kangyuzhe666/ZYNQ7010-7020_AD9363/images/a82.PNG

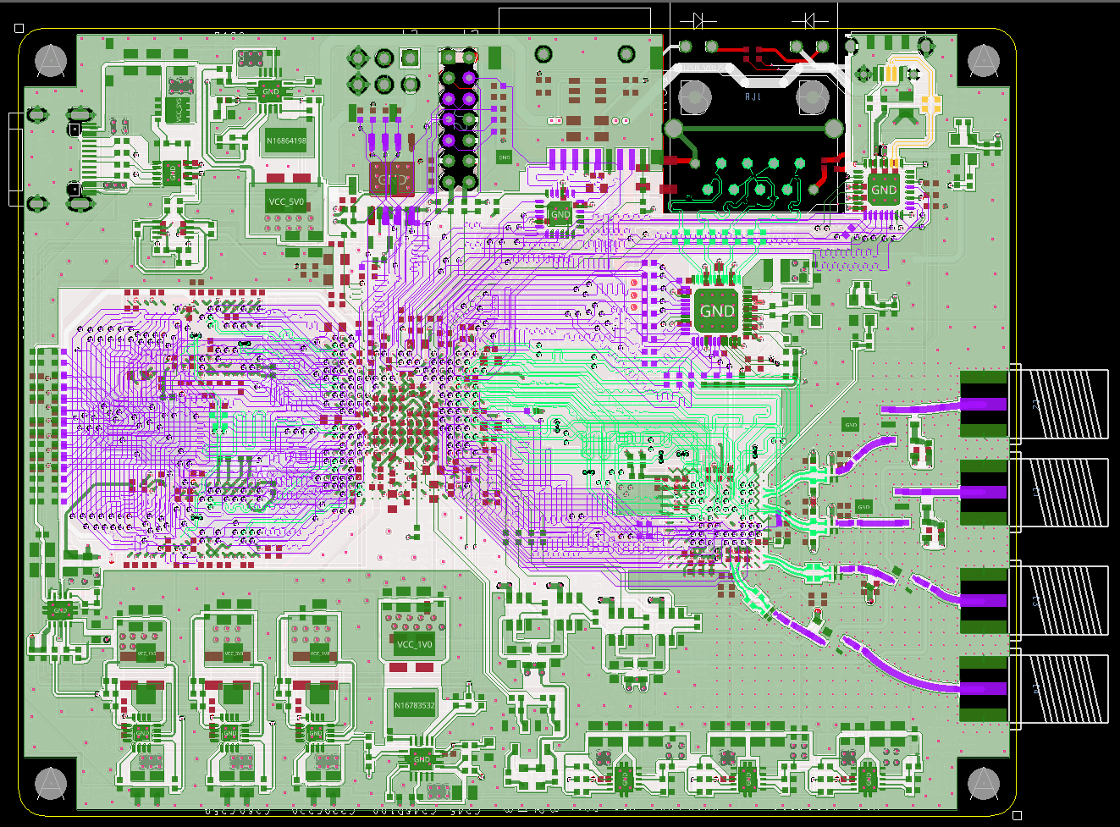
images/a82.PNG
