kangyuzhe666/ZYNQ7010-7020_AD9363/images/a83.PNG

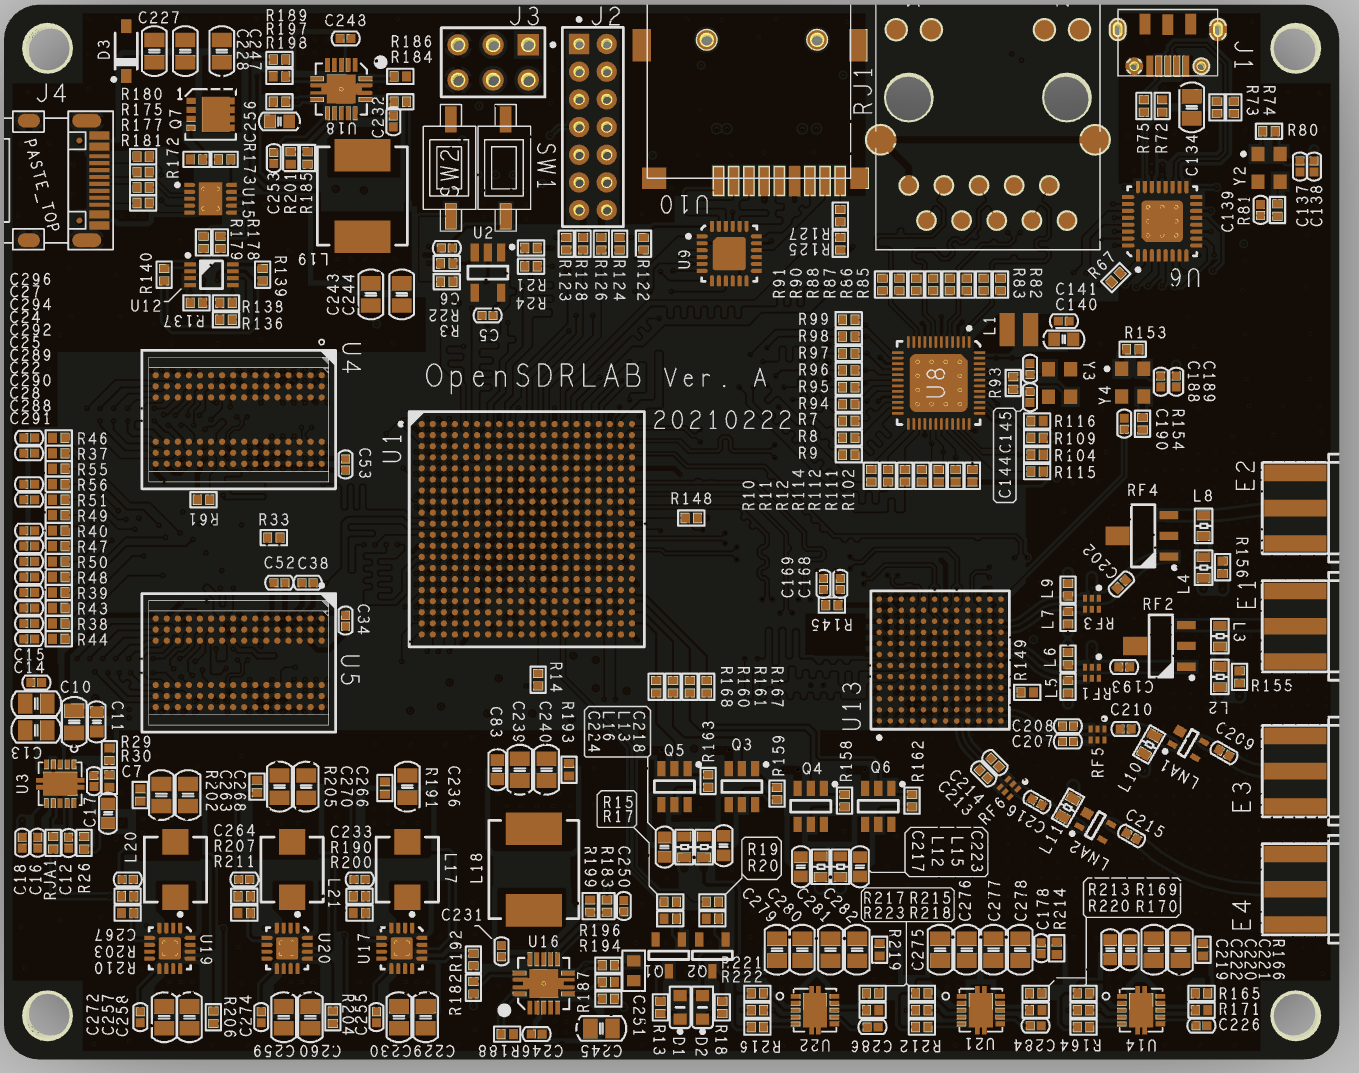
images/a83.PNG
