kangyuzhe666/ZYNQ7010-7020_AD9363/images/cpf.JPG

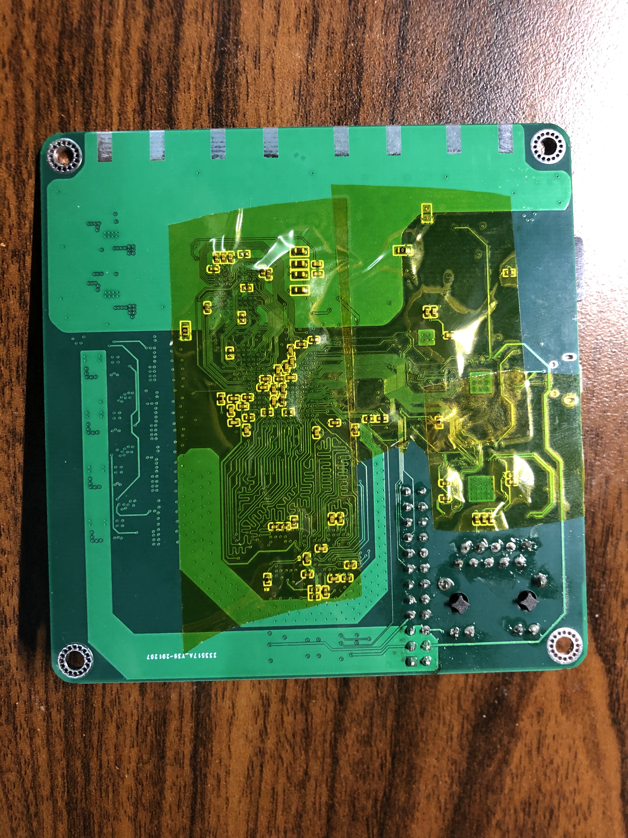
images/cpf.JPG
