kangyuzhe666/ZYNQ7010-7020_AD9363/images/cpz.JPG

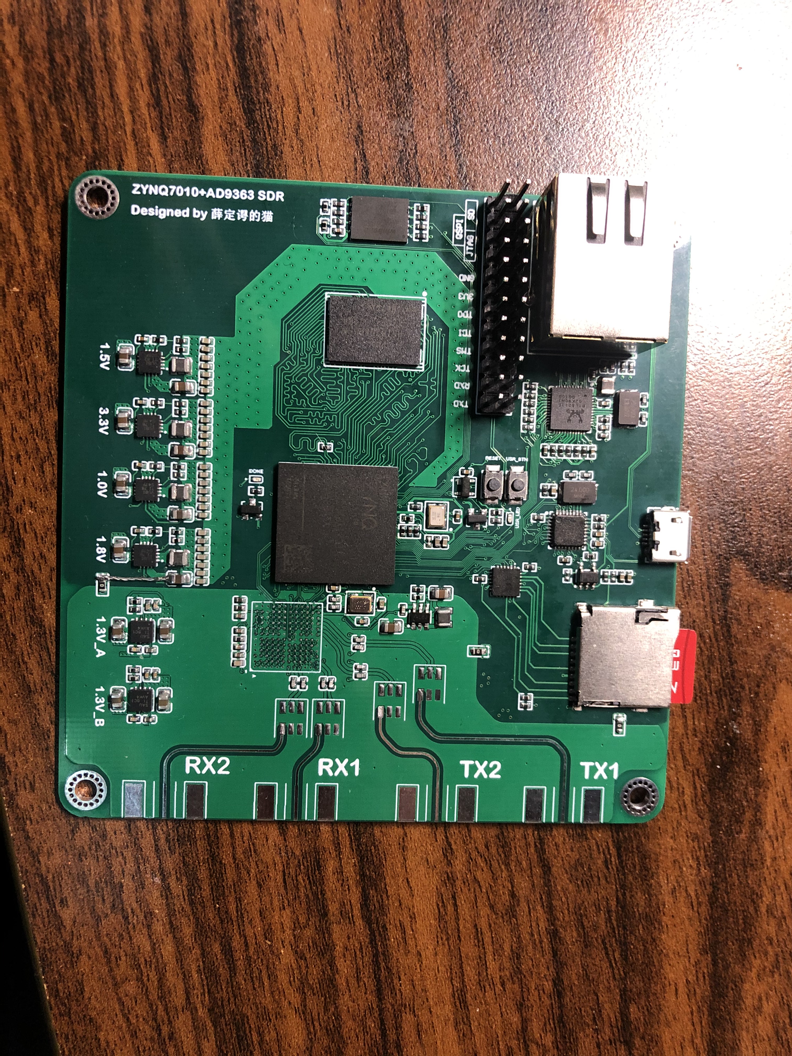
images/cpz.JPG
