kangyuzhe666/ZYNQ7010-7020_AD9363/images/IMG_2752.JPG

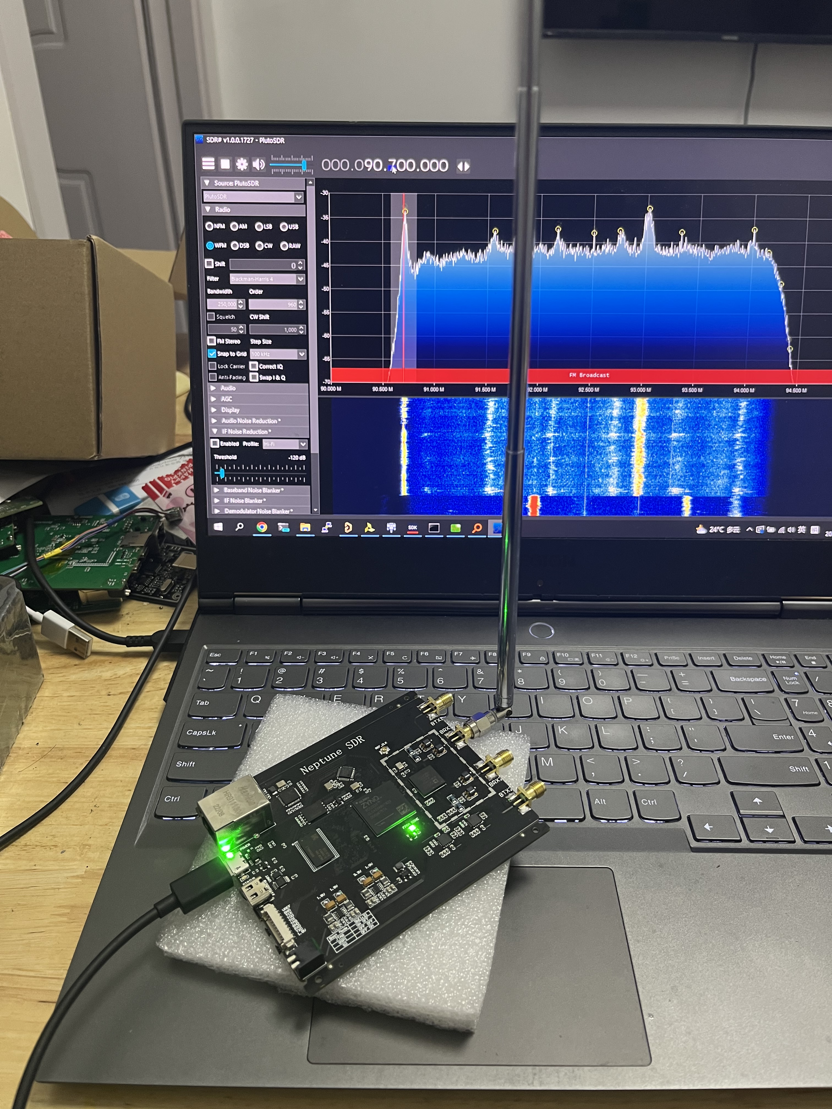
images/IMG_2752.JPG
