kangyuzhe666/ZYNQ7010-7020_AD9363/images/IMG_2765.JPG

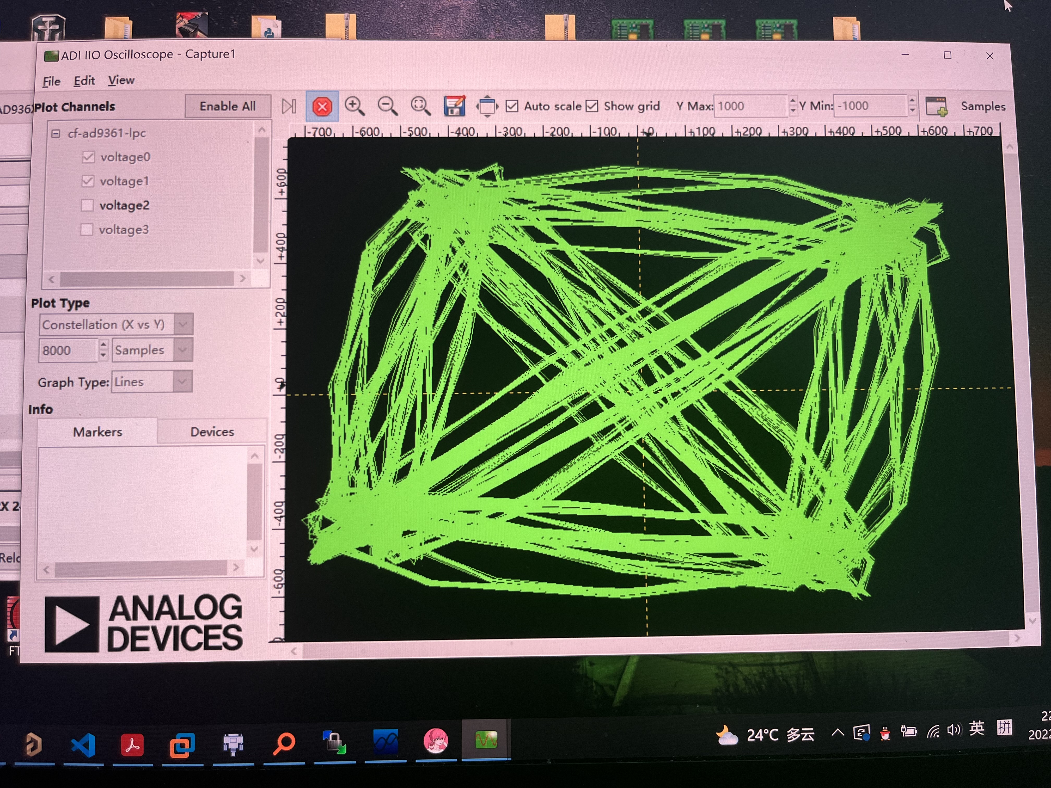
images/IMG_2765.JPG
