kangyuzhe666/ZYNQ7010-7020_AD9363/images/IMG_7890.PNG

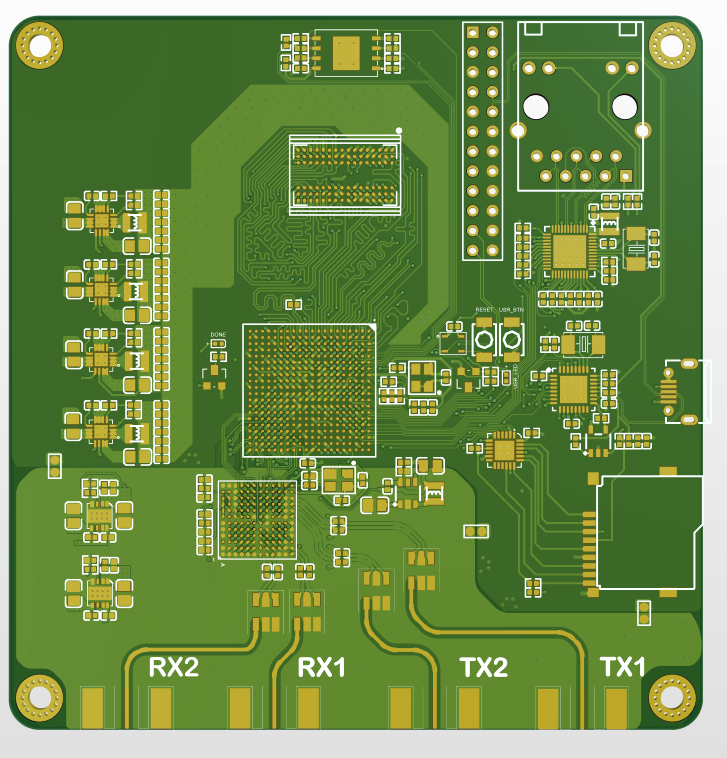
images/IMG_7890.PNG
