kangyuzhe666/ZYNQ7010-7020_AD9363/images/top.png

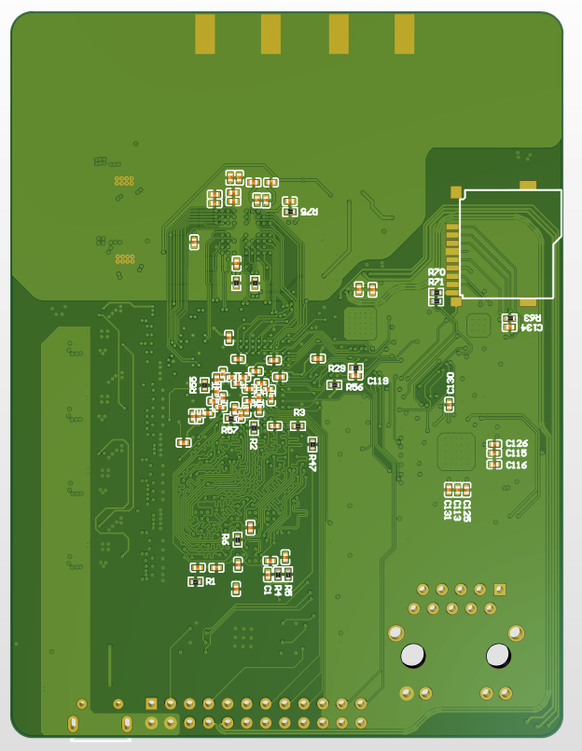
images/top.png
