kangyuzhe666/ZYNQ7010-7020_AD9363/firmware/source project/pluto-7010clg400-user-ip/pluto/pluto.runs/synth_1/.Xil/system_top_propImpl.xdc

set_property SRC_FILE_INFO {cfile:/home/kyz/hdl-2019_r1/projects/pluto/system_constr.xdc rfile:../../../system_constr.xdc id:1} [current_design]
set_property SRC_FILE_INFO {cfile:/home/kyz/hdl-2019_r1/projects/pluto/pluto.srcs/sources_1/bd/system/ip/system_axi_ad9361_dac_dma_0/system_axi_ad9361_dac_dma_0_constr.xdc rfile:../../../pluto.srcs/sources_1/bd/system/ip/system_axi_ad9361_dac_dma_0/system_axi_ad9361_dac_dma_0_constr.xdc id:2 order:LATE scoped_inst:i_system_wrapper/system_i/axi_ad9361_dac_dma/inst} [current_design]
set_property SRC_FILE_INFO {cfile:/home/kyz/hdl-2019_r1/projects/pluto/pluto.srcs/sources_1/bd/system/ip/system_axi_ad9361_adc_dma_0/system_axi_ad9361_adc_dma_0_constr.xdc rfile:../../../pluto.srcs/sources_1/bd/system/ip/system_axi_ad9361_adc_dma_0/system_axi_ad9361_adc_dma_0_constr.xdc id:3 order:LATE scoped_inst:i_system_wrapper/system_i/axi_ad9361_adc_dma/inst} [current_design]
set_property src_info {type:XDC file:1 line:4 export:INPUT save:INPUT read:READ} [current_design]
set_property  -dict {PACKAGE_PIN  U18  IOSTANDARD LVCMOS18 } [get_ports rx_clk_in]
set_property src_info {type:XDC file:1 line:5 export:INPUT save:INPUT read:READ} [current_design]
set_property  -dict {PACKAGE_PIN  U13  IOSTANDARD LVCMOS18 } [get_ports rx_frame_in]
set_property src_info {type:XDC file:1 line:6 export:INPUT save:INPUT read:READ} [current_design]
set_property  -dict {PACKAGE_PIN  P20  IOSTANDARD LVCMOS18 } [get_ports rx_data_in[0]]
set_property src_info {type:XDC file:1 line:7 export:INPUT save:INPUT read:READ} [current_design]
set_property  -dict {PACKAGE_PIN  N20  IOSTANDARD LVCMOS18 } [get_ports rx_data_in[1]]
set_property src_info {type:XDC file:1 line:8 export:INPUT save:INPUT read:READ} [current_design]
set_property  -dict {PACKAGE_PIN  W20  IOSTANDARD LVCMOS18 } [get_ports rx_data_in[2]]
set_property src_info {type:XDC file:1 line:9 export:INPUT save:INPUT read:READ} [current_design]
set_property  -dict {PACKAGE_PIN  V20  IOSTANDARD LVCMOS18 } [get_ports rx_data_in[3]]
set_property src_info {type:XDC file:1 line:10 export:INPUT save:INPUT read:READ} [current_design]
set_property  -dict {PACKAGE_PIN  U20  IOSTANDARD LVCMOS18 } [get_ports rx_data_in[4]]
set_property src_info {type:XDC file:1 line:11 export:INPUT save:INPUT read:READ} [current_design]
set_property  -dict {PACKAGE_PIN  T20  IOSTANDARD LVCMOS18 } [get_ports rx_data_in[5]]
set_property src_info {type:XDC file:1 line:12 export:INPUT save:INPUT read:READ} [current_design]
set_property  -dict {PACKAGE_PIN  R18  IOSTANDARD LVCMOS18 } [get_ports rx_data_in[6]]
set_property src_info {type:XDC file:1 line:13 export:INPUT save:INPUT read:READ} [current_design]
set_property  -dict {PACKAGE_PIN  T17  IOSTANDARD LVCMOS18 } [get_ports rx_data_in[7]]
set_property src_info {type:XDC file:1 line:14 export:INPUT save:INPUT read:READ} [current_design]
set_property  -dict {PACKAGE_PIN  P19  IOSTANDARD LVCMOS18 } [get_ports rx_data_in[8]]
set_property src_info {type:XDC file:1 line:15 export:INPUT save:INPUT read:READ} [current_design]
set_property  -dict {PACKAGE_PIN  N18  IOSTANDARD LVCMOS18 } [get_ports rx_data_in[9]]
set_property src_info {type:XDC file:1 line:16 export:INPUT save:INPUT read:READ} [current_design]
set_property  -dict {PACKAGE_PIN  R17  IOSTANDARD LVCMOS18 } [get_ports rx_data_in[10]]
set_property src_info {type:XDC file:1 line:17 export:INPUT save:INPUT read:READ} [current_design]
set_property  -dict {PACKAGE_PIN  R16  IOSTANDARD LVCMOS18 } [get_ports rx_data_in[11]]
set_property src_info {type:XDC file:1 line:19 export:INPUT save:INPUT read:READ} [current_design]
set_property  -dict {PACKAGE_PIN  T16  IOSTANDARD LVCMOS18} [get_ports tx_clk_out]
set_property src_info {type:XDC file:1 line:20 export:INPUT save:INPUT read:READ} [current_design]
set_property  -dict {PACKAGE_PIN  V16  IOSTANDARD LVCMOS18} [get_ports tx_frame_out]
set_property src_info {type:XDC file:1 line:21 export:INPUT save:INPUT read:READ} [current_design]
set_property  -dict {PACKAGE_PIN  W14  IOSTANDARD LVCMOS18} [get_ports tx_data_out[0]]
set_property src_info {type:XDC file:1 line:22 export:INPUT save:INPUT read:READ} [current_design]
set_property  -dict {PACKAGE_PIN  Y14  IOSTANDARD LVCMOS18} [get_ports tx_data_out[1]]
set_property src_info {type:XDC file:1 line:23 export:INPUT save:INPUT read:READ} [current_design]
set_property  -dict {PACKAGE_PIN  V12  IOSTANDARD LVCMOS18} [get_ports tx_data_out[2]]
set_property src_info {type:XDC file:1 line:24 export:INPUT save:INPUT read:READ} [current_design]
set_property  -dict {PACKAGE_PIN  W13  IOSTANDARD LVCMOS18} [get_ports tx_data_out[3]]
set_property src_info {type:XDC file:1 line:25 export:INPUT save:INPUT read:READ} [current_design]
set_property  -dict {PACKAGE_PIN  Y18  IOSTANDARD LVCMOS18} [get_ports tx_data_out[4]]
set_property src_info {type:XDC file:1 line:26 export:INPUT save:INPUT read:READ} [current_design]
set_property  -dict {PACKAGE_PIN  Y19  IOSTANDARD LVCMOS18} [get_ports tx_data_out[5]]
set_property src_info {type:XDC file:1 line:27 export:INPUT save:INPUT read:READ} [current_design]
set_property  -dict {PACKAGE_PIN  T12  IOSTANDARD LVCMOS18} [get_ports tx_data_out[6]]
set_property src_info {type:XDC file:1 line:28 export:INPUT save:INPUT read:READ} [current_design]
set_property  -dict {PACKAGE_PIN  U12  IOSTANDARD LVCMOS18} [get_ports tx_data_out[7]]
set_property src_info {type:XDC file:1 line:29 export:INPUT save:INPUT read:READ} [current_design]
set_property  -dict {PACKAGE_PIN  Y16  IOSTANDARD LVCMOS18} [get_ports tx_data_out[8]]
set_property src_info {type:XDC file:1 line:30 export:INPUT save:INPUT read:READ} [current_design]
set_property  -dict {PACKAGE_PIN  Y17  IOSTANDARD LVCMOS18} [get_ports tx_data_out[9]]
set_property src_info {type:XDC file:1 line:31 export:INPUT save:INPUT read:READ} [current_design]
set_property  -dict {PACKAGE_PIN  T11  IOSTANDARD LVCMOS18} [get_ports tx_data_out[10]]
set_property src_info {type:XDC file:1 line:32 export:INPUT save:INPUT read:READ} [current_design]
set_property  -dict {PACKAGE_PIN  T10  IOSTANDARD LVCMOS18} [get_ports tx_data_out[11]]
set_property src_info {type:XDC file:1 line:34 export:INPUT save:INPUT read:READ} [current_design]
set_property  -dict {PACKAGE_PIN  V17  IOSTANDARD LVCMOS18} [get_ports gpio_status[0]]
set_property src_info {type:XDC file:1 line:35 export:INPUT save:INPUT read:READ} [current_design]
set_property  -dict {PACKAGE_PIN  T14  IOSTANDARD LVCMOS18} [get_ports gpio_status[1]]
set_property src_info {type:XDC file:1 line:36 export:INPUT save:INPUT read:READ} [current_design]
set_property  -dict {PACKAGE_PIN  T15  IOSTANDARD LVCMOS18} [get_ports gpio_status[2]]
set_property src_info {type:XDC file:1 line:37 export:INPUT save:INPUT read:READ} [current_design]
set_property  -dict {PACKAGE_PIN  P14  IOSTANDARD LVCMOS18} [get_ports gpio_status[3]]
set_property src_info {type:XDC file:1 line:38 export:INPUT save:INPUT read:READ} [current_design]
set_property  -dict {PACKAGE_PIN  U14  IOSTANDARD LVCMOS18} [get_ports gpio_status[4]]
set_property src_info {type:XDC file:1 line:39 export:INPUT save:INPUT read:READ} [current_design]
set_property  -dict {PACKAGE_PIN  U15  IOSTANDARD LVCMOS18} [get_ports gpio_status[5]]
set_property src_info {type:XDC file:1 line:40 export:INPUT save:INPUT read:READ} [current_design]
set_property  -dict {PACKAGE_PIN  T19  IOSTANDARD LVCMOS18} [get_ports gpio_status[6]]
set_property src_info {type:XDC file:1 line:41 export:INPUT save:INPUT read:READ} [current_design]
set_property  -dict {PACKAGE_PIN  V18  IOSTANDARD LVCMOS18} [get_ports gpio_status[7]]
set_property src_info {type:XDC file:1 line:43 export:INPUT save:INPUT read:READ} [current_design]
set_property  -dict {PACKAGE_PIN  G20  IOSTANDARD LVCMOS18} [get_ports gpio_ctl[0]]
set_property src_info {type:XDC file:1 line:44 export:INPUT save:INPUT read:READ} [current_design]
set_property  -dict {PACKAGE_PIN  D20  IOSTANDARD LVCMOS18} [get_ports gpio_ctl[1]]
set_property src_info {type:XDC file:1 line:45 export:INPUT save:INPUT read:READ} [current_design]
set_property  -dict {PACKAGE_PIN  F20  IOSTANDARD LVCMOS18} [get_ports gpio_ctl[2]]
set_property src_info {type:XDC file:1 line:46 export:INPUT save:INPUT read:READ} [current_design]
set_property  -dict {PACKAGE_PIN  H20  IOSTANDARD LVCMOS18} [get_ports gpio_ctl[3]]
set_property src_info {type:XDC file:1 line:48 export:INPUT save:INPUT read:READ} [current_design]
set_property  -dict {PACKAGE_PIN  W19  IOSTANDARD LVCMOS18} [get_ports gpio_en_agc]
set_property src_info {type:XDC file:1 line:49 export:INPUT save:INPUT read:READ} [current_design]
set_property  -dict {PACKAGE_PIN  R19  IOSTANDARD LVCMOS18} [get_ports gpio_resetb]
set_property src_info {type:XDC file:1 line:51 export:INPUT save:INPUT read:READ} [current_design]
set_property  -dict {PACKAGE_PIN  V15  IOSTANDARD LVCMOS18} [get_ports enable]
set_property src_info {type:XDC file:1 line:52 export:INPUT save:INPUT read:READ} [current_design]
set_property  -dict {PACKAGE_PIN  R14  IOSTANDARD LVCMOS18} [get_ports txnrx]
set_property src_info {type:XDC file:1 line:54 export:INPUT save:INPUT read:READ} [current_design]
set_property  -dict {PACKAGE_PIN  J16  IOSTANDARD LVCMOS18 PULLTYPE PULLUP} [get_ports iic_scl]
set_property src_info {type:XDC file:1 line:55 export:INPUT save:INPUT read:READ} [current_design]
set_property  -dict {PACKAGE_PIN  K16  IOSTANDARD LVCMOS18 PULLTYPE PULLUP} [get_ports iic_sda]
set_property src_info {type:XDC file:1 line:57 export:INPUT save:INPUT read:READ} [current_design]
set_property  -dict {PACKAGE_PIN  N17  IOSTANDARD LVCMOS18  PULLTYPE PULLUP} [get_ports spi_csn]
set_property src_info {type:XDC file:1 line:58 export:INPUT save:INPUT read:READ} [current_design]
set_property  -dict {PACKAGE_PIN  P18  IOSTANDARD LVCMOS18} [get_ports spi_clk]
set_property src_info {type:XDC file:1 line:59 export:INPUT save:INPUT read:READ} [current_design]
set_property  -dict {PACKAGE_PIN  P15  IOSTANDARD LVCMOS18} [get_ports spi_mosi]
set_property src_info {type:XDC file:1 line:60 export:INPUT save:INPUT read:READ} [current_design]
set_property  -dict {PACKAGE_PIN  P16  IOSTANDARD LVCMOS18} [get_ports spi_miso]
set_property src_info {type:XDC file:1 line:62 export:INPUT save:INPUT read:READ} [current_design]
set_property  -dict {PACKAGE_PIN  L15  IOSTANDARD LVCMOS18} [get_ports gpio_bd]
set_property src_info {type:XDC file:1 line:63 export:INPUT save:INPUT read:READ} [current_design]
set_property  -dict {PACKAGE_PIN  W18  IOSTANDARD LVCMOS18} [get_ports clk_out]
set_property src_info {type:XDC file:1 line:74 export:INPUT save:INPUT read:READ} [current_design]
set_input_jitter clk_fpga_0 0.3
set_property src_info {type:XDC file:1 line:75 export:INPUT save:INPUT read:READ} [current_design]
set_input_jitter clk_fpga_1 0.15
current_instance i_system_wrapper/system_i/axi_ad9361_dac_dma/inst
set_property src_info {type:SCOPED_XDC file:2 line:10 export:INPUT save:INPUT read:READ} [current_design]
set_max_delay -quiet -datapath_only -from [get_clocks -of_objects [get_pins [list i_system_wrapper/system_i/axi_ad9361_dac_dma/inst/fifo_rd_clk i_system_wrapper/system_i/axi_ad9361_dac_dma/inst/m_axis_aclk i_system_wrapper/system_i/axi_ad9361_dac_dma/inst/m_dest_axi_aclk]]] -to [get_cells -hier *cdc_sync_stage1_reg* -filter {NAME =~ *i_sync_req_response_id* && IS_SEQUENTIAL}] [get_property -min PERIOD [get_clocks -of_objects [get_pins [list i_system_wrapper/system_i/axi_ad9361_dac_dma/inst/fifo_rd_clk i_system_wrapper/system_i/axi_ad9361_dac_dma/inst/m_axis_aclk i_system_wrapper/system_i/axi_ad9361_dac_dma/inst/m_dest_axi_aclk]]]]
set_property src_info {type:SCOPED_XDC file:2 line:26 export:INPUT save:INPUT read:READ} [current_design]
set_max_delay -quiet -datapath_only -from [get_clocks -of_objects [get_pins [list i_system_wrapper/system_i/axi_ad9361_dac_dma/inst/fifo_rd_clk i_system_wrapper/system_i/axi_ad9361_dac_dma/inst/m_axis_aclk i_system_wrapper/system_i/axi_ad9361_dac_dma/inst/m_dest_axi_aclk]]] -to [get_cells -quiet -hier *cdc_sync_stage1_reg* -filter {NAME =~ *i_dest_response_fifo/i_waddr_sync* && IS_SEQUENTIAL}] [get_property -min PERIOD [get_clocks -of_objects [get_pins [list i_system_wrapper/system_i/axi_ad9361_dac_dma/inst/fifo_rd_clk i_system_wrapper/system_i/axi_ad9361_dac_dma/inst/m_axis_aclk i_system_wrapper/system_i/axi_ad9361_dac_dma/inst/m_dest_axi_aclk]]]]
set_property src_info {type:SCOPED_XDC file:2 line:32 export:INPUT save:INPUT read:READ} [current_design]
set_max_delay -quiet -datapath_only -from [get_clocks -of_objects [get_pins i_system_wrapper/system_i/axi_ad9361_dac_dma/inst/s_axi_aclk]] -to [get_cells -quiet -hier *cdc_sync_stage1_reg* -filter {NAME =~ *i_dest_response_fifo/i_raddr_sync* && IS_SEQUENTIAL}] [get_property -min PERIOD [get_clocks -of_objects [get_pins i_system_wrapper/system_i/axi_ad9361_dac_dma/inst/s_axi_aclk]]]
set_property src_info {type:SCOPED_XDC file:2 line:37 export:INPUT save:INPUT read:READ} [current_design]
set_max_delay -quiet -datapath_only -from [get_cells -quiet -hier *cdc_sync_fifo_ram_reg* -filter {NAME =~ *i_dest_response_fifo* && IS_SEQUENTIAL}] -to [get_clocks -of_objects [get_pins i_system_wrapper/system_i/axi_ad9361_dac_dma/inst/s_axi_aclk]] [get_property -min PERIOD [get_clocks -of_objects [get_pins i_system_wrapper/system_i/axi_ad9361_dac_dma/inst/s_axi_aclk]]]
set_property src_info {type:SCOPED_XDC file:2 line:43 export:INPUT save:INPUT read:READ} [current_design]
set_max_delay -quiet -datapath_only -from [get_clocks -of_objects [get_pins [list i_system_wrapper/system_i/axi_ad9361_dac_dma/inst/fifo_wr_clk i_system_wrapper/system_i/axi_ad9361_dac_dma/inst/m_src_axi_aclk i_system_wrapper/system_i/axi_ad9361_dac_dma/inst/s_axis_aclk]]] -to [get_cells -quiet -hier *cdc_sync_stage1_reg* -filter {NAME =~ *i_sync_dest_request_id* && IS_SEQUENTIAL}] [get_property -min PERIOD [get_clocks -of_objects [get_pins [list i_system_wrapper/system_i/axi_ad9361_dac_dma/inst/fifo_wr_clk i_system_wrapper/system_i/axi_ad9361_dac_dma/inst/m_src_axi_aclk i_system_wrapper/system_i/axi_ad9361_dac_dma/inst/s_axis_aclk]]]]
set_property src_info {type:SCOPED_XDC file:2 line:49 export:INPUT save:INPUT read:READ} [current_design]
set_max_delay -quiet -datapath_only -from [get_clocks -of_objects [get_pins [list i_system_wrapper/system_i/axi_ad9361_dac_dma/inst/fifo_wr_clk i_system_wrapper/system_i/axi_ad9361_dac_dma/inst/m_src_axi_aclk i_system_wrapper/system_i/axi_ad9361_dac_dma/inst/s_axis_aclk]]] -to [get_cells -quiet -hier *cdc_sync_stage1_reg* -filter {NAME =~ *i_store_and_forward/i_dest_sync_id* && IS_SEQUENTIAL}] [get_property -min PERIOD [get_clocks -of_objects [get_pins [list i_system_wrapper/system_i/axi_ad9361_dac_dma/inst/fifo_wr_clk i_system_wrapper/system_i/axi_ad9361_dac_dma/inst/m_src_axi_aclk i_system_wrapper/system_i/axi_ad9361_dac_dma/inst/s_axis_aclk]]]]
set_property src_info {type:SCOPED_XDC file:2 line:55 export:INPUT save:INPUT read:READ} [current_design]
set_max_delay -quiet -datapath_only -from [get_clocks -of_objects [get_pins [list i_system_wrapper/system_i/axi_ad9361_dac_dma/inst/fifo_rd_clk i_system_wrapper/system_i/axi_ad9361_dac_dma/inst/m_axis_aclk i_system_wrapper/system_i/axi_ad9361_dac_dma/inst/m_dest_axi_aclk]]] -to [get_cells -quiet -hier *cdc_sync_stage1_reg* -filter {NAME =~ *i_store_and_forward/i_src_sync_id* && IS_SEQUENTIAL}] [get_property -min PERIOD [get_clocks -of_objects [get_pins [list i_system_wrapper/system_i/axi_ad9361_dac_dma/inst/fifo_rd_clk i_system_wrapper/system_i/axi_ad9361_dac_dma/inst/m_axis_aclk i_system_wrapper/system_i/axi_ad9361_dac_dma/inst/m_dest_axi_aclk]]]]
set_property src_info {type:SCOPED_XDC file:2 line:61 export:INPUT save:INPUT read:READ} [current_design]
set_max_delay -quiet -datapath_only -from [get_clocks -of_objects [get_pins [list i_system_wrapper/system_i/axi_ad9361_dac_dma/inst/fifo_wr_clk i_system_wrapper/system_i/axi_ad9361_dac_dma/inst/m_src_axi_aclk i_system_wrapper/system_i/axi_ad9361_dac_dma/inst/s_axis_aclk]]] -through [get_cells -quiet -hier -filter {IS_SEQUENTIAL && NAME =~ *i_store_and_forward/burst_len_mem_reg*}] -to [get_clocks -of_objects [get_pins [list i_system_wrapper/system_i/axi_ad9361_dac_dma/inst/fifo_rd_clk i_system_wrapper/system_i/axi_ad9361_dac_dma/inst/m_axis_aclk i_system_wrapper/system_i/axi_ad9361_dac_dma/inst/m_dest_axi_aclk]]] [get_property -min PERIOD [get_clocks -of_objects [get_pins [list i_system_wrapper/system_i/axi_ad9361_dac_dma/inst/fifo_rd_clk i_system_wrapper/system_i/axi_ad9361_dac_dma/inst/m_axis_aclk i_system_wrapper/system_i/axi_ad9361_dac_dma/inst/m_dest_axi_aclk]]]]
set_property src_info {type:SCOPED_XDC file:2 line:68 export:INPUT save:INPUT read:READ} [current_design]
set_max_delay -quiet -datapath_only -from [get_clocks -of_objects [get_pins [list i_system_wrapper/system_i/axi_ad9361_dac_dma/inst/fifo_wr_clk i_system_wrapper/system_i/axi_ad9361_dac_dma/inst/m_src_axi_aclk i_system_wrapper/system_i/axi_ad9361_dac_dma/inst/s_axis_aclk]]] -to [get_cells -quiet -hier *cdc_sync_stage1_reg* -filter {NAME =~ *i_dest_req_fifo/i_waddr_sync* && IS_SEQUENTIAL}] [get_property -min PERIOD [get_clocks -of_objects [get_pins [list i_system_wrapper/system_i/axi_ad9361_dac_dma/inst/fifo_wr_clk i_system_wrapper/system_i/axi_ad9361_dac_dma/inst/m_src_axi_aclk i_system_wrapper/system_i/axi_ad9361_dac_dma/inst/s_axis_aclk]]]]
set_property src_info {type:SCOPED_XDC file:2 line:74 export:INPUT save:INPUT read:READ} [current_design]
set_max_delay -quiet -datapath_only -from [get_clocks -of_objects [get_pins [list i_system_wrapper/system_i/axi_ad9361_dac_dma/inst/fifo_rd_clk i_system_wrapper/system_i/axi_ad9361_dac_dma/inst/m_axis_aclk i_system_wrapper/system_i/axi_ad9361_dac_dma/inst/m_dest_axi_aclk]]] -to [get_cells -quiet -hier *cdc_sync_stage1_reg* -filter {NAME =~ *i_dest_req_fifo/i_raddr_sync* && IS_SEQUENTIAL}] [get_property -min PERIOD [get_clocks -of_objects [get_pins [list i_system_wrapper/system_i/axi_ad9361_dac_dma/inst/fifo_rd_clk i_system_wrapper/system_i/axi_ad9361_dac_dma/inst/m_axis_aclk i_system_wrapper/system_i/axi_ad9361_dac_dma/inst/m_dest_axi_aclk]]]]
set_property src_info {type:SCOPED_XDC file:2 line:80 export:INPUT save:INPUT read:READ} [current_design]
set_max_delay -quiet -datapath_only -from [get_cells -quiet -hier *cdc_sync_fifo_ram_reg* -filter {NAME =~ *i_dest_req_fifo* && IS_SEQUENTIAL}] -to [get_clocks -of_objects [get_pins [list i_system_wrapper/system_i/axi_ad9361_dac_dma/inst/fifo_rd_clk i_system_wrapper/system_i/axi_ad9361_dac_dma/inst/m_axis_aclk i_system_wrapper/system_i/axi_ad9361_dac_dma/inst/m_dest_axi_aclk]]] [get_property -min PERIOD [get_clocks -of_objects [get_pins [list i_system_wrapper/system_i/axi_ad9361_dac_dma/inst/fifo_rd_clk i_system_wrapper/system_i/axi_ad9361_dac_dma/inst/m_axis_aclk i_system_wrapper/system_i/axi_ad9361_dac_dma/inst/m_dest_axi_aclk]]]]
set_property src_info {type:SCOPED_XDC file:2 line:86 export:INPUT save:INPUT read:READ} [current_design]
set_max_delay -quiet -datapath_only -from [get_clocks -of_objects [get_pins [list i_system_wrapper/system_i/axi_ad9361_dac_dma/inst/fifo_wr_clk i_system_wrapper/system_i/axi_ad9361_dac_dma/inst/m_src_axi_aclk i_system_wrapper/system_i/axi_ad9361_dac_dma/inst/s_axis_aclk]]] -to [get_cells -quiet -hier *cdc_sync_stage1_reg* -filter {NAME =~ *i_src_dest_bl_fifo/i_waddr_sync* && IS_SEQUENTIAL}] [get_property -min PERIOD [get_clocks -of_objects [get_pins [list i_system_wrapper/system_i/axi_ad9361_dac_dma/inst/fifo_wr_clk i_system_wrapper/system_i/axi_ad9361_dac_dma/inst/m_src_axi_aclk i_system_wrapper/system_i/axi_ad9361_dac_dma/inst/s_axis_aclk]]]]
set_property src_info {type:SCOPED_XDC file:2 line:92 export:INPUT save:INPUT read:READ} [current_design]
set_max_delay -quiet -datapath_only -from [get_clocks -of_objects [get_pins [list i_system_wrapper/system_i/axi_ad9361_dac_dma/inst/fifo_rd_clk i_system_wrapper/system_i/axi_ad9361_dac_dma/inst/m_axis_aclk i_system_wrapper/system_i/axi_ad9361_dac_dma/inst/m_dest_axi_aclk]]] -to [get_cells -quiet -hier *cdc_sync_stage1_reg* -filter {NAME =~ *i_src_dest_bl_fifo/i_raddr_sync* && IS_SEQUENTIAL}] [get_property -min PERIOD [get_clocks -of_objects [get_pins [list i_system_wrapper/system_i/axi_ad9361_dac_dma/inst/fifo_rd_clk i_system_wrapper/system_i/axi_ad9361_dac_dma/inst/m_axis_aclk i_system_wrapper/system_i/axi_ad9361_dac_dma/inst/m_dest_axi_aclk]]]]
set_property src_info {type:SCOPED_XDC file:2 line:98 export:INPUT save:INPUT read:READ} [current_design]
set_max_delay -quiet -datapath_only -from [get_cells -quiet -hier *cdc_sync_fifo_ram_reg* -filter {NAME =~ *i_src_dest_bl_fifo* && IS_SEQUENTIAL}] -to [get_clocks -of_objects [get_pins [list i_system_wrapper/system_i/axi_ad9361_dac_dma/inst/fifo_rd_clk i_system_wrapper/system_i/axi_ad9361_dac_dma/inst/m_axis_aclk i_system_wrapper/system_i/axi_ad9361_dac_dma/inst/m_dest_axi_aclk]]] [get_property -min PERIOD [get_clocks -of_objects [get_pins [list i_system_wrapper/system_i/axi_ad9361_dac_dma/inst/fifo_rd_clk i_system_wrapper/system_i/axi_ad9361_dac_dma/inst/m_axis_aclk i_system_wrapper/system_i/axi_ad9361_dac_dma/inst/m_dest_axi_aclk]]]]
set_property src_info {type:SCOPED_XDC file:2 line:104 export:INPUT save:INPUT read:READ} [current_design]
set_max_delay -quiet -datapath_only -from [get_clocks -of_objects [get_pins [list i_system_wrapper/system_i/axi_ad9361_dac_dma/inst/fifo_wr_clk i_system_wrapper/system_i/axi_ad9361_dac_dma/inst/m_src_axi_aclk i_system_wrapper/system_i/axi_ad9361_dac_dma/inst/s_axis_aclk]]] -through [get_cells -quiet -hier DP -filter {NAME =~ *i_request_arb/eot_mem_dest_reg*}] -to [get_clocks -of_objects [get_pins [list i_system_wrapper/system_i/axi_ad9361_dac_dma/inst/fifo_rd_clk i_system_wrapper/system_i/axi_ad9361_dac_dma/inst/m_axis_aclk i_system_wrapper/system_i/axi_ad9361_dac_dma/inst/m_dest_axi_aclk]]] [get_property -min PERIOD [get_clocks -of_objects [get_pins [list i_system_wrapper/system_i/axi_ad9361_dac_dma/inst/fifo_rd_clk i_system_wrapper/system_i/axi_ad9361_dac_dma/inst/m_axis_aclk i_system_wrapper/system_i/axi_ad9361_dac_dma/inst/m_dest_axi_aclk]]]]
current_instance
current_instance i_system_wrapper/system_i/axi_ad9361_adc_dma/inst
set_property src_info {type:SCOPED_XDC file:3 line:10 export:INPUT save:INPUT read:READ} [current_design]
set_max_delay -quiet -datapath_only -from [get_clocks -of_objects [get_pins i_system_wrapper/system_i/axi_ad9361_adc_dma/inst/s_axi_aclk]] -to [get_cells -quiet -hier *cdc_sync_stage1_reg* -filter {NAME =~ *i_sync_src_request_id* && IS_SEQUENTIAL}] [get_property -min PERIOD [get_clocks -of_objects [get_pins i_system_wrapper/system_i/axi_ad9361_adc_dma/inst/s_axi_aclk]]]
set_property src_info {type:SCOPED_XDC file:3 line:26 export:INPUT save:INPUT read:READ} [current_design]
set_max_delay -quiet -datapath_only -from [get_clocks -of_objects [get_pins i_system_wrapper/system_i/axi_ad9361_adc_dma/inst/s_axi_aclk]] -to [get_cells -quiet -hier *cdc_sync_stage1_reg* -filter {NAME =~ *i_src_req_fifo/i_waddr_sync* && IS_SEQUENTIAL}] [get_property -min PERIOD [get_clocks -of_objects [get_pins i_system_wrapper/system_i/axi_ad9361_adc_dma/inst/s_axi_aclk]]]
set_property src_info {type:SCOPED_XDC file:3 line:32 export:INPUT save:INPUT read:READ} [current_design]
set_max_delay -quiet -datapath_only -from [get_clocks -of_objects [get_pins [list i_system_wrapper/system_i/axi_ad9361_adc_dma/inst/fifo_wr_clk i_system_wrapper/system_i/axi_ad9361_adc_dma/inst/m_src_axi_aclk i_system_wrapper/system_i/axi_ad9361_adc_dma/inst/s_axis_aclk]]] -to [get_cells -quiet -hier *cdc_sync_stage1_reg* -filter {NAME =~ *i_src_req_fifo/i_raddr_sync* && IS_SEQUENTIAL}] [get_property -min PERIOD [get_clocks -of_objects [get_pins [list i_system_wrapper/system_i/axi_ad9361_adc_dma/inst/fifo_wr_clk i_system_wrapper/system_i/axi_ad9361_adc_dma/inst/m_src_axi_aclk i_system_wrapper/system_i/axi_ad9361_adc_dma/inst/s_axis_aclk]]]]
set_property src_info {type:SCOPED_XDC file:3 line:38 export:INPUT save:INPUT read:READ} [current_design]
set_max_delay -quiet -datapath_only -from [get_cells -quiet -hier *cdc_sync_fifo_ram_reg* -filter {NAME =~ *i_src_req_fifo* && IS_SEQUENTIAL}] -to [get_clocks -of_objects [get_pins [list i_system_wrapper/system_i/axi_ad9361_adc_dma/inst/fifo_wr_clk i_system_wrapper/system_i/axi_ad9361_adc_dma/inst/m_src_axi_aclk i_system_wrapper/system_i/axi_ad9361_adc_dma/inst/s_axis_aclk]]] [get_property -min PERIOD [get_clocks -of_objects [get_pins [list i_system_wrapper/system_i/axi_ad9361_adc_dma/inst/fifo_wr_clk i_system_wrapper/system_i/axi_ad9361_adc_dma/inst/m_src_axi_aclk i_system_wrapper/system_i/axi_ad9361_adc_dma/inst/s_axis_aclk]]]]
set_property src_info {type:SCOPED_XDC file:3 line:44 export:INPUT save:INPUT read:READ} [current_design]
set_max_delay -quiet -datapath_only -from [get_clocks -of_objects [get_pins i_system_wrapper/system_i/axi_ad9361_adc_dma/inst/s_axi_aclk]] -through [get_cells -quiet -hier DP -filter {NAME =~ *i_request_arb/eot_mem_src_reg*}] -to [get_clocks -of_objects [get_pins [list i_system_wrapper/system_i/axi_ad9361_adc_dma/inst/fifo_wr_clk i_system_wrapper/system_i/axi_ad9361_adc_dma/inst/m_src_axi_aclk i_system_wrapper/system_i/axi_ad9361_adc_dma/inst/s_axis_aclk]]] [get_property -min PERIOD [get_clocks -of_objects [get_pins [list i_system_wrapper/system_i/axi_ad9361_adc_dma/inst/fifo_wr_clk i_system_wrapper/system_i/axi_ad9361_adc_dma/inst/m_src_axi_aclk i_system_wrapper/system_i/axi_ad9361_adc_dma/inst/s_axis_aclk]]]]
set_property src_info {type:SCOPED_XDC file:3 line:51 export:INPUT save:INPUT read:READ} [current_design]
set_max_delay -quiet -datapath_only -from [get_clocks -of_objects [get_pins [list i_system_wrapper/system_i/axi_ad9361_adc_dma/inst/fifo_wr_clk i_system_wrapper/system_i/axi_ad9361_adc_dma/inst/m_src_axi_aclk i_system_wrapper/system_i/axi_ad9361_adc_dma/inst/s_axis_aclk]]] -to [get_cells -quiet -hier *cdc_sync_stage1_reg* -filter {NAME =~ *i_rewind_req_fifo/i_waddr_sync* && IS_SEQUENTIAL}] [get_property -min PERIOD [get_clocks -of_objects [get_pins [list i_system_wrapper/system_i/axi_ad9361_adc_dma/inst/fifo_wr_clk i_system_wrapper/system_i/axi_ad9361_adc_dma/inst/m_src_axi_aclk i_system_wrapper/system_i/axi_ad9361_adc_dma/inst/s_axis_aclk]]]]
set_property src_info {type:SCOPED_XDC file:3 line:57 export:INPUT save:INPUT read:READ} [current_design]
set_max_delay -quiet -datapath_only -from [get_clocks -of_objects [get_pins i_system_wrapper/system_i/axi_ad9361_adc_dma/inst/s_axi_aclk]] -to [get_cells -quiet -hier *cdc_sync_stage1_reg* -filter {NAME =~ *i_rewind_req_fifo/i_raddr_sync* && IS_SEQUENTIAL}] [get_property -min PERIOD [get_clocks -of_objects [get_pins i_system_wrapper/system_i/axi_ad9361_adc_dma/inst/s_axi_aclk]]]
set_property src_info {type:SCOPED_XDC file:3 line:63 export:INPUT save:INPUT read:READ} [current_design]
set_max_delay -quiet -datapath_only -from [get_cells -quiet -hier *cdc_sync_fifo_ram_reg* -filter {NAME =~ *i_rewind_req_fifo* && IS_SEQUENTIAL}] -to [get_clocks -of_objects [get_pins i_system_wrapper/system_i/axi_ad9361_adc_dma/inst/s_axi_aclk]] [get_property -min PERIOD [get_clocks -of_objects [get_pins i_system_wrapper/system_i/axi_ad9361_adc_dma/inst/s_axi_aclk]]]
set_property src_info {type:SCOPED_XDC file:3 line:79 export:INPUT save:INPUT read:READ} [current_design]
set_max_delay -quiet -datapath_only -from [get_clocks -of_objects [get_pins [list i_system_wrapper/system_i/axi_ad9361_adc_dma/inst/fifo_wr_clk i_system_wrapper/system_i/axi_ad9361_adc_dma/inst/m_src_axi_aclk i_system_wrapper/system_i/axi_ad9361_adc_dma/inst/s_axis_aclk]]] -to [get_cells -quiet -hier *cdc_sync_stage1_reg* -filter {NAME =~ *i_sync_dest_request_id* && IS_SEQUENTIAL}] [get_property -min PERIOD [get_clocks -of_objects [get_pins [list i_system_wrapper/system_i/axi_ad9361_adc_dma/inst/fifo_wr_clk i_system_wrapper/system_i/axi_ad9361_adc_dma/inst/m_src_axi_aclk i_system_wrapper/system_i/axi_ad9361_adc_dma/inst/s_axis_aclk]]]]
set_property src_info {type:SCOPED_XDC file:3 line:85 export:INPUT save:INPUT read:READ} [current_design]
set_max_delay -quiet -datapath_only -from [get_clocks -of_objects [get_pins [list i_system_wrapper/system_i/axi_ad9361_adc_dma/inst/fifo_wr_clk i_system_wrapper/system_i/axi_ad9361_adc_dma/inst/m_src_axi_aclk i_system_wrapper/system_i/axi_ad9361_adc_dma/inst/s_axis_aclk]]] -to [get_cells -quiet -hier *cdc_sync_stage1_reg* -filter {NAME =~ *i_store_and_forward/i_dest_sync_id* && IS_SEQUENTIAL}] [get_property -min PERIOD [get_clocks -of_objects [get_pins [list i_system_wrapper/system_i/axi_ad9361_adc_dma/inst/fifo_wr_clk i_system_wrapper/system_i/axi_ad9361_adc_dma/inst/m_src_axi_aclk i_system_wrapper/system_i/axi_ad9361_adc_dma/inst/s_axis_aclk]]]]
set_property src_info {type:SCOPED_XDC file:3 line:91 export:INPUT save:INPUT read:READ} [current_design]
set_max_delay -quiet -datapath_only -from [get_clocks -of_objects [get_pins [list i_system_wrapper/system_i/axi_ad9361_adc_dma/inst/fifo_rd_clk i_system_wrapper/system_i/axi_ad9361_adc_dma/inst/m_axis_aclk i_system_wrapper/system_i/axi_ad9361_adc_dma/inst/m_dest_axi_aclk]]] -to [get_cells -quiet -hier *cdc_sync_stage1_reg* -filter {NAME =~ *i_store_and_forward/i_src_sync_id* && IS_SEQUENTIAL}] [get_property -min PERIOD [get_clocks -of_objects [get_pins [list i_system_wrapper/system_i/axi_ad9361_adc_dma/inst/fifo_rd_clk i_system_wrapper/system_i/axi_ad9361_adc_dma/inst/m_axis_aclk i_system_wrapper/system_i/axi_ad9361_adc_dma/inst/m_dest_axi_aclk]]]]
set_property src_info {type:SCOPED_XDC file:3 line:97 export:INPUT save:INPUT read:READ} [current_design]
set_max_delay -quiet -datapath_only -from [get_clocks -of_objects [get_pins [list i_system_wrapper/system_i/axi_ad9361_adc_dma/inst/fifo_wr_clk i_system_wrapper/system_i/axi_ad9361_adc_dma/inst/m_src_axi_aclk i_system_wrapper/system_i/axi_ad9361_adc_dma/inst/s_axis_aclk]]] -through [get_cells -quiet -hier -filter {IS_SEQUENTIAL && NAME =~ *i_store_and_forward/burst_len_mem_reg*}] -to [get_clocks -of_objects [get_pins [list i_system_wrapper/system_i/axi_ad9361_adc_dma/inst/fifo_rd_clk i_system_wrapper/system_i/axi_ad9361_adc_dma/inst/m_axis_aclk i_system_wrapper/system_i/axi_ad9361_adc_dma/inst/m_dest_axi_aclk]]] [get_property -min PERIOD [get_clocks -of_objects [get_pins [list i_system_wrapper/system_i/axi_ad9361_adc_dma/inst/fifo_rd_clk i_system_wrapper/system_i/axi_ad9361_adc_dma/inst/m_axis_aclk i_system_wrapper/system_i/axi_ad9361_adc_dma/inst/m_dest_axi_aclk]]]]
set_property src_info {type:SCOPED_XDC file:3 line:104 export:INPUT save:INPUT read:READ} [current_design]
set_max_delay -quiet -datapath_only -from [get_clocks -of_objects [get_pins [list i_system_wrapper/system_i/axi_ad9361_adc_dma/inst/fifo_wr_clk i_system_wrapper/system_i/axi_ad9361_adc_dma/inst/m_src_axi_aclk i_system_wrapper/system_i/axi_ad9361_adc_dma/inst/s_axis_aclk]]] -to [get_cells -quiet -hier *cdc_sync_stage1_reg* -filter {NAME =~ *i_dest_req_fifo/i_waddr_sync* && IS_SEQUENTIAL}] [get_property -min PERIOD [get_clocks -of_objects [get_pins [list i_system_wrapper/system_i/axi_ad9361_adc_dma/inst/fifo_wr_clk i_system_wrapper/system_i/axi_ad9361_adc_dma/inst/m_src_axi_aclk i_system_wrapper/system_i/axi_ad9361_adc_dma/inst/s_axis_aclk]]]]
set_property src_info {type:SCOPED_XDC file:3 line:110 export:INPUT save:INPUT read:READ} [current_design]
set_max_delay -quiet -datapath_only -from [get_clocks -of_objects [get_pins [list i_system_wrapper/system_i/axi_ad9361_adc_dma/inst/fifo_rd_clk i_system_wrapper/system_i/axi_ad9361_adc_dma/inst/m_axis_aclk i_system_wrapper/system_i/axi_ad9361_adc_dma/inst/m_dest_axi_aclk]]] -to [get_cells -quiet -hier *cdc_sync_stage1_reg* -filter {NAME =~ *i_dest_req_fifo/i_raddr_sync* && IS_SEQUENTIAL}] [get_property -min PERIOD [get_clocks -of_objects [get_pins [list i_system_wrapper/system_i/axi_ad9361_adc_dma/inst/fifo_rd_clk i_system_wrapper/system_i/axi_ad9361_adc_dma/inst/m_axis_aclk i_system_wrapper/system_i/axi_ad9361_adc_dma/inst/m_dest_axi_aclk]]]]
set_property src_info {type:SCOPED_XDC file:3 line:116 export:INPUT save:INPUT read:READ} [current_design]
set_max_delay -quiet -datapath_only -from [get_cells -quiet -hier *cdc_sync_fifo_ram_reg* -filter {NAME =~ *i_dest_req_fifo* && IS_SEQUENTIAL}] -to [get_clocks -of_objects [get_pins [list i_system_wrapper/system_i/axi_ad9361_adc_dma/inst/fifo_rd_clk i_system_wrapper/system_i/axi_ad9361_adc_dma/inst/m_axis_aclk i_system_wrapper/system_i/axi_ad9361_adc_dma/inst/m_dest_axi_aclk]]] [get_property -min PERIOD [get_clocks -of_objects [get_pins [list i_system_wrapper/system_i/axi_ad9361_adc_dma/inst/fifo_rd_clk i_system_wrapper/system_i/axi_ad9361_adc_dma/inst/m_axis_aclk i_system_wrapper/system_i/axi_ad9361_adc_dma/inst/m_dest_axi_aclk]]]]
set_property src_info {type:SCOPED_XDC file:3 line:122 export:INPUT save:INPUT read:READ} [current_design]
set_max_delay -quiet -datapath_only -from [get_clocks -of_objects [get_pins [list i_system_wrapper/system_i/axi_ad9361_adc_dma/inst/fifo_wr_clk i_system_wrapper/system_i/axi_ad9361_adc_dma/inst/m_src_axi_aclk i_system_wrapper/system_i/axi_ad9361_adc_dma/inst/s_axis_aclk]]] -to [get_cells -quiet -hier *cdc_sync_stage1_reg* -filter {NAME =~ *i_src_dest_bl_fifo/i_waddr_sync* && IS_SEQUENTIAL}] [get_property -min PERIOD [get_clocks -of_objects [get_pins [list i_system_wrapper/system_i/axi_ad9361_adc_dma/inst/fifo_wr_clk i_system_wrapper/system_i/axi_ad9361_adc_dma/inst/m_src_axi_aclk i_system_wrapper/system_i/axi_ad9361_adc_dma/inst/s_axis_aclk]]]]
set_property src_info {type:SCOPED_XDC file:3 line:128 export:INPUT save:INPUT read:READ} [current_design]
set_max_delay -quiet -datapath_only -from [get_clocks -of_objects [get_pins [list i_system_wrapper/system_i/axi_ad9361_adc_dma/inst/fifo_rd_clk i_system_wrapper/system_i/axi_ad9361_adc_dma/inst/m_axis_aclk i_system_wrapper/system_i/axi_ad9361_adc_dma/inst/m_dest_axi_aclk]]] -to [get_cells -quiet -hier *cdc_sync_stage1_reg* -filter {NAME =~ *i_src_dest_bl_fifo/i_raddr_sync* && IS_SEQUENTIAL}] [get_property -min PERIOD [get_clocks -of_objects [get_pins [list i_system_wrapper/system_i/axi_ad9361_adc_dma/inst/fifo_rd_clk i_system_wrapper/system_i/axi_ad9361_adc_dma/inst/m_axis_aclk i_system_wrapper/system_i/axi_ad9361_adc_dma/inst/m_dest_axi_aclk]]]]
set_property src_info {type:SCOPED_XDC file:3 line:134 export:INPUT save:INPUT read:READ} [current_design]
set_max_delay -quiet -datapath_only -from [get_cells -quiet -hier *cdc_sync_fifo_ram_reg* -filter {NAME =~ *i_src_dest_bl_fifo* && IS_SEQUENTIAL}] -to [get_clocks -of_objects [get_pins [list i_system_wrapper/system_i/axi_ad9361_adc_dma/inst/fifo_rd_clk i_system_wrapper/system_i/axi_ad9361_adc_dma/inst/m_axis_aclk i_system_wrapper/system_i/axi_ad9361_adc_dma/inst/m_dest_axi_aclk]]] [get_property -min PERIOD [get_clocks -of_objects [get_pins [list i_system_wrapper/system_i/axi_ad9361_adc_dma/inst/fifo_rd_clk i_system_wrapper/system_i/axi_ad9361_adc_dma/inst/m_axis_aclk i_system_wrapper/system_i/axi_ad9361_adc_dma/inst/m_dest_axi_aclk]]]]
set_property src_info {type:SCOPED_XDC file:3 line:140 export:INPUT save:INPUT read:READ} [current_design]
set_max_delay -quiet -datapath_only -from [get_clocks -of_objects [get_pins [list i_system_wrapper/system_i/axi_ad9361_adc_dma/inst/fifo_wr_clk i_system_wrapper/system_i/axi_ad9361_adc_dma/inst/m_src_axi_aclk i_system_wrapper/system_i/axi_ad9361_adc_dma/inst/s_axis_aclk]]] -through [get_cells -quiet -hier DP -filter {NAME =~ *i_request_arb/eot_mem_dest_reg*}] -to [get_clocks -of_objects [get_pins [list i_system_wrapper/system_i/axi_ad9361_adc_dma/inst/fifo_rd_clk i_system_wrapper/system_i/axi_ad9361_adc_dma/inst/m_axis_aclk i_system_wrapper/system_i/axi_ad9361_adc_dma/inst/m_dest_axi_aclk]]] [get_property -min PERIOD [get_clocks -of_objects [get_pins [list i_system_wrapper/system_i/axi_ad9361_adc_dma/inst/fifo_rd_clk i_system_wrapper/system_i/axi_ad9361_adc_dma/inst/m_axis_aclk i_system_wrapper/system_i/axi_ad9361_adc_dma/inst/m_dest_axi_aclk]]]]
