kangyuzhe666/ZYNQ7010-7020_AD9363/firmware/source project/pluto-7010clg400-user-ip/pluto/pluto.srcs/sources_1/bd/system/ipshared/6c9d/hdl/axi_crossbar_v2_1_vl_rfs.v

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
// File name: addr_arbiter_sasd.v
//
// Description: 
//   Hybrid priority + round-robin arbiter.
//   Read & write requests combined (read preferred) at each slot
//   Muxes AR and AW channel payload inputs based on arbitration results.
//-----------------------------------------------------------------------------
//
// Structure:
//    addr_arbiter_sasd
//      mux_enc
//-----------------------------------------------------------------------------

`timescale 1ps/1ps
`default_nettype none

(* DowngradeIPIdentifiedWarnings="yes" *) 
module axi_crossbar_v2_1_19_addr_arbiter_sasd #
  (
   parameter         C_FAMILY                         = "none", 
   parameter integer C_NUM_S                = 1, 
   parameter integer C_NUM_S_LOG                = 1, 
   parameter integer C_AMESG_WIDTH                 = 1, 
   parameter         C_GRANT_ENC        = 0,
   parameter [C_NUM_S*32-1:0] C_ARB_PRIORITY             = {C_NUM_S{32'h00000000}}
                       // Arbitration priority among each SI slot. 
                       // Higher values indicate higher priority.
                       // Format: C_NUM_SLAVE_SLOTS{Bit32};
                       // Range: 'h0-'hF.
   )
  (
   // Global Signals
   input  wire                                      ACLK,
   input  wire                                      ARESET,
   // Slave Ports
   input  wire [C_NUM_S*C_AMESG_WIDTH-1:0]  S_AWMESG,
   input  wire [C_NUM_S*C_AMESG_WIDTH-1:0]  S_ARMESG,
   input  wire [C_NUM_S-1:0]                S_AWVALID,
   output wire [C_NUM_S-1:0]                S_AWREADY,
   input  wire [C_NUM_S-1:0]                S_ARVALID,
   output wire [C_NUM_S-1:0]                S_ARREADY,
   // Master Ports
   output wire [C_AMESG_WIDTH-1:0]          M_AMESG,
   output wire [C_NUM_S_LOG-1:0]            M_GRANT_ENC,
   output wire [C_NUM_S-1:0]                M_GRANT_HOT,
   output wire                              M_GRANT_RNW,
   output wire                              M_GRANT_ANY,
   output wire                              M_AWVALID,
   input  wire                              M_AWREADY,
   output wire                              M_ARVALID,
   input  wire                              M_ARREADY
   );
   
  // Generates a mask for all input slots that are priority based
  function [C_NUM_S-1:0] f_prio_mask
    (
      input integer null_arg
    );
    reg   [C_NUM_S-1:0]            mask;
    integer                        i;    
    begin
      mask = 0;    
      for (i=0; i < C_NUM_S; i=i+1) begin
        mask[i] = (C_ARB_PRIORITY[i*32+:32] != 0);
      end 
      f_prio_mask = mask;
    end   
  endfunction
  
  // Convert 16-bit one-hot to 4-bit binary
  function [3:0] f_hot2enc
    (
      input [15:0]  one_hot
    );
    begin
      f_hot2enc[0] = |(one_hot & 16'b1010101010101010);
      f_hot2enc[1] = |(one_hot & 16'b1100110011001100);
      f_hot2enc[2] = |(one_hot & 16'b1111000011110000);
      f_hot2enc[3] = |(one_hot & 16'b1111111100000000);
    end
  endfunction

  localparam [C_NUM_S-1:0] P_PRIO_MASK = f_prio_mask(0);

  reg                     m_valid_i = 1'b0;
  reg [C_NUM_S-1:0]       s_ready_i = 0;
  reg [C_NUM_S-1:0]       s_awvalid_reg = 0;
  reg [C_NUM_S-1:0]       s_arvalid_reg = 0;
  wire [15:0]             s_avalid;
  wire                    m_aready;
  wire [C_NUM_S-1:0]      rnw;
  reg                     grant_rnw;
  reg [C_NUM_S_LOG-1:0]   m_grant_enc_i;
  reg [C_NUM_S-1:0]       m_grant_hot_i; 
  reg [C_NUM_S-1:0]       last_rr_hot;
  reg                     any_grant;
  reg                     any_prio;
  reg [C_NUM_S-1:0]       which_prio_hot;
  reg [C_NUM_S_LOG-1:0]   which_prio_enc;          
  reg [4:0]               current_highest;
  reg [15:0]              next_prio_hot;
  reg [C_NUM_S_LOG-1:0]   next_prio_enc;    
  reg                     found_prio;
  wire [C_NUM_S-1:0]      valid_rr;
  reg [15:0]              next_rr_hot;
  reg [C_NUM_S_LOG-1:0]   next_rr_enc;    
  reg [C_NUM_S*C_NUM_S-1:0] carry_rr;
  reg [C_NUM_S*C_NUM_S-1:0] mask_rr;
  reg                     found_rr;
  wire [C_NUM_S-1:0]      next_hot;
  wire [C_NUM_S_LOG-1:0]  next_enc;    
  integer                 i;
  wire  [C_AMESG_WIDTH-1:0] amesg_mux;
  reg   [C_AMESG_WIDTH-1:0] m_amesg_i;
  wire [C_NUM_S*C_AMESG_WIDTH-1:0] s_amesg;
  genvar                  gen_si;

  always @(posedge ACLK) begin
    if (ARESET) begin
      s_awvalid_reg <= 0;
      s_arvalid_reg <= 0;
    end else if (|s_ready_i) begin
      s_awvalid_reg <= 0;
      s_arvalid_reg <= 0;
    end else begin
      s_arvalid_reg <= S_ARVALID & ~s_awvalid_reg;
      s_awvalid_reg <= S_AWVALID & ~s_arvalid_reg & (~S_ARVALID | s_awvalid_reg);
    end
  end
  
  assign s_avalid = S_AWVALID | S_ARVALID;
  assign M_AWVALID = m_valid_i & ~grant_rnw;
  assign M_ARVALID = m_valid_i & grant_rnw;
  assign S_AWREADY = s_ready_i & {C_NUM_S{~grant_rnw}};
  assign S_ARREADY = s_ready_i & {C_NUM_S{grant_rnw}};
  assign M_GRANT_ENC = C_GRANT_ENC ? m_grant_enc_i : 0;
  assign M_GRANT_HOT = m_grant_hot_i;
  assign M_GRANT_RNW = grant_rnw;
  assign rnw = S_ARVALID & ~s_awvalid_reg;
  assign M_AMESG = m_amesg_i;
  assign m_aready = grant_rnw ? M_ARREADY : M_AWREADY;
  
  generate
    for (gen_si=0; gen_si<C_NUM_S; gen_si=gen_si+1) begin : gen_mesg_mux
      assign s_amesg[C_AMESG_WIDTH*gen_si +: C_AMESG_WIDTH] = rnw[gen_si] ? S_ARMESG[C_AMESG_WIDTH*gen_si +: C_AMESG_WIDTH] : S_AWMESG[C_AMESG_WIDTH*gen_si +: C_AMESG_WIDTH];
    end  // gen_mesg_mux
         
    if (C_NUM_S>1) begin : gen_arbiter
    
      /////////////////////////////////////////////////////////////////////////////
      // Grant a new request when there is none still pending.
      // If no qualified requests found, de-assert M_VALID.
      /////////////////////////////////////////////////////////////////////////////
      
      assign M_GRANT_ANY = any_grant;
      assign next_hot = found_prio ? next_prio_hot : next_rr_hot;
      assign next_enc = found_prio ? next_prio_enc : next_rr_enc;
      
      always @(posedge ACLK) begin
        if (ARESET) begin
          m_valid_i <= 0;
          s_ready_i <= 0;
          m_grant_hot_i <= 0;
          m_grant_enc_i <= 0;
          any_grant <= 1'b0;
          last_rr_hot <= {1'b1, {C_NUM_S-1{1'b0}}};
          grant_rnw <= 1'b0;
        end else begin
          s_ready_i <= 0;
          if (m_valid_i) begin
            // Stall 1 cycle after each master-side completion.
            if (m_aready) begin  // Master-side completion
              m_valid_i <= 1'b0;
              m_grant_hot_i <= 0;
              any_grant <= 1'b0;
            end
          end else if (any_grant) begin
            m_valid_i <= 1'b1;
            s_ready_i <= m_grant_hot_i;  // Assert S_AW/READY for 1 cycle to complete SI address transfer
          end else begin
            if (found_prio | found_rr) begin
              m_grant_hot_i <= next_hot;
              m_grant_enc_i <= next_enc;
              any_grant <= 1'b1;
              grant_rnw <= |(rnw & next_hot);
              if (~found_prio) begin
                last_rr_hot <= next_rr_hot;
              end
            end
          end
        end
      end
    
      /////////////////////////////////////////////////////////////////////////////
      // Fixed Priority arbiter
      // Selects next request to grant from among inputs with PRIO > 0, if any.
      /////////////////////////////////////////////////////////////////////////////
      
      always @ * begin : ALG_PRIO
        integer ip;
        any_prio = 1'b0;
        which_prio_hot = 0;        
        which_prio_enc = 0;    
        current_highest = 0;    
        for (ip=0; ip < C_NUM_S; ip=ip+1) begin
          if (P_PRIO_MASK[ip] & ({1'b0, C_ARB_PRIORITY[ip*32+:4]} > current_highest)) begin
            if (s_avalid[ip]) begin
              current_highest[0+:4] = C_ARB_PRIORITY[ip*32+:4];
              any_prio = 1'b1;
              which_prio_hot = 1'b1 << ip;
              which_prio_enc = ip;
            end
          end   
        end
        found_prio = any_prio;
        next_prio_hot = which_prio_hot;
        next_prio_enc = which_prio_enc;
      end
     
      /////////////////////////////////////////////////////////////////////////////
      // Round-robin arbiter
      // Selects next request to grant from among inputs with PRIO = 0, if any.
      /////////////////////////////////////////////////////////////////////////////
      
      assign valid_rr = ~P_PRIO_MASK & s_avalid;
      
      always @ * begin : ALG_RR
        integer ir, jr, nr;
        next_rr_hot = 0;
        for (ir=0;ir<C_NUM_S;ir=ir+1) begin
          nr = (ir>0) ? (ir-1) : (C_NUM_S-1);
          carry_rr[ir*C_NUM_S] = last_rr_hot[nr];
          mask_rr[ir*C_NUM_S] = ~valid_rr[nr];
          for (jr=1;jr<C_NUM_S;jr=jr+1) begin
            nr = (ir-jr > 0) ? (ir-jr-1) : (C_NUM_S+ir-jr-1);
            carry_rr[ir*C_NUM_S+jr] = carry_rr[ir*C_NUM_S+jr-1] | (last_rr_hot[nr] & mask_rr[ir*C_NUM_S+jr-1]);
            if (jr < C_NUM_S-1) begin
              mask_rr[ir*C_NUM_S+jr] = mask_rr[ir*C_NUM_S+jr-1] & ~valid_rr[nr];
            end
          end   
          next_rr_hot[ir] = valid_rr[ir] & carry_rr[(ir+1)*C_NUM_S-1];
        end
        next_rr_enc = f_hot2enc(next_rr_hot);
        found_rr = |(next_rr_hot);
      end
  
      generic_baseblocks_v2_1_0_mux_enc # 
        (
         .C_FAMILY      ("rtl"),
         .C_RATIO       (C_NUM_S),
         .C_SEL_WIDTH   (C_NUM_S_LOG),
         .C_DATA_WIDTH  (C_AMESG_WIDTH)
        ) si_amesg_mux_inst 
        (
         .S   (next_enc),
         .A   (s_amesg),
         .O   (amesg_mux),
         .OE  (1'b1)
        ); 
        
      always @(posedge ACLK) begin
        if (ARESET) begin
          m_amesg_i <= 0;
        end else if (~any_grant) begin
          m_amesg_i <= amesg_mux;
        end
      end
    
    end else begin : gen_no_arbiter
      
      assign M_GRANT_ANY = m_grant_hot_i;

      always @ (posedge ACLK) begin
        if (ARESET) begin
          m_valid_i <= 1'b0;
          s_ready_i <= 1'b0;
          m_grant_enc_i <= 0;
          m_grant_hot_i <= 1'b0;
          grant_rnw <= 1'b0;
        end else begin
          s_ready_i <= 1'b0;
          if (m_valid_i) begin
            if (m_aready) begin
              m_valid_i <= 1'b0;
              m_grant_hot_i <= 1'b0;
            end
          end else if (m_grant_hot_i) begin
            m_valid_i <= 1'b1;
            s_ready_i[0] <= 1'b1;  // Assert S_AW/READY for 1 cycle to complete SI address transfer
          end else if (s_avalid[0]) begin
            m_grant_hot_i <= 1'b1;
            grant_rnw <= rnw[0];
          end
        end
      end
      
      always @ (posedge ACLK) begin
        if (ARESET) begin
          m_amesg_i <= 0;
        end else if (~m_grant_hot_i) begin
          m_amesg_i <= s_amesg;
        end
      end
    
    end  // gen_arbiter
  endgenerate
endmodule

`default_nettype wire


// -- (c) Copyright 2009 - 2011 Xilinx, Inc. All rights reserved.
// --
// -- This file contains confidential and proprietary information
// -- of Xilinx, Inc. and is protected under U.S. and 
// -- international copyright and other intellectual property
// -- laws.
// --
// -- DISCLAIMER
// -- This disclaimer is not a license and does not grant any
// -- rights to the materials distributed herewith. Except as
// -- otherwise provided in a valid license issued to you by
// -- Xilinx, and to the maximum extent permitted by applicable
// -- law: (1) THESE MATERIALS ARE MADE AVAILABLE "AS IS" AND
// -- WITH ALL FAULTS, AND XILINX HEREBY DISCLAIMS ALL WARRANTIES
// -- AND CONDITIONS, EXPRESS, IMPLIED, OR STATUTORY, INCLUDING
// -- BUT NOT LIMITED TO WARRANTIES OF MERCHANTABILITY, NON-
// -- INFRINGEMENT, OR FITNESS FOR ANY PARTICULAR PURPOSE; and
// -- (2) Xilinx shall not be liable (whether in contract or tort,
// -- including negligence, or under any other theory of
// -- liability) for any loss or damage of any kind or nature
// -- related to, arising under or in connection with these
// -- materials, including for any direct, or any indirect,
// -- special, incidental, or consequential loss or damage
// -- (including loss of data, profits, goodwill, or any type of
// -- loss or damage suffered as a result of any action brought
// -- by a third party) even if such damage or loss was
// -- reasonably foreseeable or Xilinx had been advised of the
// -- possibility of the same.
// --
// -- CRITICAL APPLICATIONS
// -- Xilinx products are not designed or intended to be fail-
// -- safe, or for use in any application requiring fail-safe
// -- performance, such as life-support or safety devices or
// -- systems, Class III medical devices, nuclear facilities,
// -- applications related to the deployment of airbags, or any
// -- other applications that could lead to death, personal
// -- injury, or severe property or environmental damage
// -- (individually and collectively, "Critical
// -- Applications"). Customer assumes the sole risk and
// -- liability of any use of Xilinx products in Critical
// -- Applications, subject only to applicable laws and
// -- regulations governing limitations on product liability.
// --
// -- THIS COPYRIGHT NOTICE AND DISCLAIMER MUST BE RETAINED AS
// -- PART OF THIS FILE AT ALL TIMES.
//-----------------------------------------------------------------------------
//
// File name: addr_arbiter.v
//
// Description: 
//   Instantiates generic priority encoder.
//   Each request is qualified if its target has not reached its issuing limit.
//   Muxes mesg and target inputs based on arbitration results.
//-----------------------------------------------------------------------------
//
// Structure:
//    addr_arbiter
//      mux_enc
//-----------------------------------------------------------------------------

`timescale 1ps/1ps
`default_nettype none

(* DowngradeIPIdentifiedWarnings="yes" *) 
module axi_crossbar_v2_1_19_addr_arbiter #
  (
   parameter         C_FAMILY                         = "none", 
   parameter integer C_NUM_S                = 1, 
   parameter integer C_NUM_S_LOG                = 1, 
   parameter integer C_NUM_M               = 1, 
   parameter integer C_MESG_WIDTH                 = 1, 
   parameter [C_NUM_S*32-1:0] C_ARB_PRIORITY             = {C_NUM_S{32'h00000000}}
                       // Arbitration priority among each SI slot. 
                       // Higher values indicate higher priority.
                       // Format: C_NUM_SLAVE_SLOTS{Bit32};
                       // Range: 'h0-'hF.
   )
  (
   // Global Signals
   input  wire                                      ACLK,
   input  wire                                      ARESET,
   // Slave Ports
   input  wire [C_NUM_S*C_MESG_WIDTH-1:0]  S_MESG,
   input  wire [C_NUM_S*C_NUM_M-1:0]                S_TARGET_HOT,
   input  wire [C_NUM_S-1:0]                S_VALID,
   input  wire [C_NUM_S-1:0]                S_VALID_QUAL,
   output wire [C_NUM_S-1:0]                S_READY,
   // Master Ports
   output wire [C_MESG_WIDTH-1:0]                    M_MESG,
   output wire [C_NUM_M-1:0]                           M_TARGET_HOT,
   output wire [C_NUM_S_LOG-1:0]                      M_GRANT_ENC,
   output wire                                        M_VALID,
   input  wire                                        M_READY,
   // Sideband input
   input  wire [C_NUM_M-1:0]                ISSUING_LIMIT
   );
   
  // Generates a mask for all input slots that are priority based
  function [C_NUM_S-1:0] f_prio_mask
    (
      input integer null_arg
    );
    reg   [C_NUM_S-1:0]            mask;
    integer                        i;    
    begin
      mask = 0;    
      for (i=0; i < C_NUM_S; i=i+1) begin
        mask[i] = (C_ARB_PRIORITY[i*32+:32] != 0);
      end 
      f_prio_mask = mask;
    end   
  endfunction
  
  // Convert 16-bit one-hot to 4-bit binary
  function [3:0] f_hot2enc
    (
      input [15:0]  one_hot
    );
    begin
      f_hot2enc[0] = |(one_hot & 16'b1010101010101010);
      f_hot2enc[1] = |(one_hot & 16'b1100110011001100);
      f_hot2enc[2] = |(one_hot & 16'b1111000011110000);
      f_hot2enc[3] = |(one_hot & 16'b1111111100000000);
    end
  endfunction

  localparam [C_NUM_S-1:0] P_PRIO_MASK = f_prio_mask(0);

  reg                     m_valid_i = 1'b0;
  reg [C_NUM_S-1:0]       s_ready_i = 0;
  reg [C_NUM_S-1:0]       qual_reg;
  reg [C_NUM_S-1:0]       grant_hot; 
  reg [C_NUM_S-1:0]       last_rr_hot;
  reg                     any_grant;
  reg                     any_prio;
  reg                     found_prio;
  reg [C_NUM_S-1:0]       which_prio_hot;
  reg [C_NUM_S-1:0]       next_prio_hot;
  reg [C_NUM_S_LOG-1:0]   which_prio_enc;          
  reg [C_NUM_S_LOG-1:0]   next_prio_enc;    
  reg [4:0]               current_highest;
  wire [C_NUM_S-1:0]      valid_rr;
  reg [15:0]              next_rr_hot;
  reg [C_NUM_S_LOG-1:0]   next_rr_enc;    
  reg [C_NUM_S*C_NUM_S-1:0] carry_rr;
  reg [C_NUM_S*C_NUM_S-1:0] mask_rr;
  reg                     found_rr;
  wire [C_NUM_S-1:0]      next_hot;
  wire [C_NUM_S_LOG-1:0]  next_enc;    
  reg                     prio_stall;
  integer                 i;
  wire [C_NUM_S-1:0]      valid_qual_i;
  reg  [C_NUM_S_LOG-1:0]  m_grant_enc_i;
  reg  [C_NUM_M-1:0]      m_target_hot_i;
  wire [C_NUM_M-1:0]      m_target_hot_mux;
  reg  [C_MESG_WIDTH-1:0] m_mesg_i;
  wire [C_MESG_WIDTH-1:0] m_mesg_mux;
  genvar                  gen_si;

  assign M_VALID = m_valid_i;
  assign S_READY = s_ready_i;
  assign M_GRANT_ENC = m_grant_enc_i;
  assign M_MESG = m_mesg_i;
  assign M_TARGET_HOT = m_target_hot_i;
  
  generate
    if (C_NUM_S>1) begin : gen_arbiter
      
      always @(posedge ACLK) begin
        if (ARESET) begin
          qual_reg <= 0;
        end else begin 
          qual_reg <= valid_qual_i | ~S_VALID; // Don't disqualify when bus not VALID (valid_qual_i would be garbage)
        end
      end
    
      for (gen_si=0; gen_si<C_NUM_S; gen_si=gen_si+1) begin : gen_req_qual
        assign valid_qual_i[gen_si] = S_VALID_QUAL[gen_si] & (|(S_TARGET_HOT[gen_si*C_NUM_M+:C_NUM_M] & ~ISSUING_LIMIT));
      end
    
      /////////////////////////////////////////////////////////////////////////////
      // Grant a new request when there is none still pending.
      // If no qualified requests found, de-assert M_VALID.
      /////////////////////////////////////////////////////////////////////////////
      
      assign next_hot = found_prio ? next_prio_hot : next_rr_hot;
      assign next_enc = found_prio ? next_prio_enc : next_rr_enc;
      
      always @(posedge ACLK) begin
        if (ARESET) begin
          m_valid_i <= 0;
          s_ready_i <= 0;
          grant_hot <= 0;
          any_grant <= 1'b0;
          m_grant_enc_i <= 0;
          last_rr_hot <= {1'b1, {C_NUM_S-1{1'b0}}};
          m_target_hot_i <= 0;
        end else begin
          s_ready_i <= 0;
          if (m_valid_i) begin
            // Stall 1 cycle after each master-side completion.
            if (M_READY) begin  // Master-side completion
              m_valid_i <= 1'b0;
              grant_hot <= 0;
              any_grant <= 1'b0;
            end
          end else if (any_grant) begin
            m_valid_i <= 1'b1;
            s_ready_i <= grant_hot;  // Assert S_AW/READY for 1 cycle to complete SI address transfer (regardless of M_AREADY)
          end else begin
            if ((found_prio | found_rr) & ~prio_stall) begin
              // Waste 1 cycle and re-arbitrate if target of highest prio hit issuing limit in previous cycle (valid_qual_i).
              if (|(next_hot & valid_qual_i)) begin  
                grant_hot <= next_hot;
                m_grant_enc_i <= next_enc;
                any_grant <= 1'b1;
                if (~found_prio) begin
                  last_rr_hot <= next_rr_hot;
                end
                m_target_hot_i <= m_target_hot_mux;
              end
            end
          end
        end
      end
    
      /////////////////////////////////////////////////////////////////////////////
      // Fixed Priority arbiter
      // Selects next request to grant from among inputs with PRIO > 0, if any.
      /////////////////////////////////////////////////////////////////////////////
          
      always @ * begin : ALG_PRIO
        integer ip;
        any_prio = 1'b0;
        prio_stall = 1'b0;
        which_prio_hot = 0;        
        which_prio_enc = 0;    
        current_highest = 0;    
        for (ip=0; ip < C_NUM_S; ip=ip+1) begin
          // Disqualify slot if target hit issuing limit (pass to lower prio slot).
          if (P_PRIO_MASK[ip] & S_VALID[ip] & qual_reg[ip]) begin
            if ({1'b0, C_ARB_PRIORITY[ip*32+:4]} > current_highest) begin
              current_highest[0+:4] = C_ARB_PRIORITY[ip*32+:4];
              // Stall 1 cycle when highest prio is recovering from SI-side handshake.
              // (Do not allow lower-prio slot to win arbitration.)
              if (s_ready_i[ip]) begin
                any_prio = 1'b0;
                prio_stall = 1'b1;
                which_prio_hot = 0;
                which_prio_enc = 0;
              end else begin
                any_prio = 1'b1;
                which_prio_hot = 1'b1 << ip;
                which_prio_enc = ip;
              end
            end
          end   
        end
        found_prio = any_prio;
        next_prio_hot = which_prio_hot;
        next_prio_enc = which_prio_enc;
      end
     
      /////////////////////////////////////////////////////////////////////////////
      // Round-robin arbiter
      // Selects next request to grant from among inputs with PRIO = 0, if any.
      /////////////////////////////////////////////////////////////////////////////
      
      // Disqualify slot if target hit issuing limit 2 or more cycles earlier (pass to next RR slot).
      // Disqualify for 1 cycle a slot that is recovering from SI-side handshake (s_ready_i),
      //   and allow arbitration to pass to any other RR requester.
      assign valid_rr = ~P_PRIO_MASK & S_VALID & ~s_ready_i & qual_reg;
      
      always @ * begin : ALG_RR
        integer ir, jr, nr;
        next_rr_hot = 0;
        for (ir=0;ir<C_NUM_S;ir=ir+1) begin
          nr = (ir>0) ? (ir-1) : (C_NUM_S-1);
          carry_rr[ir*C_NUM_S] = last_rr_hot[nr];
          mask_rr[ir*C_NUM_S] = ~valid_rr[nr];
          for (jr=1;jr<C_NUM_S;jr=jr+1) begin
            nr = (ir-jr > 0) ? (ir-jr-1) : (C_NUM_S+ir-jr-1);
            carry_rr[ir*C_NUM_S+jr] = carry_rr[ir*C_NUM_S+jr-1] | (last_rr_hot[nr] & mask_rr[ir*C_NUM_S+jr-1]);
            if (jr < C_NUM_S-1) begin
              mask_rr[ir*C_NUM_S+jr] = mask_rr[ir*C_NUM_S+jr-1] & ~valid_rr[nr];
            end
          end   
          next_rr_hot[ir] = valid_rr[ir] & carry_rr[(ir+1)*C_NUM_S-1];
        end
        next_rr_enc = f_hot2enc(next_rr_hot);
        found_rr = |(next_rr_hot);
      end
  
      generic_baseblocks_v2_1_0_mux_enc # 
        (
         .C_FAMILY      ("rtl"),
         .C_RATIO       (C_NUM_S),
         .C_SEL_WIDTH   (C_NUM_S_LOG),
         .C_DATA_WIDTH  (C_MESG_WIDTH)
        ) mux_mesg 
        (
         .S   (m_grant_enc_i),
         .A   (S_MESG),
         .O   (m_mesg_mux),
         .OE  (1'b1)
        ); 
        
      generic_baseblocks_v2_1_0_mux_enc # 
        (
         .C_FAMILY      ("rtl"),
         .C_RATIO       (C_NUM_S),
         .C_SEL_WIDTH   (C_NUM_S_LOG),
         .C_DATA_WIDTH  (C_NUM_M)
        ) si_amesg_mux_inst 
        (
         .S   (next_enc),
         .A   (S_TARGET_HOT),
         .O   (m_target_hot_mux),
         .OE  (1'b1)
        ); 
        
      always @(posedge ACLK) begin
        if (ARESET) begin
          m_mesg_i <= 0;
        end else if (~m_valid_i) begin
          m_mesg_i <= m_mesg_mux;
        end
      end
    
    end else begin : gen_no_arbiter
      
      assign valid_qual_i = S_VALID_QUAL & |(S_TARGET_HOT & ~ISSUING_LIMIT);
      
      always @ (posedge ACLK) begin
        if (ARESET) begin
          m_valid_i <= 1'b0;
          s_ready_i <= 1'b0;
          m_grant_enc_i <= 0;
        end else begin
          s_ready_i <= 1'b0;
          if (m_valid_i) begin
            if (M_READY) begin
              m_valid_i <= 1'b0;
            end
          end else if (S_VALID[0] & valid_qual_i[0] & ~s_ready_i) begin
            m_valid_i <= 1'b1;
            s_ready_i <= 1'b1;
            m_target_hot_i <= S_TARGET_HOT;
          end
        end
      end
      always @(posedge ACLK) begin
        if (ARESET) begin
          m_mesg_i <= 0;
        end else if (~m_valid_i) begin
          m_mesg_i <= S_MESG;
        end
      end
      
      
    end  // gen_arbiter
  endgenerate
endmodule

`default_nettype wire


// -- (c) Copyright 2010 - 2011 Xilinx, Inc. All rights reserved.
// --
// -- This file contains confidential and proprietary information
// -- of Xilinx, Inc. and is protected under U.S. and 
// -- international copyright and other intellectual property
// -- laws.
// --
// -- DISCLAIMER
// -- This disclaimer is not a license and does not grant any
// -- rights to the materials distributed herewith. Except as
// -- otherwise provided in a valid license issued to you by
// -- Xilinx, and to the maximum extent permitted by applicable
// -- law: (1) THESE MATERIALS ARE MADE AVAILABLE "AS IS" AND
// -- WITH ALL FAULTS, AND XILINX HEREBY DISCLAIMS ALL WARRANTIES
// -- AND CONDITIONS, EXPRESS, IMPLIED, OR STATUTORY, INCLUDING
// -- BUT NOT LIMITED TO WARRANTIES OF MERCHANTABILITY, NON-
// -- INFRINGEMENT, OR FITNESS FOR ANY PARTICULAR PURPOSE; and
// -- (2) Xilinx shall not be liable (whether in contract or tort,
// -- including negligence, or under any other theory of
// -- liability) for any loss or damage of any kind or nature
// -- related to, arising under or in connection with these
// -- materials, including for any direct, or any indirect,
// -- special, incidental, or consequential loss or damage
// -- (including loss of data, profits, goodwill, or any type of
// -- loss or damage suffered as a result of any action brought
// -- by a third party) even if such damage or loss was
// -- reasonably foreseeable or Xilinx had been advised of the
// -- possibility of the same.
// --
// -- CRITICAL APPLICATIONS
// -- Xilinx products are not designed or intended to be fail-
// -- safe, or for use in any application requiring fail-safe
// -- performance, such as life-support or safety devices or
// -- systems, Class III medical devices, nuclear facilities,
// -- applications related to the deployment of airbags, or any
// -- other applications that could lead to death, personal
// -- injury, or severe property or environmental damage
// -- (individually and collectively, "Critical
// -- Applications"). Customer assumes the sole risk and
// -- liability of any use of Xilinx products in Critical
// -- Applications, subject only to applicable laws and
// -- regulations governing limitations on product liability.
// --
// -- THIS COPYRIGHT NOTICE AND DISCLAIMER MUST BE RETAINED AS
// -- PART OF THIS FILE AT ALL TIMES.
//-----------------------------------------------------------------------------
//
// Description: Addr Decoder
// Each received address is compared to base and high address pairs for each 
//   of a set of decode targets. 
// The matching target's index (if any) is output combinatorially.
// If the decode is successful (matches any target), the MATCH output is asserted.
// For each target, a set of alternative address ranges may be specified.
// The base and high address pairs are formatted as a pair of 2-dimensional arrays,
//   alternative address ranges iterate within each target.
// The alternative range which matches the address is also output as REGION.
//
// Verilog-standard:  Verilog 2001
//--------------------------------------------------------------------------
//
// Structure:
//   addr_decoder
//      comparator_static
//
//--------------------------------------------------------------------------
`timescale 1ps/1ps

(* DowngradeIPIdentifiedWarnings="yes" *) 
module axi_crossbar_v2_1_19_addr_decoder #
  (
   parameter         C_FAMILY          = "none",
   parameter integer C_NUM_TARGETS     = 2,  // Number of decode targets = [1:16]
   parameter integer C_NUM_TARGETS_LOG = 1,  // Log2(C_NUM_TARGETS)
   parameter integer C_NUM_RANGES      = 1, // Number of alternative ranges that
                                             //    can match each target [1:16]
   parameter integer C_ADDR_WIDTH      = 32, // Width of decoder operand and of
                                             //   each base and high address [2:64]
   parameter integer C_TARGET_ENC      = 0,  // Enable encoded target output
   parameter integer C_TARGET_HOT      = 1,  // Enable 1-hot target output
   parameter integer C_REGION_ENC      = 0,   // Enable REGION output
   parameter [C_NUM_TARGETS*C_NUM_RANGES*64-1:0] C_BASE_ADDR = {C_NUM_TARGETS*C_NUM_RANGES*64{1'b1}}, 
   parameter [C_NUM_TARGETS*C_NUM_RANGES*64-1:0] C_HIGH_ADDR = {C_NUM_TARGETS*C_NUM_RANGES*64{1'b0}}, 
   parameter [C_NUM_TARGETS:0]    C_TARGET_QUAL                 = {C_NUM_TARGETS{1'b1}},
                       // Indicates whether each target has connectivity.
                       // Format: C_NUM_TARGETS{Bit1}.
   parameter integer   C_RESOLUTION                 = 0,
                       // Number of low-order ADDR bits that can be ignored when decoding.
   parameter integer   C_COMPARATOR_THRESHOLD       = 6
                       // Number of decoded ADDR bits above which will implement comparator_static.
   )
  (
   input  wire [C_ADDR_WIDTH-1:0]      ADDR,        // Decoder input operand
   output wire [C_NUM_TARGETS-1:0]     TARGET_HOT,  // Target matching address (1-hot)
   output wire [C_NUM_TARGETS_LOG-1:0] TARGET_ENC,  // Target matching address (encoded)
   output wire                         MATCH,       // Decode successful
   output wire [3:0]                   REGION      // Range within target matching address (encoded)
   );
  
  
  /////////////////////////////////////////////////////////////////////////////
  // Variables for generating parameter controlled instances.
  genvar target_cnt;
  genvar region_cnt;
  
  
  /////////////////////////////////////////////////////////////////////////////
  // Function to detect addrs is in the addressable range.
  // Only compare 4KB page address (ignore low-order 12 bits)
  function  decode_address;
    input [C_ADDR_WIDTH-1:0] base, high, addr;
    reg   [C_ADDR_WIDTH-C_RESOLUTION-1:0] mask;
    reg   [C_ADDR_WIDTH-C_RESOLUTION-1:0] addr_page;
    reg   [C_ADDR_WIDTH-C_RESOLUTION-1:0] base_page;
    reg   [C_ADDR_WIDTH-C_RESOLUTION-1:0] high_page;
  begin
    addr_page = addr[C_RESOLUTION+:C_ADDR_WIDTH-C_RESOLUTION];
    base_page = base[C_RESOLUTION+:C_ADDR_WIDTH-C_RESOLUTION];
    high_page = high[C_RESOLUTION+:C_ADDR_WIDTH-C_RESOLUTION];
    if (base[C_ADDR_WIDTH-1] & ~high[C_ADDR_WIDTH-1]) begin
      decode_address = 1'b0;
    end else begin
      mask  = base_page ^ high_page;
      if ( (base_page & ~mask) == (addr_page & ~mask) ) begin
        decode_address = 1'b1;
      end else begin
        decode_address = 1'b0;
      end
    end
  end
  endfunction
  
  // Generates a binary coded from onehotone encoded
  function [3:0] f_hot2enc
    (
      input [15:0]  one_hot
    );
    begin
      f_hot2enc[0] = |(one_hot & 16'b1010101010101010);
      f_hot2enc[1] = |(one_hot & 16'b1100110011001100);
      f_hot2enc[2] = |(one_hot & 16'b1111000011110000);
      f_hot2enc[3] = |(one_hot & 16'b1111111100000000);
    end
  endfunction

  /////////////////////////////////////////////////////////////////////////////
  // Internal signals
  wire [C_NUM_TARGETS-1:0]              TARGET_HOT_I;     // Target matching address (1-hot).
  wire [C_NUM_TARGETS*C_NUM_RANGES-1:0] ADDRESS_HIT;      // For address hit (1-hot).
  wire [C_NUM_TARGETS*C_NUM_RANGES-1:0] ADDRESS_HIT_REG;  // For address hit (1-hot).
  wire [C_NUM_RANGES-1:0]               REGION_HOT;       // Reginon matching address (1-hot).
  wire [3:0]                            TARGET_ENC_I;     // Internal version of encoded hit. 
  /////////////////////////////////////////////////////////////////////////////
  // Generate detection per region per target.
  generate
    for (target_cnt = 0; target_cnt < C_NUM_TARGETS; target_cnt = target_cnt + 1) begin : gen_target
      for (region_cnt = 0; region_cnt < C_NUM_RANGES; region_cnt = region_cnt + 1) begin : gen_region
        // Detect if this is an address hit (including used region decoding).
        if ((C_ADDR_WIDTH - C_RESOLUTION) > C_COMPARATOR_THRESHOLD) begin : gen_comparator_static
          if (C_TARGET_QUAL[target_cnt] &&
              ((C_BASE_ADDR[(target_cnt*C_NUM_RANGES+region_cnt)*64 +: C_ADDR_WIDTH] == 0) ||
               (C_HIGH_ADDR[(target_cnt*C_NUM_RANGES+region_cnt)*64 +: C_ADDR_WIDTH] != 0))) begin : gen_addr_range
            generic_baseblocks_v2_1_0_comparator_static #
            (
            .C_FAMILY("rtl"),
            .C_VALUE(C_BASE_ADDR[(target_cnt*C_NUM_RANGES+region_cnt)*64+C_RESOLUTION +: C_ADDR_WIDTH-C_RESOLUTION]),
            .C_DATA_WIDTH(C_ADDR_WIDTH-C_RESOLUTION)
            ) addr_decode_comparator
            (
            .CIN(1'b1),
            .A(ADDR[C_RESOLUTION +: C_ADDR_WIDTH-C_RESOLUTION] &
              ~(C_BASE_ADDR[(target_cnt*C_NUM_RANGES+region_cnt)*64+C_RESOLUTION +: C_ADDR_WIDTH-C_RESOLUTION] ^
                C_HIGH_ADDR[(target_cnt*C_NUM_RANGES+region_cnt)*64+C_RESOLUTION +: C_ADDR_WIDTH-C_RESOLUTION])),
            .COUT(ADDRESS_HIT[target_cnt*C_NUM_RANGES + region_cnt])
            );
          end else begin : gen_null_range
            assign ADDRESS_HIT[target_cnt*C_NUM_RANGES + region_cnt] = 1'b0;
          end
        end else begin : gen_no_comparator_static
          assign ADDRESS_HIT[target_cnt*C_NUM_RANGES + region_cnt] = C_TARGET_QUAL[target_cnt] ? 
                                    decode_address(
                                      C_BASE_ADDR[(target_cnt*C_NUM_RANGES+region_cnt)*64 +: C_ADDR_WIDTH],
                                      C_HIGH_ADDR[(target_cnt*C_NUM_RANGES+region_cnt)*64 +: C_ADDR_WIDTH],
                                      ADDR)
                                    : 1'b0;
        end  // gen_comparator_static
        assign ADDRESS_HIT_REG[region_cnt*C_NUM_TARGETS+target_cnt] = ADDRESS_HIT[target_cnt*C_NUM_RANGES + region_cnt];
      end  // gen_region
      
      // All regions are non-overlapping
      // => Or all the region detections for this target to determine if it is a hit.
      assign TARGET_HOT_I[target_cnt]  = | ADDRESS_HIT[target_cnt*C_NUM_RANGES +: C_NUM_RANGES];
    end  // gen_target
    
    for (region_cnt = 0; region_cnt < C_NUM_RANGES; region_cnt = region_cnt + 1) begin : gen_region_or
      assign REGION_HOT[region_cnt] = | ADDRESS_HIT_REG[region_cnt*C_NUM_TARGETS +: C_NUM_TARGETS];
    end  // gen_region_or
  endgenerate
  
  
  /////////////////////////////////////////////////////////////////////////////
  // All regions are non-overlapping
  // => Or all the target hit detections if it is a match.
  assign MATCH = | TARGET_HOT_I;
  
  
  /////////////////////////////////////////////////////////////////////////////
  // Assign conditional onehot target output signal.
  generate
    if (C_TARGET_HOT == 1) begin : USE_TARGET_ONEHOT
      assign TARGET_HOT = MATCH ? TARGET_HOT_I : 1;
    end else begin : NO_TARGET_ONEHOT
      assign TARGET_HOT = {C_NUM_TARGETS{1'b0}};
    end
  endgenerate
  
  
  /////////////////////////////////////////////////////////////////////////////
  // Assign conditional encoded target output signal.
  generate
    if (C_TARGET_ENC == 1) begin : USE_TARGET_ENCODED
      assign TARGET_ENC_I = f_hot2enc(TARGET_HOT_I);
      assign TARGET_ENC   = TARGET_ENC_I[C_NUM_TARGETS_LOG-1:0];
    end else begin : NO_TARGET_ENCODED
      assign TARGET_ENC = {C_NUM_TARGETS_LOG{1'b0}};
    end
  endgenerate
  
  
  /////////////////////////////////////////////////////////////////////////////
  // Assign conditional encoded region output signal.
  generate
    if (C_TARGET_ENC == 1) begin : USE_REGION_ENCODED
      assign REGION = f_hot2enc(REGION_HOT);
    end else begin : NO_REGION_ENCODED
      assign REGION = 4'b0;
    end
  endgenerate
  
  
endmodule


// -- (c) Copyright 2010 - 2011 Xilinx, Inc. All rights reserved.
// --
// -- This file contains confidential and proprietary information
// -- of Xilinx, Inc. and is protected under U.S. and 
// -- international copyright and other intellectual property
// -- laws.
// --
// -- DISCLAIMER
// -- This disclaimer is not a license and does not grant any
// -- rights to the materials distributed herewith. Except as
// -- otherwise provided in a valid license issued to you by
// -- Xilinx, and to the maximum extent permitted by applicable
// -- law: (1) THESE MATERIALS ARE MADE AVAILABLE "AS IS" AND
// -- WITH ALL FAULTS, AND XILINX HEREBY DISCLAIMS ALL WARRANTIES
// -- AND CONDITIONS, EXPRESS, IMPLIED, OR STATUTORY, INCLUDING
// -- BUT NOT LIMITED TO WARRANTIES OF MERCHANTABILITY, NON-
// -- INFRINGEMENT, OR FITNESS FOR ANY PARTICULAR PURPOSE; and
// -- (2) Xilinx shall not be liable (whether in contract or tort,
// -- including negligence, or under any other theory of
// -- liability) for any loss or damage of any kind or nature
// -- related to, arising under or in connection with these
// -- materials, including for any direct, or any indirect,
// -- special, incidental, or consequential loss or damage
// -- (including loss of data, profits, goodwill, or any type of
// -- loss or damage suffered as a result of any action brought
// -- by a third party) even if such damage or loss was
// -- reasonably foreseeable or Xilinx had been advised of the
// -- possibility of the same.
// --
// -- CRITICAL APPLICATIONS
// -- Xilinx products are not designed or intended to be fail-
// -- safe, or for use in any application requiring fail-safe
// -- performance, such as life-support or safety devices or
// -- systems, Class III medical devices, nuclear facilities,
// -- applications related to the deployment of airbags, or any
// -- other applications that could lead to death, personal
// -- injury, or severe property or environmental damage
// -- (individually and collectively, "Critical
// -- Applications"). Customer assumes the sole risk and
// -- liability of any use of Xilinx products in Critical
// -- Applications, subject only to applicable laws and
// -- regulations governing limitations on product liability.
// --
// -- THIS COPYRIGHT NOTICE AND DISCLAIMER MUST BE RETAINED AS
// -- PART OF THIS FILE AT ALL TIMES.
//-----------------------------------------------------------------------------
//
// Round-Robin Arbiter for R and B channel responses
// Verilog-standard:  Verilog 2001
//--------------------------------------------------------------------------
//
// Structure:
//    arbiter_resp
//--------------------------------------------------------------------------
`timescale 1ps/1ps

(* DowngradeIPIdentifiedWarnings="yes" *) 
module axi_crossbar_v2_1_19_arbiter_resp #
  (
   parameter         C_FAMILY       = "none",
   parameter integer C_NUM_S        = 4,      // Number of requesting Slave ports = [2:16]
   parameter integer C_NUM_S_LOG    = 2,      // Log2(C_NUM_S)
   parameter integer C_GRANT_ENC    = 0,      // Enable encoded grant output
   parameter integer C_GRANT_HOT    = 1       // Enable 1-hot grant output
   )
  (
   // Global Inputs
   input  wire                     ACLK,
   input  wire                     ARESET,
   // Slave  Ports
   input  wire [C_NUM_S-1:0]       S_VALID,      // Request from each slave
   output wire [C_NUM_S-1:0]       S_READY,      // Grant response to each slave
   // Master Ports
   output wire [C_NUM_S_LOG-1:0]   M_GRANT_ENC,  // Granted slave index (encoded)
   output wire [C_NUM_S-1:0]       M_GRANT_HOT,  // Granted slave index (1-hot)
   output wire                     M_VALID,      // Grant event
   input  wire                     M_READY
   );

  // Generates a binary coded from onehotone encoded
  function [4:0] f_hot2enc
    (
      input [16:0]  one_hot
    );
    begin
      f_hot2enc[0] = |(one_hot & 17'b01010101010101010);
      f_hot2enc[1] = |(one_hot & 17'b01100110011001100);
      f_hot2enc[2] = |(one_hot & 17'b01111000011110000);
      f_hot2enc[3] = |(one_hot & 17'b01111111100000000);
      f_hot2enc[4] = |(one_hot & 17'b10000000000000000);
    end
  endfunction

  (* use_clock_enable = "yes" *)
  reg [C_NUM_S-1:0]      chosen = 0;
  
  wire [C_NUM_S-1:0]     grant_hot; 
  wire                   master_selected; 
  wire                   active_master;
  wire                   need_arbitration;
  wire                   m_valid_i;
  wire [C_NUM_S-1:0]     s_ready_i;
  wire                   access_done;
  reg [C_NUM_S-1:0]      last_rr_hot;
  wire [C_NUM_S-1:0]     valid_rr;
  reg [C_NUM_S-1:0]      next_rr_hot;
  reg [C_NUM_S*C_NUM_S-1:0] carry_rr;
  reg [C_NUM_S*C_NUM_S-1:0] mask_rr;
  integer                 i;
  integer                 j;
  integer                 n;
  
  /////////////////////////////////////////////////////////////////////////////
  //   
  // Implementation of the arbiter outputs independant of arbitration
  //
  /////////////////////////////////////////////////////////////////////////////
  
  // Mask the current requests with the chosen master
  assign grant_hot        = chosen & S_VALID;

  // See if we have a selected master
  assign master_selected  = |grant_hot[0+:C_NUM_S];

  // See if we have current requests
  assign active_master    = |S_VALID;

  // Access is completed
  assign access_done = m_valid_i & M_READY;
  
  // Need to handle if we drive S_ready combinatorial and without an IDLE state

  // Drive S_READY on the master who has been chosen when we get a M_READY
  assign s_ready_i = {C_NUM_S{M_READY}} & grant_hot[0+:C_NUM_S];

  // Drive M_VALID if we have a selected master
  assign m_valid_i = master_selected;
                
  // If we have request and not a selected master, we need to arbitrate a new chosen 
  assign need_arbitration = (active_master & ~master_selected) | access_done;

  // need internal signals of the output signals
  assign M_VALID = m_valid_i;
  assign S_READY = s_ready_i;

  /////////////////////////////////////////////////////////////////////////////
  // Assign conditional onehot target output signal.
  assign M_GRANT_HOT = (C_GRANT_HOT == 1) ? grant_hot[0+:C_NUM_S] : {C_NUM_S{1'b0}};
  /////////////////////////////////////////////////////////////////////////////
  // Assign conditional encoded target output signal.
  assign M_GRANT_ENC = (C_GRANT_ENC == 1) ? f_hot2enc(grant_hot) : {C_NUM_S_LOG{1'b0}};
  
  /////////////////////////////////////////////////////////////////////////////
  // Select a new chosen when we need to arbitrate
  // If we don't have a new chosen, keep the old one since it's a good chance
  // that it will do another request
  always @(posedge ACLK)
    begin
      if (ARESET) begin
        chosen <= {C_NUM_S{1'b0}};
        last_rr_hot <= {1'b1, {C_NUM_S-1{1'b0}}};
      end else if (need_arbitration) begin
        chosen <= next_rr_hot;   
        if (|next_rr_hot) last_rr_hot <= next_rr_hot;
      end
    end

  assign valid_rr =  S_VALID;

  /////////////////////////////////////////////////////////////////////////////
  // Round-robin arbiter
  // Selects next request to grant from among inputs with PRIO = 0, if any.
  /////////////////////////////////////////////////////////////////////////////
  
  always @ * begin
    next_rr_hot = 0;
    for (i=0;i<C_NUM_S;i=i+1) begin
      n = (i>0) ? (i-1) : (C_NUM_S-1);
      carry_rr[i*C_NUM_S] = last_rr_hot[n];
      mask_rr[i*C_NUM_S] = ~valid_rr[n];
      for (j=1;j<C_NUM_S;j=j+1) begin
        n = (i-j > 0) ? (i-j-1) : (C_NUM_S+i-j-1);
        carry_rr[i*C_NUM_S+j] = carry_rr[i*C_NUM_S+j-1] | (last_rr_hot[n] & mask_rr[i*C_NUM_S+j-1]);
        if (j < C_NUM_S-1) begin
          mask_rr[i*C_NUM_S+j] = mask_rr[i*C_NUM_S+j-1] & ~valid_rr[n];
        end
      end   
      next_rr_hot[i] = valid_rr[i] & carry_rr[(i+1)*C_NUM_S-1];
    end
  end
  
endmodule


// -- (c) Copyright 2009 - 2011 Xilinx, Inc. All rights reserved.
// --
// -- This file contains confidential and proprietary information
// -- of Xilinx, Inc. and is protected under U.S. and 
// -- international copyright and other intellectual property
// -- laws.
// --
// -- DISCLAIMER
// -- This disclaimer is not a license and does not grant any
// -- rights to the materials distributed herewith. Except as
// -- otherwise provided in a valid license issued to you by
// -- Xilinx, and to the maximum extent permitted by applicable
// -- law: (1) THESE MATERIALS ARE MADE AVAILABLE "AS IS" AND
// -- WITH ALL FAULTS, AND XILINX HEREBY DISCLAIMS ALL WARRANTIES
// -- AND CONDITIONS, EXPRESS, IMPLIED, OR STATUTORY, INCLUDING
// -- BUT NOT LIMITED TO WARRANTIES OF MERCHANTABILITY, NON-
// -- INFRINGEMENT, OR FITNESS FOR ANY PARTICULAR PURPOSE; and
// -- (2) Xilinx shall not be liable (whether in contract or tort,
// -- including negligence, or under any other theory of
// -- liability) for any loss or damage of any kind or nature
// -- related to, arising under or in connection with these
// -- materials, including for any direct, or any indirect,
// -- special, incidental, or consequential loss or damage
// -- (including loss of data, profits, goodwill, or any type of
// -- loss or damage suffered as a result of any action brought
// -- by a third party) even if such damage or loss was
// -- reasonably foreseeable or Xilinx had been advised of the
// -- possibility of the same.
// --
// -- CRITICAL APPLICATIONS
// -- Xilinx products are not designed or intended to be fail-
// -- safe, or for use in any application requiring fail-safe
// -- performance, such as life-support or safety devices or
// -- systems, Class III medical devices, nuclear facilities,
// -- applications related to the deployment of airbags, or any
// -- other applications that could lead to death, personal
// -- injury, or severe property or environmental damage
// -- (individually and collectively, "Critical
// -- Applications"). Customer assumes the sole risk and
// -- liability of any use of Xilinx products in Critical
// -- Applications, subject only to applicable laws and
// -- regulations governing limitations on product liability.
// --
// -- THIS COPYRIGHT NOTICE AND DISCLAIMER MUST BE RETAINED AS
// -- PART OF THIS FILE AT ALL TIMES.
//-----------------------------------------------------------------------------
//
// File name: crossbar_sasd.v
//
// Description: 
//   This module is a M-master to N-slave AXI axi_crossbar_v2_1_19_crossbar switch.
//   Single transaction issuing, single arbiter (both W&R), single data pathways.
//   The interface of this module consists of a vectored slave and master interface
//     in which all slots are sized and synchronized to the native width and clock 
//     of the interconnect, and are all AXI4 protocol.
//   All width, clock and protocol conversions are done outside this block, as are
//     any pipeline registers or data FIFOs.
//   This module contains all arbitration, decoders and channel multiplexing logic.
//     It also contains the diagnostic registers and control interface.
//
//--------------------------------------------------------------------------
//
// Structure:
//    crossbar_sasd
//      addr_arbiter_sasd
//        mux_enc
//      addr_decoder
//        comparator_static
//      splitter
//      mux_enc
//      axic_register_slice
//      decerr_slave
//      
//-----------------------------------------------------------------------------
`timescale 1ps/1ps
`default_nettype none

(* DowngradeIPIdentifiedWarnings="yes" *) 
module axi_crossbar_v2_1_19_crossbar_sasd #
  (
   parameter         C_FAMILY                       = "none", 
   parameter integer C_NUM_SLAVE_SLOTS              =   1, 
   parameter integer C_NUM_MASTER_SLOTS             =   1, 
   parameter integer C_NUM_ADDR_RANGES              = 1,
   parameter integer C_AXI_ID_WIDTH                   = 1, 
   parameter integer C_AXI_ADDR_WIDTH                 = 32, 
   parameter integer C_AXI_DATA_WIDTH = 32, 
   parameter integer C_AXI_PROTOCOL                 = 0, 
   parameter [C_NUM_MASTER_SLOTS*C_NUM_ADDR_RANGES*64-1:0] C_M_AXI_BASE_ADDR = {C_NUM_MASTER_SLOTS*C_NUM_ADDR_RANGES*64{1'b1}}, 
   parameter [C_NUM_MASTER_SLOTS*C_NUM_ADDR_RANGES*64-1:0] C_M_AXI_HIGH_ADDR = {C_NUM_MASTER_SLOTS*C_NUM_ADDR_RANGES*64{1'b0}}, 
   parameter [C_NUM_SLAVE_SLOTS*64-1:0] C_S_AXI_BASE_ID = {C_NUM_SLAVE_SLOTS*64{1'b0}},
   parameter [C_NUM_SLAVE_SLOTS*64-1:0] C_S_AXI_HIGH_ID = {C_NUM_SLAVE_SLOTS*64{1'b0}},
   parameter integer C_AXI_SUPPORTS_USER_SIGNALS      = 0,
   parameter integer C_AXI_AWUSER_WIDTH               = 1,
   parameter integer C_AXI_ARUSER_WIDTH               = 1,
   parameter integer C_AXI_WUSER_WIDTH                = 1,
   parameter integer C_AXI_RUSER_WIDTH                = 1,
   parameter integer C_AXI_BUSER_WIDTH                = 1,
   parameter [C_NUM_SLAVE_SLOTS-1:0] C_S_AXI_SUPPORTS_WRITE           = {C_NUM_SLAVE_SLOTS{1'b1}}, 
   parameter [C_NUM_SLAVE_SLOTS-1:0] C_S_AXI_SUPPORTS_READ            = {C_NUM_SLAVE_SLOTS{1'b1}}, 
   parameter [C_NUM_MASTER_SLOTS-1:0] C_M_AXI_SUPPORTS_WRITE           = {C_NUM_MASTER_SLOTS{1'b1}}, 
   parameter [C_NUM_MASTER_SLOTS-1:0] C_M_AXI_SUPPORTS_READ            = {C_NUM_MASTER_SLOTS{1'b1}}, 
   parameter [C_NUM_SLAVE_SLOTS*32-1:0] C_S_AXI_ARB_PRIORITY             = {C_NUM_SLAVE_SLOTS{32'h00000000}},
   parameter [C_NUM_MASTER_SLOTS*32-1:0] C_M_AXI_SECURE                   = {C_NUM_MASTER_SLOTS{32'h00000000}},
   parameter [C_NUM_MASTER_SLOTS*32-1:0] C_M_AXI_ERR_MODE            = {C_NUM_MASTER_SLOTS{32'h00000000}},
   parameter integer C_R_REGISTER               = 0,
   parameter integer C_RANGE_CHECK                    = 0,
   parameter integer C_ADDR_DECODE                    = 0,
   parameter integer C_DEBUG              = 1
   )
  (
   // Global Signals
   input  wire                                                    ACLK,
   input  wire                                                    ARESETN,
   // Slave Interface Write Address Ports
   input  wire [C_NUM_SLAVE_SLOTS*C_AXI_ID_WIDTH-1:0]           S_AXI_AWID,
   input  wire [C_NUM_SLAVE_SLOTS*C_AXI_ADDR_WIDTH-1:0]           S_AXI_AWADDR,
   input  wire [C_NUM_SLAVE_SLOTS*8-1:0]                          S_AXI_AWLEN,
   input  wire [C_NUM_SLAVE_SLOTS*3-1:0]                          S_AXI_AWSIZE,
   input  wire [C_NUM_SLAVE_SLOTS*2-1:0]                          S_AXI_AWBURST,
   input  wire [C_NUM_SLAVE_SLOTS*2-1:0]                          S_AXI_AWLOCK,
   input  wire [C_NUM_SLAVE_SLOTS*4-1:0]                          S_AXI_AWCACHE,
   input  wire [C_NUM_SLAVE_SLOTS*3-1:0]                          S_AXI_AWPROT,
//   input  wire [C_NUM_SLAVE_SLOTS*4-1:0]                          S_AXI_AWREGION,
   input  wire [C_NUM_SLAVE_SLOTS*4-1:0]                          S_AXI_AWQOS,
   input  wire [C_NUM_SLAVE_SLOTS*C_AXI_AWUSER_WIDTH-1:0]         S_AXI_AWUSER,
   input  wire [C_NUM_SLAVE_SLOTS-1:0]                            S_AXI_AWVALID,
   output wire [C_NUM_SLAVE_SLOTS-1:0]                            S_AXI_AWREADY,
   // Slave Interface Write Data Ports
   input  wire [C_NUM_SLAVE_SLOTS*C_AXI_ID_WIDTH-1:0]           S_AXI_WID,
   input  wire [C_NUM_SLAVE_SLOTS*C_AXI_DATA_WIDTH-1:0]     S_AXI_WDATA,
   input  wire [C_NUM_SLAVE_SLOTS*C_AXI_DATA_WIDTH/8-1:0]   S_AXI_WSTRB,
   input  wire [C_NUM_SLAVE_SLOTS-1:0]                            S_AXI_WLAST,
   input  wire [C_NUM_SLAVE_SLOTS*C_AXI_WUSER_WIDTH-1:0]          S_AXI_WUSER,
   input  wire [C_NUM_SLAVE_SLOTS-1:0]                            S_AXI_WVALID,
   output wire [C_NUM_SLAVE_SLOTS-1:0]                            S_AXI_WREADY,
   // Slave Interface Write Response Ports
   output wire [C_NUM_SLAVE_SLOTS*C_AXI_ID_WIDTH-1:0]           S_AXI_BID,
   output wire [C_NUM_SLAVE_SLOTS*2-1:0]                          S_AXI_BRESP,
   output wire [C_NUM_SLAVE_SLOTS*C_AXI_BUSER_WIDTH-1:0]          S_AXI_BUSER,
   output wire [C_NUM_SLAVE_SLOTS-1:0]                            S_AXI_BVALID,
   input  wire [C_NUM_SLAVE_SLOTS-1:0]                            S_AXI_BREADY,
   // Slave Interface Read Address Ports
   input  wire [C_NUM_SLAVE_SLOTS*C_AXI_ID_WIDTH-1:0]           S_AXI_ARID,
   input  wire [C_NUM_SLAVE_SLOTS*C_AXI_ADDR_WIDTH-1:0]           S_AXI_ARADDR,
   input  wire [C_NUM_SLAVE_SLOTS*8-1:0]                          S_AXI_ARLEN,
   input  wire [C_NUM_SLAVE_SLOTS*3-1:0]                          S_AXI_ARSIZE,
   input  wire [C_NUM_SLAVE_SLOTS*2-1:0]                          S_AXI_ARBURST,
   input  wire [C_NUM_SLAVE_SLOTS*2-1:0]                          S_AXI_ARLOCK,
   input  wire [C_NUM_SLAVE_SLOTS*4-1:0]                          S_AXI_ARCACHE,
   input  wire [C_NUM_SLAVE_SLOTS*3-1:0]                          S_AXI_ARPROT,
//   input  wire [C_NUM_SLAVE_SLOTS*4-1:0]                          S_AXI_ARREGION,
   input  wire [C_NUM_SLAVE_SLOTS*4-1:0]                          S_AXI_ARQOS,
   input  wire [C_NUM_SLAVE_SLOTS*C_AXI_ARUSER_WIDTH-1:0]         S_AXI_ARUSER,
   input  wire [C_NUM_SLAVE_SLOTS-1:0]                            S_AXI_ARVALID,
   output wire [C_NUM_SLAVE_SLOTS-1:0]                            S_AXI_ARREADY,
   // Slave Interface Read Data Ports
   output wire [C_NUM_SLAVE_SLOTS*C_AXI_ID_WIDTH-1:0]           S_AXI_RID,
   output wire [C_NUM_SLAVE_SLOTS*C_AXI_DATA_WIDTH-1:0]     S_AXI_RDATA,
   output wire [C_NUM_SLAVE_SLOTS*2-1:0]                          S_AXI_RRESP,
   output wire [C_NUM_SLAVE_SLOTS-1:0]                            S_AXI_RLAST,
   output wire [C_NUM_SLAVE_SLOTS*C_AXI_RUSER_WIDTH-1:0]          S_AXI_RUSER,
   output wire [C_NUM_SLAVE_SLOTS-1:0]                            S_AXI_RVALID,
   input  wire [C_NUM_SLAVE_SLOTS-1:0]                            S_AXI_RREADY,
   // Master Interface Write Address Port
   output wire [C_NUM_MASTER_SLOTS*C_AXI_ID_WIDTH-1:0]          M_AXI_AWID,
   output wire [C_NUM_MASTER_SLOTS*C_AXI_ADDR_WIDTH-1:0]          M_AXI_AWADDR,
   output wire [C_NUM_MASTER_SLOTS*8-1:0]                         M_AXI_AWLEN,
   output wire [C_NUM_MASTER_SLOTS*3-1:0]                         M_AXI_AWSIZE,
   output wire [C_NUM_MASTER_SLOTS*2-1:0]                         M_AXI_AWBURST,
   output wire [C_NUM_MASTER_SLOTS*2-1:0]                         M_AXI_AWLOCK,
   output wire [C_NUM_MASTER_SLOTS*4-1:0]                         M_AXI_AWCACHE,
   output wire [C_NUM_MASTER_SLOTS*3-1:0]                         M_AXI_AWPROT,
   output wire [C_NUM_MASTER_SLOTS*4-1:0]                         M_AXI_AWREGION,
   output wire [C_NUM_MASTER_SLOTS*4-1:0]                         M_AXI_AWQOS,
   output wire [C_NUM_MASTER_SLOTS*C_AXI_AWUSER_WIDTH-1:0]        M_AXI_AWUSER,
   output wire [C_NUM_MASTER_SLOTS-1:0]                           M_AXI_AWVALID,
   input  wire [C_NUM_MASTER_SLOTS-1:0]                           M_AXI_AWREADY,
   // Master Interface Write Data Ports
   output wire [C_NUM_MASTER_SLOTS*C_AXI_ID_WIDTH-1:0]          M_AXI_WID,
   output wire [C_NUM_MASTER_SLOTS*C_AXI_DATA_WIDTH-1:0]    M_AXI_WDATA,
   output wire [C_NUM_MASTER_SLOTS*C_AXI_DATA_WIDTH/8-1:0]  M_AXI_WSTRB,
   output wire [C_NUM_MASTER_SLOTS-1:0]                           M_AXI_WLAST,
   output wire [C_NUM_MASTER_SLOTS*C_AXI_WUSER_WIDTH-1:0]         M_AXI_WUSER,
   output wire [C_NUM_MASTER_SLOTS-1:0]                           M_AXI_WVALID,
   input  wire [C_NUM_MASTER_SLOTS-1:0]                           M_AXI_WREADY,
   // Master Interface Write Response Ports
   input  wire [C_NUM_MASTER_SLOTS*C_AXI_ID_WIDTH-1:0]          M_AXI_BID,  // Unused
   input  wire [C_NUM_MASTER_SLOTS*2-1:0]                         M_AXI_BRESP,
   input  wire [C_NUM_MASTER_SLOTS*C_AXI_BUSER_WIDTH-1:0]         M_AXI_BUSER,
   input  wire [C_NUM_MASTER_SLOTS-1:0]                           M_AXI_BVALID,
   output wire [C_NUM_MASTER_SLOTS-1:0]                           M_AXI_BREADY,
   // Master Interface Read Address Port
   output wire [C_NUM_MASTER_SLOTS*C_AXI_ID_WIDTH-1:0]          M_AXI_ARID,
   output wire [C_NUM_MASTER_SLOTS*C_AXI_ADDR_WIDTH-1:0]          M_AXI_ARADDR,
   output wire [C_NUM_MASTER_SLOTS*8-1:0]                         M_AXI_ARLEN,
   output wire [C_NUM_MASTER_SLOTS*3-1:0]                         M_AXI_ARSIZE,
   output wire [C_NUM_MASTER_SLOTS*2-1:0]                         M_AXI_ARBURST,
   output wire [C_NUM_MASTER_SLOTS*2-1:0]                         M_AXI_ARLOCK,
   output wire [C_NUM_MASTER_SLOTS*4-1:0]                         M_AXI_ARCACHE,
   output wire [C_NUM_MASTER_SLOTS*3-1:0]                         M_AXI_ARPROT,
   output wire [C_NUM_MASTER_SLOTS*4-1:0]                         M_AXI_ARREGION,
   output wire [C_NUM_MASTER_SLOTS*4-1:0]                         M_AXI_ARQOS,
   output wire [C_NUM_MASTER_SLOTS*C_AXI_ARUSER_WIDTH-1:0]        M_AXI_ARUSER,
   output wire [C_NUM_MASTER_SLOTS-1:0]                           M_AXI_ARVALID,
   input  wire [C_NUM_MASTER_SLOTS-1:0]                           M_AXI_ARREADY,
   // Master Interface Read Data Ports
   input  wire [C_NUM_MASTER_SLOTS*C_AXI_ID_WIDTH-1:0]          M_AXI_RID,  // Unused
   input  wire [C_NUM_MASTER_SLOTS*C_AXI_DATA_WIDTH-1:0]    M_AXI_RDATA,
   input  wire [C_NUM_MASTER_SLOTS*2-1:0]                         M_AXI_RRESP,
   input  wire [C_NUM_MASTER_SLOTS-1:0]                           M_AXI_RLAST,
   input wire [C_NUM_MASTER_SLOTS*C_AXI_RUSER_WIDTH-1:0]         M_AXI_RUSER,
   input  wire [C_NUM_MASTER_SLOTS-1:0]                           M_AXI_RVALID,
   output wire [C_NUM_MASTER_SLOTS-1:0]                           M_AXI_RREADY
   );
   
  localparam integer  P_AXI4 = 0;
  localparam integer  P_AXI3 = 1;
  localparam integer  P_AXILITE = 2;
  localparam integer P_NUM_MASTER_SLOTS_DE = C_RANGE_CHECK ? C_NUM_MASTER_SLOTS+1 : C_NUM_MASTER_SLOTS;
  localparam integer P_NUM_MASTER_SLOTS_LOG = (C_NUM_MASTER_SLOTS>1) ? f_ceil_log2(C_NUM_MASTER_SLOTS) : 1;
  localparam integer P_NUM_MASTER_SLOTS_DE_LOG = (P_NUM_MASTER_SLOTS_DE>1) ? f_ceil_log2(P_NUM_MASTER_SLOTS_DE) : 1;
  localparam integer P_NUM_SLAVE_SLOTS_LOG = (C_NUM_SLAVE_SLOTS>1) ? f_ceil_log2(C_NUM_SLAVE_SLOTS) : 1;
  localparam integer P_AXI_AUSER_WIDTH = (C_AXI_AWUSER_WIDTH > C_AXI_ARUSER_WIDTH) ? C_AXI_AWUSER_WIDTH : C_AXI_ARUSER_WIDTH;
  localparam integer P_AXI_WID_WIDTH = (C_AXI_PROTOCOL == P_AXI3) ? C_AXI_ID_WIDTH : 1;
  localparam integer P_AMESG_WIDTH = C_AXI_ID_WIDTH + C_AXI_ADDR_WIDTH + 8+3+2+3+2+4+4 + P_AXI_AUSER_WIDTH + 4;
  localparam integer P_BMESG_WIDTH = 2 + C_AXI_BUSER_WIDTH;
  localparam integer P_RMESG_WIDTH = 1+2 + C_AXI_DATA_WIDTH + C_AXI_RUSER_WIDTH;
  localparam integer P_WMESG_WIDTH = 1 + C_AXI_DATA_WIDTH + C_AXI_DATA_WIDTH/8 + C_AXI_WUSER_WIDTH + P_AXI_WID_WIDTH;
  localparam [31:0]   P_AXILITE_ERRMODE = 32'h00000001;
  localparam integer P_NONSECURE_BIT = 1; 
  localparam [C_NUM_MASTER_SLOTS-1:0] P_M_SECURE_MASK = f_bit32to1_mi(C_M_AXI_SECURE);  // Mask of secure MI-slots
  localparam [C_NUM_MASTER_SLOTS-1:0] P_M_AXILITE_MASK = f_m_axilite(0);  // Mask of axilite rule-check MI-slots
  localparam [1:0]   P_FIXED = 2'b00;
  localparam integer P_BYPASS = 0;
  localparam integer P_LIGHTWT = 7;
  localparam integer P_FULLY_REG = 1;
  localparam integer P_R_REG_CONFIG = C_R_REGISTER == 8 ?  // "Automatic" reg-slice
        (C_RANGE_CHECK ? ((C_AXI_PROTOCOL == P_AXILITE) ? P_LIGHTWT : P_FULLY_REG) : P_BYPASS) :  // Bypass if no R-channel mux
        C_R_REGISTER;
  localparam P_DECERR = 2'b11;

  //---------------------------------------------------------------------------
  // Functions
  //---------------------------------------------------------------------------
  // Ceiling of log2(x)
  function integer f_ceil_log2
    (
     input integer x
     );
    integer acc;
    begin
      acc=0;
      while ((2**acc) < x)
        acc = acc + 1;
      f_ceil_log2 = acc;
    end
  endfunction

  // Isolate thread bits of input S_ID and add to BASE_ID (RNG00) to form MI-side ID value
  //   only for end-point SI-slots
  function [C_AXI_ID_WIDTH-1:0] f_extend_ID
    (
     input [C_AXI_ID_WIDTH-1:0] s_id,
     input integer slot
     );
    begin
      f_extend_ID = C_S_AXI_BASE_ID[slot*64+:C_AXI_ID_WIDTH] | (s_id & (C_S_AXI_BASE_ID[slot*64+:C_AXI_ID_WIDTH] ^ C_S_AXI_HIGH_ID[slot*64+:C_AXI_ID_WIDTH]));
    end
  endfunction

  // Convert Bit32 vector of range [0,1] to Bit1 vector on MI
  function [C_NUM_MASTER_SLOTS-1:0] f_bit32to1_mi
    (input [C_NUM_MASTER_SLOTS*32-1:0] vec32);
    integer mi;
    begin
      for (mi=0; mi<C_NUM_MASTER_SLOTS; mi=mi+1) begin
        f_bit32to1_mi[mi] = vec32[mi*32];
      end
    end
  endfunction

  // AxiLite error-checking mask (on MI)      
  function [C_NUM_MASTER_SLOTS-1:0] f_m_axilite
    (
      input integer null_arg
    );
    integer mi;
    begin
      for (mi=0; mi<C_NUM_MASTER_SLOTS; mi=mi+1) begin
        f_m_axilite[mi] = (C_M_AXI_ERR_MODE[mi*32+:32] == P_AXILITE_ERRMODE);
      end
    end
  endfunction

  genvar gen_si_slot;
  genvar gen_mi_slot;
  wire [C_NUM_SLAVE_SLOTS*P_AMESG_WIDTH-1:0]                      si_awmesg          ;
  wire [C_NUM_SLAVE_SLOTS*P_AMESG_WIDTH-1:0]                      si_armesg          ;
  wire [P_AMESG_WIDTH-1:0]                                        aa_amesg         ;
  wire [C_AXI_ID_WIDTH-1:0]                                       mi_aid            ;
  wire [C_AXI_ADDR_WIDTH-1:0]                                     mi_aaddr          ;
  wire [8-1:0]                                                    mi_alen           ;
  wire [3-1:0]                                                    mi_asize          ;
  wire [2-1:0]                                                    mi_alock          ;
  wire [3-1:0]                                                    mi_aprot          ;
  wire [2-1:0]                                                    mi_aburst        ;
  wire [4-1:0]                                                    mi_acache        ;
  wire [4-1:0]                                                    mi_aregion        ;
  wire [4-1:0]                                                    mi_aqos        ;
  wire [P_AXI_AUSER_WIDTH-1:0]                                    mi_auser        ;
  wire [4-1:0]                                                    target_region        ;
  wire [C_NUM_SLAVE_SLOTS*1-1:0]                                  aa_grant_hot     ;
  wire [P_NUM_SLAVE_SLOTS_LOG-1:0]                                  aa_grant_enc     ;
  wire                                                            aa_grant_rnw ;
  wire                                                            aa_grant_any ;
  wire [C_NUM_MASTER_SLOTS-1:0]                                   target_mi_hot    ;
  wire [P_NUM_MASTER_SLOTS_LOG-1:0]                                   target_mi_enc    ;
  reg  [P_NUM_MASTER_SLOTS_DE-1:0]                               m_atarget_hot = 0    ;
  reg  [P_NUM_MASTER_SLOTS_DE_LOG-1:0]                               m_atarget_enc = 0    ;
  wire [P_NUM_MASTER_SLOTS_DE_LOG-1:0]                               m_atarget_enc_comb    ;
  wire                                                            match;
  wire                                                            any_error         ;
  wire [7:0]                                                      m_aerror_i         ;
  wire [P_NUM_MASTER_SLOTS_DE-1:0]                             mi_awvalid            ;
  wire [P_NUM_MASTER_SLOTS_DE-1:0]                             mi_awready            ;
  wire [P_NUM_MASTER_SLOTS_DE-1:0]                             mi_arvalid            ;
  wire [P_NUM_MASTER_SLOTS_DE-1:0]                             mi_arready            ;
  wire                                                            aa_awvalid         ;
  wire                                                            aa_awready         ;
  wire                                                            aa_arvalid         ;
  wire                                                            aa_arready         ;
  wire                                                            mi_awvalid_en;
  wire                                                            mi_awready_mux;
  wire                                                            mi_arvalid_en;
  wire                                                            mi_arready_mux;
  wire                                                            w_transfer_en;
  wire                                                            w_complete_mux;
  wire                                                            b_transfer_en;
  wire                                                            b_complete_mux;
  wire                                                            r_transfer_en;
  wire                                                            r_complete_mux;
  wire                                                            target_secure;
  wire                                                            target_write;
  wire                                                            target_read;
  wire                                                            target_axilite;
  
  wire [P_BMESG_WIDTH-1:0]                                        si_bmesg           ;
  wire [P_NUM_MASTER_SLOTS_DE*P_BMESG_WIDTH-1:0]                 mi_bmesg           ;
  wire [P_NUM_MASTER_SLOTS_DE*2-1:0]                             mi_bresp           ;
  wire [P_NUM_MASTER_SLOTS_DE*C_AXI_BUSER_WIDTH-1:0]             mi_buser           ;
  wire [2-1:0]                                                    si_bresp           ;
  wire [C_AXI_BUSER_WIDTH-1:0]                                    si_buser           ;
  wire [P_NUM_MASTER_SLOTS_DE-1:0]                             mi_bvalid          ;
  wire [P_NUM_MASTER_SLOTS_DE-1:0]                             mi_bready          ;
  wire                                                            aa_bvalid          ;
  wire                                                            aa_bready         ;
  wire                                                            si_bready         ;
  wire [C_NUM_SLAVE_SLOTS-1:0]                                    si_bvalid;
  
  wire [P_RMESG_WIDTH-1:0]                                        aa_rmesg           ;
  wire [P_RMESG_WIDTH-1:0]                                        sr_rmesg           ;
  wire [P_NUM_MASTER_SLOTS_DE*P_RMESG_WIDTH-1:0]                 mi_rmesg           ;
  wire [P_NUM_MASTER_SLOTS_DE*2-1:0]                             mi_rresp           ;
  wire [P_NUM_MASTER_SLOTS_DE*C_AXI_RUSER_WIDTH-1:0]             mi_ruser           ;
  wire [P_NUM_MASTER_SLOTS_DE*C_AXI_DATA_WIDTH-1:0]          mi_rdata              ;
  wire [P_NUM_MASTER_SLOTS_DE*1-1:0]                             mi_rlast              ;
  wire [2-1:0]                                                    si_rresp           ;
  wire [C_AXI_RUSER_WIDTH-1:0]                                    si_ruser           ;
  wire [C_AXI_DATA_WIDTH-1:0]                                 si_rdata              ;
  wire                                                            si_rlast              ;
  wire [P_NUM_MASTER_SLOTS_DE-1:0]                             mi_rvalid          ;
  wire [P_NUM_MASTER_SLOTS_DE-1:0]                             mi_rready          ;
  wire                                                            aa_rvalid          ;
  wire                                                            aa_rready         ;
  wire                                                            sr_rvalid          ;
  wire                                                            si_rready         ;
  wire                                                            sr_rready         ;
  wire [C_NUM_SLAVE_SLOTS-1:0]                                    si_rvalid;
  
  wire [C_NUM_SLAVE_SLOTS*P_WMESG_WIDTH-1:0]                      si_wmesg           ;
  wire [P_WMESG_WIDTH-1:0]                                        mi_wmesg           ;
  wire [C_AXI_ID_WIDTH-1:0]                                    mi_wid              ;
  wire [C_AXI_DATA_WIDTH-1:0]                            mi_wdata              ;
  wire [C_AXI_DATA_WIDTH/8-1:0]                          mi_wstrb              ;
  wire [C_AXI_WUSER_WIDTH-1:0]                                    mi_wuser              ;
  wire [1-1:0]                                                    mi_wlast              ;
  wire [P_NUM_MASTER_SLOTS_DE-1:0]                             mi_wvalid          ;
  wire [P_NUM_MASTER_SLOTS_DE-1:0]                             mi_wready          ;
  wire                                                            aa_wvalid          ;
  wire                                                            aa_wready         ;
  wire [C_NUM_SLAVE_SLOTS-1:0]                                    si_wready;
  
  reg  [7:0]                                                      debug_r_beat_cnt_i;
  reg  [7:0]                                                      debug_w_beat_cnt_i;
  reg  [7:0]                                                      debug_aw_trans_seq_i;
  reg  [7:0]                                                      debug_ar_trans_seq_i;

  reg aresetn_d = 1'b0; // Reset delay register
  always @(posedge ACLK) begin
    if (~ARESETN) begin
      aresetn_d <= 1'b0;
    end else begin
      aresetn_d <= ARESETN;
    end
  end
  wire reset;
  assign reset = ~aresetn_d;

  generate
    axi_crossbar_v2_1_19_addr_arbiter_sasd #
      (
       .C_FAMILY                (C_FAMILY),
       .C_NUM_S                 (C_NUM_SLAVE_SLOTS),
       .C_NUM_S_LOG             (P_NUM_SLAVE_SLOTS_LOG),
       .C_AMESG_WIDTH            (P_AMESG_WIDTH),
       .C_GRANT_ENC             (1),
       .C_ARB_PRIORITY          (C_S_AXI_ARB_PRIORITY)
       )
      addr_arbiter_inst
        (
         .ACLK                  (ACLK),
         .ARESET                (reset),
         // Vector of SI-side AW command request inputs
         .S_AWMESG                (si_awmesg),
         .S_ARMESG                (si_armesg),
         .S_AWVALID               (S_AXI_AWVALID),
         .S_AWREADY               (S_AXI_AWREADY),
         .S_ARVALID               (S_AXI_ARVALID),
         .S_ARREADY               (S_AXI_ARREADY),
         .M_GRANT_ENC           (aa_grant_enc),
         .M_GRANT_HOT           (aa_grant_hot),  // SI-slot 1-hot mask of granted command
         .M_GRANT_ANY             (aa_grant_any),
         .M_GRANT_RNW             (aa_grant_rnw),
         .M_AMESG                (aa_amesg),  // Either S_AWMESG or S_ARMESG, as indicated by M_AWVALID and M_ARVALID.
         .M_AWVALID               (aa_awvalid),
         .M_AWREADY               (aa_awready),
         .M_ARVALID               (aa_arvalid),
         .M_ARREADY               (aa_arready)
         );

    if (C_ADDR_DECODE) begin : gen_addr_decoder
      axi_crossbar_v2_1_19_addr_decoder #
        (
          .C_FAMILY          (C_FAMILY),
          .C_NUM_TARGETS     (C_NUM_MASTER_SLOTS),
          .C_NUM_TARGETS_LOG (P_NUM_MASTER_SLOTS_LOG),
          .C_NUM_RANGES      (C_NUM_ADDR_RANGES),
          .C_ADDR_WIDTH      (C_AXI_ADDR_WIDTH),
          .C_TARGET_ENC      (1),
          .C_TARGET_HOT      (1),
          .C_REGION_ENC      (1),
          .C_BASE_ADDR      (C_M_AXI_BASE_ADDR),
          .C_HIGH_ADDR      (C_M_AXI_HIGH_ADDR),
          .C_TARGET_QUAL     ({C_NUM_MASTER_SLOTS{1'b1}}),
          .C_RESOLUTION      (2)
        ) 
        addr_decoder_inst 
        (
          .ADDR             (mi_aaddr),        
          .TARGET_HOT       (target_mi_hot),  
          .TARGET_ENC       (target_mi_enc),  
          .MATCH            (match),       
          .REGION           (target_region)      
        );
    end else begin : gen_no_addr_decoder
      assign target_mi_hot = 1;
      assign match = 1'b1;
      assign target_region = 4'b0000;
    end  // gen_addr_decoder
    
    // AW-channel arbiter command transfer completes upon completion of both M-side AW-channel transfer and B channel completion.
    axi_crossbar_v2_1_19_splitter #  
      (
        .C_NUM_M                (3)
      )
      splitter_aw
      (
         .ACLK                  (ACLK),
         .ARESET                (reset),
         .S_VALID              (aa_awvalid),
         .S_READY              (aa_awready),
         .M_VALID              ({mi_awvalid_en, w_transfer_en, b_transfer_en}),
         .M_READY              ({mi_awready_mux, w_complete_mux, b_complete_mux})
      );
    
    // AR-channel arbiter command transfer completes upon completion of both M-side AR-channel transfer and R channel completion.
    axi_crossbar_v2_1_19_splitter #  
      (
        .C_NUM_M                (2)
      )
      splitter_ar
      (
         .ACLK                  (ACLK),
         .ARESET                (reset),
         .S_VALID              (aa_arvalid),
         .S_READY              (aa_arready),
         .M_VALID              ({mi_arvalid_en, r_transfer_en}),
         .M_READY              ({mi_arready_mux, r_complete_mux})
      );
    
    assign target_secure = |(target_mi_hot & P_M_SECURE_MASK);
    assign target_write = |(target_mi_hot & C_M_AXI_SUPPORTS_WRITE);
    assign target_read = |(target_mi_hot & C_M_AXI_SUPPORTS_READ);
    assign target_axilite = |(target_mi_hot & P_M_AXILITE_MASK);
    
    assign any_error = C_RANGE_CHECK && (m_aerror_i != 0);             // DECERR if error-detection enabled and any error condition.
    assign m_aerror_i[0] = ~match;                                     // Invalid target address
    assign m_aerror_i[1] = target_secure && mi_aprot[P_NONSECURE_BIT]; // TrustZone violation
    assign m_aerror_i[2] = target_axilite && ((mi_alen != 0) || 
      (mi_asize[1:0] == 2'b11) || (mi_asize[2] == 1'b1));              // AxiLite access violation
    assign m_aerror_i[3] = (~aa_grant_rnw && ~target_write) ||
      (aa_grant_rnw && ~target_read);                                  // R/W direction unsupported by target
    assign m_aerror_i[7:4] = 4'b0000;                                     // Reserved
    assign m_atarget_enc_comb = any_error ? (P_NUM_MASTER_SLOTS_DE-1) : target_mi_enc;  // Select MI slot or decerr_slave
      
    always @(posedge ACLK) begin
      if (reset) begin
        m_atarget_hot <= 0;
        m_atarget_enc <= 0;
      end else begin
        m_atarget_hot <= {P_NUM_MASTER_SLOTS_DE{aa_grant_any}} & (any_error ? {1'b1, {C_NUM_MASTER_SLOTS{1'b0}}} : {1'b0, target_mi_hot});  // Select MI slot or decerr_slave
        m_atarget_enc <= m_atarget_enc_comb;
      end
    end
    
    // Receive AWREADY from targeted MI.
    generic_baseblocks_v2_1_0_mux_enc # 
      (
       .C_FAMILY      ("rtl"),
       .C_RATIO       (P_NUM_MASTER_SLOTS_DE),
       .C_SEL_WIDTH   (P_NUM_MASTER_SLOTS_DE_LOG),
       .C_DATA_WIDTH  (1)
      ) mi_awready_mux_inst 
      (
       .S   (m_atarget_enc),
       .A   (mi_awready),
       .O   (mi_awready_mux),
       .OE  (mi_awvalid_en)
      ); 
      
    // Receive ARREADY from targeted MI.
    generic_baseblocks_v2_1_0_mux_enc # 
      (
       .C_FAMILY      ("rtl"),
       .C_RATIO       (P_NUM_MASTER_SLOTS_DE),
       .C_SEL_WIDTH   (P_NUM_MASTER_SLOTS_DE_LOG),
       .C_DATA_WIDTH  (1)
      ) mi_arready_mux_inst 
      (
       .S   (m_atarget_enc),
       .A   (mi_arready),
       .O   (mi_arready_mux),
       .OE  (mi_arvalid_en)
      ); 
      
    assign mi_awvalid = m_atarget_hot & {P_NUM_MASTER_SLOTS_DE{mi_awvalid_en}};  // Assert AWVALID on targeted MI.
    assign mi_arvalid = m_atarget_hot & {P_NUM_MASTER_SLOTS_DE{mi_arvalid_en}};  // Assert ARVALID on targeted MI.
    assign M_AXI_AWVALID = mi_awvalid[0+:C_NUM_MASTER_SLOTS];  // Propagate to MI slots.
    assign M_AXI_ARVALID = mi_arvalid[0+:C_NUM_MASTER_SLOTS];  // Propagate to MI slots.
    assign mi_awready[0+:C_NUM_MASTER_SLOTS] = M_AXI_AWREADY;  // Copy from MI slots.
    assign mi_arready[0+:C_NUM_MASTER_SLOTS] = M_AXI_ARREADY;  // Copy from MI slots.
    
    // Receive WREADY from targeted MI.
    generic_baseblocks_v2_1_0_mux_enc # 
      (
       .C_FAMILY      ("rtl"),
       .C_RATIO       (P_NUM_MASTER_SLOTS_DE),
       .C_SEL_WIDTH   (P_NUM_MASTER_SLOTS_DE_LOG),
       .C_DATA_WIDTH  (1)
      ) mi_wready_mux_inst 
      (
       .S   (m_atarget_enc),
       .A   (mi_wready),
       .O   (aa_wready),
       .OE  (w_transfer_en)
      ); 
      
    assign mi_wvalid = m_atarget_hot & {P_NUM_MASTER_SLOTS_DE{aa_wvalid}};  // Assert WVALID on targeted MI.
    assign si_wready = aa_grant_hot & {C_NUM_SLAVE_SLOTS{aa_wready}};  // Assert WREADY on granted SI.
    assign S_AXI_WREADY = si_wready;
    assign w_complete_mux = aa_wready & aa_wvalid & mi_wlast;  // W burst complete on on designated SI/MI.
    
    // Receive RREADY from granted SI.
    generic_baseblocks_v2_1_0_mux_enc # 
      (
       .C_FAMILY      ("rtl"),
       .C_RATIO       (C_NUM_SLAVE_SLOTS),
       .C_SEL_WIDTH   (P_NUM_SLAVE_SLOTS_LOG),
       .C_DATA_WIDTH  (1)
      ) si_rready_mux_inst 
      (
       .S   (aa_grant_enc),
       .A   (S_AXI_RREADY),
       .O   (si_rready),
       .OE  (r_transfer_en)
      ); 
      
    assign sr_rready = si_rready & r_transfer_en;
    assign mi_rready = m_atarget_hot & {P_NUM_MASTER_SLOTS_DE{aa_rready}};  // Assert RREADY on targeted MI.
    assign si_rvalid = aa_grant_hot & {C_NUM_SLAVE_SLOTS{sr_rvalid}};  // Assert RVALID on granted SI.
    assign S_AXI_RVALID = si_rvalid;
    assign r_complete_mux = sr_rready & sr_rvalid & si_rlast;  // R burst complete on on designated SI/MI.
    
    // Receive BREADY from granted SI.
    generic_baseblocks_v2_1_0_mux_enc # 
      (
       .C_FAMILY      ("rtl"),
       .C_RATIO       (C_NUM_SLAVE_SLOTS),
       .C_SEL_WIDTH   (P_NUM_SLAVE_SLOTS_LOG),
       .C_DATA_WIDTH  (1)
      ) si_bready_mux_inst 
      (
       .S   (aa_grant_enc),
       .A   (S_AXI_BREADY),
       .O   (si_bready),
       .OE  (b_transfer_en)
      ); 
      
    assign aa_bready = si_bready & b_transfer_en;
    assign mi_bready = m_atarget_hot & {P_NUM_MASTER_SLOTS_DE{aa_bready}};  // Assert BREADY on targeted MI.
    assign si_bvalid = aa_grant_hot & {C_NUM_SLAVE_SLOTS{aa_bvalid}};  // Assert BVALID on granted SI.
    assign S_AXI_BVALID = si_bvalid;
    assign b_complete_mux = aa_bready & aa_bvalid;  // B transfer complete on on designated SI/MI.
    
    for (gen_si_slot=0; gen_si_slot<C_NUM_SLAVE_SLOTS; gen_si_slot=gen_si_slot+1) begin : gen_si_amesg
      assign si_armesg[gen_si_slot*P_AMESG_WIDTH +: P_AMESG_WIDTH] = {  // Concatenate from MSB to LSB
        4'b0000,
//        S_AXI_ARREGION[gen_si_slot*4+:4],
        S_AXI_ARUSER[gen_si_slot*C_AXI_ARUSER_WIDTH +: C_AXI_ARUSER_WIDTH],
        S_AXI_ARQOS[gen_si_slot*4+:4],
        S_AXI_ARCACHE[gen_si_slot*4+:4],
        S_AXI_ARBURST[gen_si_slot*2+:2],
        S_AXI_ARPROT[gen_si_slot*3+:3],
        S_AXI_ARLOCK[gen_si_slot*2+:2],
        S_AXI_ARSIZE[gen_si_slot*3+:3],
        S_AXI_ARLEN[gen_si_slot*8+:8],
        S_AXI_ARADDR[gen_si_slot*C_AXI_ADDR_WIDTH +: C_AXI_ADDR_WIDTH],
        f_extend_ID(S_AXI_ARID[gen_si_slot*C_AXI_ID_WIDTH +: C_AXI_ID_WIDTH], gen_si_slot)
        };
      assign si_awmesg[gen_si_slot*P_AMESG_WIDTH +: P_AMESG_WIDTH] = {  // Concatenate from MSB to LSB
        4'b0000,
//        S_AXI_AWREGION[gen_si_slot*4+:4],
        S_AXI_AWUSER[gen_si_slot*C_AXI_AWUSER_WIDTH +: C_AXI_AWUSER_WIDTH],
        S_AXI_AWQOS[gen_si_slot*4+:4],
        S_AXI_AWCACHE[gen_si_slot*4+:4],
        S_AXI_AWBURST[gen_si_slot*2+:2],
        S_AXI_AWPROT[gen_si_slot*3+:3],
        S_AXI_AWLOCK[gen_si_slot*2+:2],
        S_AXI_AWSIZE[gen_si_slot*3+:3],
        S_AXI_AWLEN[gen_si_slot*8+:8],
        S_AXI_AWADDR[gen_si_slot*C_AXI_ADDR_WIDTH +: C_AXI_ADDR_WIDTH],
        f_extend_ID(S_AXI_AWID[gen_si_slot*C_AXI_ID_WIDTH+:C_AXI_ID_WIDTH], gen_si_slot)
        };
    end  // gen_si_amesg
    
    assign mi_aid        = aa_amesg[0 +: C_AXI_ID_WIDTH];
    assign mi_aaddr      = aa_amesg[C_AXI_ID_WIDTH +: C_AXI_ADDR_WIDTH];
    assign mi_alen       = aa_amesg[C_AXI_ID_WIDTH+C_AXI_ADDR_WIDTH +: 8];
    assign mi_asize      = aa_amesg[C_AXI_ID_WIDTH+C_AXI_ADDR_WIDTH+8 +: 3];
    assign mi_alock      = aa_amesg[C_AXI_ID_WIDTH+C_AXI_ADDR_WIDTH+8+3 +: 2];
    assign mi_aprot      = aa_amesg[C_AXI_ID_WIDTH+C_AXI_ADDR_WIDTH+8+3+2 +: 3];
    assign mi_aburst     = aa_amesg[C_AXI_ID_WIDTH+C_AXI_ADDR_WIDTH+8+3+2+3 +: 2];
    assign mi_acache     = aa_amesg[C_AXI_ID_WIDTH+C_AXI_ADDR_WIDTH+8+3+2+3+2 +: 4];
    assign mi_aqos       = aa_amesg[C_AXI_ID_WIDTH+C_AXI_ADDR_WIDTH+8+3+2+3+2+4 +: 4];
    assign mi_auser      = aa_amesg[C_AXI_ID_WIDTH+C_AXI_ADDR_WIDTH+8+3+2+3+2+4+4 +: P_AXI_AUSER_WIDTH];
    assign mi_aregion    = (C_ADDR_DECODE != 0) ? target_region : aa_amesg[C_AXI_ID_WIDTH+C_AXI_ADDR_WIDTH+8+3+2+3+2+4+4+P_AXI_AUSER_WIDTH +: 4];
      
    // Broadcast AW transfer payload to all MI-slots
    assign M_AXI_AWID        = {C_NUM_MASTER_SLOTS{mi_aid}};
    assign M_AXI_AWADDR      = {C_NUM_MASTER_SLOTS{mi_aaddr}};
    assign M_AXI_AWLEN       = {C_NUM_MASTER_SLOTS{mi_alen }};
    assign M_AXI_AWSIZE      = {C_NUM_MASTER_SLOTS{mi_asize}};
    assign M_AXI_AWLOCK      = {C_NUM_MASTER_SLOTS{mi_alock}};
    assign M_AXI_AWPROT      = {C_NUM_MASTER_SLOTS{mi_aprot}};
    assign M_AXI_AWREGION    = {C_NUM_MASTER_SLOTS{mi_aregion}};
    assign M_AXI_AWBURST     = {C_NUM_MASTER_SLOTS{mi_aburst}};
    assign M_AXI_AWCACHE     = {C_NUM_MASTER_SLOTS{mi_acache}};
    assign M_AXI_AWQOS       = {C_NUM_MASTER_SLOTS{mi_aqos  }};
    assign M_AXI_AWUSER      = {C_NUM_MASTER_SLOTS{mi_auser[0+:C_AXI_AWUSER_WIDTH] }};
    
    // Broadcast AR transfer payload to all MI-slots
    assign M_AXI_ARID        = {C_NUM_MASTER_SLOTS{mi_aid}};
    assign M_AXI_ARADDR      = {C_NUM_MASTER_SLOTS{mi_aaddr}};                        
    assign M_AXI_ARLEN       = {C_NUM_MASTER_SLOTS{mi_alen }};                        
    assign M_AXI_ARSIZE      = {C_NUM_MASTER_SLOTS{mi_asize}};                        
    assign M_AXI_ARLOCK      = {C_NUM_MASTER_SLOTS{mi_alock}};                        
    assign M_AXI_ARPROT      = {C_NUM_MASTER_SLOTS{mi_aprot}};                        
    assign M_AXI_ARREGION    = {C_NUM_MASTER_SLOTS{mi_aregion}};                          
    assign M_AXI_ARBURST     = {C_NUM_MASTER_SLOTS{mi_aburst}};                       
    assign M_AXI_ARCACHE     = {C_NUM_MASTER_SLOTS{mi_acache}};                       
    assign M_AXI_ARQOS       = {C_NUM_MASTER_SLOTS{mi_aqos  }};                       
    assign M_AXI_ARUSER      = {C_NUM_MASTER_SLOTS{mi_auser[0+:C_AXI_ARUSER_WIDTH] }};
    
    // W-channel MI handshakes
    assign M_AXI_WVALID = mi_wvalid[0+:C_NUM_MASTER_SLOTS];
    assign mi_wready[0+:C_NUM_MASTER_SLOTS] = M_AXI_WREADY;
    // Broadcast W transfer payload to all MI-slots
    assign M_AXI_WLAST = {C_NUM_MASTER_SLOTS{mi_wlast}};
    assign M_AXI_WUSER = {C_NUM_MASTER_SLOTS{mi_wuser}};
    assign M_AXI_WDATA = {C_NUM_MASTER_SLOTS{mi_wdata}};
    assign M_AXI_WSTRB = {C_NUM_MASTER_SLOTS{mi_wstrb}};
    assign M_AXI_WID =   {C_NUM_MASTER_SLOTS{mi_wid}};
    
    // Broadcast R transfer payload to all SI-slots
    assign S_AXI_RLAST = {C_NUM_SLAVE_SLOTS{si_rlast}};
    assign S_AXI_RRESP = {C_NUM_SLAVE_SLOTS{si_rresp}};
    assign S_AXI_RUSER = {C_NUM_SLAVE_SLOTS{si_ruser}};
    assign S_AXI_RDATA = {C_NUM_SLAVE_SLOTS{si_rdata}};
    assign S_AXI_RID =   {C_NUM_SLAVE_SLOTS{mi_aid}};
    
    // Broadcast B transfer payload to all SI-slots
    assign S_AXI_BRESP = {C_NUM_SLAVE_SLOTS{si_bresp}};
    assign S_AXI_BUSER = {C_NUM_SLAVE_SLOTS{si_buser}};
    assign S_AXI_BID =   {C_NUM_SLAVE_SLOTS{mi_aid}};
    
    if (C_NUM_SLAVE_SLOTS>1) begin : gen_wmux
      // SI WVALID mux.
      generic_baseblocks_v2_1_0_mux_enc # 
        (
         .C_FAMILY      ("rtl"),
         .C_RATIO       (C_NUM_SLAVE_SLOTS),
         .C_SEL_WIDTH   (P_NUM_SLAVE_SLOTS_LOG),
         .C_DATA_WIDTH  (1)
        ) si_w_valid_mux_inst 
        (
         .S   (aa_grant_enc),
         .A   (S_AXI_WVALID),
         .O   (aa_wvalid),
         .OE  (w_transfer_en)
        ); 
      
      // SI W-channel payload mux
      generic_baseblocks_v2_1_0_mux_enc # 
        (
         .C_FAMILY      ("rtl"),
         .C_RATIO       (C_NUM_SLAVE_SLOTS),
         .C_SEL_WIDTH   (P_NUM_SLAVE_SLOTS_LOG),
         .C_DATA_WIDTH  (P_WMESG_WIDTH)
        ) si_w_payload_mux_inst 
        (
         .S   (aa_grant_enc),
         .A   (si_wmesg),
         .O   (mi_wmesg),
         .OE  (1'b1)
        ); 
        
      for (gen_si_slot=0; gen_si_slot<C_NUM_SLAVE_SLOTS; gen_si_slot=gen_si_slot+1) begin : gen_wmesg
        assign si_wmesg[gen_si_slot*P_WMESG_WIDTH+:P_WMESG_WIDTH] = {  // Concatenate from MSB to LSB
          ((C_AXI_PROTOCOL == P_AXI3) ? f_extend_ID(S_AXI_WID[gen_si_slot*C_AXI_ID_WIDTH+:C_AXI_ID_WIDTH], gen_si_slot) : 1'b0),
          S_AXI_WUSER[gen_si_slot*C_AXI_WUSER_WIDTH+:C_AXI_WUSER_WIDTH],
          S_AXI_WSTRB[gen_si_slot*C_AXI_DATA_WIDTH/8+:C_AXI_DATA_WIDTH/8],
          S_AXI_WDATA[gen_si_slot*C_AXI_DATA_WIDTH+:C_AXI_DATA_WIDTH],
          S_AXI_WLAST[gen_si_slot*1+:1]
        };
      end  // gen_wmesg
      
      assign mi_wlast = mi_wmesg[0];
      assign mi_wdata = mi_wmesg[1 +: C_AXI_DATA_WIDTH];
      assign mi_wstrb = mi_wmesg[1+C_AXI_DATA_WIDTH +: C_AXI_DATA_WIDTH/8];
      assign mi_wuser = mi_wmesg[1+C_AXI_DATA_WIDTH+C_AXI_DATA_WIDTH/8 +: C_AXI_WUSER_WIDTH];
      assign mi_wid =   mi_wmesg[1+C_AXI_DATA_WIDTH+C_AXI_DATA_WIDTH/8+C_AXI_WUSER_WIDTH +: P_AXI_WID_WIDTH];
    end else begin : gen_no_wmux
      assign aa_wvalid = w_transfer_en & S_AXI_WVALID;
      assign mi_wlast  = S_AXI_WLAST;
      assign mi_wdata  = S_AXI_WDATA;
      assign mi_wstrb  = S_AXI_WSTRB;
      assign mi_wuser  = S_AXI_WUSER;
      assign mi_wid =    S_AXI_WID;
    end  // gen_wmux
    
    // Receive RVALID from targeted MI.
    generic_baseblocks_v2_1_0_mux_enc # 
      (
       .C_FAMILY      ("rtl"),
       .C_RATIO       (P_NUM_MASTER_SLOTS_DE),
       .C_SEL_WIDTH   (P_NUM_MASTER_SLOTS_DE_LOG),
       .C_DATA_WIDTH  (1)
      ) mi_rvalid_mux_inst 
      (
       .S   (m_atarget_enc),
       .A   (mi_rvalid),
       .O   (aa_rvalid),
       .OE  (r_transfer_en)
      ); 
      
    // MI R-channel payload mux
    generic_baseblocks_v2_1_0_mux_enc # 
      (
       .C_FAMILY      ("rtl"),
       .C_RATIO       (P_NUM_MASTER_SLOTS_DE),
       .C_SEL_WIDTH   (P_NUM_MASTER_SLOTS_DE_LOG),
       .C_DATA_WIDTH  (P_RMESG_WIDTH)
      ) mi_rmesg_mux_inst 
      (
       .S   (m_atarget_enc),
       .A   (mi_rmesg),
       .O   (aa_rmesg),
       .OE  (1'b1)
      ); 
      
    axi_register_slice_v2_1_18_axic_register_slice #
      (
       .C_FAMILY (C_FAMILY),
       .C_DATA_WIDTH (P_RMESG_WIDTH),
       .C_REG_CONFIG (P_R_REG_CONFIG)
       )
      reg_slice_r
      (
       // System Signals
       .ACLK(ACLK),
       .ARESET(reset),

       // Slave side
       .S_PAYLOAD_DATA(aa_rmesg),
       .S_VALID(aa_rvalid),
       .S_READY(aa_rready),

       // Master side
       .M_PAYLOAD_DATA(sr_rmesg),
       .M_VALID(sr_rvalid),
       .M_READY(sr_rready)
       );

    assign mi_rvalid[0+:C_NUM_MASTER_SLOTS] = M_AXI_RVALID; 
    assign mi_rlast[0+:C_NUM_MASTER_SLOTS] = M_AXI_RLAST; 
    assign mi_rresp[0+:C_NUM_MASTER_SLOTS*2] = M_AXI_RRESP;
    assign mi_ruser[0+:C_NUM_MASTER_SLOTS*C_AXI_RUSER_WIDTH] = M_AXI_RUSER;
    assign mi_rdata[0+:C_NUM_MASTER_SLOTS*C_AXI_DATA_WIDTH] = M_AXI_RDATA;
    assign M_AXI_RREADY = mi_rready[0+:C_NUM_MASTER_SLOTS];
    
    for (gen_mi_slot=0; gen_mi_slot<P_NUM_MASTER_SLOTS_DE; gen_mi_slot=gen_mi_slot+1) begin : gen_rmesg
      assign mi_rmesg[gen_mi_slot*P_RMESG_WIDTH+:P_RMESG_WIDTH] = {  // Concatenate from MSB to LSB
        mi_ruser[gen_mi_slot*C_AXI_RUSER_WIDTH+:C_AXI_RUSER_WIDTH],
        mi_rdata[gen_mi_slot*C_AXI_DATA_WIDTH+:C_AXI_DATA_WIDTH],
        mi_rresp[gen_mi_slot*2+:2],
        mi_rlast[gen_mi_slot*1+:1]
      };
    end  // gen_rmesg
    
    assign si_rlast = sr_rmesg[0];
    assign si_rresp = sr_rmesg[1 +: 2];
    assign si_rdata = sr_rmesg[1+2 +: C_AXI_DATA_WIDTH];
    assign si_ruser = sr_rmesg[1+2+C_AXI_DATA_WIDTH +: C_AXI_RUSER_WIDTH];
      
    // Receive BVALID from targeted MI.
    generic_baseblocks_v2_1_0_mux_enc # 
      (
       .C_FAMILY      ("rtl"),
       .C_RATIO       (P_NUM_MASTER_SLOTS_DE),
       .C_SEL_WIDTH   (P_NUM_MASTER_SLOTS_DE_LOG),
       .C_DATA_WIDTH  (1)
      ) mi_bvalid_mux_inst 
      (
       .S   (m_atarget_enc),
       .A   (mi_bvalid),
       .O   (aa_bvalid),
       .OE  (b_transfer_en)
      ); 
      
    // MI B-channel payload mux
    generic_baseblocks_v2_1_0_mux_enc # 
      (
       .C_FAMILY      ("rtl"),
       .C_RATIO       (P_NUM_MASTER_SLOTS_DE),
       .C_SEL_WIDTH   (P_NUM_MASTER_SLOTS_DE_LOG),
       .C_DATA_WIDTH  (P_BMESG_WIDTH)
      ) mi_bmesg_mux_inst 
      (
       .S   (m_atarget_enc),
       .A   (mi_bmesg),
       .O   (si_bmesg),
       .OE  (1'b1)
      ); 
      
    assign mi_bvalid[0+:C_NUM_MASTER_SLOTS] = M_AXI_BVALID; 
    assign mi_bresp[0+:C_NUM_MASTER_SLOTS*2] = M_AXI_BRESP;
    assign mi_buser[0+:C_NUM_MASTER_SLOTS*C_AXI_BUSER_WIDTH] = M_AXI_BUSER;
    assign M_AXI_BREADY = mi_bready[0+:C_NUM_MASTER_SLOTS];
    
    for (gen_mi_slot=0; gen_mi_slot<P_NUM_MASTER_SLOTS_DE; gen_mi_slot=gen_mi_slot+1) begin : gen_bmesg
      assign mi_bmesg[gen_mi_slot*P_BMESG_WIDTH+:P_BMESG_WIDTH] = {  // Concatenate from MSB to LSB
        mi_buser[gen_mi_slot*C_AXI_BUSER_WIDTH+:C_AXI_BUSER_WIDTH],
        mi_bresp[gen_mi_slot*2+:2]
      };
    end  // gen_bmesg
    
    assign si_bresp = si_bmesg[0 +: 2];
    assign si_buser = si_bmesg[2 +: C_AXI_BUSER_WIDTH];
    
    if (C_DEBUG) begin : gen_debug_trans_seq
      // DEBUG WRITE TRANSACTION SEQUENCE COUNTER
      always @(posedge ACLK) begin
        if (reset) begin
          debug_aw_trans_seq_i <= 1;
        end else begin
          if (aa_awvalid && aa_awready) begin
            debug_aw_trans_seq_i <= debug_aw_trans_seq_i + 1;
          end
        end
      end
  
      // DEBUG READ TRANSACTION SEQUENCE COUNTER
      always @(posedge ACLK) begin
        if (reset) begin
          debug_ar_trans_seq_i <= 1;
        end else begin
          if (aa_arvalid && aa_arready) begin
            debug_ar_trans_seq_i <= debug_ar_trans_seq_i + 1;
          end
        end
      end
      
      // DEBUG WRITE BEAT COUNTER 
      always @(posedge ACLK) begin
        if (reset) begin
          debug_w_beat_cnt_i <= 0;
        end else if (aa_wready & aa_wvalid) begin
          if (mi_wlast) begin
            debug_w_beat_cnt_i <= 0;
          end else begin
            debug_w_beat_cnt_i <= debug_w_beat_cnt_i + 1;
          end
        end
      end  // Clocked process
    
      // DEBUG READ BEAT COUNTER 
      always @(posedge ACLK) begin
        if (reset) begin
          debug_r_beat_cnt_i <= 0;
        end else if (sr_rready & sr_rvalid) begin
          if (si_rlast) begin
            debug_r_beat_cnt_i <= 0;
          end else begin
            debug_r_beat_cnt_i <= debug_r_beat_cnt_i + 1;
          end
        end
      end  // Clocked process
    
    end  // gen_debug_trans_seq

    if (C_RANGE_CHECK) begin : gen_decerr
      // Highest MI-slot (index C_NUM_MASTER_SLOTS) is the error handler
      axi_crossbar_v2_1_19_decerr_slave #
        (
         .C_AXI_ID_WIDTH                 (1),
         .C_AXI_DATA_WIDTH               (C_AXI_DATA_WIDTH),
         .C_AXI_RUSER_WIDTH                (C_AXI_RUSER_WIDTH),
         .C_AXI_BUSER_WIDTH                (C_AXI_BUSER_WIDTH),
         .C_AXI_PROTOCOL                 (C_AXI_PROTOCOL),
         .C_RESP                         (P_DECERR) 
        )
        decerr_slave_inst
          (
           .S_AXI_ACLK (ACLK),
           .S_AXI_ARESET (reset),
           .S_AXI_AWID (1'b0),
           .S_AXI_AWVALID (mi_awvalid[C_NUM_MASTER_SLOTS]),
           .S_AXI_AWREADY (mi_awready[C_NUM_MASTER_SLOTS]),
           .S_AXI_WLAST (mi_wlast),
           .S_AXI_WVALID (mi_wvalid[C_NUM_MASTER_SLOTS]),
           .S_AXI_WREADY (mi_wready[C_NUM_MASTER_SLOTS]),
           .S_AXI_BID (),
           .S_AXI_BRESP (mi_bresp[C_NUM_MASTER_SLOTS*2+:2]),
           .S_AXI_BUSER (mi_buser[C_NUM_MASTER_SLOTS*C_AXI_BUSER_WIDTH+:C_AXI_BUSER_WIDTH]),
           .S_AXI_BVALID (mi_bvalid[C_NUM_MASTER_SLOTS]),
           .S_AXI_BREADY (mi_bready[C_NUM_MASTER_SLOTS]),
           .S_AXI_ARID (1'b0),
           .S_AXI_ARLEN (mi_alen),
           .S_AXI_ARVALID (mi_arvalid[C_NUM_MASTER_SLOTS]),
           .S_AXI_ARREADY (mi_arready[C_NUM_MASTER_SLOTS]),
           .S_AXI_RID (),
           .S_AXI_RDATA (mi_rdata[C_NUM_MASTER_SLOTS*C_AXI_DATA_WIDTH+:C_AXI_DATA_WIDTH]),
           .S_AXI_RRESP (mi_rresp[C_NUM_MASTER_SLOTS*2+:2]),
           .S_AXI_RUSER (mi_ruser[C_NUM_MASTER_SLOTS*C_AXI_RUSER_WIDTH+:C_AXI_RUSER_WIDTH]),
           .S_AXI_RLAST (mi_rlast[C_NUM_MASTER_SLOTS]),
           .S_AXI_RVALID (mi_rvalid[C_NUM_MASTER_SLOTS]),
           .S_AXI_RREADY (mi_rready[C_NUM_MASTER_SLOTS])
         );
    end  // gen_decerr

  endgenerate

endmodule

`default_nettype wire


// -- (c) Copyright 2009 - 2011 Xilinx, Inc. All rights reserved.
// --
// -- This file contains confidential and proprietary information
// -- of Xilinx, Inc. and is protected under U.S. and 
// -- international copyright and other intellectual property
// -- laws.
// --
// -- DISCLAIMER
// -- This disclaimer is not a license and does not grant any
// -- rights to the materials distributed herewith. Except as
// -- otherwise provided in a valid license issued to you by
// -- Xilinx, and to the maximum extent permitted by applicable
// -- law: (1) THESE MATERIALS ARE MADE AVAILABLE "AS IS" AND
// -- WITH ALL FAULTS, AND XILINX HEREBY DISCLAIMS ALL WARRANTIES
// -- AND CONDITIONS, EXPRESS, IMPLIED, OR STATUTORY, INCLUDING
// -- BUT NOT LIMITED TO WARRANTIES OF MERCHANTABILITY, NON-
// -- INFRINGEMENT, OR FITNESS FOR ANY PARTICULAR PURPOSE; and
// -- (2) Xilinx shall not be liable (whether in contract or tort,
// -- including negligence, or under any other theory of
// -- liability) for any loss or damage of any kind or nature
// -- related to, arising under or in connection with these
// -- materials, including for any direct, or any indirect,
// -- special, incidental, or consequential loss or damage
// -- (including loss of data, profits, goodwill, or any type of
// -- loss or damage suffered as a result of any action brought
// -- by a third party) even if such damage or loss was
// -- reasonably foreseeable or Xilinx had been advised of the
// -- possibility of the same.
// --
// -- CRITICAL APPLICATIONS
// -- Xilinx products are not designed or intended to be fail-
// -- safe, or for use in any application requiring fail-safe
// -- performance, such as life-support or safety devices or
// -- systems, Class III medical devices, nuclear facilities,
// -- applications related to the deployment of airbags, or any
// -- other applications that could lead to death, personal
// -- injury, or severe property or environmental damage
// -- (individually and collectively, "Critical
// -- Applications"). Customer assumes the sole risk and
// -- liability of any use of Xilinx products in Critical
// -- Applications, subject only to applicable laws and
// -- regulations governing limitations on product liability.
// --
// -- THIS COPYRIGHT NOTICE AND DISCLAIMER MUST BE RETAINED AS
// -- PART OF THIS FILE AT ALL TIMES.
//-----------------------------------------------------------------------------
//
// File name: crossbar.v
//
// Description: 
//   This module is a M-master to N-slave AXI axi_crossbar_v2_1_19_crossbar switch.
//   The interface of this module consists of a vectored slave and master interface
//     in which all slots are sized and synchronized to the native width and clock 
//     of the interconnect.
//   The SAMD axi_crossbar_v2_1_19_crossbar supports only AXI4 and AXI3 protocols.
//   All width, clock and protocol conversions are done outside this block, as are
//     any pipeline registers or data FIFOs.
//   This module contains all arbitration, decoders and channel multiplexing logic.
//     It also contains the diagnostic registers and control interface.
//
//-----------------------------------------------------------------------------
//
// Structure:
//    crossbar
//      si_transactor
//        addr_decoder
//          comparator_static
//        mux_enc
//        axic_srl_fifo
//        arbiter_resp
//      splitter
//      wdata_router
//        axic_reg_srl_fifo
//      wdata_mux
//        axic_reg_srl_fifo
//        mux_enc
//      addr_decoder
//        comparator_static
//      axic_srl_fifo
//      axi_register_slice
//      addr_arbiter
//        mux_enc
//      decerr_slave
//      
//-----------------------------------------------------------------------------
`timescale 1ps/1ps
`default_nettype none
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
