kangyuzhe666/ZYNQ7010-7020_AD9363/firmware/source project/pluto-7010clg400-user-ip/pluto/pluto.srcs/sources_1/bd/system/ipshared/cc23/hdl/axi_register_slice_v2_1_vl_rfs.v

//  (c) Copyright 2017 Xilinx, Inc. All rights reserved.
//
//  This file contains confidential and proprietary information
//  of Xilinx, Inc. and is protected under U.S. and
//  international copyright and other intellectual property
//  laws.
//
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
//  CRITICAL APPLICATIONS
//  Xilinx products are not designed or intended to be fail-
//  safe, or for use in any application requiring fail-safe
//  performance, such as life-support or safety devices or
//  systems, Class III medical devices, nuclear facilities,
//  applications related to the deployment of airbags, or any
//  other applications that could lead to death, personal
//  injury, or severe property or environmental damage
//  (individually and collectively, "Critical
//  Applications"). Customer assumes the sole risk and
//  liability of any use of Xilinx products in Critical
//  Applications, subject only to applicable laws and
//  regulations governing limitations on product liability.
//
//  THIS COPYRIGHT NOTICE AND DISCLAIMER MUST BE RETAINED AS
//  PART OF THIS FILE AT ALL TIMES. 
//-----------------------------------------------------------------------------

`timescale 1ps/1ps
`default_nettype none

module axi_register_slice_v2_1_18_tdm_sample (
///////////////////////////////////////////////////////////////////////////////
// Port Declarations
///////////////////////////////////////////////////////////////////////////////
  input  wire                    slow_clk,
  input  wire                    fast_clk,
  output wire                    sample_cycle
);

////////////////////////////////////////////////////////////////////////////////
// Wires/Reg declarations
////////////////////////////////////////////////////////////////////////////////
reg                slow_clk_div2 = 1'b0;
reg                posedge_finder_first;
reg                posedge_finder_second;
wire               first_edge;
wire               second_edge;
reg                sample_cycle_d;
(* shreg_extract = "no" *) reg                sample_cycle_r;


////////////////////////////////////////////////////////////////////////////////
// BEGIN RTL
////////////////////////////////////////////////////////////////////////////////
    always @(posedge slow_clk) begin 
      slow_clk_div2 <= ~slow_clk_div2;
    end

    // Find matching rising edges by clocking slow_clk_div2 onto faster clock
    always @(posedge fast_clk) begin 
      posedge_finder_first <= slow_clk_div2;
    end
    always @(posedge fast_clk) begin 
      posedge_finder_second <= ~slow_clk_div2;
    end

    assign first_edge = slow_clk_div2 & ~posedge_finder_first;
    assign second_edge = ~slow_clk_div2 & ~posedge_finder_second;

    always @(*) begin 
      sample_cycle_d = first_edge | second_edge;
    end
   
    always @(posedge fast_clk) begin 
      sample_cycle_r <= sample_cycle_d;
    end
    
    assign sample_cycle = sample_cycle_r;

endmodule // tdm_sample

`default_nettype wire


(* autopipeline_module="yes" *)
module axi_register_slice_v2_1_18_auto_slr #
  (
   parameter integer C_DATA_WIDTH = 32
   )
  (
   // System Signals
   input wire ACLK,
   input wire ARESETN,

   // Slave side
   input  wire [C_DATA_WIDTH-1:0] S_PAYLOAD_DATA,
   input  wire S_VALID,
   output wire S_READY,

   // Master side
   output wire [C_DATA_WIDTH-1:0] M_PAYLOAD_DATA,
   output wire M_VALID,
   input  wire M_READY
   );

    (* autopipeline_group="fwd",autopipeline_limit=24,autopipeline_include="resp" *) wire                    s_handshake_pipe;
                                                                                     reg                     m_handshake_q    = 1'b0;
    (* autopipeline_group="resp" *)                                                  wire                    m_ready_pipe;
                                                                                     reg                     s_ready_i        = 1'b0;
    (* autopipeline_group="fwd",autopipeline_limit=24,autopipeline_include="resp" *) reg  [C_DATA_WIDTH-1:0] s_payload_pipe;
                                                                                     reg  [C_DATA_WIDTH-1:0] m_payload_q;
    (* keep="true" *)                                                                reg  s_aclear = 1'b0;
    (* autopipeline_group="fwd",autopipeline_limit=24,autopipeline_include="resp" *) reg  s_areset_fwd   = 1'b0;
    (* autopipeline_group="resp" *)                                                  reg  s_areset_resp  = 1'b0;
    (* keep="true" *)                                                                reg  s_areset_resp2 = 1'b0;
    (* keep="true" *)                                                                reg  m_aclear = 1'b0;
    (* autopipeline_group="fwd",autopipeline_limit=24,autopipeline_include="resp" *) reg  m_areset_fwd   = 1'b0;
    (* autopipeline_group="resp" *)                                                  reg  m_areset_resp  = 1'b0;
    (* keep="true" *)                                                                reg  m_areset_resp2 = 1'b0;
    
    assign S_READY = s_ready_i;
    
  // Global Reset pipelining
  
    always @(posedge ACLK) begin
      s_aclear       <= ~ARESETN;
      s_areset_fwd   <= ~ARESETN; 
      s_areset_resp  <= s_areset_fwd;  // Auto-pipeline
      s_areset_resp2 <= s_areset_resp; // Auto-pipeline
    end
    
    always @(posedge ACLK) begin
      m_aclear       <= ~ARESETN;
      m_areset_fwd   <= ~ARESETN; 
      m_areset_resp  <= m_areset_fwd;  // Auto-pipeline
      m_areset_resp2 <= m_areset_resp; // Auto-pipeline
    end
    
  // Global Autopipeline registers
    
    always @(posedge ACLK) begin
      m_handshake_q <= s_handshake_pipe;
    end
    
    always @(posedge ACLK) begin
      s_ready_i <= m_ready_pipe;  // Auto-pipeline
    end
    
    always @(posedge ACLK) begin
      s_payload_pipe <= S_PAYLOAD_DATA;
      m_payload_q    <= s_payload_pipe;  // Auto-pipeline
    end
    
    FDCE #(
        .INIT(1'b0)
     ) s_handshake_asyncclear_inst (
        .Q   (s_handshake_pipe),
        .C   (ACLK), 
        .CE  (1'b1),
        .CLR (s_aclear),
        .D   (s_handshake_d)
     );
    
    FDCE #(
        .INIT(1'b0)
     ) m_ready_asyncclear_inst (
        .Q   (m_ready_pipe),
        .C   (ACLK), 
        .CE  (1'b1),
        .CLR (m_aclear),
        .D   (m_ready_d)
     );
    
  // Source-side submodule
    
    axi_register_slice_v2_1_18_auto_src 
      slr_auto_src
      (
       .ACLK             (ACLK),    
       .s_aclear         (s_aclear),
       .s_areset_resp2   (s_areset_resp2),  
       .S_VALID          (S_VALID),  
       .s_ready_i        (s_ready_i), 
       .s_handshake_d    (s_handshake_d)
      );
    
  // Destination-side submodule
    
    axi_register_slice_v2_1_18_auto_dest #
      (
       .C_DATA_WIDTH (C_DATA_WIDTH)
      )
      slr_auto_dest
      (
       .ACLK           (ACLK),    
       .m_aclear       (m_aclear),
       .m_areset_resp2 (m_areset_resp2),  
       .M_READY        (M_READY), 
       .m_handshake_q  (m_handshake_q),
       .m_ready_d      (m_ready_d),  
       .M_VALID        (M_VALID),  
       .m_payload_q    (m_payload_q),  
       .M_PAYLOAD_DATA (M_PAYLOAD_DATA)
      );
    
endmodule  // auto_slr

module axi_register_slice_v2_1_18_auto_src 
  (
   input  wire ACLK,
   input  wire s_aclear,
   input  wire s_areset_resp2,
   input  wire S_VALID,
   input  wire s_ready_i,
   output wire s_handshake_d
   );
    
    (* keep="true" *) reg  s_areset_resp3 = 1'b0;
    wire s_aresetn_d;
    wire s_aresetn_q;
    
    assign s_aresetn_d = (~s_areset_resp2 & s_areset_resp3) | s_aresetn_q;
    assign s_handshake_d = S_VALID & s_ready_i & s_aresetn_q;
    
    always @(posedge ACLK) begin
      s_areset_resp3 <= s_areset_resp2;
    end
    
    // Assert s_aresetn_q asynchronously on leading edge of s_aclear; De-assert synchronously on trailing edge of s_areset_resp2.
    FDCE #(
        .INIT(1'b0)
     ) s_reset_asyncclear_inst (
        .Q   (s_aresetn_q),
        .C   (ACLK), 
        .CE  (1'b1),
        .CLR (s_aclear),
        .D   (s_aresetn_d)
     );
    
endmodule  // auto_src

module axi_register_slice_v2_1_18_auto_dest #
  (
   parameter integer C_DATA_WIDTH = 32
   )
  (
   input  wire ACLK,
   input  wire m_aclear,
   input  wire m_areset_resp2,
   input  wire M_READY,
   input  wire m_handshake_q,
   output wire m_ready_d,
   output wire M_VALID,
   input  wire [C_DATA_WIDTH-1:0] m_payload_q,
   output wire [C_DATA_WIDTH-1:0] M_PAYLOAD_DATA
   );
    
    (* keep="true" *) reg  m_areset_resp3 = 1'b0;
    wire m_aresetn_d;
    wire m_aresetn_q;
    wire m_valid_i;
    wire pop;
    wire push;
    
    assign M_VALID = m_valid_i;
    assign m_aresetn_d = (~m_areset_resp2 & m_areset_resp3) | m_aresetn_q;
    assign m_ready_d     = (M_READY | ~m_valid_i) & m_aresetn_q;
    assign pop     = M_READY & m_valid_i;
    
    always @(posedge ACLK) begin
      m_areset_resp3 <= m_areset_resp2;
    end
    
    // Assert m_aresetn_q asynchronously on leading edge of m_aclear; De-assert synchronously on trailing edge of m_areset_resp2.
    FDCE #(
        .INIT(1'b0)
     ) m_reset_asyncclear_inst (
        .Q   (m_aresetn_q),
        .C   (ACLK), 
        .CE  (1'b1),
        .CLR (m_aclear),
        .D   (m_aresetn_d)
     );
    
    axi_register_slice_v2_1_18_axic_reg_srl_fifo #
      (
       .C_FIFO_WIDTH (C_DATA_WIDTH), 
       .C_FIFO_SIZE  (5)  
      )
      srl_fifo_0
      (
       .aclk    (ACLK),    
       .areset  (~m_aresetn_q),
       .aclear  (m_aclear),  
       .s_mesg  (m_payload_q),  
       .s_valid (m_handshake_q), 
       .m_mesg  (M_PAYLOAD_DATA),  
       .m_valid (m_valid_i), 
       .m_ready (pop)
      );
    
endmodule  // auto_dest


// -- (c) Copyright 2010 - 2017 Xilinx, Inc. All rights reserved.
// --
// -- This file contains confidential and proprietary information
// -- of Xilinx, Inc. and is protected under U.S. and 
// -- international copyright and other intellectual property
// -- laws.
// --
// -- DISCLAIMER
// -- This disclaimer is not a license and does not grant any
// -- rights to the materials distributed herewith. Except as
// -- otherwise provided in a valid license issued to you by
// -- Xilinx, and to the maximum extent permitted by applicable
// -- law: (1) THESE MATERIALS ARE MADE AVAILABLE "AS IS" AND
// -- WITH ALL FAULTS, AND XILINX HEREBY DISCLAIMS ALL WARRANTIES
// -- AND CONDITIONS, EXPRESS, IMPLIED, OR STATUTORY, INCLUDING
// -- BUT NOT LIMITED TO WARRANTIES OF MERCHANTABILITY, NON-
// -- INFRINGEMENT, OR FITNESS FOR ANY PARTICULAR PURPOSE; and
// -- (2) Xilinx shall not be liable (whether in contract or tort,
// -- including negligence, or under any other theory of
// -- liability) for any loss or damage of any kind or nature
// -- related to, arising under or in connection with these
// -- materials, including for any direct, or any indirect,
// -- special, incidental, or consequential loss or damage
// -- (including loss of data, profits, goodwill, or any type of
// -- loss or damage suffered as a result of any action brought
// -- by a third party) even if such damage or loss was
// -- reasonably foreseeable or Xilinx had been advised of the
// -- possibility of the same.
// --
// -- CRITICAL APPLICATIONS
// -- Xilinx products are not designed or intended to be fail-
// -- safe, or for use in any application requiring fail-safe
// -- performance, such as life-support or safety devices or
// -- systems, Class III medical devices, nuclear facilities,
// -- applications related to the deployment of airbags, or any
// -- other applications that could lead to death, personal
// -- injury, or severe property or environmental damage
// -- (individually and collectively, "Critical
// -- Applications"). Customer assumes the sole risk and
// -- liability of any use of Xilinx products in Critical
// -- Applications, subject only to applicable laws and
// -- regulations governing limitations on product liability.
// --
// -- THIS COPYRIGHT NOTICE AND DISCLAIMER MUST BE RETAINED AS
// -- PART OF THIS FILE AT ALL TIMES.
//-----------------------------------------------------------------------------
//
// Register Slice
//   Generic single-channel AXI pipeline register on forward and/or reverse signal path
//
// Verilog-standard:  Verilog 2001
//--------------------------------------------------------------------------
//
// Structure:
//   axic_register_slice
//
//--------------------------------------------------------------------------

`timescale 1ps/1ps
(* DowngradeIPIdentifiedWarnings="yes" *) 
module axi_register_slice_v2_1_18_srl_rtl #
  (
   parameter         C_A_WIDTH = 2          // Address Width (>= 1)
   )
  (
   input  wire                 clk, // Clock
   input  wire [C_A_WIDTH-1:0] a,   // Address
   input  wire                 ce,  // Clock Enable
   input  wire                 d,   // Input Data
   output wire                 q    // Output Data
   );

  localparam integer P_SRLDEPTH = 2**C_A_WIDTH;
  
    reg [P_SRLDEPTH-1:0] shift_reg = {P_SRLDEPTH{1'b0}};
    always @(posedge clk)
      if (ce)
        shift_reg <= {shift_reg[P_SRLDEPTH-2:0], d};
    assign q = shift_reg[a];

endmodule  // srl_rtl

`timescale 1ps/1ps
(* DowngradeIPIdentifiedWarnings="yes" *) 
module axi_register_slice_v2_1_18_axic_register_slice #
  (
   parameter C_FAMILY     = "virtex6",
   parameter C_DATA_WIDTH = 32,
   parameter C_REG_CONFIG = 32'h00000000
   // C_REG_CONFIG:
   //   0 => BYPASS    = The channel is just wired through the module.
   //   1 => FWD_REV   = Both FWD and REV (fully-registered)
   //   2 => FWD       = The master VALID and payload signals are registrated. 
   //   3 => REV       = The slave ready signal is registrated
   //   4 => RESERVED (all outputs driven to 0).
   //   5 => RESERVED (all outputs driven to 0).
   //   6 => INPUTS    = Slave and Master side inputs are registrated.
   //   7 => LIGHT_WT  = 1-stage pipeline register with bubble cycle, both FWD and REV pipelining
   //   9 => SI/MI_REG = Source side completely registered (including S_VALID input)
   )
  (
   // System Signals
   input wire ACLK,
   input wire ARESET,

   // Slave side
   input  wire [C_DATA_WIDTH-1:0] S_PAYLOAD_DATA,
   input  wire S_VALID,
   output wire S_READY,

   // Master side
   output  wire [C_DATA_WIDTH-1:0] M_PAYLOAD_DATA,
   output wire M_VALID,
   input  wire M_READY
   );

  (* use_clock_enable = "yes" *)

  generate
  ////////////////////////////////////////////////////////////////////
  //
  // C_REG_CONFIG = 0
  // Bypass mode
  //
  ////////////////////////////////////////////////////////////////////
    if (C_REG_CONFIG == 32'h00000000) begin
      assign M_PAYLOAD_DATA = S_PAYLOAD_DATA;
      assign M_VALID        = S_VALID;
      assign S_READY        = M_READY;      
    end
    
  ////////////////////////////////////////////////////////////////////
  //
  // C_REG_CONFIG = 9
  // Source (SI) interface completely registered
  //
  ////////////////////////////////////////////////////////////////////
      
    else if (C_REG_CONFIG == 32'h00000009) begin
      reg [C_DATA_WIDTH-1:0] s_payload_d;
      wire [C_DATA_WIDTH-1:0] srl_out;
      reg s_ready_i = 1'b0;
      reg m_valid_i = 1'b0;
      reg payld_sel;
      reg push;
      reg pop;
      wire s_handshake_d;
      reg s_valid_d;
      reg s_ready_d = 1'b0;
      reg s_ready_reg = 1'b0;
      reg [2:0] fifoaddr = 3'b110;
      
      reg areset_d = 1'b0;
      always @(posedge ACLK) begin
        areset_d <= ARESET;
      end
      
      assign s_handshake_d = s_valid_d & s_ready_d;

      always @ * begin
        case (fifoaddr)
          3'b111: begin  // EMPTY: No payload in SRL; pre-assert m_ready
            s_ready_i = 1'b1;
            payld_sel = 1'b0;
            pop = 1'b0;
            case ({s_handshake_d, M_READY}) 
              2'b00, 2'b01: begin  // Idle
                m_valid_i = 1'b0;
                push = 1'b0;
              end
              2'b10: begin  // Payload received
                m_valid_i = 1'b1;
                push = 1'b1;
              end
              2'b11: begin  // Payload received and read out combinatorially
                m_valid_i = 1'b1;
                push = 1'b0;
              end
            endcase
          end

          3'b000: begin  // 1 payload item in SRL
            m_valid_i = 1'b1;
            payld_sel = 1'b1;
            case ({s_handshake_d, M_READY}) 
              2'b00: begin  // Idle
                s_ready_i = 1'b1;
                push = 1'b0;
                pop = 1'b0;
              end
              2'b01: begin  // Pop
                s_ready_i = 1'b1;
                push = 1'b0;
                pop = 1'b1;
              end
              2'b10: begin  // Push
                s_ready_i = 1'b0;  // Doesn't de-assert on SI until next cycle
                push = 1'b1;
                pop = 1'b0;
              end
              2'b11: begin  // Push and Pop
                s_ready_i = 1'b1;
                push = 1'b1;
                pop = 1'b1;
              end
            endcase
          end

          3'b001: begin  // 2 payload items in SRL
            m_valid_i = 1'b1;
            payld_sel = 1'b1;
            case ({s_handshake_d, M_READY}) 
              2'b00: begin  // Idle
                s_ready_i = 1'b0;
                push = 1'b0;
                pop = 1'b0;
              end
              2'b01: begin  // Pop
                s_ready_i = 1'b1;
                push = 1'b0;
                pop = 1'b1;
              end
              2'b10: begin  // Push (Handshake completes on SI while pushing 2nd item into SRL)
                s_ready_i = 1'b0;
                push = 1'b1;
                pop = 1'b0;
              end
              2'b11: begin  // Push and Pop
                s_ready_i = 1'b0;
                push = 1'b1;
                pop = 1'b1;
              end
            endcase
          end

          3'b010: begin  // 3 payload items in SRL
            m_valid_i = 1'b1;
            s_ready_i = 1'b0;
            payld_sel = 1'b1;
            push = 1'b0;
            if (M_READY) begin  // Handshake cannot complete on SI
              pop = 1'b1;
            end else begin
              pop = 1'b0;
            end
          end

          default: begin  // RESET state (fifoaddr = 3'b110)
            m_valid_i = 1'b0;
            s_ready_i = 1'b0;
            payld_sel = 1'b0;
            push = 1'b1;  // Advance to Empty state
            pop = 1'b0;
          end  // RESET
        endcase
      end

      always @(posedge ACLK) begin
        if (areset_d) begin
          fifoaddr <= 3'b110;
          s_ready_reg <= 1'b0;
          s_ready_d <= 1'b0;
        end else begin
          s_ready_reg <= s_ready_i;
          s_ready_d <= s_ready_reg;
          if (push & ~pop) begin
            fifoaddr <= fifoaddr + 1;
          end else if (~push & pop) begin
            fifoaddr <= fifoaddr - 1;
          end
        end
      end

      always @(posedge ACLK) begin
        s_valid_d <= S_VALID;
        s_payload_d <= S_PAYLOAD_DATA;
      end

      assign S_READY = s_ready_reg;
      assign M_VALID = m_valid_i;
      assign M_PAYLOAD_DATA = payld_sel ? srl_out : s_payload_d;

    //---------------------------------------------------------------------------
    // Instantiate SRLs
    //---------------------------------------------------------------------------
      genvar i;
      for (i=0;i<C_DATA_WIDTH;i=i+1) begin : gen_srls
        axi_register_slice_v2_1_18_srl_rtl #
          (
           .C_A_WIDTH (2)
          )
          srl_nx1
          (
           .clk (ACLK),
           .a   (fifoaddr[1:0]),
           .ce  (push),
           .d   (s_payload_d[i]),
           .q   (srl_out[i])
          );
      end      
    end 
        
        
  ////////////////////////////////////////////////////////////////////
  //
  // C_REG_CONFIG = 1 (or 8)
  // Both FWD and REV mode
  //
  ////////////////////////////////////////////////////////////////////
    else if ((C_REG_CONFIG == 32'h00000001) || (C_REG_CONFIG == 32'h00000008)) begin
      reg [C_DATA_WIDTH-1:0] m_payload_i;
      reg [C_DATA_WIDTH-1:0] skid_buffer;
      reg                    s_ready_i = 1'b0; 
      reg                    m_valid_i = 1'b0;

      assign S_READY = s_ready_i;
      assign M_VALID = m_valid_i;
      assign M_PAYLOAD_DATA = m_payload_i;

      reg [1:0] aresetn_d = 2'b00; // Reset delay shifter
      always @(posedge ACLK) begin
        if (ARESET) begin
          aresetn_d <= 2'b00;
        end else begin
          aresetn_d <= {aresetn_d[0], ~ARESET};
        end
      end
      
      always @(posedge ACLK) begin
        if (~aresetn_d[0]) begin
          s_ready_i <= 1'b0;
        end else begin
          s_ready_i <= M_READY | ~m_valid_i | (s_ready_i & ~S_VALID);
        end
        
        if (~aresetn_d[1]) begin
          m_valid_i <= 1'b0;
        end else begin
          m_valid_i <= S_VALID | ~s_ready_i | (m_valid_i & ~M_READY);
        end
        
        if (M_READY | ~m_valid_i) begin
          m_payload_i <= s_ready_i ? S_PAYLOAD_DATA : skid_buffer;
        end
        
        if (s_ready_i) begin
          skid_buffer <= S_PAYLOAD_DATA;
        end
      end

    end // if (C_REG_CONFIG == 1)
    
    
  ////////////////////////////////////////////////////////////////////
  //
  // C_REG_CONFIG = 2
  // Only FWD mode
  //
  ////////////////////////////////////////////////////////////////////
    else if (C_REG_CONFIG == 32'h00000002)
    begin
      reg [C_DATA_WIDTH-1:0] storage_data;
      wire                   s_ready_i; //local signal of output
      reg                    m_valid_i = 1'b0; //local signal of output

      // assign local signal to its output signal
      assign S_READY = s_ready_i;
      assign M_VALID = m_valid_i;

      reg aresetn_d = 1'b0; // Reset delay register
      always @(posedge ACLK) begin
        if (ARESET) begin
          aresetn_d <= 1'b0;
        end else begin
          aresetn_d <= ~ARESET;
        end
      end
      
      // Save payload data whenever we have a transaction on the slave side
      always @(posedge ACLK) 
      begin
        if (S_VALID & s_ready_i)
          storage_data <= S_PAYLOAD_DATA;
      end

      assign M_PAYLOAD_DATA = storage_data;
      
      // M_Valid set to high when we have a completed transfer on slave side
      // Is removed on a M_READY except if we have a new transfer on the slave side
      always @(posedge ACLK) 
      begin
        if (~aresetn_d) 
          m_valid_i <= 1'b0;
        else
          if (S_VALID) // Always set m_valid_i when slave side is valid
            m_valid_i <= 1'b1;
          else
            if (M_READY) // Clear (or keep) when no slave side is valid but master side is ready
              m_valid_i <= 1'b0;
      end // always @ (posedge ACLK)
      
      // Slave Ready is either when Master side drives M_Ready or we have space in our storage data
      assign s_ready_i = (M_READY | ~m_valid_i) & aresetn_d;

    end // if (C_REG_CONFIG == 2)
  ////////////////////////////////////////////////////////////////////
  //
  // C_REG_CONFIG = 3
  // Only REV mode
  //
  ////////////////////////////////////////////////////////////////////
    else if (C_REG_CONFIG == 32'h00000003)
    begin
      reg [C_DATA_WIDTH-1:0] storage_data;
      reg                    s_ready_i = 1'b0; //local signal of output
      reg                    has_valid_storage_i;
      reg                    has_valid_storage;

      reg [1:0] aresetn_d = 2'b00; // Reset delay register
      always @(posedge ACLK) begin
        if (ARESET) begin
          aresetn_d <= 2'b00;
        end else begin
          aresetn_d <= {aresetn_d[0], ~ARESET};
        end
      end
      
      // Save payload data whenever we have a transaction on the slave side
      always @(posedge ACLK) 
      begin
        if (S_VALID & s_ready_i)
          storage_data <= S_PAYLOAD_DATA;
      end

      assign M_PAYLOAD_DATA = has_valid_storage?storage_data:S_PAYLOAD_DATA;

      // Need to determine when we need to save a payload
      // Need a combinatorial signals since it will also effect S_READY
      always @ *
      begin
        // Set the value if we have a slave transaction but master side is not ready
        if (S_VALID & s_ready_i & ~M_READY)
          has_valid_storage_i = 1'b1;
        
        // Clear the value if it's set and Master side completes the transaction but we don't have a new slave side 
        // transaction 
        else if ( (has_valid_storage == 1) && (M_READY == 1) && ( (S_VALID == 0) || (s_ready_i == 0)))
          has_valid_storage_i = 1'b0;
        else
          has_valid_storage_i = has_valid_storage;
      end // always @ *

      always @(posedge ACLK) 
      begin
        if (~aresetn_d[0]) 
          has_valid_storage <= 1'b0;
        else
          has_valid_storage <= has_valid_storage_i;
      end

      // S_READY is either clocked M_READY or that we have room in local storage
      always @(posedge ACLK) 
      begin
        if (~aresetn_d[0]) 
          s_ready_i <= 1'b0;
        else
          s_ready_i <= M_READY | ~has_valid_storage_i;
      end

      // assign local signal to its output signal
      assign S_READY = s_ready_i;

      // M_READY is either combinatorial S_READY or that we have valid data in local storage
      assign M_VALID = (S_VALID | has_valid_storage) & aresetn_d[1];
      
    end // if (C_REG_CONFIG == 3)
    
  ////////////////////////////////////////////////////////////////////
  //
  // C_REG_CONFIG = 4 or 5 is NO LONGER SUPPORTED
  //
  ////////////////////////////////////////////////////////////////////
    else if ((C_REG_CONFIG == 32'h00000004) || (C_REG_CONFIG == 32'h00000005))
    begin
// synthesis translate_off
      initial begin  
        $display ("ERROR: For axi_register_slice, C_REG_CONFIG = 4 or 5 is RESERVED.");
      end
// synthesis translate_on
      assign M_PAYLOAD_DATA = 0;
      assign M_VALID        = 1'b0;
      assign S_READY        = 1'b0;    
    end  

  ////////////////////////////////////////////////////////////////////
  //
  // C_REG_CONFIG = 6
  // INPUTS mode
  //
  ////////////////////////////////////////////////////////////////////
    else if (C_REG_CONFIG == 32'h00000006)
    begin
      localparam [1:0] 
        ZERO = 2'b00,
        ONE  = 2'b01,
        TWO  = 2'b11;
      reg [1:0] state = ZERO;
      reg [1:0] next_state;

      reg [C_DATA_WIDTH-1:0] storage_data1;
      reg [C_DATA_WIDTH-1:0] storage_data2;
      reg                    s_valid_d = 1'b0;
      reg                    s_ready_d = 1'b0;
      reg                    m_ready_d = 1'b0;
      reg                    m_valid_d = 1'b0;
      reg                    load_s2;
      reg                    sel_s2;
      wire                   new_access;
      wire                   access_done;
      wire                   s_ready_i; //local signal of output
      reg                    s_ready_ii;
      reg                    m_valid_i; //local signal of output
      
      reg [1:0] aresetn_d = 2'b00; // Reset delay register
      always @(posedge ACLK) begin
        if (ARESET) begin
          aresetn_d <= 2'b00;
        end else begin
          aresetn_d <= {aresetn_d[0], ~ARESET};
        end
      end
      
      // assign local signal to its output signal
      assign S_READY = s_ready_i;
      assign M_VALID = m_valid_i;
      assign s_ready_i = s_ready_ii & aresetn_d[1];

      // Registrate input control signals
      always @(posedge ACLK) 
      begin
        if (~aresetn_d[0]) begin          
          s_valid_d <= 1'b0;
          s_ready_d <= 1'b0;
          m_ready_d <= 1'b0;
        end else begin
          s_valid_d <= S_VALID;
          s_ready_d <= s_ready_i;
          m_ready_d <= M_READY;
        end
      end // always @ (posedge ACLK)

      // Load storage1 with slave side payload data when slave side ready is high
      always @(posedge ACLK) 
      begin
        if (s_ready_i)
          storage_data1 <= S_PAYLOAD_DATA;          
      end

      // Load storage2 with storage data 
      always @(posedge ACLK) 
      begin
        if (load_s2)
          storage_data2 <= storage_data1;
      end

      always @(posedge ACLK) 
      begin
        if (~aresetn_d[0]) 
          m_valid_d <= 1'b0;
        else 
          m_valid_d <= m_valid_i;
      end

      // Local help signals
      assign new_access  = s_ready_d & s_valid_d;
      assign access_done = m_ready_d & m_valid_d;


      // State Machine for handling output signals
      always @*
      begin
        next_state = state; // Stay in the same state unless we need to move to another state
        load_s2   = 0;
        sel_s2    = 0;
        m_valid_i = 0;
        s_ready_ii = 0;
        case (state)
            // No transaction stored locally
            ZERO: begin
              load_s2   = 0;
              sel_s2    = 0;
              m_valid_i = 0;
              s_ready_ii = 1;
              if (new_access) begin
                next_state = ONE; // Got one so move to ONE
                load_s2   = 1;
                m_valid_i = 0;
              end
              else begin
                next_state = next_state;
                load_s2   = load_s2;
                m_valid_i = m_valid_i;
              end

            end // case: ZERO

            // One transaction stored locally
            ONE: begin
              load_s2   = 0;
              sel_s2    = 1;
              m_valid_i = 1;
              s_ready_ii = 1;
              if (~new_access & access_done) begin
                next_state = ZERO; // Read out one so move to ZERO
                m_valid_i = 0;                      
              end
              else if (new_access & ~access_done) begin
                next_state = TWO;  // Got another one so move to TWO
                s_ready_ii = 0;
              end
              else if (new_access & access_done) begin
                load_s2   = 1;
                sel_s2    = 0;
              end
              else begin
                load_s2   = load_s2;
                sel_s2    = sel_s2;
              end


            end // case: ONE

            // TWO transaction stored locally
            TWO: begin
              load_s2   = 0;
              sel_s2    = 1;
              m_valid_i = 1;
              s_ready_ii = 0;
              if (access_done) begin 
                next_state = ONE; // Read out one so move to ONE
                s_ready_ii  = 1;
                load_s2    = 1;
                sel_s2     = 0;
              end
              else begin
                next_state = next_state;
                s_ready_ii  = s_ready_ii;
                load_s2    = load_s2;
                sel_s2     = sel_s2;
              end
            end // case: TWO
        endcase // case (state)
      end // always @ *


      // State Machine for handling output signals
      always @(posedge ACLK) 
      begin
        if (~aresetn_d[0]) 
          state <= ZERO;
        else
          state <= next_state; // Stay in the same state unless we need to move to another state
      end
      
      // Master Payload mux
      assign M_PAYLOAD_DATA = sel_s2?storage_data2:storage_data1;

    end // if (C_REG_CONFIG == 6)
  ////////////////////////////////////////////////////////////////////
  //
  // C_REG_CONFIG = 7
  // Light-weight mode.
  // 1-stage pipeline register with bubble cycle, both FWD and REV pipelining
  // Operates same as 1-deep FIFO
  //
  ////////////////////////////////////////////////////////////////////
    else if (C_REG_CONFIG == 32'h00000007) begin
      reg [C_DATA_WIDTH-1:0] m_payload_i;
      reg                    s_ready_i = 1'b0; 
      reg                    m_valid_i = 1'b0;

      assign S_READY = s_ready_i;
      assign M_VALID = m_valid_i;
      assign M_PAYLOAD_DATA = m_payload_i;

      reg [1:0] aresetn_d = 2'b00; // Reset delay shifter
      always @(posedge ACLK) begin
        if (ARESET) begin
          aresetn_d <= 2'b00;
        end else begin
          aresetn_d <= {aresetn_d[0], ~ARESET};
        end
      end
      
      always @(posedge ACLK) begin
        if (~aresetn_d[0]) begin
          s_ready_i <= 1'b0;
        end else if (~aresetn_d[1]) begin
          s_ready_i <= 1'b1;
        end else begin
          s_ready_i <= m_valid_i ? M_READY : ~S_VALID;
        end
        
        if (~aresetn_d[1]) begin
          m_valid_i <= 1'b0;
        end else begin
          m_valid_i <= s_ready_i ? S_VALID : ~M_READY;
        end
        
        if (~m_valid_i) begin
          m_payload_i <= S_PAYLOAD_DATA;
        end
      end
      
    end // if (C_REG_CONFIG == 7)
    
    else begin : default_case
      // Passthrough
      assign M_PAYLOAD_DATA = S_PAYLOAD_DATA;
      assign M_VALID        = S_VALID;
      assign S_READY        = M_READY;      
    end

  endgenerate
endmodule // axic_register_slice


// -- (c) Copyright 2017 Xilinx, Inc. All rights reserved.
// --
// -- This file contains confidential and proprietary information
// -- of Xilinx, Inc. and is protected under U.S. and 
// -- international copyright and other intellectual property
// -- laws.
// --
// -- DISCLAIMER
// -- This disclaimer is not a license and does not grant any
// -- rights to the materials distributed herewith. Except as
// -- otherwise provided in a valid license issued to you by
// -- Xilinx, and to the maximum extent permitted by applicable
// -- law: (1) THESE MATERIALS ARE MADE AVAILABLE "AS IS" AND
// -- WITH ALL FAULTS, AND XILINX HEREBY DISCLAIMS ALL WARRANTIES
// -- AND CONDITIONS, EXPRESS, IMPLIED, OR STATUTORY, INCLUDING
// -- BUT NOT LIMITED TO WARRANTIES OF MERCHANTABILITY, NON-
// -- INFRINGEMENT, OR FITNESS FOR ANY PARTICULAR PURPOSE; and
// -- (2) Xilinx shall not be liable (whether in contract or tort,
// -- including negligence, or under any other theory of
// -- liability) for any loss or damage of any kind or nature
// -- related to, arising under or in connection with these
// -- materials, including for any direct, or any indirect,
// -- special, incidental, or consequential loss or damage
// -- (including loss of data, profits, goodwill, or any type of
// -- loss or damage suffered as a result of any action brought
// -- by a third party) even if such damage or loss was
// -- reasonably foreseeable or Xilinx had been advised of the
// -- possibility of the same.
// --
// -- CRITICAL APPLICATIONS
// -- Xilinx products are not designed or intended to be fail-
// -- safe, or for use in any application requiring fail-safe
// -- performance, such as life-support or safety devices or
// -- systems, Class III medical devices, nuclear facilities,
// -- applications related to the deployment of airbags, or any
// -- other applications that could lead to death, personal
// -- injury, or severe property or environmental damage
// -- (individually and collectively, "Critical
// -- Applications"). Customer assumes the sole risk and
// -- liability of any use of Xilinx products in Critical
// -- Applications, subject only to applicable laws and
// -- regulations governing limitations on product liability.
// --
// -- THIS COPYRIGHT NOTICE AND DISCLAIMER MUST BE RETAINED AS
// -- PART OF THIS FILE AT ALL TIMES.
//-----------------------------------------------------------------------------
//
// Register Slice
//   Generic single-channel AXI pipeline register on forward and/or reverse signal path
//
// Verilog-standard:  Verilog 2001
//--------------------------------------------------------------------------
//
// Structure:
//   axic_register_slice_slr
//
//--------------------------------------------------------------------------

`timescale 1ps/1ps
(* DowngradeIPIdentifiedWarnings="yes" *) 
module axi_register_slice_v2_1_18_multi_slr #
  (
   parameter C_FAMILY     = "virtex6",
   parameter integer C_DATA_WIDTH = 32,
   parameter integer C_CHANNEL = 0,  // 0=Forward, 1=Response
   parameter integer C_NUM_SLR_CROSSINGS = 0,
   parameter integer C_PIPELINES_MASTER = 0,
   parameter integer C_PIPELINES_SLAVE = 0,
   parameter integer C_PIPELINES_MIDDLE = 0
   )
  (
   // System Signals
   input wire ACLK,
   input wire ARESETN,

   // Slave side
   input  wire [C_DATA_WIDTH-1:0] S_PAYLOAD_DATA,
   input  wire S_VALID,
   output wire S_READY,

   // Master side
   output  wire [C_DATA_WIDTH-1:0] M_PAYLOAD_DATA,
   output wire M_VALID,
   input  wire M_READY
   );
   
  localparam integer P_FORWARD = 0;
  localparam integer P_RESPONSE = 1;
  localparam integer P_REG_CONFIG = 15;
  localparam integer P_FWD_MIDDLE_LATENCY = C_PIPELINES_MASTER + 2;
  localparam integer P_RESP_MIDDLE_LATENCY = C_PIPELINES_SLAVE + 2;
  localparam integer P_FWD_MIDDLE2_LATENCY = C_PIPELINES_MASTER + 2 + C_PIPELINES_MIDDLE + 2;
  localparam integer P_RESP_MIDDLE2_LATENCY = C_PIPELINES_SLAVE + 2 + C_PIPELINES_MIDDLE + 2;
  localparam integer P_FWD_DEST_LATENCY = C_PIPELINES_MASTER + 2 + ((C_NUM_SLR_CROSSINGS>1) ? (C_PIPELINES_MIDDLE+2) : 0) + ((C_NUM_SLR_CROSSINGS==3) ? (C_PIPELINES_MIDDLE+2) : 0);
  localparam integer P_RESP_DEST_LATENCY = C_PIPELINES_SLAVE + 2 + ((C_NUM_SLR_CROSSINGS>1) ? (C_PIPELINES_MIDDLE+2) : 0) + ((C_NUM_SLR_CROSSINGS==3) ? (C_PIPELINES_MIDDLE+2) : 0);

  generate
  
  if (C_NUM_SLR_CROSSINGS==0) begin : single_slr
    
    axi_register_slice_v2_1_18_single_slr # (
      .C_FAMILY     ( C_FAMILY              ) ,
      .C_DATA_WIDTH ( C_DATA_WIDTH ) ,
      .C_PIPELINES  (C_PIPELINES_MASTER) 
    )
    slr_master (
      .ACLK           (ACLK),
      .ARESETN         (ARESETN),
      .S_PAYLOAD_DATA (S_PAYLOAD_DATA),
      .S_VALID        (S_VALID),
      .S_READY        (S_READY),
      .M_PAYLOAD_DATA (M_PAYLOAD_DATA),
      .M_VALID        (M_VALID),
      .M_READY        (M_READY)
    );
    
  end else if (C_NUM_SLR_CROSSINGS==1) begin : dual_slr
    
    wire [C_DATA_WIDTH-1:0] src_payload;
    wire src_handshake;
    wire src_reset;
    wire src_ready;
    wire dummy_reset;
        
    if (C_CHANNEL==P_FORWARD) begin : fwd
      axi_register_slice_v2_1_18_source_region_slr # (
        .C_FAMILY     ( C_FAMILY ) ,
        .C_DATA_WIDTH ( C_DATA_WIDTH ) ,
        .C_SLR_WIDTH  ( C_DATA_WIDTH ),
        .C_PIPELINES  ( C_PIPELINES_MASTER) ,
        .C_CHANNEL    ( C_CHANNEL ),
        .C_REG_CONFIG ( P_REG_CONFIG ) 
      )
      slr_master (
        .ACLK               (ACLK),
        .ACLK2X             (1'b0),
        .ARESETN             (ARESETN),
        .S_PAYLOAD_DATA     (S_PAYLOAD_DATA),
        .S_VALID            (S_VALID),
        .S_READY            (S_READY),
        .laguna_m_reset_out ( src_reset   ) ,
        .laguna_m_reset_in  ( dummy_reset   ) ,
        .laguna_m_payload   ( src_payload ) , 
        .laguna_m_handshake ( src_handshake   ) ,
        .laguna_m_ready     ( src_ready   )
      );
      
      axi_register_slice_v2_1_18_dest_region_slr #(
        .C_FAMILY     ( C_FAMILY         ) ,
        .C_REG_CONFIG ( P_REG_CONFIG ) ,
        .C_CHANNEL    ( C_CHANNEL ),
        .C_DATA_WIDTH ( C_DATA_WIDTH ) ,
        .C_SLR_WIDTH  ( C_DATA_WIDTH ),
        .C_PIPELINES  (C_PIPELINES_SLAVE),
        .C_SOURCE_LATENCY (P_FWD_DEST_LATENCY)
      )
      slr_slave (
        .ACLK               ( ACLK            ) ,
        .ACLK2X             (1'b0),
        .ARESETN             ( ARESETN ) ,
        .laguna_s_reset_out ( dummy_reset   ) ,
        .laguna_s_reset_in  ( src_reset   ) ,
        .laguna_s_payload   ( src_payload ) ,
        .laguna_s_handshake ( src_handshake   ) ,
        .laguna_s_ready     ( src_ready   ) ,
        .M_PAYLOAD_DATA     (M_PAYLOAD_DATA),
        .M_VALID            (M_VALID),
        .M_READY            (M_READY)
      );
      
    end else begin : resp
      axi_register_slice_v2_1_18_source_region_slr # (
        .C_FAMILY     ( C_FAMILY ) ,
        .C_DATA_WIDTH ( C_DATA_WIDTH ) ,
        .C_SLR_WIDTH  ( C_DATA_WIDTH ),
        .C_PIPELINES  (C_PIPELINES_SLAVE) ,
        .C_CHANNEL    ( C_CHANNEL ),
        .C_REG_CONFIG ( P_REG_CONFIG ) 
      )
      slr_slave (
        .ACLK               (ACLK),
        .ACLK2X             (1'b0),
        .ARESETN             ( ARESETN ),
        .S_PAYLOAD_DATA     (S_PAYLOAD_DATA),
        .S_VALID            (S_VALID),
        .S_READY            (S_READY),
        .laguna_m_reset_out ( dummy_reset   ) ,
        .laguna_m_reset_in  ( src_reset  ) ,
        .laguna_m_payload   ( src_payload ) , 
        .laguna_m_handshake ( src_handshake   ) ,
        .laguna_m_ready     ( src_ready   )
      );
      
      axi_register_slice_v2_1_18_dest_region_slr #(
        .C_FAMILY     ( C_FAMILY         ) ,
        .C_REG_CONFIG ( P_REG_CONFIG ) ,
        .C_CHANNEL    ( C_CHANNEL ),
        .C_DATA_WIDTH ( C_DATA_WIDTH ) ,
        .C_SLR_WIDTH  ( C_DATA_WIDTH ),
        .C_PIPELINES  (C_PIPELINES_MASTER),
        .C_SOURCE_LATENCY (P_RESP_DEST_LATENCY)
      )
      slr_master (
        .ACLK               ( ACLK            ) ,
        .ACLK2X             (1'b0),
        .ARESETN             ( ARESETN        ) ,
        .laguna_s_reset_out ( src_reset   ) ,
        .laguna_s_reset_in  ( dummy_reset    ) ,
        .laguna_s_payload   ( src_payload ) ,
        .laguna_s_handshake ( src_handshake   ) ,
        .laguna_s_ready     ( src_ready   ) ,
        .M_PAYLOAD_DATA     (M_PAYLOAD_DATA),
        .M_VALID            (M_VALID),
        .M_READY            (M_READY)
      );
    end
    
  end else if (C_NUM_SLR_CROSSINGS==2) begin : triple_slr
    
    wire [C_DATA_WIDTH-1:0] src_payload;
    wire src_handshake;
    wire src_ready;
    wire src_reset;
    wire [C_DATA_WIDTH-1:0] dest_payload;
    wire dest_handshake;
    wire dest_ready;
    wire dest_reset;
    wire dummy_reset1;
    wire dummy_reset2;
        
    if (C_CHANNEL==P_FORWARD) begin : fwd
      axi_register_slice_v2_1_18_source_region_slr # (
        .C_FAMILY     ( C_FAMILY ) ,
        .C_DATA_WIDTH ( C_DATA_WIDTH ) ,
        .C_SLR_WIDTH  ( C_DATA_WIDTH ),
        .C_PIPELINES  (C_PIPELINES_MASTER) ,
        .C_CHANNEL    ( C_CHANNEL ),
        .C_REG_CONFIG ( P_REG_CONFIG ) 
      )
      slr_master (
        .ACLK               (ACLK),
        .ACLK2X             (1'b0),
        .ARESETN             (ARESETN),
        .S_PAYLOAD_DATA     (S_PAYLOAD_DATA),
        .S_VALID            (S_VALID),
        .S_READY            (S_READY),
        .laguna_m_reset_out ( src_reset   ) ,
        .laguna_m_reset_in  ( dummy_reset1   ) ,
        .laguna_m_payload   ( src_payload ) , 
        .laguna_m_handshake ( src_handshake   ) ,
        .laguna_m_ready     ( src_ready   )
      );
      
      axi_register_slice_v2_1_18_middle_region_slr #(
        .C_FAMILY     ( C_FAMILY         ) ,
        .C_DATA_WIDTH ( C_DATA_WIDTH ) ,
        .C_CHANNEL    ( C_CHANNEL ),
        .C_PIPELINES  (C_PIPELINES_MIDDLE),
        .C_SOURCE_LATENCY (P_FWD_MIDDLE_LATENCY)
      )
      slr_middle (
        .ACLK               ( ACLK ) ,
        .ARESETN            ( ARESETN ),
        .laguna_s_reset_out ( dummy_reset1   ) ,
        .laguna_s_reset_in  ( src_reset    ) ,
        .laguna_s_payload   ( src_payload ) ,
        .laguna_s_handshake ( src_handshake   ) ,
        .laguna_s_ready     ( src_ready   ) ,
        .laguna_m_reset_out ( dest_reset   ) ,
        .laguna_m_reset_in  ( dummy_reset2   ) ,
        .laguna_m_payload   ( dest_payload ) , 
        .laguna_m_handshake ( dest_handshake   ) ,
        .laguna_m_ready     ( dest_ready   )
      );
      
      axi_register_slice_v2_1_18_dest_region_slr #(
        .C_FAMILY     ( C_FAMILY         ) ,
        .C_REG_CONFIG ( P_REG_CONFIG ) ,
        .C_CHANNEL    ( C_CHANNEL ),
        .C_DATA_WIDTH ( C_DATA_WIDTH ) ,
        .C_SLR_WIDTH  ( C_DATA_WIDTH ),
        .C_PIPELINES  (C_PIPELINES_SLAVE),
        .C_SOURCE_LATENCY (P_FWD_DEST_LATENCY)
      )
      slr_slave (
        .ACLK               ( ACLK            ) ,
        .ACLK2X             (1'b0),
        .ARESETN            ( ARESETN ),
        .laguna_s_reset_out ( dummy_reset2   ) ,
        .laguna_s_reset_in  ( dest_reset    ) ,
        .laguna_s_payload   ( dest_payload ) ,
        .laguna_s_handshake ( dest_handshake   ) ,
        .laguna_s_ready     ( dest_ready   ) ,
        .M_PAYLOAD_DATA     (M_PAYLOAD_DATA),
        .M_VALID            (M_VALID),
        .M_READY            (M_READY)
      );
      
    end else begin : resp
      axi_register_slice_v2_1_18_source_region_slr # (
        .C_FAMILY     ( C_FAMILY ) ,
        .C_DATA_WIDTH ( C_DATA_WIDTH ) ,
        .C_SLR_WIDTH  ( C_DATA_WIDTH ),
        .C_PIPELINES  (C_PIPELINES_SLAVE) ,
        .C_CHANNEL    ( C_CHANNEL ),
        .C_REG_CONFIG ( P_REG_CONFIG ) 
      )
      slr_slave (
        .ACLK               (ACLK),
        .ACLK2X             (1'b0),
        .ARESETN            ( ARESETN ),
        .S_PAYLOAD_DATA     (S_PAYLOAD_DATA),
        .S_VALID            (S_VALID),
        .S_READY            (S_READY),
        .laguna_m_reset_out ( dummy_reset1   ) ,
        .laguna_m_reset_in  ( src_reset   ) ,
        .laguna_m_payload   ( src_payload ) , 
        .laguna_m_handshake ( src_handshake   ) ,
        .laguna_m_ready     ( src_ready   )
      );
      
      axi_register_slice_v2_1_18_middle_region_slr #(
        .C_FAMILY     ( C_FAMILY         ) ,
        .C_DATA_WIDTH ( C_DATA_WIDTH ) ,
        .C_CHANNEL    ( C_CHANNEL ),
        .C_PIPELINES  (C_PIPELINES_MIDDLE),
        .C_SOURCE_LATENCY (P_RESP_MIDDLE_LATENCY)
      )
      slr_middle (
        .ACLK               ( ACLK ) ,
        .ARESETN            ( ARESETN ),
        .laguna_s_reset_out ( src_reset   ) ,
        .laguna_s_reset_in  ( dummy_reset1    ) ,
        .laguna_s_payload   ( src_payload ) ,
        .laguna_s_handshake ( src_handshake   ) ,
        .laguna_s_ready     ( src_ready   ) ,
        .laguna_m_reset_out ( dummy_reset2   ) ,
        .laguna_m_reset_in  ( dest_reset   ) ,
        .laguna_m_payload   ( dest_payload ) , 
        .laguna_m_handshake ( dest_handshake   ) ,
        .laguna_m_ready     ( dest_ready   )
      );
      
      axi_register_slice_v2_1_18_dest_region_slr #(
        .C_FAMILY     ( C_FAMILY         ) ,
        .C_REG_CONFIG ( P_REG_CONFIG ) ,
        .C_CHANNEL    ( C_CHANNEL ),
        .C_DATA_WIDTH ( C_DATA_WIDTH ) ,
        .C_SLR_WIDTH  ( C_DATA_WIDTH ),
        .C_PIPELINES  (C_PIPELINES_MASTER),
        .C_SOURCE_LATENCY (P_RESP_DEST_LATENCY)
      )
      slr_master (
        .ACLK               ( ACLK            ) ,
        .ACLK2X             (1'b0),
        .ARESETN             ( ARESETN        ) ,
        .laguna_s_reset_out ( dest_reset   ) ,
        .laguna_s_reset_in  ( dummy_reset2    ) ,
        .laguna_s_payload   ( dest_payload ) ,
        .laguna_s_handshake ( dest_handshake   ) ,
        .laguna_s_ready     ( dest_ready   ) ,
        .M_PAYLOAD_DATA     (M_PAYLOAD_DATA),
        .M_VALID            (M_VALID),
        .M_READY            (M_READY)
      );
    end
      
  end else if (C_NUM_SLR_CROSSINGS==3) begin : quad_slr
    
    wire [C_DATA_WIDTH-1:0] src_payload;
    wire src_handshake;
    wire src_ready;
    wire src_reset;
    wire [C_DATA_WIDTH-1:0] mid_payload;
    wire mid_handshake;
    wire mid_ready;
    wire mid_reset;
    wire [C_DATA_WIDTH-1:0] dest_payload;
    wire dest_handshake;
    wire dest_ready;
    wire dest_reset;
    wire dummy_reset1;
    wire dummy_reset2;
    wire dummy_reset3;
        
    if (C_CHANNEL==P_FORWARD) begin : fwd
      axi_register_slice_v2_1_18_source_region_slr # (
        .C_FAMILY     ( C_FAMILY ) ,
        .C_DATA_WIDTH ( C_DATA_WIDTH ) ,
        .C_SLR_WIDTH  ( C_DATA_WIDTH ),
        .C_PIPELINES  (C_PIPELINES_MASTER) ,
        .C_CHANNEL    ( C_CHANNEL ),
        .C_REG_CONFIG ( P_REG_CONFIG ) 
      )
      slr_master (
        .ACLK               (ACLK),
        .ACLK2X             (1'b0),
        .ARESETN             (ARESETN),
        .S_PAYLOAD_DATA     (S_PAYLOAD_DATA),
        .S_VALID            (S_VALID),
        .S_READY            (S_READY),
        .laguna_m_reset_out ( src_reset   ) ,
        .laguna_m_reset_in  ( dummy_reset1   ) ,
        .laguna_m_payload   ( src_payload ) , 
        .laguna_m_handshake ( src_handshake   ) ,
        .laguna_m_ready     ( src_ready   )
      );
      
      axi_register_slice_v2_1_18_middle_region_slr #(
        .C_FAMILY     ( C_FAMILY         ) ,
        .C_DATA_WIDTH ( C_DATA_WIDTH ) ,
        .C_CHANNEL    ( C_CHANNEL ),
        .C_PIPELINES  (C_PIPELINES_MIDDLE),
        .C_SOURCE_LATENCY (P_FWD_MIDDLE_LATENCY)
      )
      slr_middle_master (
        .ACLK               ( ACLK ) ,
        .ARESETN            ( ARESETN ),
        .laguna_s_reset_out ( dummy_reset1   ) ,
        .laguna_s_reset_in  ( src_reset    ) ,
        .laguna_s_payload   ( src_payload ) ,
        .laguna_s_handshake ( src_handshake   ) ,
        .laguna_s_ready     ( src_ready   ) ,
        .laguna_m_reset_out ( mid_reset   ) ,
        .laguna_m_reset_in  ( dummy_reset2   ) ,
        .laguna_m_payload   ( mid_payload ) , 
        .laguna_m_handshake ( mid_handshake   ) ,
        .laguna_m_ready     ( mid_ready   )
      );
      
      axi_register_slice_v2_1_18_middle_region_slr #(
        .C_FAMILY     ( C_FAMILY         ) ,
        .C_DATA_WIDTH ( C_DATA_WIDTH ) ,
        .C_CHANNEL    ( C_CHANNEL ),
        .C_PIPELINES  (C_PIPELINES_MIDDLE),
        .C_SOURCE_LATENCY (P_FWD_MIDDLE2_LATENCY)
      )
      slr_middle_slave (
        .ACLK               ( ACLK ) ,
        .ARESETN            ( ARESETN ),
        .laguna_s_reset_out ( dummy_reset2   ) ,
        .laguna_s_reset_in  ( mid_reset    ) ,
        .laguna_s_payload   ( mid_payload ) ,
        .laguna_s_handshake ( mid_handshake   ) ,
        .laguna_s_ready     ( mid_ready   ) ,
        .laguna_m_reset_out ( dest_reset   ) ,
        .laguna_m_reset_in  ( dummy_reset3   ) ,
        .laguna_m_payload   ( dest_payload ) , 
        .laguna_m_handshake ( dest_handshake   ) ,
        .laguna_m_ready     ( dest_ready   )
      );
      
      axi_register_slice_v2_1_18_dest_region_slr #(
        .C_FAMILY     ( C_FAMILY         ) ,
        .C_REG_CONFIG ( P_REG_CONFIG ) ,
        .C_CHANNEL    ( C_CHANNEL ),
        .C_DATA_WIDTH ( C_DATA_WIDTH ) ,
        .C_SLR_WIDTH  ( C_DATA_WIDTH ),
        .C_PIPELINES  (C_PIPELINES_SLAVE),
        .C_SOURCE_LATENCY (P_FWD_DEST_LATENCY)
      )
      slr_slave (
        .ACLK               ( ACLK            ) ,
        .ACLK2X             (1'b0),
        .ARESETN            ( ARESETN ),
        .laguna_s_reset_out ( dummy_reset3   ) ,
        .laguna_s_reset_in  ( dest_reset    ) ,
        .laguna_s_payload   ( dest_payload ) ,
        .laguna_s_handshake ( dest_handshake   ) ,
        .laguna_s_ready     ( dest_ready   ) ,
        .M_PAYLOAD_DATA     (M_PAYLOAD_DATA),
        .M_VALID            (M_VALID),
        .M_READY            (M_READY)
      );
      
    end else begin : resp
      axi_register_slice_v2_1_18_source_region_slr # (
        .C_FAMILY     ( C_FAMILY ) ,
        .C_DATA_WIDTH ( C_DATA_WIDTH ) ,
        .C_SLR_WIDTH  ( C_DATA_WIDTH ),
        .C_PIPELINES  (C_PIPELINES_SLAVE) ,
        .C_CHANNEL    ( C_CHANNEL ),
        .C_REG_CONFIG ( P_REG_CONFIG ) 
      )
      slr_slave (
        .ACLK               (ACLK),
        .ACLK2X             (1'b0),
        .ARESETN            ( ARESETN ),
        .S_PAYLOAD_DATA     (S_PAYLOAD_DATA),
        .S_VALID            (S_VALID),
        .S_READY            (S_READY),
        .laguna_m_reset_out ( dummy_reset1   ) ,
        .laguna_m_reset_in  ( src_reset   ) ,
        .laguna_m_payload   ( src_payload ) , 
        .laguna_m_handshake ( src_handshake   ) ,
        .laguna_m_ready     ( src_ready   )
      );
      
      axi_register_slice_v2_1_18_middle_region_slr #(
        .C_FAMILY     ( C_FAMILY         ) ,
        .C_DATA_WIDTH ( C_DATA_WIDTH ) ,
        .C_CHANNEL    ( C_CHANNEL ),
        .C_PIPELINES  (C_PIPELINES_MIDDLE),
        .C_SOURCE_LATENCY (P_RESP_MIDDLE_LATENCY)
      )
      slr_middle_slave (
        .ACLK               ( ACLK ) ,
        .ARESETN             ( ARESETN ) ,
        .laguna_s_reset_out ( src_reset   ) ,
        .laguna_s_reset_in  ( dummy_reset1    ) ,
        .laguna_s_payload   ( src_payload ) ,
        .laguna_s_handshake ( src_handshake   ) ,
        .laguna_s_ready     ( src_ready   ) ,
        .laguna_m_reset_out (  dummy_reset2  ) ,
        .laguna_m_reset_in  ( mid_reset   ) ,
        .laguna_m_payload   ( mid_payload ) , 
        .laguna_m_handshake ( mid_handshake   ) ,
        .laguna_m_ready     ( mid_ready   )
      );
      
      axi_register_slice_v2_1_18_middle_region_slr #(
        .C_FAMILY     ( C_FAMILY         ) ,
        .C_DATA_WIDTH ( C_DATA_WIDTH ) ,
        .C_CHANNEL    ( C_CHANNEL ),
        .C_PIPELINES  (C_PIPELINES_MIDDLE),
        .C_SOURCE_LATENCY (P_RESP_MIDDLE2_LATENCY)
      )
      slr_middle_master (
        .ACLK               ( ACLK ) ,
        .ARESETN             ( ARESETN ) ,
        .laguna_s_reset_out ( mid_reset   ) ,
        .laguna_s_reset_in  ( dummy_reset2   ) ,
        .laguna_s_payload   ( mid_payload ) ,
        .laguna_s_handshake ( mid_handshake   ) ,
        .laguna_s_ready     ( mid_ready   ) ,
        .laguna_m_reset_out ( dummy_reset3   ) ,
        .laguna_m_reset_in  ( dest_reset   ) ,
        .laguna_m_payload   ( dest_payload ) , 
        .laguna_m_handshake ( dest_handshake   ) ,
        .laguna_m_ready     ( dest_ready   )
      );
      
      axi_register_slice_v2_1_18_dest_region_slr #(
        .C_FAMILY     ( C_FAMILY         ) ,
        .C_REG_CONFIG ( P_REG_CONFIG ) ,
        .C_CHANNEL    ( C_CHANNEL ),
        .C_DATA_WIDTH ( C_DATA_WIDTH ) ,
        .C_SLR_WIDTH  ( C_DATA_WIDTH ),
        .C_PIPELINES  (C_PIPELINES_MASTER),
        .C_SOURCE_LATENCY (P_RESP_DEST_LATENCY)
      )
      slr_master (
        .ACLK               ( ACLK            ) ,
        .ACLK2X             (1'b0),
        .ARESETN             ( ARESETN        ) ,
        .laguna_s_reset_out ( dest_reset   ) ,
        .laguna_s_reset_in  ( dummy_reset3    ) ,
        .laguna_s_payload   ( dest_payload ) ,
        .laguna_s_handshake ( dest_handshake   ) ,
        .laguna_s_ready     ( dest_ready   ) ,
        .M_PAYLOAD_DATA     (M_PAYLOAD_DATA),
        .M_VALID            (M_VALID),
        .M_READY            (M_READY)
      );
    end
  end
  
endgenerate
endmodule  // multi_slr

`timescale 1ps/1ps
(* DowngradeIPIdentifiedWarnings="yes" *) 
module axi_register_slice_v2_1_18_middle_region_slr #
  (
   parameter C_FAMILY     = "virtex6",
   parameter integer C_DATA_WIDTH = 32,
   parameter integer C_CHANNEL = 0,  // 0=Forward, 1=Response
   parameter integer C_PIPELINES = 0,
   parameter integer C_SOURCE_LATENCY = 1
      // Number of cycles to wait after laguna_s_ready output to enable shifting internal pipeline stages, to stay in sync with pipeline enables in source slr .
   )
  (
   // System Signals
   input wire ACLK,
   input wire ARESETN,

   // Slave side
   input  wire laguna_s_reset_in,
   output wire laguna_s_reset_out,
   input  wire [C_DATA_WIDTH-1:0] laguna_s_payload,
   input  wire laguna_s_handshake,
   output wire laguna_s_ready,

   // Master side
   input  wire laguna_m_reset_in,
   output wire laguna_m_reset_out,
   output wire [C_DATA_WIDTH-1:0] laguna_m_payload,
   output wire laguna_m_handshake,
   input  wire laguna_m_ready
   );
   
  localparam integer P_PIPE_WIDTH = C_PIPELINES>0 ? C_PIPELINES : 1;
  localparam integer P_PIPE_LATENCY = ((C_SOURCE_LATENCY>0)?C_SOURCE_LATENCY:1) + C_PIPELINES;
  localparam integer P_FANOUT = 256;
  localparam integer P_REPLICATION = (C_DATA_WIDTH>P_FANOUT) ? (C_DATA_WIDTH/P_FANOUT + 1) : 1;
  localparam integer P_FORWARD = 0;
  localparam integer P_RESPONSE = 1;
   
  generate

  (* keep="true" *) reg s_reset_dd = 1'b0;
  (* keep="true" *) reg m_reset_dd = 1'b0;
  (* USER_SLL_REG="true", keep="true" *) reg laguna_s_reset_in_d = 1'b0;
  (* USER_SLL_REG="true", keep="true" *) reg laguna_m_reset_in_d = 1'b0;
  (* USER_SLL_REG="true", keep="true" *) reg laguna_s_reset_out_i = 1'b0;
  (* USER_SLL_REG="true", keep="true" *) reg laguna_m_reset_out_i = 1'b0;
  
  assign laguna_s_reset_out = laguna_s_reset_out_i;
  assign laguna_m_reset_out = laguna_m_reset_out_i;
  
  always @(posedge ACLK) begin
    laguna_s_reset_in_d <= laguna_s_reset_in;
    laguna_m_reset_in_d <= laguna_m_reset_in;
    s_reset_dd <= laguna_s_reset_in_d;
    m_reset_dd <= laguna_m_reset_in_d;
    laguna_s_reset_out_i <= C_PIPELINES==0 ? laguna_m_reset_in_d : m_reset_dd;
    laguna_m_reset_out_i <= C_PIPELINES==0 ? laguna_s_reset_in_d : s_reset_dd;
  end
  
  wire ACLEAR;
  assign ACLEAR = ~ARESETN;
  
  if (1) begin : common
    (* USER_SLL_REG="true", shreg_extract="no" *) reg [C_DATA_WIDTH-1:0] laguna_s_payload_d;
    (* USER_SLL_REG="true", shreg_extract="no" *) reg [C_DATA_WIDTH-1:0] laguna_m_payload_i;
    wire laguna_s_handshake_q;
    wire m_handshake_d;
    (* USER_SLL_REG="true", keep="true" *)  reg laguna_m_ready_d = 1'b0;
    (* USER_SLL_REG="true", keep="true" *)  reg laguna_s_ready_i = 1'b0;
    (* keep="true" *)  reg [P_PIPE_WIDTH-1:0] ready_d = {P_PIPE_WIDTH{1'b0}};
    wire [(C_PIPELINES+2)*C_DATA_WIDTH-1:0] payload_i;
    wire [(C_PIPELINES+2)-1:0] handshake_i;
    genvar p;
    
    assign laguna_m_payload = laguna_m_payload_i;
    assign laguna_s_ready = laguna_s_ready_i;
        
    always @(posedge ACLK) begin
      laguna_m_ready_d <= laguna_m_ready; 
      laguna_s_ready_i <= (C_PIPELINES==0) ? laguna_m_ready_d : ready_d[P_PIPE_WIDTH-1];
      ready_d <= {ready_d, laguna_m_ready_d}; 
    end

    for (p=0; p<=(C_PIPELINES+1); p=p+1) begin : pipe
      (* shreg_extract="no" *) reg [C_DATA_WIDTH-1:0]  payload_data;
      wire payload_valid_d;
      wire payload_valid_q;
      
      assign payload_i[p*C_DATA_WIDTH +: C_DATA_WIDTH] = (p==0) ? laguna_s_payload_d : payload_data;
      assign handshake_i[p] = (p==0) ? laguna_s_handshake_q : payload_valid_q;
      assign payload_valid_d = handshake_i[((p>0)?(p-1):0)];
      
      always @(posedge ACLK) begin
        if (p==0) begin
          laguna_s_payload_d <= laguna_s_payload;
        end else if (p==C_PIPELINES+1) begin
          laguna_m_payload_i <= payload_i[C_PIPELINES*C_DATA_WIDTH +: C_DATA_WIDTH];
        end else begin
          payload_data <= payload_i[((p>0)?(p-1):0)*C_DATA_WIDTH +: C_DATA_WIDTH];
        end
      end

      FDCE #(
          .INIT(1'b0)
       ) payload_valid_asyncclear_inst (
          .Q   (payload_valid_q),
          .C   (ACLK), 
          .CE  (1'b1),
          .CLR (ACLEAR),
          .D   (payload_valid_d)
       );
    end  // loop p
    
    assign m_handshake_d = handshake_i[C_PIPELINES];
    
    (* USER_SLL_REG="true" *)
    FDCE #(
        .INIT(1'b0)
     ) laguna_m_handshake_asyncclear_inst (
        .Q   (laguna_m_handshake),
        .C   (ACLK), 
        .CE  (1'b1),
        .CLR (ACLEAR),
        .D   (m_handshake_d)
     );
    
    (* USER_SLL_REG="true" *)
    FDCE #(
        .INIT(1'b0)
     ) laguna_s_handshake_asyncclear_inst (
        .Q   (laguna_s_handshake_q),
        .C   (ACLK), 
        .CE  (1'b1),
        .CLR (ACLEAR),
        .D   (laguna_s_handshake)
     );
    
  end // gen_slr
  endgenerate
endmodule  // middle_region_slr

`timescale 1ps/1ps
(* DowngradeIPIdentifiedWarnings="yes" *) 
module axi_register_slice_v2_1_18_source_region_slr #
  (
   parameter C_FAMILY     = "virtex6",
   parameter integer C_REG_CONFIG = 12,
   parameter integer C_CHANNEL = 0,  // 0=Forward, 1=Response
   parameter integer C_DATA_WIDTH = 32,
   parameter integer C_SLR_WIDTH = 32,
   parameter integer C_PIPELINES = 0
   )
  (
   // System Signals
   input wire ACLK,
   input wire ACLK2X,
   input wire ARESETN,

   // Slave side
   input  wire [C_DATA_WIDTH-1:0] S_PAYLOAD_DATA,
   input  wire S_VALID,
   output wire S_READY,

   // Master side
   input  wire laguna_m_reset_in,
   output wire laguna_m_reset_out,
   output wire [C_SLR_WIDTH-1:0] laguna_m_payload,
   output wire laguna_m_handshake,
   input  wire laguna_m_ready
   );

  generate

  if (C_REG_CONFIG == 13) begin : tdm
    (* keep="true" *) reg areset_d = 1'b0;
    always @(posedge ACLK) begin
      areset_d <= ~ARESETN;
    end
    assign laguna_m_reset_out = 1'b0;
  
    localparam integer P_EVEN_WIDTH = C_DATA_WIDTH[0] ? (C_DATA_WIDTH+1) : C_DATA_WIDTH;
    
    (* shreg_extract = "no" *) reg [P_EVEN_WIDTH-1:0] payload_d1;
    (* shreg_extract = "no" *) reg [C_SLR_WIDTH-1:0]  laguna_m_payload_i;
    (* keep="true" *)    reg laguna_m_handshake_i = 1'b0;
    (* shreg_extract = "no" *) reg laguna_m_ready_d = 1'b0;
    wire sample_cycle;
    integer i;

    assign laguna_m_payload = laguna_m_payload_i;
    assign laguna_m_handshake = laguna_m_handshake_i;
    assign S_READY = laguna_m_ready_d;
        
    always @(posedge ACLK) begin
      if (laguna_m_ready_d) begin
        payload_d1 <= S_PAYLOAD_DATA;  // ACLK cycle 1
      end
    end

    always @(posedge ACLK2X) begin
      for (i=0;i<C_SLR_WIDTH;i=i+1) begin  
        if (laguna_m_ready_d) begin
          if (~sample_cycle) begin  // First (high) phase of ACLK cycle 2
            laguna_m_payload_i[i] <= payload_d1[2*i+1];  // Mux odd bits
          end else begin  // Second (low) phase of ACLK cycle 2
            laguna_m_payload_i[i] <= payload_d1[2*i];  // Mux even bits
          end
        end
      end
    end

    always @(posedge ACLK) begin
      if (areset_d) begin
        laguna_m_handshake_i <= 1'b0;
        laguna_m_ready_d <= 1'b0;
      end else begin
        if (laguna_m_ready_d) begin
          laguna_m_handshake_i <= S_VALID;
        end
        laguna_m_ready_d <= laguna_m_ready;  // Half-cycle setup from dest_region.laguna_s_ready_i
      end
    end

    axi_register_slice_v2_1_18_tdm_sample tdm_sample_inst (
      .slow_clk     (ACLK),
      .fast_clk     (ACLK2X),
      .sample_cycle (sample_cycle)
    );
    
  end else begin : common

    localparam integer P_FANOUT = 256;
    localparam integer P_REPLICATION = (C_DATA_WIDTH>P_FANOUT) ? (C_DATA_WIDTH/P_FANOUT + 1) : 1;
    localparam integer P_PIPE_WIDTH = (C_PIPELINES>0) ? C_PIPELINES : 1;
    localparam integer P_FORWARD = 0;
    localparam integer P_RESPONSE = 1;
     
    (* keep="true" *)    reg aresetn_d = 1'b1;
    (* keep="true" *) reg areset_d = 1'b0;
    (* USER_SLL_REG="true", keep="true" *) reg laguna_m_reset_in_d = 1'b0;
    (* USER_SLL_REG="true", keep="true" *) reg laguna_m_reset_out_i = 1'b0;
                               reg [15:0] areset_dly = 16'b0;
    
    assign laguna_m_reset_out = laguna_m_reset_out_i;
    
    always @(posedge ACLK) begin
      laguna_m_reset_in_d <= laguna_m_reset_in;
      aresetn_d <= C_CHANNEL==P_FORWARD ? ARESETN : 1'b1;
      areset_dly <= {16{~aresetn_d}} | (areset_dly<<1);
      areset_d <= C_REG_CONFIG == 12 ? ~ARESETN : C_CHANNEL==P_FORWARD ? areset_dly[15]  : laguna_m_reset_in_d;
      laguna_m_reset_out_i <= areset_d;  // For resp channels, reflect laguna_m_reset_in_d to avoid tie-off laguna routing errors, but it doesn't get used.
    end
  
    wire ACLEAR;
    assign ACLEAR = C_REG_CONFIG == 12 ? 1'b0 : ~ARESETN;
  
    (* USER_SLL_REG="true", shreg_extract="no" *) reg [C_DATA_WIDTH-1:0] laguna_m_payload_i;
    wire m_handshake_d;
    (* USER_SLL_REG="true", keep="true" *)  reg laguna_m_ready_d = 1'b0;
    (* keep="true" *)  reg s_ready_i = 1'b0;
    (* keep="true" *)  reg [P_PIPE_WIDTH-1:0] ready_d = {P_PIPE_WIDTH{1'b0}};
    wire [(C_PIPELINES+1)*C_DATA_WIDTH-1:0] payload_i;
    wire [(C_PIPELINES+1)-1:0] handshake_i;
    genvar p;
    
    assign laguna_m_payload = laguna_m_payload_i;
    assign S_READY = s_ready_i;
        
    always @(posedge ACLK) begin
      laguna_m_ready_d <= laguna_m_ready; 
      ready_d <= {ready_d, laguna_m_ready_d}; 
      if (areset_d) begin
        s_ready_i <= 1'b0; 
      end else begin
        s_ready_i <= (C_PIPELINES==0) ? laguna_m_ready_d : ready_d[P_PIPE_WIDTH-1]; 
      end
    end
    
    for (p=0; p<=C_PIPELINES; p=p+1) begin : pipe
      (* shreg_extract="no" *) reg [C_DATA_WIDTH-1:0] payload_data;
      wire payload_valid_d;
      wire payload_valid_q;
      
      assign payload_i[p*C_DATA_WIDTH +: C_DATA_WIDTH] = payload_data;
      assign handshake_i[p] = payload_valid_q;
      assign payload_valid_d = (p==0) ? (S_VALID & s_ready_i) : handshake_i[((p>0)?(p-1):0)];
      
      always @(posedge ACLK) begin
        if (p==C_PIPELINES) begin
          laguna_m_payload_i <= C_PIPELINES==0 ? S_PAYLOAD_DATA : payload_i[(P_PIPE_WIDTH-1)*C_DATA_WIDTH +: C_DATA_WIDTH];
        end else if (p==0) begin
          payload_data <= S_PAYLOAD_DATA;
        end else begin
          payload_data <= payload_i[((p>0)?(p-1):0)*C_DATA_WIDTH +: C_DATA_WIDTH];
        end
      end
      
      FDCE #(
          .INIT(1'b0)
       ) payload_valid_asyncclear_inst (
          .Q   (payload_valid_q),
          .C   (ACLK), 
          .CE  (1'b1),
          .CLR (ACLEAR),
          .D   (payload_valid_d)
       );
    end  // loop p
    
    assign m_handshake_d = C_PIPELINES==0 ? (S_VALID & s_ready_i) : handshake_i[P_PIPE_WIDTH-1];
    
    (* USER_SLL_REG="true" *)
    FDCE #(
        .INIT(1'b0)
     ) laguna_m_handshake_asyncclear_inst (
        .Q   (laguna_m_handshake),
        .C   (ACLK), 
        .CE  (1'b1),
        .CLR (ACLEAR),
        .D   (m_handshake_d)
     );
    
  end // gen_slr
  endgenerate
endmodule  // source_region_slr

`timescale 1ps/1ps
(* DowngradeIPIdentifiedWarnings="yes" *)
module axi_register_slice_v2_1_18_dest_region_slr #
  (
   parameter C_FAMILY     = "virtex6",
   parameter integer C_REG_CONFIG = 12,
   parameter integer C_CHANNEL = 0,  // 0=Forward, 1=Response
   parameter integer C_DATA_WIDTH = 32,
   parameter integer C_SLR_WIDTH = 32,
   parameter integer C_PIPELINES = 0,
   parameter integer C_SOURCE_LATENCY = 1
      // Number of cycles to wait after laguna_s_ready output to enable shifting internal pipeline stages, to stay in sync with pipeline enables in source slr .
   )
  (
   // System Signals
   input wire ACLK,
   input wire ACLK2X,
   input wire ARESETN,

   // Slave side
   input  wire laguna_s_reset_in,
   output wire laguna_s_reset_out,
   input  wire [C_SLR_WIDTH-1:0] laguna_s_payload,
   input  wire laguna_s_handshake,
   output wire laguna_s_ready,

   // Master side
   output wire [C_DATA_WIDTH-1:0] M_PAYLOAD_DATA,
   output wire M_VALID,
   input  wire M_READY
   );

  generate

  if (C_REG_CONFIG == 13) begin : tdm
    (* keep="true" *) reg areset_d = 1'b0;
    always @(posedge ACLK) begin
      areset_d <= ~ARESETN;
    end
    assign laguna_s_reset_out = 1'b0;
  
    localparam integer P_EVEN_WIDTH = C_DATA_WIDTH[0] ? (C_DATA_WIDTH+1) : C_DATA_WIDTH;
    
    (* shreg_extract = "no" *) reg [C_SLR_WIDTH-1:0]  laguna_s_payload_d;
    (* shreg_extract = "no" *) reg [C_SLR_WIDTH-1:0]  payload_tdm_d4;
    (* shreg_extract = "no" *) reg [C_DATA_WIDTH-1:0] fifo_out;
    (* shreg_extract = "no" *) reg [C_DATA_WIDTH-1:0] fifo_out_n1;
    (* shreg_extract = "no" *) reg laguna_s_handshake_d = 1'b0;
    (* keep="true" *)    reg laguna_s_ready_i = 1'b0;
    (* shreg_extract = "no" *) reg s_ready_d2 = 1'b0;
    reg [P_EVEN_WIDTH-1:0] payload_demux;
    reg m_valid_r = 1'b0;
    wire push;
    wire pop;
    reg [1:0] fifo_cnt = 2'h0;
    integer i;
    
    assign laguna_s_ready = laguna_s_ready_i;
    assign M_VALID = m_valid_r;
    assign M_PAYLOAD_DATA = fifo_out;  // Registered outputs
    assign pop = M_READY & m_valid_r;
    assign push = laguna_s_handshake_d & s_ready_d2;      

    always @(posedge ACLK) begin
      if (areset_d) begin
        laguna_s_handshake_d <= 1'b0;
      end else if (s_ready_d2) begin
        laguna_s_handshake_d <= laguna_s_handshake;
      end
    end

    always @(posedge ACLK2X) begin
      if (s_ready_d2) begin
        payload_tdm_d4 <= laguna_s_payload_d;
        laguna_s_payload_d <= laguna_s_payload;
      end
    end
    
    always @ * begin
      for (i=0;i<C_SLR_WIDTH;i=i+1) begin
        payload_demux[2*i+1] = payload_tdm_d4[i];       // Odd bits captured during second (low) phase of ACLK cycle 2
        payload_demux[2*i] = laguna_s_payload_d[i];  // Even bits captured during first (high) phase of ACLK cycle 3
          // Complete payload_demux signal is stable during second (low) phase of ACLK cycle 3 (gets clobbered after each ACLK active edge)
      end
    end

    always @(posedge ACLK) begin
      if (areset_d) begin
        fifo_cnt <= 2'h0;
        m_valid_r <=  1'b0;
        s_ready_d2 <= 1'b0;
      end else begin
        s_ready_d2 <= laguna_s_ready_i;  // Half-cycle setup from laguna_s_ready_i
        if (push & ~pop) begin
          fifo_cnt <= fifo_cnt + 2'h1;
          m_valid_r <=  1'b1;
        end else if (~push & pop) begin
          fifo_cnt <= fifo_cnt - 2'h1;
          m_valid_r <= fifo_cnt[1];  // fifo_cnt >= 2
        end
      end
    end

    always @(negedge ACLK) begin
      if (areset_d) begin
        laguna_s_ready_i <= 1'b0;
      end else begin
        laguna_s_ready_i <= M_READY | ~m_valid_r;  // Half-cycle setup
      end
    end

    always @(posedge ACLK) begin
      case (fifo_cnt)
        2'h0: begin  // EMPTY
          fifo_out <= payload_demux;
        end
        
        2'h1: begin
          fifo_out_n1 <= payload_demux;
          if (pop) begin
            fifo_out <= payload_demux;
          end
        end
        
        default: begin  // fifo_cnt == 2
          if (pop) begin
            fifo_out <= fifo_out_n1;
            fifo_out_n1 <= payload_demux;
          end
        end
      endcase
    end

  end else begin : common

    localparam integer P_PIPE_WIDTH = C_PIPELINES>0 ? C_PIPELINES : 1;
    localparam integer P_PIPE_LATENCY = ((C_SOURCE_LATENCY>0)?C_SOURCE_LATENCY:1) + C_PIPELINES;
    localparam integer P_FANOUT = 256;
    localparam integer P_REPLICATION = (C_DATA_WIDTH>P_FANOUT) ? (C_DATA_WIDTH/P_FANOUT + 1) : 1;
    localparam integer P_FORWARD = 0;
    localparam integer P_RESPONSE = 1;
     
    (* keep="true" *)    reg aresetn_d = 1'b1;
    (* keep="true" *) reg areset_d = 1'b0;
    (* USER_SLL_REG="true", keep="true" *) reg laguna_s_reset_in_d = 1'b0;
    (* USER_SLL_REG="true", keep="true" *) reg laguna_s_reset_out_i = 1'b0;
                               reg [15:0] areset_dly = 16'b0;
    
    assign laguna_s_reset_out = laguna_s_reset_out_i;
    
    always @(posedge ACLK) begin
      laguna_s_reset_in_d <= laguna_s_reset_in;
      aresetn_d <= C_CHANNEL==P_RESPONSE ? ARESETN : 1'b1;
      areset_dly <= {16{~aresetn_d}} | (areset_dly<<1);
      areset_d <= C_REG_CONFIG == 12 ? ~ARESETN : C_CHANNEL==P_FORWARD ? laguna_s_reset_in_d : areset_dly[15];
      laguna_s_reset_out_i <= areset_d;  // For forward channels, reflect laguna_s_reset_in_d to avoid tie-off laguna routing errors, but it doesn't get used.
    end

    wire ACLEAR;
    assign ACLEAR = C_REG_CONFIG == 12 ? 1'b0 : ~ARESETN;
  
    (* USER_SLL_REG="true", shreg_extract="no" *) reg [C_DATA_WIDTH-1:0] laguna_s_payload_d;
    wire laguna_s_handshake_q;
    (* USER_SLL_REG="true", keep="true" *)  reg laguna_s_ready_i = 1'b0;
    (* keep="true" *)  reg [P_PIPE_WIDTH-1:0] ready_d = {P_PIPE_WIDTH{1'b0}};
    wire [(C_PIPELINES+1)*C_DATA_WIDTH-1:0] payload_i;
    wire [(C_PIPELINES+1)-1:0] handshake_i;
    wire m_valid_i;
    wire push;
    wire pop;
    genvar p;
    
    assign laguna_s_ready = laguna_s_ready_i;
    assign pop = M_READY & m_valid_i;
    assign push = handshake_i[C_PIPELINES];      
    assign M_VALID = m_valid_i;

    always @(posedge ACLK) begin
      laguna_s_ready_i <= (C_PIPELINES==0) ? (M_READY | ~m_valid_i) : ready_d[P_PIPE_WIDTH-1];
      ready_d <= {ready_d, (M_READY | ~m_valid_i)}; 
    end
    
    for (p=0; p<=C_PIPELINES; p=p+1) begin : pipe
      (* shreg_extract="no" *) reg [C_DATA_WIDTH-1:0]  payload_data;
      wire payload_valid_d;
      wire payload_valid_q;
      
      assign payload_i[p*C_DATA_WIDTH +: C_DATA_WIDTH] = (p==0) ? laguna_s_payload_d : payload_data;
      assign handshake_i[p] = (p==0) ? laguna_s_handshake_q : payload_valid_q;
      assign payload_valid_d = handshake_i[((p>0)?(p-1):0)];
      
      always @(posedge ACLK) begin
        if (p==0) begin
          laguna_s_payload_d <= laguna_s_payload;
        end else begin
          payload_data <= payload_i[((p>0)?(p-1):0)*C_DATA_WIDTH +: C_DATA_WIDTH];
        end
      end
        
      FDCE #(
          .INIT(1'b0)
       ) payload_valid_asyncclear_inst (
          .Q   (payload_valid_q),
          .C   (ACLK), 
          .CE  (1'b1),
          .CLR (ACLEAR),
          .D   (payload_valid_d)
       );
    end  // loop p
    
    (* USER_SLL_REG="true" *)
    FDCE #(
        .INIT(1'b0)
     ) laguna_s_handshake_asyncclear_inst (
        .Q   (laguna_s_handshake_q),
        .C   (ACLK), 
        .CE  (1'b1),
        .CLR (ACLEAR),
        .D   (laguna_s_handshake)
     );
        
    axi_register_slice_v2_1_18_axic_reg_srl_fifo #
      (
       .C_FIFO_WIDTH (C_DATA_WIDTH), 
       .C_FIFO_SIZE  ((C_PIPELINES+C_SOURCE_LATENCY>14) ? 6 : (C_PIPELINES+C_SOURCE_LATENCY>6) ? 5 : 4)  
      )
      srl_fifo_0
      (
       .aclk    (ACLK),    
       .areset  (areset_d),  
       .aclear  (ACLEAR),
       .s_mesg  (payload_i[C_PIPELINES*C_DATA_WIDTH +: C_DATA_WIDTH]),  
       .s_valid (push), 
       .m_mesg  (M_PAYLOAD_DATA),  
       .m_valid (m_valid_i), 
       .m_ready (pop)
      ); 
  
  end // gen_slr
  endgenerate
endmodule  // dest_region_slr

`timescale 1ps/1ps
(* DowngradeIPIdentifiedWarnings="yes" *)
module axi_register_slice_v2_1_18_single_slr #
  (
   parameter C_FAMILY     = "virtex6",
   parameter integer C_DATA_WIDTH = 32,
   parameter integer C_PIPELINES = 0
   )
  (
   // System Signals
   input wire ACLK,
   input wire ARESETN,

   // Slave side
   input  wire [C_DATA_WIDTH-1:0] S_PAYLOAD_DATA,
   input  wire S_VALID,
   output wire S_READY,

   // Master side
   output wire [C_DATA_WIDTH-1:0] M_PAYLOAD_DATA,
   output wire M_VALID,
   input  wire M_READY
   );

  generate

  localparam integer P_PIPE_WIDTH = (C_PIPELINES>0) ? C_PIPELINES : 1;
  localparam integer P_FANOUT = 256;
  localparam integer P_REPLICATION = (C_DATA_WIDTH>P_FANOUT) ? (C_DATA_WIDTH/P_FANOUT + 1) : 1;
   
  reg areset_d = 1'b0;
  reg [3:0] areset_dly = 4'b0;
  always @(posedge ACLK) begin
    areset_dly <= {4{~ARESETN}} | (areset_dly<<1);
    areset_d <= areset_dly[3];
  end
  
  if (1) begin : common
    reg s_ready_i = 1'b0;
    (* keep="true" *)  reg [P_PIPE_WIDTH-1:0] ready_d = {P_PIPE_WIDTH{1'b0}};
    wire [(C_PIPELINES+1)*C_DATA_WIDTH-1:0] payload_i;
    wire [(C_PIPELINES+1)-1:0] handshake_i;
    wire m_valid_i;
    wire push;
    wire pop;
    genvar p;
    
    assign pop = M_READY & m_valid_i;
    assign push = handshake_i[C_PIPELINES];      
    assign M_VALID = m_valid_i;
    assign S_READY = s_ready_i;
        
    always @(posedge ACLK) begin
      ready_d <= {ready_d, (M_READY | ~m_valid_i)}; 
      if (areset_d) begin
        s_ready_i <= 1'b0; 
      end else begin
        s_ready_i <= (C_PIPELINES==0) ? (M_READY | ~m_valid_i) : ready_d[P_PIPE_WIDTH-1]; 
      end
    end
    
    assign payload_i[0 +: C_DATA_WIDTH] = S_PAYLOAD_DATA;
    assign handshake_i[0] = S_VALID & s_ready_i;
    
    for (p=1; p<=C_PIPELINES; p=p+1) begin : pipe
      (* shreg_extract="no" *) reg [C_DATA_WIDTH-1:0]  payload_data;
      (* keep="true" *)  reg payload_valid = 1'b0;
      
      assign payload_i[p*C_DATA_WIDTH +: C_DATA_WIDTH] = payload_data;
      assign handshake_i[p] = payload_valid;
      
      always @(posedge ACLK) begin
        if (p==1) begin
          payload_data <= S_PAYLOAD_DATA;
          payload_valid <= S_VALID & s_ready_i & ~areset_d;
        end else begin
          payload_data <= payload_i[((p>0)?(p-1):0)*C_DATA_WIDTH +: C_DATA_WIDTH];
          payload_valid <= handshake_i[((p>0)?(p-1):0)];
        end
      end
    end
    
    if (C_PIPELINES==0) begin : ff_fifo

      (* shreg_extract = "no" *) reg [C_DATA_WIDTH-1:0] fifo_out;
      (* shreg_extract = "no" *) reg [C_DATA_WIDTH-1:0] fifo_out_n1;
      (* shreg_extract = "no" *) reg [C_DATA_WIDTH-1:0] fifo_out_n2;
      reg [1:0] fifo_cnt = 2'h0;
      reg m_valid_r = 1'b0;
      
      assign M_PAYLOAD_DATA = fifo_out; 
      assign m_valid_i = m_valid_r;
      
      always @(posedge ACLK) begin
        if (areset_d) begin
          fifo_cnt <= 2'h0;
          m_valid_r <=  1'b0;
        end else begin
          if (push & ~pop) begin
            fifo_cnt <= fifo_cnt + 2'h1;
            m_valid_r <=  1'b1;
          end else if (~push & pop) begin
            fifo_cnt <= fifo_cnt - 2'h1;
            m_valid_r <= fifo_cnt[1];  // fifo_cnt >= 2
          end
        end
      end

      always @(posedge ACLK) begin
        case (fifo_cnt)
          2'h0: begin  // EMPTY
            fifo_out <= payload_i[C_PIPELINES*C_DATA_WIDTH +: C_DATA_WIDTH];
          end
          
          2'h1: begin
            fifo_out_n1 <= payload_i[C_PIPELINES*C_DATA_WIDTH +: C_DATA_WIDTH];
            if (pop) begin
              fifo_out <= payload_i[C_PIPELINES*C_DATA_WIDTH +: C_DATA_WIDTH];
            end
          end
          
          2'h2: begin
            fifo_out_n2 <= payload_i[C_PIPELINES*C_DATA_WIDTH +: C_DATA_WIDTH];
            if (pop) begin
              fifo_out <= fifo_out_n1;
              fifo_out_n1 <= payload_i[C_PIPELINES*C_DATA_WIDTH +: C_DATA_WIDTH];
            end
          end
          
          default: begin  // fifo_cnt == 3
            if (pop) begin
              fifo_out <= fifo_out_n1;
              fifo_out_n1 <= fifo_out_n2;
              fifo_out_n2 <= payload_i[C_PIPELINES*C_DATA_WIDTH +: C_DATA_WIDTH];
            end
          end
        endcase
      end
    
    end else begin : srl_fifo
    
      axi_register_slice_v2_1_18_axic_reg_srl_fifo #
        (
         .C_FIFO_WIDTH (C_DATA_WIDTH), 
         .C_FIFO_SIZE  ((C_PIPELINES>12) ? 5 : 4)  
        )
        srl_fifo_0
        (
         .aclk    (ACLK),    
         .areset  (areset_d),
         .aclear  (1'b0),  
         .s_mesg  (payload_i[C_PIPELINES*C_DATA_WIDTH +: C_DATA_WIDTH]),  
         .s_valid (push), 
         .m_mesg  (M_PAYLOAD_DATA),  
         .m_valid (m_valid_i), 
         .m_ready (pop)
        );

    end // gen_fifo
  end // gen_slr
  endgenerate
endmodule  // single_slr

(* DowngradeIPIdentifiedWarnings="yes" *) 
module axi_register_slice_v2_1_18_axic_reg_srl_fifo #
  // FIFO with no s_ready back-pressure; must guarantee parent will never push beyond full
  (
   parameter integer C_FIFO_WIDTH  = 1,      // Width of s_mesg/m_mesg.
   parameter integer C_FIFO_SIZE = 5        // Depth of FIFO is 2**C_FIFO_SIZE.  
   )
  (
   input  wire                        aclk,    // Clock
   input  wire                        areset,  // Reset
   input  wire                        aclear,  // Async clear
   input  wire [C_FIFO_WIDTH-1:0]     s_mesg,  // Input data
   input  wire                        s_valid, // Input data valid
   output wire [C_FIFO_WIDTH-1:0]     m_mesg,  // Output data
   output wire                        m_valid, // Output data valid
   input  wire                        m_ready  // Output data ready
   );
  
  genvar i;

  generate
  
    localparam integer P_FIFO_DEPTH            = 2**C_FIFO_SIZE;
    localparam [C_FIFO_SIZE-1:0] P_EMPTY       = {C_FIFO_SIZE{1'b1}};
    localparam [C_FIFO_SIZE-1:0] P_ALMOSTEMPTY = {C_FIFO_SIZE{1'b0}};
    
    localparam M_VALID_0   = 1'b0;
    localparam M_VALID_1   = 1'b1;
    localparam SRL_VALID_0 = 1'b0;
    localparam SRL_VALID_1 = 1'b1;
    localparam S_VALID_0   = 1'b0;
    localparam S_VALID_1   = 1'b1;
    localparam M_READY_0   = 1'b0;
    localparam M_READY_1   = 1'b1;
    
    localparam [1:0] K_EMPTY   = {SRL_VALID_0, M_VALID_0};
    localparam [1:0] K_HAS1    = {SRL_VALID_0, M_VALID_1};
    localparam [1:0] K_MIN2    = {SRL_VALID_1, M_VALID_1};

    reg  push;       // SRL push
    reg  pop;        // SRL pop
    wire [C_FIFO_WIDTH-1:0] srl_reg;
    reg [C_FIFO_SIZE-1:0]  fifoaddr = P_EMPTY;
    
    wire [1:0] state;  // State vector register
    reg  [1:0] next;           // Next state value
    wire [1:0] next_qual;           // Next state value
    
    reg  load_mesg;  // Load output register
    reg  srl2mesg;   // Output reg loads from SRL (else from s_mesg)
    reg  [C_FIFO_WIDTH-1:0] mesg_reg;  // No initial state
    reg  m_valid_d;
    wire m_valid_q;
    
    assign m_valid = m_valid_q;
    assign next_qual = areset ? K_EMPTY : next;
    assign m_mesg  = mesg_reg;

    FDCE #(
        .INIT(1'b0)
     ) asyncclear_mvalid_inst (
        .Q   (m_valid_q),
        .C   (aclk), 
        .CE  (1'b1),
        .CLR (aclear),
        .D   (m_valid_d)
     );

    FDCE #(
        .INIT(1'b0)
     ) asyncclear_state0_inst (
        .Q   (state[0]),
        .C   (aclk), 
        .CE  (1'b1),
        .CLR (aclear),
        .D   (next_qual[0])
     );

    FDCE #(
        .INIT(1'b0)
     ) asyncclear_state1_inst (
        .Q   (state[1]),
        .C   (aclk), 
        .CE  (1'b1),
        .CLR (aclear),
        .D   (next_qual[1])
     );

    always @ * begin
      next = state;  // Default: hold state unless re-assigned
      m_valid_d = m_valid_q & ~areset;
      load_mesg = 1'b1;
      srl2mesg = 1'b0;
      push = 1'b0;
      pop = 1'b0;
      case (state)
        K_EMPTY: begin  // FIFO Empty; pre-assert s_ready
          load_mesg = s_valid;
          srl2mesg = 1'b0;
          push = 1'b0;
          pop = 1'b0;
          if (s_valid & ~areset) begin
            next = K_HAS1;
            m_valid_d = 1'b0;
          end
        end  // EMPTY
        
        K_HAS1: begin  // FIFO contains 1 item in the output register (SRL empty)
          srl2mesg = 1'b0;
          pop = 1'b0;
          casex ({s_valid,m_ready})
            {S_VALID_1,M_READY_0}: begin  // Receive a 2nd item, push into SRL
              next = K_MIN2;
              load_mesg = 1'b0;
              push = 1'b1;
              m_valid_d = 1'b1;
            end
            
            {S_VALID_0,M_READY_1}: begin  // Pop to empty
              next = K_EMPTY;
              load_mesg = 1'b1;  // Inconsequential
              push = 1'b0;
              m_valid_d = 1'b0;
            end
            
            {S_VALID_1,M_READY_1}: begin  // Push a new item while popping; replace contents of output reg
              next = K_HAS1;
              load_mesg = 1'b1;
              push = 1'b0;
              m_valid_d = 1'b1;
            end
            
            default: begin  // s_valid=0, m_ready=0: hold state
              next = K_HAS1;
              load_mesg = 1'b0;
              push = 1'b0;
              m_valid_d = 1'b1;
            end
          endcase
        end  // HAS1
        
        K_MIN2: begin  // FIFO contains >1 item, some in SRL
          srl2mesg = 1'b1;
          m_valid_d = 1'b1;
          casex ({s_valid,m_ready})
            {S_VALID_1,M_READY_0}: begin  // Receive a new item, push into SRL
              next = K_MIN2;
              load_mesg = 1'b0;
              push = 1'b1;
              pop = 1'b0;
            end
            
            {S_VALID_0,M_READY_1}: begin  // Pop SRL to replace output reg
              next = (fifoaddr == P_ALMOSTEMPTY) ? K_HAS1 : K_MIN2;
              load_mesg = 1'b1;
              push = 1'b0;
              pop = 1'b1;
            end
            
            {S_VALID_1,M_READY_1}: begin  // Push a new item while popping
              next = K_MIN2;
              load_mesg = 1'b1;
              push = 1'b1;
              pop = 1'b1;
            end
            
            default: begin  // s_valid=0, m_ready=0: hold state
              next = K_MIN2;
              load_mesg = 1'b0;
              push = 1'b0;
              pop = 1'b0;
            end
          endcase
        end  // MIN2
        
        default: begin  // Same as RESET
          next = K_EMPTY;
        end  // default
      endcase
    end
    
    always @(posedge aclk) begin  // Payload reg needs no reset
      if (load_mesg) begin
        mesg_reg <= srl2mesg ? srl_reg : s_mesg;
      end
    end
        
    // SRL FIFO address pointer
    always @(posedge aclk) begin
      if (areset) begin
        fifoaddr <= P_EMPTY;
      end else begin
        if (push & ~pop) begin
          fifoaddr <= fifoaddr + 1;
        end else if (~push & pop) begin
          fifoaddr <= fifoaddr - 1;
        end
      end
    end
        
    //---------------------------------------------------------------------------
    // Instantiate SRLs
    //---------------------------------------------------------------------------
    for (i=0;i<C_FIFO_WIDTH;i=i+1) begin : srl
      (* keep_hierarchy = "yes" *) axi_register_slice_v2_1_18_srl_rtl #
        (
         .C_A_WIDTH (C_FIFO_SIZE)
        )
        srl_nx1
        (
         .clk (aclk),
         .a   (fifoaddr),
         .ce  (s_valid),
         .d   (s_mesg[i]),
         .q   (srl_reg[i])
        );
    end      
  endgenerate
  
endmodule  // axic_reg_srl_fifo


//  (c) Copyright 2010-2017 Xilinx, Inc. All rights reserved.
//
//  This file contains confidential and proprietary information
//  of Xilinx, Inc. and is protected under U.S. and
//  international copyright and other intellectual property
//  laws.
//
//  DISCLAIMER
//  This disclaimer is not a license and does not grant any
//  rights to the materials distributed herewith. Except as
//  otherwise provided in a valid license issued to you by
//  Xilinx, and to the maximum extent permitted by applicable
//  law: (1) THESE MATERIALS ARE MADE AVAILABLE "AS IS" AND
//  WITH ALL FAULTS, AND XILINX HEREBY DISCLAIMS ALL WARRANTIES
//  AND CONDITIONS, EXPRESS, IMPLIED, OR STATUTORY, INCLUDING
//  BUT NOT LIMITED TO WARRANTIES OF MERCHANTABILITY, NON-
//  INFRINGEMENT, OR FITNESS FOR ANY PARTICULAR PURPOSE; and
//  (2) Xilinx shall not be liable (whether in contract or tort,
//  including negligence, or under any other theory of
//  liability) for any loss or damage of any kind or nature
//  related to, arising under or in connection with these
//  materials, including for any direct, or any indirect,
//  special, incidental, or consequential loss or damage
//  (including loss of data, profits, goodwill, or any type of
//  loss or damage suffered as a result of any action brought
//  by a third party) even if such damage or loss was
//  reasonably foreseeable or Xilinx had been advised of the
//  possibility of the same.
//
//  CRITICAL APPLICATIONS
//  Xilinx products are not designed or intended to be fail-
//  safe, or for use in any application requiring fail-safe
//  performance, such as life-support or safety devices or
//  systems, Class III medical devices, nuclear facilities,
//  applications related to the deployment of airbags, or any
//  other applications that could lead to death, personal
//  injury, or severe property or environmental damage
//  (individually and collectively, "Critical
//  Applications"). Customer assumes the sole risk and
//  liability of any use of Xilinx products in Critical
//  Applications, subject only to applicable laws and
//  regulations governing limitations on product liability.
//
//  THIS COPYRIGHT NOTICE AND DISCLAIMER MUST BE RETAINED AS
//  PART OF THIS FILE AT ALL TIMES. 
//-----------------------------------------------------------------------------
//
// AXI Register Slice
//   Register selected channels on the forward and/or reverse signal paths.
//   5-channel memory-mapped AXI4 interfaces.
//
// Verilog-standard:  Verilog 2001
//--------------------------------------------------------------------------
//
// Structure:
//   axi_register_slice
//      axic_register_slice
//
//--------------------------------------------------------------------------

`timescale 1ps/1ps
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
