kangyuzhe666/ZYNQ7010-7020_AD9363/firmware/source project/pluto-7010clg400-user-ip/pluto/pluto.srcs/sources_1/bd/system/ip/system_sys_ps7_0/hdl/verilog/processing_system7_v5_5_processing_system7.v

 
//-----------------------------------------------------------------------------
// processing_system7
// processor sub system wrapper
//-----------------------------------------------------------------------------
//
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
//-----------------------------------------------------------------------------
// Filename:      processing_system7_v5_5_processing_system7.v
// Version:       v1.00.a
// Description:   This is the wrapper file for PSS. 
//-----------------------------------------------------------------------------
// Structure:   This section shows the hierarchical structure of 
//              pss_wrapper.
//
//              --processing_system7_v5_5_processing_system7.v
//                    --PS7.v - Unisim component
//-----------------------------------------------------------------------------
// Author:      SD
//
// History:
//
//  SD      09/20/11      -- First version
// ~~~~~~
// Created the first version v2.00.a
// ^^^^^^
//------------------------------------------------------------------------------
// ^^^^^^
//  SR     11/25/11       -- v3.00.a version
// ~~~~~~~
// Key changes are
// 1. Changed all clock, reset and clktrig ports to be individual
// signals instead of vectors. This is required for modeling of tools.
// 2. Interrupts are now defined as individual signals as well.
// 3. Added Clk buffer logic for FCLK_CLK
// 4. Includes the ACP related changes done
//
// TODO:
// 1. C_NUM_F2P_INTR_INPUTS needs to have control on the
//    number of interrupt ports connected for IRQ_F2P.
// 
//------------------------------------------------------------------------------
// ^^^^^^
//  KP     12/07/11       -- v3.00.a version
// ~~~~~~~
// Key changes are
//  C_NUM_F2P_INTR_INPUTS taken into account for IRQ_F2P
//------------------------------------------------------------------------------
// ^^^^^^
//  NR     12/09/11       -- v3.00.a version
// ~~~~~~~
// Key changes are
//  C_FCLK_CLK0_BUF to C_FCLK_CLK3_BUF parameters were updated 
//  to STRING and fix for CR 640523
//------------------------------------------------------------------------------
// ^^^^^^
//  NR     12/13/11       -- v3.00.a version
// ~~~~~~~
// Key changes are
// Updated IRQ_F2P logic to address CR 641523.
//------------------------------------------------------------------------------
// ^^^^^^
//  NR     02/01/12       -- v3.01.a version
// ~~~~~~~
// Key changes are
// Updated SDIO logic to address CR 636210.
//         |
//         Added C_PS7_SI_REV parameter to track SI Rev
// Removed compress/decompress logic to address CR 642527.
//------------------------------------------------------------------------------
// ^^^^^^
//  NR     02/27/12       -- v3.01.a version
// ~~~~~~~
// Key changes are
// TTC(0,1)_WAVE_OUT and TTC(0,1)_CLK_IN vector signals are made as individual 
// ports as fix for CR 646379
//------------------------------------------------------------------------------
// ^^^^^^
//  NR     03/05/12       -- v3.01.a version
// ~~~~~~~
// Key changes are
// Added/updated compress/decompress logic to address 648393
//------------------------------------------------------------------------------
// ^^^^^^
//  NR     03/14/12       -- v4.00.a version
// ~~~~~~~
// Unused parameters deleted CR 651120
// Addressed CR 651751
//------------------------------------------------------------------------------
// ^^^^^^
//  NR     04/17/12       -- v4.01.a version
// ~~~~~~~
// Added FTM trace buffer functionality
// Added support for ACP AxUSER ports local update
//------------------------------------------------------------------------------
// ^^^^^^
//  VR     05/18/12       -- v4.01.a version
// ~~~~~~~
// Fixed CR#659157
//------------------------------------------------------------------------------
// ^^^^^^
//  VR     07/25/12       -- v4.01.a version
// ~~~~~~~
// Changed S_AXI_HP{1,2}_WACOUNT port's width to 6 from 8 to match unisim model
// Changed fclk_clktrig_gnd width to 4 from 16 to match unisim model
//------------------------------------------------------------------------------
// ^^^^^^
//  VR     11/06/12       -- v5.00 version
// ~~~~~~~
// CR #682573
// Added BIBUF to fixed IO ports and IBUF to fixed input ports
//------------------------------------------------------------------------------
(*POWER= "<PROCESSOR name={system} numA9Cores={2} clockFreq={666.666666} load={0.5} /><MEMORY name={code} memType={DDR3} dataWidth={16} clockFreq={533.333333} readRate={0.5} writeRate={0.5} /><IO interface={GPIO_Bank_1} ioStandard={LVCMOS18} bidis={23} ioBank={Vcco_p1} clockFreq={1} usageRate={0.5} /><IO interface={GPIO_Bank_0} ioStandard={LVCMOS33} bidis={10} ioBank={Vcco_p0} clockFreq={1} usageRate={0.5} /><IO interface={SPI} ioStandard={} bidis={0} ioBank={} clockFreq={166.666672} usageRate={0.5} /><IO interface={UART} ioStandard={LVCMOS18} bidis={2} ioBank={Vcco_p1} clockFreq={100.000000} usageRate={0.5} /><IO interface={USB} ioStandard={LVCMOS18} bidis={12} ioBank={Vcco_p1} clockFreq={60} usageRate={0.5} /><IO interface={QSPI} ioStandard={LVCMOS33} bidis={6} ioBank={Vcco_p0} clockFreq={200} usageRate={0.5} /><PLL domain={Processor} vco={1333.333} /><PLL domain={Memory} vco={1066.667} /><PLL domain={IO} vco={1000.000} /><AXI interface={S_AXI_HP2} dataWidth={64} clockFreq={100} usageRate={0.5} /><AXI interface={S_AXI_HP1} dataWidth={64} clockFreq={100} usageRate={0.5} /><AXI interface={M_AXI_GP0} dataWidth={32} clockFreq={100} usageRate={0.5} />/>" *)
(* CORE_GENERATION_INFO = "processing_system7_v5.5 ,processing_system7_v5.5_user_configuration,{ PCW_UIPARAM_DDR_FREQ_MHZ=533.333333, PCW_UIPARAM_DDR_BANK_ADDR_COUNT=3, PCW_UIPARAM_DDR_ROW_ADDR_COUNT=15, PCW_UIPARAM_DDR_COL_ADDR_COUNT=10, PCW_UIPARAM_DDR_CL=7, PCW_UIPARAM_DDR_CWL=6, PCW_UIPARAM_DDR_T_RCD=7, PCW_UIPARAM_DDR_T_RP=7, PCW_UIPARAM_DDR_T_RC=48.75, PCW_UIPARAM_DDR_T_RAS_MIN=35.0, PCW_UIPARAM_DDR_T_FAW=40.0, PCW_UIPARAM_DDR_AL=0, PCW_UIPARAM_DDR_DQS_TO_CLK_DELAY_0=0.048, PCW_UIPARAM_DDR_DQS_TO_CLK_DELAY_1=0.050, PCW_UIPARAM_DDR_DQS_TO_CLK_DELAY_2=0.0, PCW_UIPARAM_DDR_DQS_TO_CLK_DELAY_3=0.0, PCW_UIPARAM_DDR_BOARD_DELAY0=0.241, PCW_UIPARAM_DDR_BOARD_DELAY1=0.240, PCW_UIPARAM_DDR_BOARD_DELAY2=0.25, PCW_UIPARAM_DDR_BOARD_DELAY3=0.25, PCW_UIPARAM_DDR_DQS_0_LENGTH_MM=0, PCW_UIPARAM_DDR_DQS_1_LENGTH_MM=0, PCW_UIPARAM_DDR_DQS_2_LENGTH_MM=0, PCW_UIPARAM_DDR_DQS_3_LENGTH_MM=0, PCW_UIPARAM_DDR_DQ_0_LENGTH_MM=0, PCW_UIPARAM_DDR_DQ_1_LENGTH_MM=0, PCW_UIPARAM_DDR_DQ_2_LENGTH_MM=0, PCW_UIPARAM_DDR_DQ_3_LENGTH_MM=0, PCW_UIPARAM_DDR_CLOCK_0_LENGTH_MM=0, PCW_UIPARAM_DDR_CLOCK_1_LENGTH_MM=0, PCW_UIPARAM_DDR_CLOCK_2_LENGTH_MM=0, PCW_UIPARAM_DDR_CLOCK_3_LENGTH_MM=0, PCW_UIPARAM_DDR_DQS_0_PACKAGE_LENGTH=101.239, PCW_UIPARAM_DDR_DQS_1_PACKAGE_LENGTH=79.5025, PCW_UIPARAM_DDR_DQS_2_PACKAGE_LENGTH=60.536, PCW_UIPARAM_DDR_DQS_3_PACKAGE_LENGTH=71.7715, PCW_UIPARAM_DDR_DQ_0_PACKAGE_LENGTH=104.5365, PCW_UIPARAM_DDR_DQ_1_PACKAGE_LENGTH=70.676, PCW_UIPARAM_DDR_DQ_2_PACKAGE_LENGTH=59.1615, PCW_UIPARAM_DDR_DQ_3_PACKAGE_LENGTH=81.319, PCW_UIPARAM_DDR_CLOCK_0_PACKAGE_LENGTH=54.563, PCW_UIPARAM_DDR_CLOCK_1_PACKAGE_LENGTH=54.563, PCW_UIPARAM_DDR_CLOCK_2_PACKAGE_LENGTH=54.563, PCW_UIPARAM_DDR_CLOCK_3_PACKAGE_LENGTH=54.563, PCW_UIPARAM_DDR_DQS_0_PROPOGATION_DELAY=160, PCW_UIPARAM_DDR_DQS_1_PROPOGATION_DELAY=160, PCW_UIPARAM_DDR_DQS_2_PROPOGATION_DELAY=160, PCW_UIPARAM_DDR_DQS_3_PROPOGATION_DELAY=160, PCW_UIPARAM_DDR_DQ_0_PROPOGATION_DELAY=160, PCW_UIPARAM_DDR_DQ_1_PROPOGATION_DELAY=160\
, PCW_UIPARAM_DDR_DQ_2_PROPOGATION_DELAY=160, PCW_UIPARAM_DDR_DQ_3_PROPOGATION_DELAY=160, PCW_UIPARAM_DDR_CLOCK_0_PROPOGATION_DELAY=160, PCW_UIPARAM_DDR_CLOCK_1_PROPOGATION_DELAY=160, PCW_UIPARAM_DDR_CLOCK_2_PROPOGATION_DELAY=160, PCW_UIPARAM_DDR_CLOCK_3_PROPOGATION_DELAY=160, PCW_CRYSTAL_PERIPHERAL_FREQMHZ=33.333333, PCW_APU_PERIPHERAL_FREQMHZ=666.666666, PCW_DCI_PERIPHERAL_FREQMHZ=10.159, PCW_QSPI_PERIPHERAL_FREQMHZ=200, PCW_SMC_PERIPHERAL_FREQMHZ=100, PCW_USB0_PERIPHERAL_FREQMHZ=60, PCW_USB1_PERIPHERAL_FREQMHZ=60, PCW_SDIO_PERIPHERAL_FREQMHZ=100, PCW_UART_PERIPHERAL_FREQMHZ=100, PCW_SPI_PERIPHERAL_FREQMHZ=166.666666, PCW_CAN_PERIPHERAL_FREQMHZ=100, PCW_CAN0_PERIPHERAL_FREQMHZ=-1, PCW_CAN1_PERIPHERAL_FREQMHZ=-1, PCW_WDT_PERIPHERAL_FREQMHZ=133.333333, PCW_TTC_PERIPHERAL_FREQMHZ=50, PCW_TTC0_CLK0_PERIPHERAL_FREQMHZ=133.333333, PCW_TTC0_CLK1_PERIPHERAL_FREQMHZ=133.333333, PCW_TTC0_CLK2_PERIPHERAL_FREQMHZ=133.333333, PCW_TTC1_CLK0_PERIPHERAL_FREQMHZ=133.333333, PCW_TTC1_CLK1_PERIPHERAL_FREQMHZ=133.333333, PCW_TTC1_CLK2_PERIPHERAL_FREQMHZ=133.333333, PCW_PCAP_PERIPHERAL_FREQMHZ=200, PCW_TPIU_PERIPHERAL_FREQMHZ=200, PCW_FPGA0_PERIPHERAL_FREQMHZ=100.0, PCW_FPGA1_PERIPHERAL_FREQMHZ=200.0, PCW_FPGA2_PERIPHERAL_FREQMHZ=50, PCW_FPGA3_PERIPHERAL_FREQMHZ=50, PCW_OVERRIDE_BASIC_CLOCK=0, PCW_ARMPLL_CTRL_FBDIV=40, PCW_IOPLL_CTRL_FBDIV=30, PCW_DDRPLL_CTRL_FBDIV=32, PCW_CPU_CPU_PLL_FREQMHZ=1333.333, PCW_IO_IO_PLL_FREQMHZ=1000.000, PCW_DDR_DDR_PLL_FREQMHZ=1066.667, PCW_USE_M_AXI_GP0=1, PCW_USE_M_AXI_GP1=0, PCW_USE_S_AXI_GP0=0, PCW_USE_S_AXI_GP1=0, PCW_USE_S_AXI_ACP=0, PCW_USE_S_AXI_HP0=0, PCW_USE_S_AXI_HP1=1, PCW_USE_S_AXI_HP2=1, PCW_USE_S_AXI_HP3=0, PCW_M_AXI_GP0_FREQMHZ=100\
, PCW_M_AXI_GP1_FREQMHZ=10, PCW_S_AXI_GP0_FREQMHZ=10, PCW_S_AXI_GP1_FREQMHZ=10, PCW_S_AXI_ACP_FREQMHZ=10, PCW_S_AXI_HP0_FREQMHZ=10, PCW_S_AXI_HP1_FREQMHZ=100, PCW_S_AXI_HP2_FREQMHZ=100, PCW_S_AXI_HP3_FREQMHZ=10, PCW_USE_CROSS_TRIGGER=0, PCW_FTM_CTI_IN0=DISABLED, PCW_FTM_CTI_IN1=DISABLED, PCW_FTM_CTI_IN2=DISABLED, PCW_FTM_CTI_IN3=DISABLED, PCW_FTM_CTI_OUT0=DISABLED, PCW_FTM_CTI_OUT1=DISABLED, PCW_FTM_CTI_OUT2=DISABLED, PCW_FTM_CTI_OUT3=DISABLED, PCW_UART0_BAUD_RATE=115200, PCW_UART1_BAUD_RATE=115200, PCW_S_AXI_HP0_DATA_WIDTH=64, PCW_S_AXI_HP1_DATA_WIDTH=64, PCW_S_AXI_HP2_DATA_WIDTH=64, PCW_S_AXI_HP3_DATA_WIDTH=64, PCW_IRQ_F2P_MODE=REVERSE, PCW_PRESET_BANK0_VOLTAGE=LVCMOS 3.3V, PCW_PRESET_BANK1_VOLTAGE=LVCMOS 1.8V, PCW_UIPARAM_DDR_ENABLE=1, PCW_UIPARAM_DDR_ADV_ENABLE=0, PCW_UIPARAM_DDR_MEMORY_TYPE=DDR 3, PCW_UIPARAM_DDR_ECC=Disabled, PCW_UIPARAM_DDR_BUS_WIDTH=16 Bit, PCW_UIPARAM_DDR_BL=8, PCW_UIPARAM_DDR_HIGH_TEMP=Normal (0-85), PCW_UIPARAM_DDR_PARTNO=MT41K256M16 RE-125, PCW_UIPARAM_DDR_DRAM_WIDTH=16 Bits, PCW_UIPARAM_DDR_DEVICE_CAPACITY=4096 MBits, PCW_UIPARAM_DDR_SPEED_BIN=DDR3_1066F, PCW_UIPARAM_DDR_TRAIN_WRITE_LEVEL=1, PCW_UIPARAM_DDR_TRAIN_READ_GATE=1, PCW_UIPARAM_DDR_TRAIN_DATA_EYE=1, PCW_UIPARAM_DDR_CLOCK_STOP_EN=0, PCW_UIPARAM_DDR_USE_INTERNAL_VREF=0, PCW_DDR_PORT0_HPR_ENABLE=0, PCW_DDR_PORT1_HPR_ENABLE=0, PCW_DDR_PORT2_HPR_ENABLE=0, PCW_DDR_PORT3_HPR_ENABLE=0, PCW_DDR_HPRLPR_QUEUE_PARTITION=HPR(0)/LPR(32), PCW_DDR_LPR_TO_CRITICAL_PRIORITY_LEVEL=2, PCW_DDR_HPR_TO_CRITICAL_PRIORITY_LEVEL=15, PCW_DDR_WRITE_TO_CRITICAL_PRIORITY_LEVEL=2\
, PCW_NAND_PERIPHERAL_ENABLE=0, PCW_NAND_GRP_D8_ENABLE=0, PCW_NOR_PERIPHERAL_ENABLE=0, PCW_NOR_GRP_A25_ENABLE=0, PCW_NOR_GRP_CS0_ENABLE=0, PCW_NOR_GRP_SRAM_CS0_ENABLE=0, PCW_NOR_GRP_CS1_ENABLE=0, PCW_NOR_GRP_SRAM_CS1_ENABLE=0, PCW_NOR_GRP_SRAM_INT_ENABLE=0, PCW_QSPI_PERIPHERAL_ENABLE=1, PCW_QSPI_QSPI_IO=MIO 1 .. 6, PCW_QSPI_GRP_SINGLE_SS_ENABLE=1, PCW_QSPI_GRP_SINGLE_SS_IO=MIO 1 .. 6, PCW_QSPI_GRP_SS1_ENABLE=0, PCW_QSPI_GRP_IO1_ENABLE=0, PCW_QSPI_GRP_FBCLK_ENABLE=0, PCW_QSPI_INTERNAL_HIGHADDRESS=0xFCFFFFFF, PCW_SINGLE_QSPI_DATA_MODE=x4, PCW_ENET0_PERIPHERAL_ENABLE=0, PCW_ENET0_GRP_MDIO_ENABLE=0, PCW_ENET0_RESET_ENABLE=0, PCW_ENET1_PERIPHERAL_ENABLE=0, PCW_ENET1_GRP_MDIO_ENABLE=0, PCW_ENET1_RESET_ENABLE=0, PCW_SD0_PERIPHERAL_ENABLE=0, PCW_SD0_GRP_CD_ENABLE=0, PCW_SD0_GRP_WP_ENABLE=0, PCW_SD0_GRP_POW_ENABLE=0, PCW_SD1_PERIPHERAL_ENABLE=0, PCW_SD1_GRP_CD_ENABLE=0, PCW_SD1_GRP_WP_ENABLE=0, PCW_SD1_GRP_POW_ENABLE=0, PCW_UART0_PERIPHERAL_ENABLE=0, PCW_UART0_GRP_FULL_ENABLE=0, PCW_UART1_PERIPHERAL_ENABLE=1, PCW_UART1_UART1_IO=MIO 48 .. 49, PCW_UART1_GRP_FULL_ENABLE=0, PCW_SPI0_PERIPHERAL_ENABLE=1, PCW_SPI0_SPI0_IO=EMIO, PCW_SPI0_GRP_SS0_ENABLE=1, PCW_SPI0_GRP_SS0_IO=EMIO, PCW_SPI0_GRP_SS1_ENABLE=1, PCW_SPI0_GRP_SS1_IO=EMIO, PCW_SPI0_GRP_SS2_ENABLE=1, PCW_SPI0_GRP_SS2_IO=EMIO, PCW_SPI1_PERIPHERAL_ENABLE=0, PCW_SPI1_GRP_SS0_ENABLE=0, PCW_SPI1_GRP_SS1_ENABLE=0, PCW_SPI1_GRP_SS2_ENABLE=0, PCW_CAN0_PERIPHERAL_ENABLE=0\
, PCW_CAN0_GRP_CLK_ENABLE=0, PCW_CAN1_PERIPHERAL_ENABLE=0, PCW_CAN1_GRP_CLK_ENABLE=0, PCW_TRACE_PERIPHERAL_ENABLE=0, PCW_TRACE_GRP_2BIT_ENABLE=0, PCW_TRACE_GRP_4BIT_ENABLE=0, PCW_TRACE_GRP_8BIT_ENABLE=0, PCW_TRACE_GRP_16BIT_ENABLE=0, PCW_TRACE_GRP_32BIT_ENABLE=0, PCW_WDT_PERIPHERAL_ENABLE=0, PCW_TTC0_PERIPHERAL_ENABLE=0, PCW_TTC1_PERIPHERAL_ENABLE=0, PCW_PJTAG_PERIPHERAL_ENABLE=0, PCW_USB0_PERIPHERAL_ENABLE=1, PCW_USB0_USB0_IO=MIO 28 .. 39, PCW_USB0_RESET_ENABLE=1, PCW_USB0_RESET_IO=MIO 46, PCW_USB1_PERIPHERAL_ENABLE=0, PCW_USB1_RESET_ENABLE=0, PCW_I2C0_PERIPHERAL_ENABLE=0, PCW_I2C0_GRP_INT_ENABLE=0, PCW_I2C0_RESET_ENABLE=0, PCW_I2C1_PERIPHERAL_ENABLE=0, PCW_I2C1_GRP_INT_ENABLE=0, PCW_I2C1_RESET_ENABLE=0, PCW_GPIO_PERIPHERAL_ENABLE=0, PCW_GPIO_MIO_GPIO_ENABLE=1, PCW_GPIO_MIO_GPIO_IO=MIO, PCW_GPIO_EMIO_GPIO_ENABLE=1, PCW_GPIO_EMIO_GPIO_IO=17, PCW_APU_CLK_RATIO_ENABLE=6:2:1, PCW_ENET0_PERIPHERAL_FREQMHZ=1000 Mbps, PCW_ENET1_PERIPHERAL_FREQMHZ=1000 Mbps, PCW_CPU_PERIPHERAL_CLKSRC=ARM PLL, PCW_DDR_PERIPHERAL_CLKSRC=DDR PLL, PCW_SMC_PERIPHERAL_CLKSRC=IO PLL, PCW_QSPI_PERIPHERAL_CLKSRC=IO PLL, PCW_SDIO_PERIPHERAL_CLKSRC=IO PLL, PCW_UART_PERIPHERAL_CLKSRC=IO PLL, PCW_SPI_PERIPHERAL_CLKSRC=IO PLL, PCW_CAN_PERIPHERAL_CLKSRC=IO PLL, PCW_FCLK0_PERIPHERAL_CLKSRC=IO PLL, PCW_FCLK1_PERIPHERAL_CLKSRC=IO PLL, PCW_FCLK2_PERIPHERAL_CLKSRC=IO PLL, PCW_FCLK3_PERIPHERAL_CLKSRC=IO PLL, PCW_ENET0_PERIPHERAL_CLKSRC=IO PLL, PCW_ENET1_PERIPHERAL_CLKSRC=IO PLL, PCW_CAN0_PERIPHERAL_CLKSRC=External, PCW_CAN1_PERIPHERAL_CLKSRC=External, PCW_TPIU_PERIPHERAL_CLKSRC=External\
, PCW_TTC0_CLK0_PERIPHERAL_CLKSRC=CPU_1X, PCW_TTC0_CLK1_PERIPHERAL_CLKSRC=CPU_1X, PCW_TTC0_CLK2_PERIPHERAL_CLKSRC=CPU_1X, PCW_TTC1_CLK0_PERIPHERAL_CLKSRC=CPU_1X, PCW_TTC1_CLK1_PERIPHERAL_CLKSRC=CPU_1X, PCW_TTC1_CLK2_PERIPHERAL_CLKSRC=CPU_1X, PCW_WDT_PERIPHERAL_CLKSRC=CPU_1X, PCW_DCI_PERIPHERAL_CLKSRC=DDR PLL, PCW_PCAP_PERIPHERAL_CLKSRC=IO PLL, PCW_USB_RESET_POLARITY=Active Low, PCW_ENET_RESET_POLARITY=Active Low, PCW_I2C_RESET_POLARITY=Active Low, PCW_FPGA_FCLK0_ENABLE=1, PCW_FPGA_FCLK1_ENABLE=1, PCW_FPGA_FCLK2_ENABLE=0, PCW_FPGA_FCLK3_ENABLE=0, PCW_NOR_SRAM_CS0_T_TR=1, PCW_NOR_SRAM_CS0_T_PC=1, PCW_NOR_SRAM_CS0_T_WP=1, PCW_NOR_SRAM_CS0_T_CEOE=1, PCW_NOR_SRAM_CS0_T_WC=11, PCW_NOR_SRAM_CS0_T_RC=11, PCW_NOR_SRAM_CS0_WE_TIME=0, PCW_NOR_SRAM_CS1_T_TR=1, PCW_NOR_SRAM_CS1_T_PC=1, PCW_NOR_SRAM_CS1_T_WP=1, PCW_NOR_SRAM_CS1_T_CEOE=1, PCW_NOR_SRAM_CS1_T_WC=11, PCW_NOR_SRAM_CS1_T_RC=11, PCW_NOR_SRAM_CS1_WE_TIME=0, PCW_NOR_CS0_T_TR=1, PCW_NOR_CS0_T_PC=1, PCW_NOR_CS0_T_WP=1, PCW_NOR_CS0_T_CEOE=1, PCW_NOR_CS0_T_WC=11, PCW_NOR_CS0_T_RC=11, PCW_NOR_CS0_WE_TIME=0, PCW_NOR_CS1_T_TR=1, PCW_NOR_CS1_T_PC=1, PCW_NOR_CS1_T_WP=1, PCW_NOR_CS1_T_CEOE=1, PCW_NOR_CS1_T_WC=11, PCW_NOR_CS1_T_RC=11, PCW_NOR_CS1_WE_TIME=0, PCW_NAND_CYCLES_T_RR=1, PCW_NAND_CYCLES_T_AR=1, PCW_NAND_CYCLES_T_CLR=1, PCW_NAND_CYCLES_T_WP=1, PCW_NAND_CYCLES_T_REA=1, PCW_NAND_CYCLES_T_WC=11\
, PCW_NAND_CYCLES_T_RC=11 }" *)  
(* HW_HANDOFF = "system_sys_ps7_0.hwdef" *)  

module processing_system7_v5_5_processing_system7

#(
  parameter integer C_USE_DEFAULT_ACP_USER_VAL = 1,
  parameter integer C_S_AXI_ACP_ARUSER_VAL = 31,
  parameter integer C_S_AXI_ACP_AWUSER_VAL = 31,
  parameter integer C_M_AXI_GP0_THREAD_ID_WIDTH = 12,
  parameter integer C_M_AXI_GP1_THREAD_ID_WIDTH = 12, 
  parameter integer C_M_AXI_GP0_ENABLE_STATIC_REMAP = 1,
  parameter integer C_M_AXI_GP1_ENABLE_STATIC_REMAP = 1, 
  parameter integer C_M_AXI_GP0_ID_WIDTH = 12,
  parameter integer C_M_AXI_GP1_ID_WIDTH = 12,
  parameter integer C_S_AXI_GP0_ID_WIDTH = 6,
  parameter integer C_S_AXI_GP1_ID_WIDTH = 6,
  parameter integer C_S_AXI_HP0_ID_WIDTH = 6,
  parameter integer C_S_AXI_HP1_ID_WIDTH = 6,
  parameter integer C_S_AXI_HP2_ID_WIDTH = 6,
  parameter integer C_S_AXI_HP3_ID_WIDTH = 6,
  parameter integer C_S_AXI_ACP_ID_WIDTH = 3,
  parameter integer C_S_AXI_HP0_DATA_WIDTH = 64,
  parameter integer C_S_AXI_HP1_DATA_WIDTH = 64,
  parameter integer C_S_AXI_HP2_DATA_WIDTH = 64,
  parameter integer C_S_AXI_HP3_DATA_WIDTH = 64,
  parameter integer C_INCLUDE_ACP_TRANS_CHECK = 0,
  parameter integer C_NUM_F2P_INTR_INPUTS = 1,
  parameter         C_FCLK_CLK0_BUF = "TRUE",
  parameter         C_FCLK_CLK1_BUF = "TRUE",
  parameter         C_FCLK_CLK2_BUF = "TRUE",
  parameter         C_FCLK_CLK3_BUF = "TRUE",
  parameter integer C_EMIO_GPIO_WIDTH = 64,
  parameter integer C_INCLUDE_TRACE_BUFFER = 0,
  parameter integer C_TRACE_BUFFER_FIFO_SIZE = 128,
  parameter integer C_TRACE_BUFFER_CLOCK_DELAY = 12,
  parameter integer USE_TRACE_DATA_EDGE_DETECTOR = 0,
  parameter integer C_TRACE_PIPELINE_WIDTH = 8,
  parameter         C_PS7_SI_REV = "PRODUCTION",
  parameter integer C_EN_EMIO_ENET0 = 0,
  parameter integer C_EN_EMIO_ENET1 = 0,
  parameter integer C_EN_EMIO_TRACE = 0,
  parameter integer C_DQ_WIDTH = 32,
  parameter integer C_DQS_WIDTH = 4,
  parameter integer C_DM_WIDTH = 4,
  parameter integer C_MIO_PRIMITIVE = 54,
  parameter	    C_PACKAGE_NAME = "clg484",
  parameter C_IRQ_F2P_MODE = "DIRECT",
  parameter C_TRACE_INTERNAL_WIDTH = 32,
  parameter integer C_EN_EMIO_PJTAG = 0,
  
  // Enable and disable AFI Secure transaction 
  parameter C_USE_AXI_NONSECURE = 0,
  
  //parameters for HP enable ports 
  parameter C_USE_S_AXI_HP0 = 0,
  parameter C_USE_S_AXI_HP1 = 0,
  parameter C_USE_S_AXI_HP2 = 0,
  parameter C_USE_S_AXI_HP3 = 0,
  
  //parameters for GP and ACP enable ports */
  parameter C_USE_M_AXI_GP0 = 0,
  parameter C_USE_M_AXI_GP1 = 0,
  parameter C_USE_S_AXI_GP0 = 0,
  parameter C_USE_S_AXI_GP1 = 0,
  parameter C_USE_S_AXI_ACP = 0,
  parameter C_GP0_EN_MODIFIABLE_TXN=0,
  parameter C_GP1_EN_MODIFIABLE_TXN=0
   
)
(
  //FMIO =========================================
  
  //FMIO CAN0
  output          CAN0_PHY_TX,
  input           CAN0_PHY_RX,

  //FMIO CAN1
  output          CAN1_PHY_TX,  
  input           CAN1_PHY_RX,
  
  //FMIO ENET0
  output  reg     ENET0_GMII_TX_EN = 'b0,
  output  reg     ENET0_GMII_TX_ER = 'b0,
  output          ENET0_MDIO_MDC,
  output          ENET0_MDIO_O,
  output          ENET0_MDIO_T,
  output          ENET0_PTP_DELAY_REQ_RX,
  output          ENET0_PTP_DELAY_REQ_TX,
  output          ENET0_PTP_PDELAY_REQ_RX,
  output          ENET0_PTP_PDELAY_REQ_TX,
  output          ENET0_PTP_PDELAY_RESP_RX,
  output          ENET0_PTP_PDELAY_RESP_TX,
  output          ENET0_PTP_SYNC_FRAME_RX,
  output          ENET0_PTP_SYNC_FRAME_TX,
  output          ENET0_SOF_RX,
  output          ENET0_SOF_TX,
  
  
  output  reg [7:0]    ENET0_GMII_TXD,  

  
  input           ENET0_GMII_COL,
  input           ENET0_GMII_CRS,
  input           ENET0_GMII_RX_CLK,
  input           ENET0_GMII_RX_DV,
  input           ENET0_GMII_RX_ER,
  input           ENET0_GMII_TX_CLK,
  input           ENET0_MDIO_I,
  input           ENET0_EXT_INTIN,
  input [7:0]     ENET0_GMII_RXD,  

  //FMIO ENET1
  output   reg    ENET1_GMII_TX_EN = 'b0,
  output   reg    ENET1_GMII_TX_ER = 'b0,
  output          ENET1_MDIO_MDC,
  output          ENET1_MDIO_O,
  output          ENET1_MDIO_T,
  output          ENET1_PTP_DELAY_REQ_RX,
  output          ENET1_PTP_DELAY_REQ_TX,
  output          ENET1_PTP_PDELAY_REQ_RX,
  output          ENET1_PTP_PDELAY_REQ_TX,
  output          ENET1_PTP_PDELAY_RESP_RX,
  output          ENET1_PTP_PDELAY_RESP_TX,
  output          ENET1_PTP_SYNC_FRAME_RX,
  output          ENET1_PTP_SYNC_FRAME_TX,
  output          ENET1_SOF_RX,
  output          ENET1_SOF_TX,
  output reg [7:0]    ENET1_GMII_TXD,  

  input          ENET1_GMII_COL,
  input          ENET1_GMII_CRS,
  input          ENET1_GMII_RX_CLK,
  input          ENET1_GMII_RX_DV,
  input          ENET1_GMII_RX_ER,
  input          ENET1_GMII_TX_CLK,
  input          ENET1_MDIO_I,
  input          ENET1_EXT_INTIN,  
  input [7:0]    ENET1_GMII_RXD,
  
  //FMIO GPIO
  input    [(C_EMIO_GPIO_WIDTH-1):0] GPIO_I,
  output   [(C_EMIO_GPIO_WIDTH-1):0] GPIO_O,
  output   [(C_EMIO_GPIO_WIDTH-1):0] GPIO_T,  
  
  //FMIO I2C0
  input           I2C0_SDA_I,
  output          I2C0_SDA_O,
  output          I2C0_SDA_T,
  input           I2C0_SCL_I,
  output          I2C0_SCL_O,
  output          I2C0_SCL_T,

  //FMIO I2C1
  input           I2C1_SDA_I,
  output          I2C1_SDA_O,
  output          I2C1_SDA_T,
  input           I2C1_SCL_I,
  output          I2C1_SCL_O,
  output          I2C1_SCL_T,
  
  //FMIO PJTAG
  input           PJTAG_TCK,
  input           PJTAG_TMS,
  input           PJTAG_TDI,
  output          PJTAG_TDO,

  
  //FMIO SDIO0
  output          SDIO0_CLK,
  input           SDIO0_CLK_FB,
  output          SDIO0_CMD_O,
  input           SDIO0_CMD_I,
  output          SDIO0_CMD_T,
  input     [3:0] SDIO0_DATA_I,
  output    [3:0] SDIO0_DATA_O,
  output    [3:0] SDIO0_DATA_T,
  output          SDIO0_LED,
  input           SDIO0_CDN,
  input           SDIO0_WP,  
  output          SDIO0_BUSPOW,
  output    [2:0] SDIO0_BUSVOLT,

  //FMIO SDIO1
  output          SDIO1_CLK,
  input           SDIO1_CLK_FB,
  output          SDIO1_CMD_O,
  input           SDIO1_CMD_I,
  output          SDIO1_CMD_T,
  input     [3:0] SDIO1_DATA_I,
  output    [3:0] SDIO1_DATA_O,
  output    [3:0] SDIO1_DATA_T,  
  output          SDIO1_LED,
  input           SDIO1_CDN,  
  input           SDIO1_WP,
  output          SDIO1_BUSPOW,  
  output    [2:0] SDIO1_BUSVOLT,

  //FMIO SPI0
  input           SPI0_SCLK_I,
  output          SPI0_SCLK_O,
  output          SPI0_SCLK_T,
  input           SPI0_MOSI_I,
  output          SPI0_MOSI_O,
  output          SPI0_MOSI_T,
  input           SPI0_MISO_I,
  output          SPI0_MISO_O,
  output          SPI0_MISO_T,
  input           SPI0_SS_I,
  output          SPI0_SS_O,
  output          SPI0_SS1_O,
  output          SPI0_SS2_O,
  output          SPI0_SS_T,

  //FMIO SPI1
  input           SPI1_SCLK_I,
  output          SPI1_SCLK_O,
  output          SPI1_SCLK_T,
  input           SPI1_MOSI_I,
  output          SPI1_MOSI_O,
  output          SPI1_MOSI_T,
  input           SPI1_MISO_I,
  output          SPI1_MISO_O,
  output          SPI1_MISO_T,
  input           SPI1_SS_I,
  output          SPI1_SS_O,
  output          SPI1_SS1_O,
  output          SPI1_SS2_O,  
  output          SPI1_SS_T,

  //FMIO UART0
  output          UART0_DTRN,
  output          UART0_RTSN,  
  output          UART0_TX,
  input           UART0_CTSN,
  input           UART0_DCDN,
  input           UART0_DSRN,
  input           UART0_RIN,  
  input           UART0_RX,

  //FMIO UART1
  output          UART1_DTRN,
  output          UART1_RTSN,  
  output          UART1_TX,
  input           UART1_CTSN,
  input           UART1_DCDN,
  input           UART1_DSRN,
  input           UART1_RIN,  
  input           UART1_RX,

  //FMIO TTC0
  output    		TTC0_WAVE0_OUT,
  output    		TTC0_WAVE1_OUT,
  output    		TTC0_WAVE2_OUT,
  input     		TTC0_CLK0_IN,
  input     		TTC0_CLK1_IN,
  input     		TTC0_CLK2_IN,

  //FMIO TTC1
  output    		TTC1_WAVE0_OUT,
  output    		TTC1_WAVE1_OUT,
  output    		TTC1_WAVE2_OUT,
  input     		TTC1_CLK0_IN,
  input     		TTC1_CLK1_IN,
  input     		TTC1_CLK2_IN,

  //WDT
  input           WDT_CLK_IN,
  output          WDT_RST_OUT,

  //FTPORT
  input           TRACE_CLK,
  output          TRACE_CTL,
  output   [(C_TRACE_INTERNAL_WIDTH)-1:0] TRACE_DATA,
  output   reg		  TRACE_CLK_OUT,
  
  // USB
  output   [1:0]  USB0_PORT_INDCTL,
  output          USB0_VBUS_PWRSELECT,
  input           USB0_VBUS_PWRFAULT,

  output   [1:0]  USB1_PORT_INDCTL,
  output          USB1_VBUS_PWRSELECT,
  input           USB1_VBUS_PWRFAULT,
  
  input           SRAM_INTIN,

  //AIO ===================================================

  //M_AXI_GP0
  
  // -- Output
  
  output M_AXI_GP0_ARESETN,
  output M_AXI_GP0_ARVALID,
  output M_AXI_GP0_AWVALID,
  output M_AXI_GP0_BREADY,
  output M_AXI_GP0_RREADY,
  output M_AXI_GP0_WLAST,
  output M_AXI_GP0_WVALID,
  output [(C_M_AXI_GP0_THREAD_ID_WIDTH - 1):0] M_AXI_GP0_ARID,
  output [(C_M_AXI_GP0_THREAD_ID_WIDTH - 1):0] M_AXI_GP0_AWID,
  output [(C_M_AXI_GP0_THREAD_ID_WIDTH - 1):0] M_AXI_GP0_WID,
  output [1:0] M_AXI_GP0_ARBURST,
  output [1:0] M_AXI_GP0_ARLOCK,
  output [2:0] M_AXI_GP0_ARSIZE,
  output [1:0] M_AXI_GP0_AWBURST,
  output [1:0] M_AXI_GP0_AWLOCK,
  output [2:0] M_AXI_GP0_AWSIZE,
  output [2:0] M_AXI_GP0_ARPROT,
  output [2:0] M_AXI_GP0_AWPROT,
  output [31:0] M_AXI_GP0_ARADDR,
  output [31:0] M_AXI_GP0_AWADDR,
  output [31:0] M_AXI_GP0_WDATA,
  output [3:0] M_AXI_GP0_ARCACHE,
  output [3:0] M_AXI_GP0_ARLEN,
  output [3:0] M_AXI_GP0_ARQOS,
  output [3:0] M_AXI_GP0_AWCACHE,
  output [3:0] M_AXI_GP0_AWLEN,
  output [3:0] M_AXI_GP0_AWQOS,
  output [3:0] M_AXI_GP0_WSTRB, 
  
  // -- Input  
  
  input M_AXI_GP0_ACLK,
  input M_AXI_GP0_ARREADY,
  input M_AXI_GP0_AWREADY,
  input M_AXI_GP0_BVALID,
  input M_AXI_GP0_RLAST,
  input M_AXI_GP0_RVALID,
  input M_AXI_GP0_WREADY,
  input [(C_M_AXI_GP0_THREAD_ID_WIDTH - 1):0] M_AXI_GP0_BID,
  input [(C_M_AXI_GP0_THREAD_ID_WIDTH - 1):0] M_AXI_GP0_RID,
  input [1:0] M_AXI_GP0_BRESP,
  input [1:0] M_AXI_GP0_RRESP,
  input [31:0] M_AXI_GP0_RDATA,  


  //M_AXI_GP1
  
  // -- Output

  output M_AXI_GP1_ARESETN,
  output M_AXI_GP1_ARVALID,
  output M_AXI_GP1_AWVALID,
  output M_AXI_GP1_BREADY,
  output M_AXI_GP1_RREADY,
  output M_AXI_GP1_WLAST,
  output M_AXI_GP1_WVALID,
  output [(C_M_AXI_GP1_THREAD_ID_WIDTH - 1):0] M_AXI_GP1_ARID,
  output [(C_M_AXI_GP1_THREAD_ID_WIDTH - 1):0] M_AXI_GP1_AWID,
  output [(C_M_AXI_GP1_THREAD_ID_WIDTH - 1):0] M_AXI_GP1_WID,
  output [1:0] M_AXI_GP1_ARBURST,
  output [1:0] M_AXI_GP1_ARLOCK,
  output [2:0] M_AXI_GP1_ARSIZE,
  output [1:0] M_AXI_GP1_AWBURST,
  output [1:0] M_AXI_GP1_AWLOCK,
  output [2:0] M_AXI_GP1_AWSIZE,
  output [2:0] M_AXI_GP1_ARPROT,
  output [2:0] M_AXI_GP1_AWPROT,
  output [31:0] M_AXI_GP1_ARADDR,
  output [31:0] M_AXI_GP1_AWADDR,
  output [31:0] M_AXI_GP1_WDATA,
  output [3:0] M_AXI_GP1_ARCACHE,
  output [3:0] M_AXI_GP1_ARLEN,
  output [3:0] M_AXI_GP1_ARQOS,
  output [3:0] M_AXI_GP1_AWCACHE,
  output [3:0] M_AXI_GP1_AWLEN,
  output [3:0] M_AXI_GP1_AWQOS,
  output [3:0] M_AXI_GP1_WSTRB,
  
  // -- Input
  
  input M_AXI_GP1_ACLK,
  input M_AXI_GP1_ARREADY,
  input M_AXI_GP1_AWREADY,
  input M_AXI_GP1_BVALID,
  input M_AXI_GP1_RLAST,
  input M_AXI_GP1_RVALID,
  input M_AXI_GP1_WREADY,  
  input [(C_M_AXI_GP1_THREAD_ID_WIDTH - 1):0] M_AXI_GP1_BID,
  input [(C_M_AXI_GP1_THREAD_ID_WIDTH - 1):0] M_AXI_GP1_RID,
  input [1:0] M_AXI_GP1_BRESP,
  input [1:0] M_AXI_GP1_RRESP,
  input [31:0] M_AXI_GP1_RDATA,  
  

  // S_AXI_GP0
  
  // -- Output
  
  output S_AXI_GP0_ARESETN,
  output S_AXI_GP0_ARREADY,
  output S_AXI_GP0_AWREADY,
  output S_AXI_GP0_BVALID,
  output S_AXI_GP0_RLAST,
  output S_AXI_GP0_RVALID,
  output S_AXI_GP0_WREADY,  
  output [1:0] S_AXI_GP0_BRESP,
  output [1:0] S_AXI_GP0_RRESP,
  output [31:0] S_AXI_GP0_RDATA,
  output [(C_S_AXI_GP0_ID_WIDTH - 1) : 0] S_AXI_GP0_BID,
  output [(C_S_AXI_GP0_ID_WIDTH - 1) : 0] S_AXI_GP0_RID,
  
  // -- Input
  input S_AXI_GP0_ACLK,
  input S_AXI_GP0_ARVALID,
  input S_AXI_GP0_AWVALID,
  input S_AXI_GP0_BREADY,
  input S_AXI_GP0_RREADY,
  input S_AXI_GP0_WLAST,
  input S_AXI_GP0_WVALID,
  input [1:0] S_AXI_GP0_ARBURST,
  input [1:0] S_AXI_GP0_ARLOCK,
  input [2:0] S_AXI_GP0_ARSIZE,
  input [1:0] S_AXI_GP0_AWBURST,
  input [1:0] S_AXI_GP0_AWLOCK,
  input [2:0] S_AXI_GP0_AWSIZE,
  input [2:0] S_AXI_GP0_ARPROT,
  input [2:0] S_AXI_GP0_AWPROT,
  input [31:0] S_AXI_GP0_ARADDR,
  input [31:0] S_AXI_GP0_AWADDR,
  input [31:0] S_AXI_GP0_WDATA,
  input [3:0] S_AXI_GP0_ARCACHE,
  input [3:0] S_AXI_GP0_ARLEN,
  input [3:0] S_AXI_GP0_ARQOS,
  input [3:0] S_AXI_GP0_AWCACHE,
  input [3:0] S_AXI_GP0_AWLEN,
  input [3:0] S_AXI_GP0_AWQOS,
  input [3:0] S_AXI_GP0_WSTRB,
  input [(C_S_AXI_GP0_ID_WIDTH - 1) : 0] S_AXI_GP0_ARID,
  input [(C_S_AXI_GP0_ID_WIDTH - 1) : 0] S_AXI_GP0_AWID,
  input [(C_S_AXI_GP0_ID_WIDTH - 1) : 0] S_AXI_GP0_WID,  

  // S_AXI_GP1
  
  // -- Output  
  output S_AXI_GP1_ARESETN,
  output S_AXI_GP1_ARREADY,
  output S_AXI_GP1_AWREADY,
  output S_AXI_GP1_BVALID,
  output S_AXI_GP1_RLAST,
  output S_AXI_GP1_RVALID,
  output S_AXI_GP1_WREADY,  
  output [1:0] S_AXI_GP1_BRESP,
  output [1:0] S_AXI_GP1_RRESP,
  output [31:0] S_AXI_GP1_RDATA,
  output [(C_S_AXI_GP1_ID_WIDTH - 1) : 0] S_AXI_GP1_BID,
  output [(C_S_AXI_GP1_ID_WIDTH - 1) : 0] S_AXI_GP1_RID,
  
  // -- Input
  input S_AXI_GP1_ACLK,
  input S_AXI_GP1_ARVALID,
  input S_AXI_GP1_AWVALID,
  input S_AXI_GP1_BREADY,
  input S_AXI_GP1_RREADY,
  input S_AXI_GP1_WLAST,
  input S_AXI_GP1_WVALID,
  input [1:0] S_AXI_GP1_ARBURST,
  input [1:0] S_AXI_GP1_ARLOCK,
  input [2:0] S_AXI_GP1_ARSIZE,
  input [1:0] S_AXI_GP1_AWBURST,
  input [1:0] S_AXI_GP1_AWLOCK,
  input [2:0] S_AXI_GP1_AWSIZE,
  input [2:0] S_AXI_GP1_ARPROT,
  input [2:0] S_AXI_GP1_AWPROT,
  input [31:0] S_AXI_GP1_ARADDR,
  input [31:0] S_AXI_GP1_AWADDR,
  input [31:0] S_AXI_GP1_WDATA,
  input [3:0] S_AXI_GP1_ARCACHE,
  input [3:0] S_AXI_GP1_ARLEN,
  input [3:0] S_AXI_GP1_ARQOS,
  input [3:0] S_AXI_GP1_AWCACHE,
  input [3:0] S_AXI_GP1_AWLEN,
  input [3:0] S_AXI_GP1_AWQOS,
  input [3:0] S_AXI_GP1_WSTRB,
  input [(C_S_AXI_GP1_ID_WIDTH - 1) : 0] S_AXI_GP1_ARID,
  input [(C_S_AXI_GP1_ID_WIDTH - 1) : 0] S_AXI_GP1_AWID,
  input [(C_S_AXI_GP1_ID_WIDTH - 1) : 0] S_AXI_GP1_WID,  

  //S_AXI_ACP
  
  // -- Output  
  
  output S_AXI_ACP_ARESETN,
  output S_AXI_ACP_ARREADY,
  output S_AXI_ACP_AWREADY,
  output S_AXI_ACP_BVALID,
  output S_AXI_ACP_RLAST,
  output S_AXI_ACP_RVALID,
  output S_AXI_ACP_WREADY,  
  output [1:0] S_AXI_ACP_BRESP,
  output [1:0] S_AXI_ACP_RRESP,
  output [(C_S_AXI_ACP_ID_WIDTH - 1) : 0] S_AXI_ACP_BID,
  output [(C_S_AXI_ACP_ID_WIDTH - 1) : 0] S_AXI_ACP_RID,
  output [63:0] S_AXI_ACP_RDATA,
  
  // -- Input
  
  input S_AXI_ACP_ACLK,
  input S_AXI_ACP_ARVALID,
  input S_AXI_ACP_AWVALID,
  input S_AXI_ACP_BREADY,
  input S_AXI_ACP_RREADY,
  input S_AXI_ACP_WLAST,
  input S_AXI_ACP_WVALID,
  input [(C_S_AXI_ACP_ID_WIDTH - 1) : 0] S_AXI_ACP_ARID,
  input [2:0] S_AXI_ACP_ARPROT,
  input [(C_S_AXI_ACP_ID_WIDTH - 1) : 0] S_AXI_ACP_AWID,
  input [2:0] S_AXI_ACP_AWPROT,
  input [(C_S_AXI_ACP_ID_WIDTH - 1) : 0] S_AXI_ACP_WID,
  input [31:0] S_AXI_ACP_ARADDR,
  input [31:0] S_AXI_ACP_AWADDR,
  input [3:0] S_AXI_ACP_ARCACHE,
  input [3:0] S_AXI_ACP_ARLEN,
  input [3:0] S_AXI_ACP_ARQOS,
  input [3:0] S_AXI_ACP_AWCACHE,
  input [3:0] S_AXI_ACP_AWLEN,
  input [3:0] S_AXI_ACP_AWQOS,  
  input [1:0] S_AXI_ACP_ARBURST,
  input [1:0] S_AXI_ACP_ARLOCK,
  input [2:0] S_AXI_ACP_ARSIZE,
  input [1:0] S_AXI_ACP_AWBURST,
  input [1:0] S_AXI_ACP_AWLOCK,
  input [2:0] S_AXI_ACP_AWSIZE,
  input [4:0] S_AXI_ACP_ARUSER,
  input [4:0] S_AXI_ACP_AWUSER,
  input [63:0] S_AXI_ACP_WDATA,
  input [7:0] S_AXI_ACP_WSTRB,  
  
  // S_AXI_HP_0
  
  // -- Output
  output S_AXI_HP0_ARESETN,
  output S_AXI_HP0_ARREADY,
  output S_AXI_HP0_AWREADY,
  output S_AXI_HP0_BVALID,
  output S_AXI_HP0_RLAST,
  output S_AXI_HP0_RVALID,
  output S_AXI_HP0_WREADY,  
  output [1:0] S_AXI_HP0_BRESP,
  output [1:0] S_AXI_HP0_RRESP,
  output [(C_S_AXI_HP0_ID_WIDTH - 1) : 0] S_AXI_HP0_BID,
  output [(C_S_AXI_HP0_ID_WIDTH - 1) : 0] S_AXI_HP0_RID,
  output [(C_S_AXI_HP0_DATA_WIDTH - 1) :0] S_AXI_HP0_RDATA,
  output [7:0] S_AXI_HP0_RCOUNT,
  output [7:0] S_AXI_HP0_WCOUNT,
  output [2:0] S_AXI_HP0_RACOUNT,
  output [5:0] S_AXI_HP0_WACOUNT,
  
  // -- Input  
  input S_AXI_HP0_ACLK,
  input S_AXI_HP0_ARVALID,
  input S_AXI_HP0_AWVALID,
  input S_AXI_HP0_BREADY,
  input S_AXI_HP0_RDISSUECAP1_EN,
  input S_AXI_HP0_RREADY,
  input S_AXI_HP0_WLAST,
  input S_AXI_HP0_WRISSUECAP1_EN,
  input S_AXI_HP0_WVALID,
  input [1:0] S_AXI_HP0_ARBURST,
  input [1:0] S_AXI_HP0_ARLOCK,
  input [2:0] S_AXI_HP0_ARSIZE,
  input [1:0] S_AXI_HP0_AWBURST,
  input [1:0] S_AXI_HP0_AWLOCK,
  input [2:0] S_AXI_HP0_AWSIZE,
  input [2:0] S_AXI_HP0_ARPROT,
  input [2:0] S_AXI_HP0_AWPROT,
  input [31:0] S_AXI_HP0_ARADDR,
  input [31:0] S_AXI_HP0_AWADDR,
  input [3:0] S_AXI_HP0_ARCACHE,
  input [3:0] S_AXI_HP0_ARLEN,
  input [3:0] S_AXI_HP0_ARQOS,
  input [3:0] S_AXI_HP0_AWCACHE,
  input [3:0] S_AXI_HP0_AWLEN,
  input [3:0] S_AXI_HP0_AWQOS,
  input [(C_S_AXI_HP0_ID_WIDTH - 1) : 0] S_AXI_HP0_ARID,
  input [(C_S_AXI_HP0_ID_WIDTH - 1) : 0] S_AXI_HP0_AWID,
  input [(C_S_AXI_HP0_ID_WIDTH - 1) : 0] S_AXI_HP0_WID,
  input [(C_S_AXI_HP0_DATA_WIDTH - 1) :0] S_AXI_HP0_WDATA,
  input [((C_S_AXI_HP0_DATA_WIDTH/8)-1):0] S_AXI_HP0_WSTRB,  

  // S_AXI_HP1
  // -- Output
  output S_AXI_HP1_ARESETN,
  output S_AXI_HP1_ARREADY,
  output S_AXI_HP1_AWREADY,
  output S_AXI_HP1_BVALID,
  output S_AXI_HP1_RLAST,
  output S_AXI_HP1_RVALID,
  output S_AXI_HP1_WREADY,  
  output [1:0] S_AXI_HP1_BRESP,
  output [1:0] S_AXI_HP1_RRESP,
  output [(C_S_AXI_HP1_ID_WIDTH - 1) : 0] S_AXI_HP1_BID,
  output [(C_S_AXI_HP1_ID_WIDTH - 1) : 0] S_AXI_HP1_RID,
  output [(C_S_AXI_HP1_DATA_WIDTH - 1) :0] S_AXI_HP1_RDATA,
  output [7:0] S_AXI_HP1_RCOUNT,
  output [7:0] S_AXI_HP1_WCOUNT,
  output [2:0] S_AXI_HP1_RACOUNT,
  output [5:0] S_AXI_HP1_WACOUNT,
  
  
  // -- Input  
  input S_AXI_HP1_ACLK,
  input S_AXI_HP1_ARVALID,
  input S_AXI_HP1_AWVALID,
  input S_AXI_HP1_BREADY,
  input S_AXI_HP1_RDISSUECAP1_EN,
  input S_AXI_HP1_RREADY,
  input S_AXI_HP1_WLAST,
  input S_AXI_HP1_WRISSUECAP1_EN,
  input S_AXI_HP1_WVALID,
  input [1:0] S_AXI_HP1_ARBURST,
  input [1:0] S_AXI_HP1_ARLOCK,
  input [2:0] S_AXI_HP1_ARSIZE,
  input [1:0] S_AXI_HP1_AWBURST,
  input [1:0] S_AXI_HP1_AWLOCK,
  input [2:0] S_AXI_HP1_AWSIZE,
  input [2:0] S_AXI_HP1_ARPROT,
  input [2:0] S_AXI_HP1_AWPROT,
  input [31:0] S_AXI_HP1_ARADDR,
  input [31:0] S_AXI_HP1_AWADDR,
  input [3:0] S_AXI_HP1_ARCACHE,
  input [3:0] S_AXI_HP1_ARLEN,
  input [3:0] S_AXI_HP1_ARQOS,
  input [3:0] S_AXI_HP1_AWCACHE,
  input [3:0] S_AXI_HP1_AWLEN,
  input [3:0] S_AXI_HP1_AWQOS,
  input [(C_S_AXI_HP1_ID_WIDTH - 1) : 0] S_AXI_HP1_ARID,
  input [(C_S_AXI_HP1_ID_WIDTH - 1) : 0] S_AXI_HP1_AWID,
  input [(C_S_AXI_HP1_ID_WIDTH - 1) : 0] S_AXI_HP1_WID,
  input [(C_S_AXI_HP1_DATA_WIDTH - 1) :0] S_AXI_HP1_WDATA,
  input [((C_S_AXI_HP1_DATA_WIDTH/8)-1):0] S_AXI_HP1_WSTRB,  

  // S_AXI_HP2
  // -- Output
  output S_AXI_HP2_ARESETN,
  output S_AXI_HP2_ARREADY,
  output S_AXI_HP2_AWREADY,
  output S_AXI_HP2_BVALID,
  output S_AXI_HP2_RLAST,
  output S_AXI_HP2_RVALID,
  output S_AXI_HP2_WREADY,  
  output [1:0] S_AXI_HP2_BRESP,
  output [1:0] S_AXI_HP2_RRESP,
  output [(C_S_AXI_HP2_ID_WIDTH - 1) : 0] S_AXI_HP2_BID,
  output [(C_S_AXI_HP2_ID_WIDTH - 1) : 0] S_AXI_HP2_RID,
  output [(C_S_AXI_HP2_DATA_WIDTH - 1) :0] S_AXI_HP2_RDATA,
  output [7:0] S_AXI_HP2_RCOUNT,
  output [7:0] S_AXI_HP2_WCOUNT,
  output [2:0] S_AXI_HP2_RACOUNT,
  output [5:0] S_AXI_HP2_WACOUNT,
  
  
  // -- Input  
  input S_AXI_HP2_ACLK,
  input S_AXI_HP2_ARVALID,
  input S_AXI_HP2_AWVALID,
  input S_AXI_HP2_BREADY,
  input S_AXI_HP2_RDISSUECAP1_EN,
  input S_AXI_HP2_RREADY,
  input S_AXI_HP2_WLAST,
  input S_AXI_HP2_WRISSUECAP1_EN,
  input S_AXI_HP2_WVALID,
  input [1:0] S_AXI_HP2_ARBURST,
  input [1:0] S_AXI_HP2_ARLOCK,
  input [2:0] S_AXI_HP2_ARSIZE,
  input [1:0] S_AXI_HP2_AWBURST,
  input [1:0] S_AXI_HP2_AWLOCK,
  input [2:0] S_AXI_HP2_AWSIZE,
  input [2:0] S_AXI_HP2_ARPROT,
  input [2:0] S_AXI_HP2_AWPROT,
  input [31:0] S_AXI_HP2_ARADDR,
  input [31:0] S_AXI_HP2_AWADDR,
  input [3:0] S_AXI_HP2_ARCACHE,
  input [3:0] S_AXI_HP2_ARLEN,
  input [3:0] S_AXI_HP2_ARQOS,
  input [3:0] S_AXI_HP2_AWCACHE,
  input [3:0] S_AXI_HP2_AWLEN,
  input [3:0] S_AXI_HP2_AWQOS,
  input [(C_S_AXI_HP2_ID_WIDTH - 1) : 0] S_AXI_HP2_ARID,
  input [(C_S_AXI_HP2_ID_WIDTH - 1) : 0] S_AXI_HP2_AWID,
  input [(C_S_AXI_HP2_ID_WIDTH - 1) : 0] S_AXI_HP2_WID,
  input [(C_S_AXI_HP2_DATA_WIDTH - 1) :0] S_AXI_HP2_WDATA,
  input [((C_S_AXI_HP2_DATA_WIDTH/8)-1):0] S_AXI_HP2_WSTRB,  

  // S_AXI_HP_3
  
  // -- Output
  output S_AXI_HP3_ARESETN,
  output S_AXI_HP3_ARREADY,
  output S_AXI_HP3_AWREADY,
  output S_AXI_HP3_BVALID,
  output S_AXI_HP3_RLAST,
  output S_AXI_HP3_RVALID,
  output S_AXI_HP3_WREADY,  
  output [1:0] S_AXI_HP3_BRESP,
  output [1:0] S_AXI_HP3_RRESP,
  output [(C_S_AXI_HP3_ID_WIDTH - 1) : 0] S_AXI_HP3_BID,
  output [(C_S_AXI_HP3_ID_WIDTH - 1) : 0] S_AXI_HP3_RID,
  output [(C_S_AXI_HP3_DATA_WIDTH - 1) :0] S_AXI_HP3_RDATA,
  output [7:0] S_AXI_HP3_RCOUNT,
  output [7:0] S_AXI_HP3_WCOUNT,
  output [2:0] S_AXI_HP3_RACOUNT,
  output [5:0] S_AXI_HP3_WACOUNT,
  
  
  // -- Input  
  input S_AXI_HP3_ACLK,
  input S_AXI_HP3_ARVALID,
  input S_AXI_HP3_AWVALID,
  input S_AXI_HP3_BREADY,
  input S_AXI_HP3_RDISSUECAP1_EN,
  input S_AXI_HP3_RREADY,
  input S_AXI_HP3_WLAST,
  input S_AXI_HP3_WRISSUECAP1_EN,
  input S_AXI_HP3_WVALID,
  input [1:0] S_AXI_HP3_ARBURST,
  input [1:0] S_AXI_HP3_ARLOCK,
  input [2:0] S_AXI_HP3_ARSIZE,
  input [1:0] S_AXI_HP3_AWBURST,
  input [1:0] S_AXI_HP3_AWLOCK,
  input [2:0] S_AXI_HP3_AWSIZE,
  input [2:0] S_AXI_HP3_ARPROT,
  input [2:0] S_AXI_HP3_AWPROT,
  input [31:0] S_AXI_HP3_ARADDR,
  input [31:0] S_AXI_HP3_AWADDR,
  input [3:0] S_AXI_HP3_ARCACHE,
  input [3:0] S_AXI_HP3_ARLEN,
  input [3:0] S_AXI_HP3_ARQOS,
  input [3:0] S_AXI_HP3_AWCACHE,
  input [3:0] S_AXI_HP3_AWLEN,
  input [3:0] S_AXI_HP3_AWQOS,
  input [(C_S_AXI_HP3_ID_WIDTH - 1) : 0] S_AXI_HP3_ARID,
  input [(C_S_AXI_HP3_ID_WIDTH - 1) : 0] S_AXI_HP3_AWID,
  input [(C_S_AXI_HP3_ID_WIDTH - 1) : 0] S_AXI_HP3_WID,
  input [(C_S_AXI_HP3_DATA_WIDTH - 1) :0] S_AXI_HP3_WDATA,
  input [((C_S_AXI_HP3_DATA_WIDTH/8)-1):0] S_AXI_HP3_WSTRB,  
  
  //FIO ========================================

  //IRQ
  //output [28:0] IRQ_P2F,
  output IRQ_P2F_DMAC_ABORT ,
  output IRQ_P2F_DMAC0,
  output IRQ_P2F_DMAC1,
  output IRQ_P2F_DMAC2,
  output IRQ_P2F_DMAC3,
  output IRQ_P2F_DMAC4,
  output IRQ_P2F_DMAC5,
  output IRQ_P2F_DMAC6,
  output IRQ_P2F_DMAC7,
  output IRQ_P2F_SMC,
  output IRQ_P2F_QSPI,
  output IRQ_P2F_CTI,
  output IRQ_P2F_GPIO,
  output IRQ_P2F_USB0,
  output IRQ_P2F_ENET0,
  output IRQ_P2F_ENET_WAKE0,
  output IRQ_P2F_SDIO0,
  output IRQ_P2F_I2C0,
  output IRQ_P2F_SPI0,
  output IRQ_P2F_UART0,
  output IRQ_P2F_CAN0,
  output IRQ_P2F_USB1,
  output IRQ_P2F_ENET1,
  output IRQ_P2F_ENET_WAKE1,
  output IRQ_P2F_SDIO1,
  output IRQ_P2F_I2C1,
  output IRQ_P2F_SPI1,
  output IRQ_P2F_UART1,
  output IRQ_P2F_CAN1,
  input  [(C_NUM_F2P_INTR_INPUTS-1):0] IRQ_F2P,
  input         Core0_nFIQ,
  input         Core0_nIRQ,
  input         Core1_nFIQ,
  input         Core1_nIRQ,

  //DMA

  output [1:0] DMA0_DATYPE,  
  output DMA0_DAVALID,
  output DMA0_DRREADY,
  output DMA0_RSTN,  
  output [1:0] DMA1_DATYPE,  
  output DMA1_DAVALID,
  output DMA1_DRREADY,
  output DMA1_RSTN,  
  output [1:0] DMA2_DATYPE,  
  output DMA2_DAVALID,
  output DMA2_DRREADY,
  output DMA2_RSTN,  
  output [1:0] DMA3_DATYPE,    
  output DMA3_DAVALID,
  output DMA3_DRREADY,
  output DMA3_RSTN,  
  input DMA0_ACLK,
  input DMA0_DAREADY,
  input DMA0_DRLAST,
  input DMA0_DRVALID,
  input DMA1_ACLK,
  input DMA1_DAREADY,
  input DMA1_DRLAST,
  input DMA1_DRVALID,
  input DMA2_ACLK,
  input DMA2_DAREADY,
  input DMA2_DRLAST,
  input DMA2_DRVALID,
  input DMA3_ACLK,
  input DMA3_DAREADY,
  input DMA3_DRLAST,
  input DMA3_DRVALID,  
  input [1:0] DMA0_DRTYPE,
  input [1:0] DMA1_DRTYPE,
  input [1:0] DMA2_DRTYPE,
  input [1:0] DMA3_DRTYPE,
  
  //FCLK
  output    FCLK_CLK3,
  output    FCLK_CLK2,
  output    FCLK_CLK1,
  output    FCLK_CLK0,
 
  input     FCLK_CLKTRIG3_N,
  input     FCLK_CLKTRIG2_N,
  input     FCLK_CLKTRIG1_N,
  input     FCLK_CLKTRIG0_N,
 
  output    FCLK_RESET3_N,
  output    FCLK_RESET2_N,
  output    FCLK_RESET1_N,
  output    FCLK_RESET0_N,

  //FTMD
  input    [31:0] FTMD_TRACEIN_DATA,
  input           FTMD_TRACEIN_VALID,
  input           FTMD_TRACEIN_CLK,
  input    [3:0]  FTMD_TRACEIN_ATID,

  //FTMT
  input     FTMT_F2P_TRIG_0,
  output    FTMT_F2P_TRIGACK_0,
  input     FTMT_F2P_TRIG_1,
  output    FTMT_F2P_TRIGACK_1,
  input     FTMT_F2P_TRIG_2,
  output    FTMT_F2P_TRIGACK_2,
  input     FTMT_F2P_TRIG_3,
  output    FTMT_F2P_TRIGACK_3,
  input     [31:0] FTMT_F2P_DEBUG,  
  input     FTMT_P2F_TRIGACK_0,
  output    FTMT_P2F_TRIG_0,
  input     FTMT_P2F_TRIGACK_1,
  output    FTMT_P2F_TRIG_1,
  input     FTMT_P2F_TRIGACK_2,
  output    FTMT_P2F_TRIG_2,
  input     FTMT_P2F_TRIGACK_3,
  output    FTMT_P2F_TRIG_3,
  output    [31:0] FTMT_P2F_DEBUG,

  //FIDLE
  input           FPGA_IDLE_N,
  
  //EVENT

  output EVENT_EVENTO,
  output [1:0] EVENT_STANDBYWFE,
  output [1:0] EVENT_STANDBYWFI,  
  input EVENT_EVENTI,   
  

  //DARB
  input     [3:0] DDR_ARB,
  inout     [C_MIO_PRIMITIVE - 1:0] MIO,  
  
  //DDR
  inout         DDR_CAS_n,       // CASB
  inout         DDR_CKE,         // CKE
  inout         DDR_Clk_n,       // CKN
  inout         DDR_Clk,         // CKP
  inout         DDR_CS_n,        // CSB 
  inout         DDR_DRSTB,       // DDR_DRSTB  
  inout         DDR_ODT,         // ODT
  inout         DDR_RAS_n,       // RASB
  inout         DDR_WEB,
  inout  [2:0]  DDR_BankAddr,    // BA  
  inout  [14:0] DDR_Addr,        // A
  
  inout          DDR_VRN,
  inout          DDR_VRP,
  inout   [C_DM_WIDTH - 1:0]  DDR_DM,          // DM  
  inout   [C_DQ_WIDTH - 1:0] DDR_DQ,          // DQ
  inout   [C_DQS_WIDTH -1:0]  DDR_DQS_n,       // DQSN
  inout   [C_DQS_WIDTH - 1:0]  DDR_DQS,         // DQSP
  
  inout          PS_SRSTB,        // SRSTB    
  inout          PS_CLK,          // CLK
  inout          PS_PORB         // PORB 


);

wire [11:0]  M_AXI_GP0_AWID_FULL;
wire [11:0]  M_AXI_GP0_WID_FULL;
wire [11:0]  M_AXI_GP0_ARID_FULL;

wire [11:0]  M_AXI_GP0_BID_FULL;
wire [11:0]  M_AXI_GP0_RID_FULL;

wire [11:0]  M_AXI_GP1_AWID_FULL;
wire [11:0]  M_AXI_GP1_WID_FULL;
wire [11:0]  M_AXI_GP1_ARID_FULL;

wire [11:0]  M_AXI_GP1_BID_FULL;
wire [11:0]  M_AXI_GP1_RID_FULL;

wire [3:0] M_AXI_GP0_ARCACHE_t;
wire [3:0] M_AXI_GP1_ARCACHE_t;
wire [3:0] M_AXI_GP0_AWCACHE_t;
wire [3:0] M_AXI_GP1_AWCACHE_t;


// Wires for connecting to the PS7
wire    ENET0_GMII_TX_EN_i;
wire    ENET0_GMII_TX_ER_i;
reg          ENET0_GMII_COL_i;
reg          ENET0_GMII_CRS_i;
reg          ENET0_GMII_RX_DV_i;
reg          ENET0_GMII_RX_ER_i;
reg [7:0]    ENET0_GMII_RXD_i;
wire [7:0]   ENET0_GMII_TXD_i;

wire         ENET1_GMII_TX_EN_i;
wire         ENET1_GMII_TX_ER_i;
reg          ENET1_GMII_COL_i;
reg          ENET1_GMII_CRS_i;
reg          ENET1_GMII_RX_DV_i;
reg          ENET1_GMII_RX_ER_i;
reg [7:0]   ENET1_GMII_RXD_i;
wire [7:0]   ENET1_GMII_TXD_i;

reg    [31:0] FTMD_TRACEIN_DATA_notracebuf;
reg           FTMD_TRACEIN_VALID_notracebuf;
reg    [3:0]  FTMD_TRACEIN_ATID_notracebuf;

wire    [31:0] FTMD_TRACEIN_DATA_i;
wire           FTMD_TRACEIN_VALID_i;
wire    [3:0]  FTMD_TRACEIN_ATID_i;

wire    [31:0] FTMD_TRACEIN_DATA_tracebuf;
wire           FTMD_TRACEIN_VALID_tracebuf;
wire    [3:0]  FTMD_TRACEIN_ATID_tracebuf;

wire [5:0]    S_AXI_GP0_BID_out;
wire [5:0]    S_AXI_GP0_RID_out;
wire [5:0]    S_AXI_GP0_ARID_in;
wire [5:0]    S_AXI_GP0_AWID_in;
wire [5:0]    S_AXI_GP0_WID_in;

wire [5:0]    S_AXI_GP1_BID_out;
wire [5:0]    S_AXI_GP1_RID_out;
wire [5:0]    S_AXI_GP1_ARID_in;
wire [5:0]    S_AXI_GP1_AWID_in;
wire [5:0]    S_AXI_GP1_WID_in;

wire [5:0]    S_AXI_HP0_BID_out;
wire [5:0]    S_AXI_HP0_RID_out;
wire [5:0]    S_AXI_HP0_ARID_in;
wire [5:0]    S_AXI_HP0_AWID_in;
wire [5:0]    S_AXI_HP0_WID_in;

wire [5:0]    S_AXI_HP1_BID_out;
wire [5:0]    S_AXI_HP1_RID_out;
wire [5:0]    S_AXI_HP1_ARID_in;
wire [5:0]    S_AXI_HP1_AWID_in;
wire [5:0]    S_AXI_HP1_WID_in;

wire [5:0]    S_AXI_HP2_BID_out;
wire [5:0]    S_AXI_HP2_RID_out;
wire [5:0]    S_AXI_HP2_ARID_in;
wire [5:0]    S_AXI_HP2_AWID_in;
wire [5:0]    S_AXI_HP2_WID_in;

wire [5:0]    S_AXI_HP3_BID_out;
wire [5:0]    S_AXI_HP3_RID_out;
wire [5:0]    S_AXI_HP3_ARID_in;
wire [5:0]    S_AXI_HP3_AWID_in;
wire [5:0]    S_AXI_HP3_WID_in;

wire [2:0]    S_AXI_ACP_BID_out;
wire [2:0]    S_AXI_ACP_RID_out;
wire [2:0]    S_AXI_ACP_ARID_in;
wire [2:0]    S_AXI_ACP_AWID_in;
wire [2:0]    S_AXI_ACP_WID_in;  

wire [63:0]   S_AXI_HP0_WDATA_in;
wire [7:0]    S_AXI_HP0_WSTRB_in;
wire [63:0]   S_AXI_HP0_RDATA_out;

wire [63:0]   S_AXI_HP1_WDATA_in;
wire [7:0]    S_AXI_HP1_WSTRB_in;
wire [63:0]   S_AXI_HP1_RDATA_out;

wire [63:0]   S_AXI_HP2_WDATA_in;
wire [7:0]    S_AXI_HP2_WSTRB_in;
wire [63:0]   S_AXI_HP2_RDATA_out;

wire [63:0]   S_AXI_HP3_WDATA_in;
wire [7:0]    S_AXI_HP3_WSTRB_in;
wire [63:0]   S_AXI_HP3_RDATA_out;
 
wire [1:0]    M_AXI_GP0_ARSIZE_i;
wire [1:0]    M_AXI_GP0_AWSIZE_i;

wire [1:0]    M_AXI_GP1_ARSIZE_i;
wire [1:0]    M_AXI_GP1_AWSIZE_i;

wire [(C_S_AXI_ACP_ID_WIDTH - 1) : 0]    SAXIACPBID_W;
wire [(C_S_AXI_ACP_ID_WIDTH - 1) : 0]    SAXIACPRID_W;
wire [(C_S_AXI_ACP_ID_WIDTH - 1) : 0]    SAXIACPARID_W;
wire [(C_S_AXI_ACP_ID_WIDTH - 1) : 0]    SAXIACPAWID_W;
wire [(C_S_AXI_ACP_ID_WIDTH - 1) : 0]    SAXIACPWID_W;  


wire SAXIACPARREADY_W;
wire SAXIACPAWREADY_W;
wire SAXIACPBVALID_W;
wire SAXIACPRLAST_W;
wire SAXIACPRVALID_W;
wire SAXIACPWREADY_W;  
wire [1:0] SAXIACPBRESP_W;
wire [1:0] SAXIACPRRESP_W;
wire [(C_S_AXI_ACP_ID_WIDTH - 1) : 0] S_AXI_ATC_BID;
wire [(C_S_AXI_ACP_ID_WIDTH - 1) : 0] S_AXI_ATC_RID;
wire [63:0] SAXIACPRDATA_W;
  
wire S_AXI_ATC_ARVALID;
wire S_AXI_ATC_AWVALID;
wire S_AXI_ATC_BREADY;
wire S_AXI_ATC_RREADY;
wire S_AXI_ATC_WLAST;
wire S_AXI_ATC_WVALID;
wire [(C_S_AXI_ACP_ID_WIDTH - 1) : 0] S_AXI_ATC_ARID;
wire [2:0] S_AXI_ATC_ARPROT;
wire [(C_S_AXI_ACP_ID_WIDTH - 1) : 0] S_AXI_ATC_AWID;
wire [2:0] S_AXI_ATC_AWPROT;
wire [(C_S_AXI_ACP_ID_WIDTH - 1) : 0] S_AXI_ATC_WID;
wire [31:0] S_AXI_ATC_ARADDR;
wire [31:0] S_AXI_ATC_AWADDR;
wire [3:0] S_AXI_ATC_ARCACHE;
wire [3:0] S_AXI_ATC_ARLEN;
wire [3:0] S_AXI_ATC_ARQOS;
wire [3:0] S_AXI_ATC_AWCACHE;
wire [3:0] S_AXI_ATC_AWLEN;
wire [3:0] S_AXI_ATC_AWQOS;  
wire [1:0] S_AXI_ATC_ARBURST;
wire [1:0] S_AXI_ATC_ARLOCK;
wire [2:0] S_AXI_ATC_ARSIZE;
wire [1:0] S_AXI_ATC_AWBURST;
wire [1:0] S_AXI_ATC_AWLOCK;
wire [2:0] S_AXI_ATC_AWSIZE;
wire [4:0] S_AXI_ATC_ARUSER;
wire [4:0] S_AXI_ATC_AWUSER;
wire [63:0] S_AXI_ATC_WDATA;
wire [7:0] S_AXI_ATC_WSTRB;  


wire SAXIACPARVALID_W;
wire SAXIACPAWVALID_W;
wire SAXIACPBREADY_W;
wire SAXIACPRREADY_W;
wire SAXIACPWLAST_W;
wire SAXIACPWVALID_W;
wire [2:0] SAXIACPARPROT_W;
wire [2:0] SAXIACPAWPROT_W;
wire [31:0] SAXIACPARADDR_W;
wire [31:0] SAXIACPAWADDR_W;
wire [3:0] SAXIACPARCACHE_W;
wire [3:0] SAXIACPARLEN_W;
wire [3:0] SAXIACPARQOS_W;
wire [3:0] SAXIACPAWCACHE_W;
wire [3:0] SAXIACPAWLEN_W;
wire [3:0] SAXIACPAWQOS_W;  
wire [1:0] SAXIACPARBURST_W;
wire [1:0] SAXIACPARLOCK_W;
wire [2:0] SAXIACPARSIZE_W;
wire [1:0] SAXIACPAWBURST_W;
wire [1:0] SAXIACPAWLOCK_W;
wire [2:0] SAXIACPAWSIZE_W;
wire [4:0] SAXIACPARUSER_W;
wire [4:0] SAXIACPAWUSER_W;
wire [63:0] SAXIACPWDATA_W;
wire [7:0] SAXIACPWSTRB_W;

// AxUSER signal update
wire [4:0] param_aruser;
wire [4:0] param_awuser;

// Added to address CR 651751
wire [3:0]   fclk_clktrig_gnd = 4'h0;


wire [19:0]   irq_f2p_i;
wire [15:0]   irq_f2p_null = 16'h0000;

// EMIO I2C0
wire          I2C0_SDA_T_n;
wire          I2C0_SCL_T_n;
// EMIO I2C1
wire          I2C1_SDA_T_n;
wire          I2C1_SCL_T_n;
// EMIO SPI0
wire          SPI0_SCLK_T_n;
wire          SPI0_MOSI_T_n;
wire          SPI0_MISO_T_n;
wire          SPI0_SS_T_n;
// EMIO SPI1
wire          SPI1_SCLK_T_n;
wire          SPI1_MOSI_T_n;
wire          SPI1_MISO_T_n;
wire          SPI1_SS_T_n;

// EMIO GEM0
wire          ENET0_MDIO_T_n;

// EMIO GEM1
wire          ENET1_MDIO_T_n;

// EMIO GPIO
wire  [(C_EMIO_GPIO_WIDTH-1):0]        GPIO_T_n;

wire [63:0]   gpio_out_t_n;
wire [63:0]   gpio_out;
wire [63:0]   gpio_in63_0;

//For Clock buffering
wire    [3:0] FCLK_CLK_unbuffered;
wire    [3:0] FCLK_CLK_buffered;
wire   		  FCLK_CLK0_temp;

// EMIO PJTAG
wire          PJTAG_TDO_O;
wire          PJTAG_TDO_T;
wire          PJTAG_TDO_T_n;

// EMIO SDIO0
wire          SDIO0_CMD_T_n;
wire [3:0]    SDIO0_DATA_T_n;

// EMIO SDIO1
wire          SDIO1_CMD_T_n;
wire [3:0]    SDIO1_DATA_T_n;

// buffered IO
wire  [C_MIO_PRIMITIVE - 1:0]  buffered_MIO;
wire  buffered_DDR_WEB;
wire  buffered_DDR_CAS_n;
wire  buffered_DDR_CKE;
wire  buffered_DDR_Clk_n;
wire  buffered_DDR_Clk;
wire  buffered_DDR_CS_n; 
wire  buffered_DDR_DRSTB;  
wire  buffered_DDR_ODT;
wire  buffered_DDR_RAS_n;
wire  [2:0]  buffered_DDR_BankAddr; 
wire  [14:0]  buffered_DDR_Addr;
  
wire  buffered_DDR_VRN;
wire  buffered_DDR_VRP;
wire  [C_DM_WIDTH - 1:0]  buffered_DDR_DM;  
wire  [C_DQ_WIDTH - 1:0]  buffered_DDR_DQ;
wire  [C_DQS_WIDTH -1:0]  buffered_DDR_DQS_n;
wire  [C_DQS_WIDTH - 1:0]  buffered_DDR_DQS;
  
wire  buffered_PS_SRSTB; 
wire  buffered_PS_CLK;
wire  buffered_PS_PORB;

wire S_AXI_HP0_ACLK_temp;
wire S_AXI_HP1_ACLK_temp;
wire S_AXI_HP2_ACLK_temp;
wire S_AXI_HP3_ACLK_temp;
wire M_AXI_GP0_ACLK_temp;
wire M_AXI_GP1_ACLK_temp;
wire S_AXI_GP0_ACLK_temp;
wire S_AXI_GP1_ACLK_temp;
wire S_AXI_ACP_ACLK_temp;

wire [31:0] TRACE_DATA_i;
wire TRACE_CTL_i;
(* keep = "true" *) reg   TRACE_CTL_PIPE [(C_TRACE_PIPELINE_WIDTH - 1):0];
(* keep = "true" *) reg   [(C_TRACE_INTERNAL_WIDTH)-1:0] TRACE_DATA_PIPE [(C_TRACE_PIPELINE_WIDTH - 1):0];

// fixed CR #665394
integer j;
generate
  if (C_EN_EMIO_TRACE == 1) begin 
    always @(posedge TRACE_CLK) 
    begin
	  TRACE_CTL_PIPE[C_TRACE_PIPELINE_WIDTH - 1] <= TRACE_CTL_i;
	  TRACE_DATA_PIPE[C_TRACE_PIPELINE_WIDTH - 1] <= TRACE_DATA_i[(C_TRACE_INTERNAL_WIDTH-1):0];
	  for (j=(C_TRACE_PIPELINE_WIDTH-1); j>0; j=j-1) begin
		TRACE_CTL_PIPE[j-1] <= TRACE_CTL_PIPE[j];
		TRACE_DATA_PIPE[j-1] <= TRACE_DATA_PIPE[j];
      end
	  TRACE_CLK_OUT  <= ~TRACE_CLK_OUT;
	end
  end	
else
begin
always @*
begin
TRACE_CTL_PIPE[C_TRACE_PIPELINE_WIDTH - 1] <= 1'b0;
  TRACE_DATA_PIPE[C_TRACE_PIPELINE_WIDTH - 1] <= 1'b0; 
  for (j=(C_TRACE_PIPELINE_WIDTH-1); j>0; j=j-1) begin
  TRACE_CTL_PIPE[j-1] <= 1'b0;
		TRACE_DATA_PIPE[j-1] <= 1'b0;
		end
  TRACE_CLK_OUT  <= 1'b0; 
  end
end
endgenerate

assign TRACE_CTL = TRACE_CTL_PIPE[0];

assign TRACE_DATA = TRACE_DATA_PIPE[0];

//irq_p2f

// Updated IRQ_F2P logic to address CR 641523
generate 
  if(C_NUM_F2P_INTR_INPUTS == 0) begin : irq_f2p_select_null
    assign irq_f2p_i[19:0] = {Core1_nFIQ,Core0_nFIQ,Core1_nIRQ,Core0_nIRQ,irq_f2p_null[15:0]};
  end else if(C_NUM_F2P_INTR_INPUTS == 16) begin : irq_f2p_select_all
    assign irq_f2p_i[19:0] = {Core1_nFIQ,Core0_nFIQ,Core1_nIRQ,Core0_nIRQ,IRQ_F2P[15:0]};
  end else begin : irq_f2p_select
	if (C_IRQ_F2P_MODE == "DIRECT") begin
    assign irq_f2p_i[19:0] = {Core1_nFIQ,Core0_nFIQ,Core1_nIRQ,Core0_nIRQ,
				irq_f2p_null[(15-C_NUM_F2P_INTR_INPUTS):0],
				IRQ_F2P[(C_NUM_F2P_INTR_INPUTS-1):0]};
	end else begin
	assign irq_f2p_i[19:0] = {Core1_nFIQ,Core0_nFIQ,Core1_nIRQ,Core0_nIRQ,
				IRQ_F2P[(C_NUM_F2P_INTR_INPUTS-1):0],
				irq_f2p_null[(15-C_NUM_F2P_INTR_INPUTS):0]};
	end
  end
endgenerate

assign M_AXI_GP0_ARSIZE[2:0] = {1'b0, M_AXI_GP0_ARSIZE_i[1:0]};
assign M_AXI_GP0_AWSIZE[2:0] = {1'b0, M_AXI_GP0_AWSIZE_i[1:0]};
assign M_AXI_GP1_ARSIZE[2:0] = {1'b0, M_AXI_GP1_ARSIZE_i[1:0]};
assign M_AXI_GP1_AWSIZE[2:0] = {1'b0, M_AXI_GP1_AWSIZE_i[1:0]};



// Compress Function

   
// Modified as per CR 631955   
//function [11:0] uncompress_id; 
//   input [5:0] id; 
//      begin 
//         case (id[5:0]) 
//            // dmac0 
//            6'd1 : uncompress_id = 12'b010000_1000_00 ; 
//            6'd2 : uncompress_id = 12'b010000_0000_00 ; 
//            6'd3 : uncompress_id = 12'b010000_0001_00 ; 
//            6'd4 : uncompress_id = 12'b010000_0010_00 ; 
//            6'd5 : uncompress_id = 12'b010000_0011_00 ; 
//            6'd6 : uncompress_id = 12'b010000_0100_00 ; 
//            6'd7 : uncompress_id = 12'b010000_0101_00 ; 
//            6'd8 : uncompress_id = 12'b010000_0110_00 ; 
//            6'd9 : uncompress_id = 12'b010000_0111_00 ; 
//            // ioum 
//            6'd10 : uncompress_id = 12'b0100000_000_01 ; 
//            6'd11 : uncompress_id = 12'b0100000_001_01 ; 
//            6'd12 : uncompress_id = 12'b0100000_010_01 ; 
//            6'd13 : uncompress_id = 12'b0100000_011_01 ; 
//            6'd14 : uncompress_id = 12'b0100000_100_01 ; 
//            6'd15 : uncompress_id = 12'b0100000_101_01 ; 
//            // devci 
//            6'd16 : uncompress_id = 12'b1000_0000_0000 ; 
//            // dap 
//            6'd17 : uncompress_id = 12'b1000_0000_0001 ; 
//            // l2m1 (CPU000) 
//            6'd18 : uncompress_id = 12'b11_000_000_00_00 ; 
//            6'd19 : uncompress_id = 12'b11_010_000_00_00 ; 
//            6'd20 : uncompress_id = 12'b11_011_000_00_00 ; 
//            6'd21 : uncompress_id = 12'b11_100_000_00_00 ; 
//            6'd22 : uncompress_id = 12'b11_101_000_00_00 ; 
//            6'd23 : uncompress_id = 12'b11_110_000_00_00 ; 
//            6'd24 : uncompress_id = 12'b11_111_000_00_00 ; 
//            // l2m1 (CPU001) 
//            6'd25 : uncompress_id = 12'b11_000_001_00_00 ; 
//            6'd26 : uncompress_id = 12'b11_010_001_00_00 ; 
//            6'd27 : uncompress_id = 12'b11_011_001_00_00 ; 
//            6'd28 : uncompress_id = 12'b11_100_001_00_00 ; 
//            6'd29 : uncompress_id = 12'b11_101_001_00_00 ; 
//            6'd30 : uncompress_id = 12'b11_110_001_00_00 ; 
//            6'd31 : uncompress_id = 12'b11_111_001_00_00 ; 
//            // l2m1 (L2CC) 
//            6'd32 : uncompress_id = 12'b11_000_00101_00 ; 
//            6'd33 : uncompress_id = 12'b11_000_01001_00 ; 
//            6'd34 : uncompress_id = 12'b11_000_01101_00 ; 
//            6'd35 : uncompress_id = 12'b11_000_10011_00 ; 
//            6'd36 : uncompress_id = 12'b11_000_10111_00 ; 
//            6'd37 : uncompress_id = 12'b11_000_11011_00 ; 
//            6'd38 : uncompress_id = 12'b11_000_11111_00 ; 
//            6'd39 : uncompress_id = 12'b11_000_00011_00 ; 
//            6'd40 : uncompress_id = 12'b11_000_00111_00 ; 
//            6'd41 : uncompress_id = 12'b11_000_01011_00 ; 
//            6'd42 : uncompress_id = 12'b11_000_01111_00 ; 
//            6'd43 : uncompress_id = 12'b11_000_00001_00 ; 
//            // l2m1 (ACP) 
//            6'd44 : uncompress_id = 12'b11_000_10000_00 ; 
//            6'd45 : uncompress_id = 12'b11_001_10000_00 ; 
//            6'd46 : uncompress_id = 12'b11_010_10000_00 ; 
//            6'd47 : uncompress_id = 12'b11_011_10000_00 ; 
//            6'd48 : uncompress_id = 12'b11_100_10000_00 ; 
//            6'd49 : uncompress_id = 12'b11_101_10000_00 ; 
//            6'd50 : uncompress_id = 12'b11_110_10000_00 ; 
//            6'd51 : uncompress_id = 12'b11_111_10000_00 ; 
//         default : uncompress_id = ~0; 
//      endcase 
//   end 
//endfunction 
// 
//function [5:0] compress_id; 
//   input [11:0] id; 
//      begin 
//         case (id[11:0]) 
//         // dmac0 
//            12'b010000_1000_00 : compress_id = 'd1 ; 
//            12'b010000_0000_00 : compress_id = 'd2 ; 
//            12'b010000_0001_00 : compress_id = 'd3 ; 
//            12'b010000_0010_00 : compress_id = 'd4 ; 
//            12'b010000_0011_00 : compress_id = 'd5 ; 
//            12'b010000_0100_00 : compress_id = 'd6 ; 
//            12'b010000_0101_00 : compress_id = 'd7 ; 
//            12'b010000_0110_00 : compress_id = 'd8 ; 
//            12'b010000_0111_00 : compress_id = 'd9 ; 
//            // ioum 
//            12'b0100000_000_01 : compress_id = 'd10 ; 
//            12'b0100000_001_01 : compress_id = 'd11 ; 
//            12'b0100000_010_01 : compress_id = 'd12 ; 
//            12'b0100000_011_01 : compress_id = 'd13 ; 
//            12'b0100000_100_01 : compress_id = 'd14 ; 
//            12'b0100000_101_01 : compress_id = 'd15 ; 
//            // devci 
//            12'b1000_0000_0000 : compress_id = 'd16 ; 
//            // dap 
//            12'b1000_0000_0001 : compress_id = 'd17 ; 
//            // l2m1 (CPU000) 
//            12'b11_000_000_00_00 : compress_id = 'd18 ; 
//            12'b11_010_000_00_00 : compress_id = 'd19 ; 
//            12'b11_011_000_00_00 : compress_id = 'd20 ; 
//            12'b11_100_000_00_00 : compress_id = 'd21 ; 
//            12'b11_101_000_00_00 : compress_id = 'd22 ; 
//            12'b11_110_000_00_00 : compress_id = 'd23 ; 
//            12'b11_111_000_00_00 : compress_id = 'd24 ; 
//            // l2m1 (CPU001) 
//            12'b11_000_001_00_00 : compress_id = 'd25 ; 
//            12'b11_010_001_00_00 : compress_id = 'd26 ; 
//            12'b11_011_001_00_00 : compress_id = 'd27 ; 
//            12'b11_100_001_00_00 : compress_id = 'd28 ; 
//            12'b11_101_001_00_00 : compress_id = 'd29 ; 
//            12'b11_110_001_00_00 : compress_id = 'd30 ; 
//            12'b11_111_001_00_00 : compress_id = 'd31 ; 
//            // l2m1 (L2CC) 
//            12'b11_000_00101_00 : compress_id = 'd32 ; 
//            12'b11_000_01001_00 : compress_id = 'd33 ; 
//            12'b11_000_01101_00 : compress_id = 'd34 ; 
//            12'b11_000_10011_00 : compress_id = 'd35 ; 
//            12'b11_000_10111_00 : compress_id = 'd36 ; 
//            12'b11_000_11011_00 : compress_id = 'd37 ; 
//            12'b11_000_11111_00 : compress_id = 'd38 ; 
//            12'b11_000_00011_00 : compress_id = 'd39 ; 
//            12'b11_000_00111_00 : compress_id = 'd40 ; 
//            12'b11_000_01011_00 : compress_id = 'd41 ; 
//            12'b11_000_01111_00 : compress_id = 'd42 ; 
//            12'b11_000_00001_00 : compress_id = 'd43 ; 
//            // l2m1 (ACP) 
//            12'b11_000_10000_00 : compress_id = 'd44 ; 
//            12'b11_001_10000_00 : compress_id = 'd45 ; 
//            12'b11_010_10000_00 : compress_id = 'd46 ; 
//            12'b11_011_10000_00 : compress_id = 'd47 ; 
//            12'b11_100_10000_00 : compress_id = 'd48 ; 
//            12'b11_101_10000_00 : compress_id = 'd49 ; 
//            12'b11_110_10000_00 : compress_id = 'd50 ; 
//            12'b11_111_10000_00 : compress_id = 'd51 ; 
//         default: compress_id = ~0; 
//      endcase 
//   end 
//endfunction 

// Modified as per CR 648393

	function [5:0] compress_id; 
		input [11:0] id; 
			begin 
				compress_id[0] = id[7] | (id[4] & id[2]) | (~id[11] & id[2]) | (id[11] & id[0]); 
				compress_id[1] = id[8] | id[5] | (~id[11] & id[3]); 
				compress_id[2] = id[9] | (id[6] & id[3] & id[2]) | (~id[11] & id[4]); 
				compress_id[3] = (id[11] & id[10] & id[4]) | (id[11] & id[10] & id[2]) | (~id[11] & id[10] & ~id[5] & ~id[0]); 
				compress_id[4] = (id[11] & id[3]) | (id[10] & id[0]) | (id[11] & id[10] & ~id[2] &~id[6]); 
				compress_id[5] = id[11] & id[10] & ~id[3]; 
			end 
	endfunction 

	function [11:0] uncompress_id; 
		input [5:0] id; 
			begin 
				case (id[5:0]) 
					// dmac0 
					6'b000_010 : uncompress_id = 12'b010000_1000_00 ; 
					6'b001_000 : uncompress_id = 12'b010000_0000_00 ; 
					6'b001_001 : uncompress_id = 12'b010000_0001_00 ; 
					6'b001_010 : uncompress_id = 12'b010000_0010_00 ; 
					6'b001_011 : uncompress_id = 12'b010000_0011_00 ; 
					6'b001_100 : uncompress_id = 12'b010000_0100_00 ; 
					6'b001_101 : uncompress_id = 12'b010000_0101_00 ; 
					6'b001_110 : uncompress_id = 12'b010000_0110_00 ; 
					6'b001_111 : uncompress_id = 12'b010000_0111_00 ; 
					// ioum 
					6'b010_000 : uncompress_id = 12'b0100000_000_01 ; 
					6'b010_001 : uncompress_id = 12'b0100000_001_01 ; 
					6'b010_010 : uncompress_id = 12'b0100000_010_01 ; 
					6'b010_011 : uncompress_id = 12'b0100000_011_01 ; 
					6'b010_100 : uncompress_id = 12'b0100000_100_01 ; 
					6'b010_101 : uncompress_id = 12'b0100000_101_01 ; 
					// devci 
					6'b000_000 : uncompress_id = 12'b1000_0000_0000 ; 
					// dap 
					6'b000_001 : uncompress_id = 12'b1000_0000_0001 ; 
					// l2m1 (CPU000) 
					6'b110_000 : uncompress_id = 12'b11_000_000_00_00 ; 
					6'b110_010 : uncompress_id = 12'b11_010_000_00_00 ; 
					6'b110_011 : uncompress_id = 12'b11_011_000_00_00 ; 
					6'b110_100 : uncompress_id = 12'b11_100_000_00_00 ; 
					6'b110_101 : uncompress_id = 12'b11_101_000_00_00 ; 
					6'b110_110 : uncompress_id = 12'b11_110_000_00_00 ; 
					6'b110_111 : uncompress_id = 12'b11_111_000_00_00 ; 
					// l2m1 (CPU001) 
					6'b111_000 : uncompress_id = 12'b11_000_001_00_00 ; 
					6'b111_010 : uncompress_id = 12'b11_010_001_00_00 ; 
					6'b111_011 : uncompress_id = 12'b11_011_001_00_00 ; 
					6'b111_100 : uncompress_id = 12'b11_100_001_00_00 ; 
					6'b111_101 : uncompress_id = 12'b11_101_001_00_00 ; 
					6'b111_110 : uncompress_id = 12'b11_110_001_00_00 ; 
					6'b111_111 : uncompress_id = 12'b11_111_001_00_00 ; 
					// l2m1 (L2CC) 
					6'b101_001 : uncompress_id = 12'b11_000_00101_00 ; 
					6'b101_010 : uncompress_id = 12'b11_000_01001_00 ; 
					6'b101_011 : uncompress_id = 12'b11_000_01101_00 ; 
					6'b011_100 : uncompress_id = 12'b11_000_10011_00 ; 
					6'b011_101 : uncompress_id = 12'b11_000_10111_00 ; 
					6'b011_110 : uncompress_id = 12'b11_000_11011_00 ; 
					6'b011_111 : uncompress_id = 12'b11_000_11111_00 ; 
					6'b011_000 : uncompress_id = 12'b11_000_00011_00 ; 
					6'b011_001 : uncompress_id = 12'b11_000_00111_00 ; 
					6'b011_010 : uncompress_id = 12'b11_000_01011_00 ; 
					6'b011_011 : uncompress_id = 12'b11_000_01111_00 ; 
					6'b101_000 : uncompress_id = 12'b11_000_00001_00 ; 
					// l2m1 (ACP) 
					6'b100_000 : uncompress_id = 12'b11_000_10000_00 ; 
					6'b100_001 : uncompress_id = 12'b11_001_10000_00 ; 
					6'b100_010 : uncompress_id = 12'b11_010_10000_00 ; 
					6'b100_011 : uncompress_id = 12'b11_011_10000_00 ; 
					6'b100_100 : uncompress_id = 12'b11_100_10000_00 ; 
					6'b100_101 : uncompress_id = 12'b11_101_10000_00 ; 
					6'b100_110 : uncompress_id = 12'b11_110_10000_00 ; 
					6'b100_111 : uncompress_id = 12'b11_111_10000_00 ; 
					default : uncompress_id = 12'hx ; 
				endcase 
			end 
	endfunction

   
// Static Remap logic Enablement and Disablement for C_M_AXI0 port
        
        assign M_AXI_GP0_AWID        = (C_M_AXI_GP0_ENABLE_STATIC_REMAP == 1) ? compress_id(M_AXI_GP0_AWID_FULL) : M_AXI_GP0_AWID_FULL;
        assign M_AXI_GP0_WID         = (C_M_AXI_GP0_ENABLE_STATIC_REMAP == 1) ? compress_id(M_AXI_GP0_WID_FULL)  : M_AXI_GP0_WID_FULL;   
        assign M_AXI_GP0_ARID        = (C_M_AXI_GP0_ENABLE_STATIC_REMAP == 1) ? compress_id(M_AXI_GP0_ARID_FULL) : M_AXI_GP0_ARID_FULL;      
        assign M_AXI_GP0_BID_FULL    = (C_M_AXI_GP0_ENABLE_STATIC_REMAP == 1) ? uncompress_id(M_AXI_GP0_BID)     : M_AXI_GP0_BID;
        assign M_AXI_GP0_RID_FULL    = (C_M_AXI_GP0_ENABLE_STATIC_REMAP == 1) ? uncompress_id(M_AXI_GP0_RID)     : M_AXI_GP0_RID;      

  // Static Remap logic Enablement and Disablement for C_M_AXI1 port   

        assign M_AXI_GP1_AWID        = (C_M_AXI_GP1_ENABLE_STATIC_REMAP == 1) ? compress_id(M_AXI_GP1_AWID_FULL) : M_AXI_GP1_AWID_FULL;
        assign M_AXI_GP1_WID         = (C_M_AXI_GP1_ENABLE_STATIC_REMAP == 1) ? compress_id(M_AXI_GP1_WID_FULL)  : M_AXI_GP1_WID_FULL;   
        assign M_AXI_GP1_ARID        = (C_M_AXI_GP1_ENABLE_STATIC_REMAP == 1) ? compress_id(M_AXI_GP1_ARID_FULL) : M_AXI_GP1_ARID_FULL;      
        assign M_AXI_GP1_BID_FULL    = (C_M_AXI_GP1_ENABLE_STATIC_REMAP == 1) ? uncompress_id(M_AXI_GP1_BID)     : M_AXI_GP1_BID;
        assign M_AXI_GP1_RID_FULL    = (C_M_AXI_GP1_ENABLE_STATIC_REMAP == 1) ? uncompress_id(M_AXI_GP1_RID)     : M_AXI_GP1_RID;      


//// Compress_id and uncompress_id has been removed to address CR 642527
//// AXI interconnect v1.05.a and beyond implements dynamic ID compression/decompression.
//        assign M_AXI_GP0_AWID        =  M_AXI_GP0_AWID_FULL;
//        assign M_AXI_GP0_WID         =  M_AXI_GP0_WID_FULL;   
//        assign M_AXI_GP0_ARID        =  M_AXI_GP0_ARID_FULL;      
//        assign M_AXI_GP0_BID_FULL    =  M_AXI_GP0_BID;
//        assign M_AXI_GP0_RID_FULL    =  M_AXI_GP0_RID;      
//
//        assign M_AXI_GP1_AWID        =  M_AXI_GP1_AWID_FULL;
//        assign M_AXI_GP1_WID         =  M_AXI_GP1_WID_FULL;   
//        assign M_AXI_GP1_ARID        =  M_AXI_GP1_ARID_FULL;      
//        assign M_AXI_GP1_BID_FULL    =  M_AXI_GP1_BID;
//        assign M_AXI_GP1_RID_FULL    =  M_AXI_GP1_RID;      
						  
  
// Pipeline Stage for ENET0
	
generate
  if (C_EN_EMIO_ENET0 == 1) begin
  always @(posedge ENET0_GMII_TX_CLK)
  begin
      ENET0_GMII_TXD    <= ENET0_GMII_TXD_i;
      ENET0_GMII_TX_EN  <= ENET0_GMII_TX_EN_i; //1'b0; //ENET0_GMII_TX_EN_i;
	  ENET0_GMII_TX_ER  <= ENET0_GMII_TX_ER_i; //1'b0;//ENET0_GMII_TX_ER_i;
      ENET0_GMII_COL_i  <= ENET0_GMII_COL;
      ENET0_GMII_CRS_i  <= ENET0_GMII_CRS;
    end
	end
	else
	always@*
	 begin
	  ENET0_GMII_TXD    <= 'b0;//ENET0_GMII_TXD_i;
      ENET0_GMII_TX_EN  <= 'b0;//ENET0_GMII_TX_EN_i; //1'b0; //ENET0_GMII_TX_EN_i;
	  ENET0_GMII_TX_ER  <= 'b0;//ENET0_GMII_TX_ER_i; //1'b0;//ENET0_GMII_TX_ER_i;
	  ENET0_GMII_COL_i <= 'b0;
	  ENET0_GMII_CRS_i <= 'b0;
	 end  
endgenerate
  
generate
  if (C_EN_EMIO_ENET0 == 1) begin 
    always @(posedge ENET0_GMII_RX_CLK) 
    begin
      ENET0_GMII_RXD_i    <= ENET0_GMII_RXD;
      ENET0_GMII_RX_DV_i  <= ENET0_GMII_RX_DV;
      ENET0_GMII_RX_ER_i  <= ENET0_GMII_RX_ER;
    end
  end
	else
	begin
	always @*
	begin
	ENET0_GMII_RXD_i    <= 0;
   ENET0_GMII_RX_DV_i  <= 0;
    ENET0_GMII_RX_ER_i  <= 0;
	end
	end
endgenerate

// Pipeline Stage for ENET1
	
generate
  if (C_EN_EMIO_ENET1 == 1) begin 
    always @(posedge ENET1_GMII_TX_CLK) 
    begin
      ENET1_GMII_TXD    <= ENET1_GMII_TXD_i;
      ENET1_GMII_TX_EN  <= ENET1_GMII_TX_EN_i;
      ENET1_GMII_TX_ER  <= ENET1_GMII_TX_ER_i;
      ENET1_GMII_COL_i  <= ENET1_GMII_COL;
      ENET1_GMII_CRS_i  <= ENET1_GMII_CRS;
    end
  end
  else
  begin
  always@*
	 begin
	  ENET1_GMII_TXD    <= 'b0;//ENET0_GMII_TXD_i;
      ENET1_GMII_TX_EN  <= 'b0;//ENET0_GMII_TX_EN_i; //1'b0; //ENET0_GMII_TX_EN_i;
	  ENET1_GMII_TX_ER  <= 'b0;//ENET0_GMII_TX_ER_i; //1'b0;//ENET0_GMII_TX_ER_i;
	  ENET1_GMII_COL_i <= 0;
	  ENET1_GMII_CRS_i <= 0;
	 end  
  end
endgenerate
   
generate	
  if (C_EN_EMIO_ENET1 == 1) begin 
    always @(posedge ENET1_GMII_RX_CLK) 
    begin
      ENET1_GMII_RXD_i    <= ENET1_GMII_RXD;
      ENET1_GMII_RX_DV_i  <= ENET1_GMII_RX_DV;
      ENET1_GMII_RX_ER_i  <= ENET1_GMII_RX_ER;
    end
  end	
else
	begin
	always @*
	begin
	ENET1_GMII_RXD_i    <= 'b0;
   ENET1_GMII_RX_DV_i  <= 'b0;
  ENET1_GMII_RX_ER_i  <= 'b0;
	end
	end  
endgenerate   
   
// Trace buffer instantiated when C_INCLUDE_TRACE_BUFFER is 1.

generate
  if (C_EN_EMIO_TRACE == 1)  begin
    if (C_INCLUDE_TRACE_BUFFER == 0) begin : gen_no_trace_buffer
        
      // Pipeline Stage for Traceport ATID
      always @(posedge FTMD_TRACEIN_CLK) 
      begin
       	FTMD_TRACEIN_DATA_notracebuf    <= FTMD_TRACEIN_DATA;
        FTMD_TRACEIN_VALID_notracebuf   <= FTMD_TRACEIN_VALID;
	FTMD_TRACEIN_ATID_notracebuf    <= FTMD_TRACEIN_ATID;
      end

      assign FTMD_TRACEIN_DATA_i   = FTMD_TRACEIN_DATA_notracebuf;
      assign FTMD_TRACEIN_VALID_i  = FTMD_TRACEIN_VALID_notracebuf;
      assign FTMD_TRACEIN_ATID_i   = FTMD_TRACEIN_ATID_notracebuf;

    end else begin : gen_trace_buffer
    
      processing_system7_v5_5_trace_buffer #(.FIFO_SIZE (C_TRACE_BUFFER_FIFO_SIZE),
      .USE_TRACE_DATA_EDGE_DETECTOR(USE_TRACE_DATA_EDGE_DETECTOR),
      .C_DELAY_CLKS(C_TRACE_BUFFER_CLOCK_DELAY)
       )
      trace_buffer_i (
        .TRACE_CLK(FTMD_TRACEIN_CLK), 
        .RST(~FCLK_RESET0_N), 
        .TRACE_VALID_IN(FTMD_TRACEIN_VALID), 
        .TRACE_DATA_IN(FTMD_TRACEIN_DATA), 
        .TRACE_ATID_IN(FTMD_TRACEIN_ATID), 
        .TRACE_ATID_OUT(FTMD_TRACEIN_ATID_tracebuf), 
        .TRACE_VALID_OUT(FTMD_TRACEIN_VALID_tracebuf), 
        .TRACE_DATA_OUT(FTMD_TRACEIN_DATA_tracebuf)
      );

      assign FTMD_TRACEIN_DATA_i   = FTMD_TRACEIN_DATA_tracebuf;
      assign FTMD_TRACEIN_VALID_i  = FTMD_TRACEIN_VALID_tracebuf;
      assign FTMD_TRACEIN_ATID_i   = FTMD_TRACEIN_ATID_tracebuf;
 
    end
  end
  else
  begin
  assign FTMD_TRACEIN_DATA_i   = 1'b0;
      assign FTMD_TRACEIN_VALID_i  = 1'b0;
      assign FTMD_TRACEIN_ATID_i   = 1'b0;
	  end
endgenerate
  
   
   // ID Width Control on AXI Slave ports
   // S_AXI_GP0
   
     function [5:0] id_in_gp0;
       input [(C_S_AXI_GP0_ID_WIDTH - 1) : 0] axi_id_gp0_in;
     begin
        case (C_S_AXI_GP0_ID_WIDTH)
              1:  id_in_gp0  = {5'b0, axi_id_gp0_in};
              2:  id_in_gp0  = {4'b0, axi_id_gp0_in};
              3:  id_in_gp0  = {3'b0, axi_id_gp0_in};
              4:  id_in_gp0  = {2'b0, axi_id_gp0_in};
              5:  id_in_gp0  = {1'b0, axi_id_gp0_in};
              6:  id_in_gp0  = axi_id_gp0_in;    
              default : id_in_gp0 =  axi_id_gp0_in;
        endcase
     end
     endfunction

    assign S_AXI_GP0_ARID_in = id_in_gp0(S_AXI_GP0_ARID);
    assign S_AXI_GP0_AWID_in = id_in_gp0(S_AXI_GP0_AWID);
    assign S_AXI_GP0_WID_in  = id_in_gp0(S_AXI_GP0_WID);

     function [5:0] id_out_gp0;
       input [(C_S_AXI_GP0_ID_WIDTH - 1) : 0] axi_id_gp0_out;
     begin
        case (C_S_AXI_GP0_ID_WIDTH)
              1:  id_out_gp0  = axi_id_gp0_out[0];
              2:  id_out_gp0  = axi_id_gp0_out[1:0];
              3:  id_out_gp0  = axi_id_gp0_out[2:0];
              4:  id_out_gp0  = axi_id_gp0_out[3:0];
              5:  id_out_gp0  = axi_id_gp0_out[4:0];
              6:  id_out_gp0  = axi_id_gp0_out;    
              default : id_out_gp0 =  axi_id_gp0_out;              
        endcase
     end
     endfunction
    
    assign S_AXI_GP0_BID     = id_out_gp0(S_AXI_GP0_BID_out);
    assign S_AXI_GP0_RID     = id_out_gp0(S_AXI_GP0_RID_out);    
   
   // S_AXI_GP1
   
     function [5:0] id_in_gp1;
       input [(C_S_AXI_GP1_ID_WIDTH - 1) : 0] axi_id_gp1_in;
     begin
        case (C_S_AXI_GP1_ID_WIDTH)
              1:  id_in_gp1  = {5'b0, axi_id_gp1_in};
              2:  id_in_gp1  = {4'b0, axi_id_gp1_in};
              3:  id_in_gp1  = {3'b0, axi_id_gp1_in};
              4:  id_in_gp1  = {2'b0, axi_id_gp1_in};
              5:  id_in_gp1  = {1'b0, axi_id_gp1_in};
              6:  id_in_gp1  = axi_id_gp1_in;    
              default : id_in_gp1 =  axi_id_gp1_in;
        endcase
     end
     endfunction

    assign S_AXI_GP1_ARID_in = id_in_gp1(S_AXI_GP1_ARID);
    assign S_AXI_GP1_AWID_in = id_in_gp1(S_AXI_GP1_AWID);
    assign S_AXI_GP1_WID_in  = id_in_gp1(S_AXI_GP1_WID);

     function [5:0] id_out_gp1;
       input [(C_S_AXI_GP1_ID_WIDTH - 1) : 0] axi_id_gp1_out;
     begin
        case (C_S_AXI_GP1_ID_WIDTH)
              1:  id_out_gp1  = axi_id_gp1_out[0];
              2:  id_out_gp1  = axi_id_gp1_out[1:0];
              3:  id_out_gp1  = axi_id_gp1_out[2:0];
              4:  id_out_gp1  = axi_id_gp1_out[3:0];
              5:  id_out_gp1  = axi_id_gp1_out[4:0];
              6:  id_out_gp1  = axi_id_gp1_out;    
              default : id_out_gp1 =  axi_id_gp1_out;              
        endcase
     end
     endfunction
    
    assign S_AXI_GP1_BID     = id_out_gp1(S_AXI_GP1_BID_out);
    assign S_AXI_GP1_RID     = id_out_gp1(S_AXI_GP1_RID_out);    
    
// S_AXI_HP0    
    
     function [5:0] id_in_hp0;
       input [(C_S_AXI_HP0_ID_WIDTH - 1) : 0] axi_id_hp0_in;
     begin
        case (C_S_AXI_HP0_ID_WIDTH)
              1:  id_in_hp0  = {5'b0, axi_id_hp0_in};
              2:  id_in_hp0  = {4'b0, axi_id_hp0_in};
              3:  id_in_hp0  = {3'b0, axi_id_hp0_in};
              4:  id_in_hp0  = {2'b0, axi_id_hp0_in};
              5:  id_in_hp0  = {1'b0, axi_id_hp0_in};
              6:  id_in_hp0  = axi_id_hp0_in;    
              default : id_in_hp0 =  axi_id_hp0_in;
        endcase
     end
     endfunction

    assign S_AXI_HP0_ARID_in = id_in_hp0(S_AXI_HP0_ARID);
    assign S_AXI_HP0_AWID_in = id_in_hp0(S_AXI_HP0_AWID);
    assign S_AXI_HP0_WID_in  = id_in_hp0(S_AXI_HP0_WID);

     function [5:0] id_out_hp0;
       input [(C_S_AXI_HP0_ID_WIDTH - 1) : 0] axi_id_hp0_out;
     begin
        case (C_S_AXI_HP0_ID_WIDTH)
              1:  id_out_hp0  = axi_id_hp0_out[0];
              2:  id_out_hp0  = axi_id_hp0_out[1:0];
              3:  id_out_hp0  = axi_id_hp0_out[2:0];
              4:  id_out_hp0  = axi_id_hp0_out[3:0];
              5:  id_out_hp0  = axi_id_hp0_out[4:0];
              6:  id_out_hp0  = axi_id_hp0_out;    
              default : id_out_hp0 =  axi_id_hp0_out;              
        endcase
     end
     endfunction
    
    assign S_AXI_HP0_BID     = id_out_hp0(S_AXI_HP0_BID_out);
    assign S_AXI_HP0_RID     = id_out_hp0(S_AXI_HP0_RID_out);  
    
    assign S_AXI_HP0_WDATA_in        = (C_S_AXI_HP0_DATA_WIDTH == 64) ? S_AXI_HP0_WDATA : {32'b0,S_AXI_HP0_WDATA};
    assign S_AXI_HP0_WSTRB_in        = (C_S_AXI_HP0_DATA_WIDTH == 64) ? S_AXI_HP0_WSTRB : {4'b0,S_AXI_HP0_WSTRB};       
    assign S_AXI_HP0_RDATA           = (C_S_AXI_HP0_DATA_WIDTH == 64) ? S_AXI_HP0_RDATA_out : S_AXI_HP0_RDATA_out[31:0];
    
// S_AXI_HP1    

     function [5:0] id_in_hp1;
       input [(C_S_AXI_HP1_ID_WIDTH - 1) : 0] axi_id_hp1_in;
     begin
        case (C_S_AXI_HP1_ID_WIDTH)
              1:  id_in_hp1  = {5'b0, axi_id_hp1_in};
              2:  id_in_hp1  = {4'b0, axi_id_hp1_in};
              3:  id_in_hp1  = {3'b0, axi_id_hp1_in};
              4:  id_in_hp1  = {2'b0, axi_id_hp1_in};
              5:  id_in_hp1  = {1'b0, axi_id_hp1_in};
              6:  id_in_hp1  = axi_id_hp1_in;    
              default : id_in_hp1 =  axi_id_hp1_in;
        endcase
     end
     endfunction
     
     

    assign S_AXI_HP1_ARID_in = id_in_hp1(S_AXI_HP1_ARID);
    assign S_AXI_HP1_AWID_in = id_in_hp1(S_AXI_HP1_AWID);
    assign S_AXI_HP1_WID_in  = id_in_hp1(S_AXI_HP1_WID);

     function [5:0] id_out_hp1;
       input [(C_S_AXI_HP1_ID_WIDTH - 1) : 0] axi_id_hp1_out;
     begin
        case (C_S_AXI_HP1_ID_WIDTH)
              1:  id_out_hp1  = axi_id_hp1_out[0];
              2:  id_out_hp1  = axi_id_hp1_out[1:0];
              3:  id_out_hp1  = axi_id_hp1_out[2:0];
              4:  id_out_hp1  = axi_id_hp1_out[3:0];
              5:  id_out_hp1  = axi_id_hp1_out[4:0];
              6:  id_out_hp1  = axi_id_hp1_out;    
              default : id_out_hp1 =  axi_id_hp1_out;              
        endcase
     end
     endfunction
    
    assign S_AXI_HP1_BID     = id_out_hp1(S_AXI_HP1_BID_out);
    assign S_AXI_HP1_RID     = id_out_hp1(S_AXI_HP1_RID_out); 
    
    assign S_AXI_HP1_WDATA_in        = (C_S_AXI_HP1_DATA_WIDTH == 64) ? S_AXI_HP1_WDATA : {32'b0,S_AXI_HP1_WDATA};
    assign S_AXI_HP1_WSTRB_in        = (C_S_AXI_HP1_DATA_WIDTH == 64) ? S_AXI_HP1_WSTRB : {4'b0,S_AXI_HP1_WSTRB};       
    assign S_AXI_HP1_RDATA           = (C_S_AXI_HP1_DATA_WIDTH == 64) ? S_AXI_HP1_RDATA_out : S_AXI_HP1_RDATA_out[31:0];
    
    
// S_AXI_HP2    

     function [5:0] id_in_hp2;
       input [(C_S_AXI_HP2_ID_WIDTH - 1) : 0] axi_id_hp2_in;
     begin
        case (C_S_AXI_HP2_ID_WIDTH)
              1:  id_in_hp2  = {5'b0, axi_id_hp2_in};
              2:  id_in_hp2  = {4'b0, axi_id_hp2_in};
              3:  id_in_hp2  = {3'b0, axi_id_hp2_in};
              4:  id_in_hp2  = {2'b0, axi_id_hp2_in};
              5:  id_in_hp2  = {1'b0, axi_id_hp2_in};
              6:  id_in_hp2  = axi_id_hp2_in;    
              default : id_in_hp2 =  axi_id_hp2_in;
        endcase
     end
     endfunction
     
    assign S_AXI_HP2_ARID_in = id_in_hp2(S_AXI_HP2_ARID);
    assign S_AXI_HP2_AWID_in = id_in_hp2(S_AXI_HP2_AWID);
    assign S_AXI_HP2_WID_in  = id_in_hp2(S_AXI_HP2_WID);
 

     function [5:0] id_out_hp2;
       input [(C_S_AXI_HP2_ID_WIDTH - 1) : 0] axi_id_hp2_out;
     begin
        case (C_S_AXI_HP2_ID_WIDTH)
              1:  id_out_hp2  = axi_id_hp2_out[0];
              2:  id_out_hp2  = axi_id_hp2_out[1:0];
              3:  id_out_hp2  = axi_id_hp2_out[2:0];
              4:  id_out_hp2  = axi_id_hp2_out[3:0];
              5:  id_out_hp2  = axi_id_hp2_out[4:0];
              6:  id_out_hp2  = axi_id_hp2_out;    
              default : id_out_hp2 =  axi_id_hp2_out;              
        endcase
     end
     endfunction
    
    assign S_AXI_HP2_BID     = id_out_hp2(S_AXI_HP2_BID_out);
    assign S_AXI_HP2_RID     = id_out_hp2(S_AXI_HP2_RID_out);  
    
    assign S_AXI_HP2_WDATA_in        = (C_S_AXI_HP2_DATA_WIDTH == 64) ? S_AXI_HP2_WDATA : {32'b0,S_AXI_HP2_WDATA};
    assign S_AXI_HP2_WSTRB_in        = (C_S_AXI_HP2_DATA_WIDTH == 64) ? S_AXI_HP2_WSTRB : {4'b0,S_AXI_HP2_WSTRB};       
    assign S_AXI_HP2_RDATA           = (C_S_AXI_HP2_DATA_WIDTH == 64) ? S_AXI_HP2_RDATA_out : S_AXI_HP2_RDATA_out[31:0];
    
    
// S_AXI_HP3    

     function [5:0] id_in_hp3;
       input [(C_S_AXI_HP3_ID_WIDTH - 1) : 0] axi_id_hp3_in;
     begin
        case (C_S_AXI_HP3_ID_WIDTH)
              1:  id_in_hp3  = {5'b0, axi_id_hp3_in};
              2:  id_in_hp3  = {4'b0, axi_id_hp3_in};
              3:  id_in_hp3  = {3'b0, axi_id_hp3_in};
              4:  id_in_hp3  = {2'b0, axi_id_hp3_in};
              5:  id_in_hp3  = {1'b0, axi_id_hp3_in};
              6:  id_in_hp3  = axi_id_hp3_in;    
              default : id_in_hp3 =  axi_id_hp3_in;
        endcase
     end
     endfunction
     
    assign S_AXI_HP3_ARID_in = id_in_hp3(S_AXI_HP3_ARID);
    assign S_AXI_HP3_AWID_in = id_in_hp3(S_AXI_HP3_AWID);
    assign S_AXI_HP3_WID_in  = id_in_hp3(S_AXI_HP3_WID);
     


     function [5:0] id_out_hp3;
       input [(C_S_AXI_HP3_ID_WIDTH - 1) : 0] axi_id_hp3_out;
     begin
        case (C_S_AXI_HP3_ID_WIDTH)
              1:  id_out_hp3  = axi_id_hp3_out[0];
              2:  id_out_hp3  = axi_id_hp3_out[1:0];
              3:  id_out_hp3  = axi_id_hp3_out[2:0];
              4:  id_out_hp3  = axi_id_hp3_out[3:0];
              5:  id_out_hp3  = axi_id_hp3_out[4:0];
              6:  id_out_hp3  = axi_id_hp3_out;    
              default : id_out_hp3 =  axi_id_hp3_out;              
        endcase
     end
     endfunction
    
    assign S_AXI_HP3_BID     = id_out_hp3(S_AXI_HP3_BID_out);
    assign S_AXI_HP3_RID     = id_out_hp3(S_AXI_HP3_RID_out); 
    
    assign S_AXI_HP3_WDATA_in        = (C_S_AXI_HP3_DATA_WIDTH == 64) ? S_AXI_HP3_WDATA : {32'b0,S_AXI_HP3_WDATA};
    assign S_AXI_HP3_WSTRB_in        = (C_S_AXI_HP3_DATA_WIDTH == 64) ? S_AXI_HP3_WSTRB : {4'b0,S_AXI_HP3_WSTRB};       
    assign S_AXI_HP3_RDATA           = (C_S_AXI_HP3_DATA_WIDTH == 64) ? S_AXI_HP3_RDATA_out : S_AXI_HP3_RDATA_out[31:0];
    
    
// S_AXI_ACP    

     function [2:0] id_in_acp;
       input [(C_S_AXI_ACP_ID_WIDTH - 1) : 0] axi_id_acp_in;
     begin
        case (C_S_AXI_ACP_ID_WIDTH)
              1:  id_in_acp  = {2'b0, axi_id_acp_in};
              2:  id_in_acp  = {1'b0, axi_id_acp_in};
              3:  id_in_acp  = axi_id_acp_in;
              default : id_in_acp =  axi_id_acp_in;
        endcase
     end
     endfunction

    assign S_AXI_ACP_ARID_in = id_in_acp(SAXIACPARID_W);
    assign S_AXI_ACP_AWID_in = id_in_acp(SAXIACPAWID_W);
    assign S_AXI_ACP_WID_in  = id_in_acp(SAXIACPWID_W);

     function [2:0] id_out_acp;
       input [(C_S_AXI_ACP_ID_WIDTH - 1) : 0] axi_id_acp_out;
     begin
        case (C_S_AXI_ACP_ID_WIDTH)
              1:  id_out_acp  = axi_id_acp_out[0];
              2:  id_out_acp  = axi_id_acp_out[1:0];
              3:  id_out_acp  = axi_id_acp_out;
              default : id_out_acp =  axi_id_acp_out;              
        endcase
     end
     endfunction
    
    assign SAXIACPBID_W     = id_out_acp(S_AXI_ACP_BID_out);
    assign SAXIACPRID_W     = id_out_acp(S_AXI_ACP_RID_out);  
    
// FMIO Tristate Inversion logic 

//FMIO I2C0
assign        I2C0_SDA_T  = ~ I2C0_SDA_T_n;
assign        I2C0_SCL_T  = ~ I2C0_SCL_T_n;
//FMIO I2C1                     
assign        I2C1_SDA_T  = ~ I2C1_SDA_T_n;
assign        I2C1_SCL_T  = ~ I2C1_SCL_T_n;
//FMIO SPI0             
assign        SPI0_SCLK_T = ~ SPI0_SCLK_T_n;
assign        SPI0_MOSI_T = ~ SPI0_MOSI_T_n;
assign        SPI0_MISO_T = ~ SPI0_MISO_T_n;
assign        SPI0_SS_T   = ~ SPI0_SS_T_n;
//FMIO SPI1             
assign        SPI1_SCLK_T = ~ SPI1_SCLK_T_n;
assign        SPI1_MOSI_T = ~ SPI1_MOSI_T_n;
assign        SPI1_MISO_T = ~ SPI1_MISO_T_n;
assign        SPI1_SS_T   = ~ SPI1_SS_T_n;



// EMIO GEM0 MDIO
assign        ENET0_MDIO_T = ~ ENET0_MDIO_T_n;
    
// EMIO GEM1 MDIO
assign        ENET1_MDIO_T = ~ ENET1_MDIO_T_n;

// EMIO GPIO
assign        GPIO_T = ~ GPIO_T_n;

// EMIO GPIO Width Control 

  function [63:0] gpio_width_adjust_in;
    input [(C_EMIO_GPIO_WIDTH - 1) : 0] gpio_in;
  begin
     case (C_EMIO_GPIO_WIDTH)
           1:  gpio_width_adjust_in   = {63'b0, gpio_in};
           2:  gpio_width_adjust_in   = {62'b0, gpio_in};
           3:  gpio_width_adjust_in   = {61'b0, gpio_in};
           4:  gpio_width_adjust_in   = {60'b0, gpio_in};
           5:  gpio_width_adjust_in   = {59'b0, gpio_in};
           6:  gpio_width_adjust_in   = {58'b0, gpio_in};
           7:  gpio_width_adjust_in   = {57'b0, gpio_in};
           8:  gpio_width_adjust_in   = {56'b0, gpio_in};
           9:  gpio_width_adjust_in   = {55'b0, gpio_in};
           10:  gpio_width_adjust_in  = {54'b0, gpio_in};
           11:  gpio_width_adjust_in  = {53'b0, gpio_in};
           12:  gpio_width_adjust_in  = {52'b0, gpio_in};
           13:  gpio_width_adjust_in  = {51'b0, gpio_in};
           14:  gpio_width_adjust_in  = {50'b0, gpio_in};
           15:  gpio_width_adjust_in  = {49'b0, gpio_in};
           16:  gpio_width_adjust_in  = {48'b0, gpio_in};
           17:  gpio_width_adjust_in  = {47'b0, gpio_in};
           18:  gpio_width_adjust_in  = {46'b0, gpio_in};
           19:  gpio_width_adjust_in  = {45'b0, gpio_in};
           20:  gpio_width_adjust_in  = {44'b0, gpio_in};
           21:  gpio_width_adjust_in  = {43'b0, gpio_in};
           22:  gpio_width_adjust_in  = {42'b0, gpio_in};
           23:  gpio_width_adjust_in  = {41'b0, gpio_in};
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
           29: gpio_width_adjust_out    = gpio_o[28:0];
           30: gpio_width_adjust_out    = gpio_o[29:0];
           31: gpio_width_adjust_out    = gpio_o[30:0];
           32: gpio_width_adjust_out    = gpio_o[31:0];
           33: gpio_width_adjust_out    = gpio_o[32:0];
           34: gpio_width_adjust_out    = gpio_o[33:0];
           35: gpio_width_adjust_out    = gpio_o[34:0];
           36: gpio_width_adjust_out    = gpio_o[35:0];
           37: gpio_width_adjust_out    = gpio_o[36:0];
           38: gpio_width_adjust_out    = gpio_o[37:0];
           39: gpio_width_adjust_out    = gpio_o[38:0];
           40: gpio_width_adjust_out    = gpio_o[39:0];
           41: gpio_width_adjust_out    = gpio_o[40:0];
           42: gpio_width_adjust_out    = gpio_o[41:0];
           43: gpio_width_adjust_out    = gpio_o[42:0];
           44: gpio_width_adjust_out    = gpio_o[43:0];
           45: gpio_width_adjust_out    = gpio_o[44:0];
           46: gpio_width_adjust_out    = gpio_o[45:0];
           47: gpio_width_adjust_out    = gpio_o[46:0];
           48: gpio_width_adjust_out    = gpio_o[47:0];
           49: gpio_width_adjust_out    = gpio_o[48:0];
           50: gpio_width_adjust_out    = gpio_o[49:0];
           51: gpio_width_adjust_out    = gpio_o[50:0];
           52: gpio_width_adjust_out    = gpio_o[51:0];
           53: gpio_width_adjust_out    = gpio_o[52:0];
           54: gpio_width_adjust_out    = gpio_o[53:0];
           55: gpio_width_adjust_out    = gpio_o[54:0];
           56: gpio_width_adjust_out    = gpio_o[55:0];
           57: gpio_width_adjust_out    = gpio_o[56:0];
           58: gpio_width_adjust_out    = gpio_o[57:0];
           59: gpio_width_adjust_out    = gpio_o[58:0];
           60: gpio_width_adjust_out    = gpio_o[59:0];
           61: gpio_width_adjust_out    = gpio_o[60:0];
           62: gpio_width_adjust_out    = gpio_o[61:0];
           63: gpio_width_adjust_out    = gpio_o[62:0];
           64: gpio_width_adjust_out    = gpio_o;    
           default : gpio_width_adjust_out =  gpio_o;
     endcase
  end
  endfunction

 assign GPIO_O[(C_EMIO_GPIO_WIDTH - 1) : 0]   = gpio_width_adjust_out(gpio_out);
 assign GPIO_T_n[(C_EMIO_GPIO_WIDTH - 1) : 0] = gpio_width_adjust_out(gpio_out_t_n);

// Adding OBUFT to JTAG out port
generate
  if ( C_EN_EMIO_PJTAG == 1 ) begin : PJTAG_OBUFT_TRUE
	OBUFT jtag_obuft_inst (
	.O(PJTAG_TDO),
	.I(PJTAG_TDO_O),
	.T(PJTAG_TDO_T)  
	);
  end
  else
  begin
  assign PJTAG_TDO = 1'b0;
  end
endgenerate
// -------
// EMIO PJTAG
assign        PJTAG_TDO_T = ~ PJTAG_TDO_T_n;

// EMIO SDIO0 : No negation required as per CR#636210 for 1.0 version of  Silicon,
// FOR Other SI REV, inversion is required
 
assign        SDIO0_CMD_T       =   (C_PS7_SI_REV == "1.0") ? (SDIO0_CMD_T_n) : (~ SDIO0_CMD_T_n);
assign        SDIO0_DATA_T[3:0] =   (C_PS7_SI_REV == "1.0") ? (SDIO0_DATA_T_n[3:0]) : (~ SDIO0_DATA_T_n[3:0]);

// EMIO SDIO1 : No negation required as per CR#636210 for 1.0 version of  Silicon,
// FOR Other SI REV, inversion is required
assign        SDIO1_CMD_T       =  (C_PS7_SI_REV == "1.0") ? (SDIO1_CMD_T_n) : (~ SDIO1_CMD_T_n);
assign        SDIO1_DATA_T[3:0] =  (C_PS7_SI_REV == "1.0") ? (SDIO1_DATA_T_n[3:0]) : (~ SDIO1_DATA_T_n[3:0]);

// FCLK_CLK optional clock buffers

generate
   if (C_FCLK_CLK0_BUF == "TRUE" | C_FCLK_CLK0_BUF == "true") begin : buffer_fclk_clk_0
     BUFG FCLK_CLK_0_BUFG (.I(FCLK_CLK_unbuffered[0]), .O(FCLK_CLK_buffered[0]));
   end
   if (C_FCLK_CLK1_BUF == "TRUE" | C_FCLK_CLK1_BUF == "true") begin : buffer_fclk_clk_1
     BUFG FCLK_CLK_1_BUFG (.I(FCLK_CLK_unbuffered[1]), .O(FCLK_CLK_buffered[1]));
   end
   if (C_FCLK_CLK2_BUF == "TRUE" | C_FCLK_CLK2_BUF == "true") begin : buffer_fclk_clk_2
     BUFG FCLK_CLK_2_BUFG (.I(FCLK_CLK_unbuffered[2]), .O(FCLK_CLK_buffered[2]));
   end
   if (C_FCLK_CLK3_BUF == "TRUE" | C_FCLK_CLK3_BUF == "true") begin : buffer_fclk_clk_3
     BUFG FCLK_CLK_3_BUFG (.I(FCLK_CLK_unbuffered[3]), .O(FCLK_CLK_buffered[3]));
   end
endgenerate 

assign FCLK_CLK0_temp = (C_FCLK_CLK0_BUF == "TRUE" | C_FCLK_CLK0_BUF == "true") ? FCLK_CLK_buffered[0] : FCLK_CLK_unbuffered[0];
assign FCLK_CLK1 = (C_FCLK_CLK1_BUF == "TRUE" | C_FCLK_CLK1_BUF == "true") ? FCLK_CLK_buffered[1] : FCLK_CLK_unbuffered[1];
assign FCLK_CLK2 = (C_FCLK_CLK2_BUF == "TRUE" | C_FCLK_CLK2_BUF == "true") ? FCLK_CLK_buffered[2] : FCLK_CLK_unbuffered[2];
assign FCLK_CLK3 = (C_FCLK_CLK3_BUF == "TRUE" | C_FCLK_CLK3_BUF == "true") ? FCLK_CLK_buffered[3] : FCLK_CLK_unbuffered[3];

assign FCLK_CLK0 = FCLK_CLK0_temp;

// Adding BIBUF for fixed IO Ports and IBUF for fixed Input Ports

BIBUF DDR_CAS_n_BIBUF (.PAD(DDR_CAS_n), .IO(buffered_DDR_CAS_n));
BIBUF DDR_CKE_BIBUF (.PAD(DDR_CKE), .IO(buffered_DDR_CKE));
BIBUF DDR_Clk_n_BIBUF (.PAD(DDR_Clk_n), .IO(buffered_DDR_Clk_n));
BIBUF DDR_Clk_BIBUF (.PAD(DDR_Clk), .IO(buffered_DDR_Clk));
BIBUF DDR_CS_n_BIBUF (.PAD(DDR_CS_n), .IO(buffered_DDR_CS_n));
BIBUF DDR_DRSTB_BIBUF (.PAD(DDR_DRSTB), .IO(buffered_DDR_DRSTB));
BIBUF DDR_ODT_BIBUF (.PAD(DDR_ODT), .IO(buffered_DDR_ODT));
BIBUF DDR_RAS_n_BIBUF (.PAD(DDR_RAS_n), .IO(buffered_DDR_RAS_n));
BIBUF DDR_WEB_BIBUF (.PAD(DDR_WEB), .IO(buffered_DDR_WEB));
BIBUF DDR_VRN_BIBUF (.PAD(DDR_VRN), .IO(buffered_DDR_VRN));
BIBUF DDR_VRP_BIBUF (.PAD(DDR_VRP), .IO(buffered_DDR_VRP));
BIBUF PS_SRSTB_BIBUF (.PAD(PS_SRSTB), .IO(buffered_PS_SRSTB));
BIBUF PS_CLK_BIBUF (.PAD(PS_CLK), .IO(buffered_PS_CLK));
BIBUF PS_PORB_BIBUF (.PAD(PS_PORB), .IO(buffered_PS_PORB));

genvar i;
generate
	for (i=0; i < C_MIO_PRIMITIVE; i=i+1) begin
		BIBUF MIO_BIBUF (.PAD(MIO[i]), .IO(buffered_MIO[i]));
	end
endgenerate

generate
	for (i=0; i < 3; i=i+1) begin
		BIBUF DDR_BankAddr_BIBUF (.PAD(DDR_BankAddr[i]), .IO(buffered_DDR_BankAddr[i]));
	end
endgenerate

generate
	for (i=0; i < 15; i=i+1) begin
		BIBUF DDR_Addr_BIBUF (.PAD(DDR_Addr[i]), .IO(buffered_DDR_Addr[i]));
	end
endgenerate

generate
	for (i=0; i < C_DM_WIDTH; i=i+1) begin
		BIBUF DDR_DM_BIBUF (.PAD(DDR_DM[i]), .IO(buffered_DDR_DM[i]));
	end
endgenerate

generate
	for (i=0; i < C_DQ_WIDTH; i=i+1) begin
		BIBUF DDR_DQ_BIBUF (.PAD(DDR_DQ[i]), .IO(buffered_DDR_DQ[i]));
	end
endgenerate

generate
	for (i=0; i < C_DQS_WIDTH; i=i+1) begin
		BIBUF DDR_DQS_n_BIBUF (.PAD(DDR_DQS_n[i]), .IO(buffered_DDR_DQS_n[i]));
	end
endgenerate

generate
	for (i=0; i < C_DQS_WIDTH; i=i+1) begin
		BIBUF DDR_DQS_BIBUF (.PAD(DDR_DQS[i]), .IO(buffered_DDR_DQS[i]));
	end
endgenerate

// Connect FCLK in case of disable the AXI port for non Secure Transaction
//Start


generate
  if ( C_USE_AXI_NONSECURE == 1 && C_USE_S_AXI_HP0 == 0) begin 
   assign S_AXI_HP0_ACLK_temp = FCLK_CLK0_temp;
  end
  else begin
  assign S_AXI_HP0_ACLK_temp = S_AXI_HP0_ACLK;
  end
endgenerate

generate
  if ( C_USE_AXI_NONSECURE == 1 && C_USE_S_AXI_HP1 == 0) begin 
	assign S_AXI_HP1_ACLK_temp = FCLK_CLK0_temp;
  end
  else begin
	assign S_AXI_HP1_ACLK_temp = S_AXI_HP1_ACLK;
  end
endgenerate

generate
  if ( C_USE_AXI_NONSECURE == 1 && C_USE_S_AXI_HP2 == 0) begin 
	assign S_AXI_HP2_ACLK_temp = FCLK_CLK0_temp;
  end
  else begin
	assign S_AXI_HP2_ACLK_temp = S_AXI_HP2_ACLK;
  end
endgenerate

generate
  if ( C_USE_AXI_NONSECURE == 1 && C_USE_S_AXI_HP3 == 0) begin 
	assign S_AXI_HP3_ACLK_temp = FCLK_CLK0_temp;
  end
  else begin
	assign S_AXI_HP3_ACLK_temp = S_AXI_HP3_ACLK;
  end
endgenerate

//Start


generate
  if ( C_USE_AXI_NONSECURE == 1 && C_USE_M_AXI_GP0 == 0) begin 
	assign M_AXI_GP0_ACLK_temp = FCLK_CLK0_temp;
  end
  else begin
	assign M_AXI_GP0_ACLK_temp = M_AXI_GP0_ACLK;  
  end
endgenerate

generate
  if ( C_USE_AXI_NONSECURE == 1 && C_USE_M_AXI_GP1 == 0) begin 
	assign M_AXI_GP1_ACLK_temp = FCLK_CLK0_temp;
  end
  else begin
	assign M_AXI_GP1_ACLK_temp = M_AXI_GP1_ACLK;    
  end
endgenerate

generate
  if ( C_USE_AXI_NONSECURE == 1 && C_USE_S_AXI_GP0 == 0) begin 
	assign S_AXI_GP0_ACLK_temp = FCLK_CLK0_temp;
  end
  else begin
	assign S_AXI_GP0_ACLK_temp = S_AXI_GP0_ACLK;    
    end
endgenerate

generate
  if ( C_USE_AXI_NONSECURE == 1 && C_USE_S_AXI_GP1 == 0) begin 
	assign S_AXI_GP1_ACLK_temp = FCLK_CLK0_temp;
  end
  else begin
	assign S_AXI_GP1_ACLK_temp = S_AXI_GP1_ACLK;      
   end
endgenerate

generate
  if ( C_USE_AXI_NONSECURE == 1 && C_USE_S_AXI_ACP == 0) begin 
	assign S_AXI_ACP_ACLK_temp = FCLK_CLK0_temp;
  end
  else begin
	assign S_AXI_ACP_ACLK_temp = S_AXI_ACP_ACLK;        
  end
endgenerate

assign M_AXI_GP0_ARCACHE=(C_GP0_EN_MODIFIABLE_TXN==1)?{{M_AXI_GP0_ARCACHE_t[3:2]},{1'b1},{M_AXI_GP0_ARCACHE_t[0]}}:M_AXI_GP0_ARCACHE_t ;
assign M_AXI_GP1_ARCACHE=(C_GP1_EN_MODIFIABLE_TXN==1)?{{M_AXI_GP1_ARCACHE_t[3:2]},{1'b1},{M_AXI_GP1_ARCACHE_t[0]}}:M_AXI_GP1_ARCACHE_t ;
assign M_AXI_GP0_AWCACHE=(C_GP0_EN_MODIFIABLE_TXN==1)?{{M_AXI_GP0_AWCACHE_t[3:2]},{1'b1},{M_AXI_GP0_AWCACHE_t[0]}}:M_AXI_GP0_AWCACHE_t ;
assign M_AXI_GP1_AWCACHE=(C_GP1_EN_MODIFIABLE_TXN==1)?{{M_AXI_GP1_AWCACHE_t[3:2]},{1'b1},{M_AXI_GP1_AWCACHE_t[0]}}:M_AXI_GP1_AWCACHE_t ;
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
