kangyuzhe666/ZYNQ7010-7020_AD9363/firmware/source project/pluto-7010clg400-user-ip/pluto/pluto.srcs/sources_1/bd/system/ipshared/304c/hdl/axi_iic_v2_0_vh_rfs.vhd

--soft_reset.vhd   v1.01a
-------------------------------------------------------------------------------
--
-- *************************************************************************
-- **                                                                     **
-- ** DISCLAIMER OF LIABILITY                                             **
-- **                                                                     **
-- ** This text/file contains proprietary, confidential                   **
-- ** information of Xilinx, Inc., is distributed under                   **
-- ** license from Xilinx, Inc., and may be used, copied                  **
-- ** and/or disclosed only pursuant to the terms of a valid              **
-- ** license agreement with Xilinx, Inc. Xilinx hereby                   **
-- ** grants you a license to use this text/file solely for               **
-- ** design, simulation, implementation and creation of                  **
-- ** design files limited to Xilinx devices or technologies.             **
-- ** Use with non-Xilinx devices or technologies is expressly            **
-- ** prohibited and immediately terminates your license unless           **
-- ** covered by a separate agreement.                                    **
-- **                                                                     **
-- ** Xilinx is providing this design, code, or information               **
-- ** "as-is" solely for use in developing programs and                   **
-- ** solutions for Xilinx devices, with no obligation on the             **
-- ** part of Xilinx to provide support. By providing this design,        **
-- ** code, or information as one possible implementation of              **
-- ** this feature, application or standard, Xilinx is making no          **
-- ** representation that this implementation is free from any            **
-- ** claims of infringement. You are responsible for obtaining           **
-- ** any rights you may require for your implementation.                 **
-- ** Xilinx expressly disclaims any warranty whatsoever with             **
-- ** respect to the adequacy of the implementation, including            **
-- ** but not limited to any warranties or representations that this      **
-- ** implementation is free from claims of infringement, implied         **
-- ** warranties of merchantability or fitness for a particular           **
-- ** purpose.                                                            **
-- **                                                                     **
-- ** Xilinx products are not intended for use in life support            **
-- ** appliances, devices, or systems. Use in such applications is        **
-- ** expressly prohibited.                                               **
-- **                                                                     **
-- ** Any modifications that are made to the Source Code are              **
-- ** done at the user’s sole risk and will be unsupported.               **
-- ** The Xilinx Support Hotline does not have access to source           **
-- ** code and therefore cannot answer specific questions related         **
-- ** to source HDL. The Xilinx Hotline support of original source        **
-- ** code IP shall only address issues and questions related             **
-- ** to the standard Netlist version of the core (and thus               **
-- ** indirectly, the original core source).                              **
-- **                                                                     **
-- ** Copyright (c) 2006-2010 Xilinx, Inc. All rights reserved.           **
-- **                                                                     **
-- ** This copyright and support notice must be retained as part          **
-- ** of this text at all times.                                          **
-- **                                                                     **
-- *************************************************************************
--
-------------------------------------------------------------------------------
-- Filename:        soft_reset.vhd
-- Version:         v1_00_a
-- Description:     This VHDL design file is the Soft Reset Service
--
-------------------------------------------------------------------------------
-- Structure:   
--
--              soft_reset.vhd
--                  
--
-------------------------------------------------------------------------------
-- Author:      Gary Burch
--
-- History:
--     GAB     Aug 2, 2006  v1.00a (initial release)
--
--
--     DET     1/17/2008     v4_0
-- ~~~~~~
--     - Incorporated new disclaimer header
-- ^^^^^^
--
-------------------------------------------------------------------------------
-- Naming Conventions:
--      active low signals:                     "*_n"
--      clock signals:                          "clk", "clk_div#", "clk_#x" 
--      reset signals:                          "rst", "rst_n" 
--      generics:                               "C_*" 
--      user defined types:                     "*_TYPE" 
--      state machine next state:               "*_ns" 
--      state machine current state:            "*_cs" 
--      combinatorial signals:                  "*_com" 
--      pipelined or register delay signals:    "*_d#" 
--      counter signals:                        "*cnt*"
--      clock enable signals:                   "*_ce" 
--      internal version of output port         "*_i"
--      device pins:                            "*_pin" 
--      ports:                                  - Names begin with Uppercase 
--      processes:                              "*_PROCESS" 
--      component instantiations:               "<ENTITY_>I_<#|FUNC>
-------------------------------------------------------------------------------
-- Library definitions

library ieee;
use ieee.std_logic_1164.all;
use ieee.numeric_std.all;

library unisim;
use unisim.vcomponents.all;

-------------------------------------------------------------------------------

entity soft_reset is
    generic (
        C_SIPIF_DWIDTH          : integer := 32;
            -- Width of the write data bus

        C_RESET_WIDTH           : integer := 4     
            -- Width of triggered reset in Bus Clocks
    ); 
    port (
  
        -- Inputs From the IPIF Bus 
        Bus2IP_Reset        : in  std_logic;
        Bus2IP_Clk          : in  std_logic;
        Bus2IP_WrCE         : in  std_logic;
        Bus2IP_Data         : in  std_logic_vector(0 to C_SIPIF_DWIDTH-1);
        Bus2IP_BE           : in  std_logic_vector(0 to (C_SIPIF_DWIDTH/8)-1);

        -- Final Device Reset Output
        Reset2IP_Reset      : out std_logic; 

        -- Status Reply Outputs to the Bus 
        Reset2Bus_WrAck     : out std_logic;
        Reset2Bus_Error     : out std_logic;
        Reset2Bus_ToutSup   : out std_logic
    
    );
  end soft_reset ;
  
  

-------------------------------------------------------------------------------

architecture implementation of soft_reset is

-------------------------------------------------------------------------------
-- Function Declarations 
-------------------------------------------------------------------------------

-------------------------------------------------------------------------------
-- Type Declarations
-------------------------------------------------------------------------------
    
-------------------------------------------------------------------------------
-- Constant Declarations
-------------------------------------------------------------------------------

-- Module Software Reset screen value for write data
-- This requires a Hex 'A' to be written to ativate the S/W reset port
constant RESET_MATCH    : std_logic_vector(0 to 3) := "1010"; 
                                                           
-- Required BE index to be active during Reset activation
constant BE_MATCH       : integer := 3; 
                                                            
-------------------------------------------------------------------------------
-- Signal Declarations
-------------------------------------------------------------------------------

signal sm_reset         : std_logic;
signal error_reply      : std_logic;
signal reset_wrack      : std_logic;
signal reset_error      : std_logic;
signal reset_trig       : std_logic;
signal wrack            : std_logic;
signal wrack_ff_chain   : std_logic;
signal flop_q_chain     : std_logic_vector(0 to C_RESET_WIDTH);
--signal bus2ip_wrce_d1   : std_logic;

signal data_is_non_reset_match  : std_logic;
signal sw_rst_cond              : std_logic;
signal sw_rst_cond_d1           : std_logic;

-------------------------------------------------------------------------------
-- Architecture
-------------------------------------------------------------------------------
  
begin
           
-- Misc assignments         
Reset2Bus_WrAck     <= reset_wrack;
Reset2Bus_Error     <= reset_error;
Reset2Bus_ToutSup   <= sm_reset; -- Suppress a data phase timeout when
                                 -- a commanded reset is active.

reset_wrack         <=  (reset_error or wrack);-- and Bus2IP_WrCE;
reset_error         <=  data_is_non_reset_match and Bus2IP_WrCE;
Reset2IP_Reset      <=  Bus2IP_Reset or sm_reset;
      
---------------------------------------------------------------------------------
---- Register WRCE for use in creating a strobe pulse
---------------------------------------------------------------------------------
--REG_WRCE : process(Bus2IP_Clk)
--    begin
--        if(Bus2IP_Clk'EVENT and Bus2IP_Clk = '1')then
--            if(Bus2IP_Reset = '1')then
--                bus2ip_wrce_d1 <= '0';
--            else
--                bus2ip_wrce_d1 <= Bus2IP_WrCE;
--            end if;
--        end if;
--    end process REG_WRCE;
--
-------------------------------------------------------------------------------
-- Start the S/W reset state machine as a result of an IPIF Bus write to
-- the Reset port and the data on the DBus inputs matching the Reset 
-- match value. If the value on the data bus input does not match the 
-- designated reset key, an error acknowledge is generated.
-------------------------------------------------------------------------------
--DETECT_SW_RESET : process (Bus2IP_Clk)
--    begin
--        if(Bus2IP_Clk'EVENT and Bus2IP_Clk = '1') then
--            if (Bus2IP_Reset = '1') then
--                error_reply       <= '0';
--                reset_trig        <= '0';
--            elsif (Bus2IP_WrCE = '1' 
--            and Bus2IP_BE(BE_MATCH) = '1'
--            and Bus2IP_Data(28 to 31) = RESET_MATCH) then
--                error_reply       <= '0';
--                reset_trig        <= Bus2IP_WrCE and not bus2ip_wrce_d1;
--            elsif (Bus2IP_WrCE = '1') then 
--                error_reply       <= '1';
--                reset_trig        <= '0';
--            else
--                error_reply       <= '0';
--                reset_trig        <= '0';
--            end if;
--        end if;
--    end process DETECT_SW_RESET;


    data_is_non_reset_match <=
        '0' when (Bus2IP_Data(C_SIPIF_DWIDTH-4 to C_SIPIF_DWIDTH-1) = RESET_MATCH
             and Bus2IP_BE(BE_MATCH) = '1')
        else '1';

--------------------------------------------------------------------------------
-- SW Reset
--------------------------------------------------------------------------------
    ----------------------------------------------------------------------------
    sw_rst_cond <= Bus2IP_WrCE and not data_is_non_reset_match;
    --
    RST_PULSE_PROC : process (Bus2IP_Clk)
    Begin
       if (Bus2IP_Clk'EVENT and Bus2IP_Clk = '1') Then
           if (Bus2IP_Reset = '1') Then
              sw_rst_cond_d1    <= '0';
              reset_trig        <= '0';
           else
              sw_rst_cond_d1    <= sw_rst_cond;
              reset_trig        <= sw_rst_cond and not sw_rst_cond_d1;
           end if;
       end if;
    End process;

        
-------------------------------------------------------------------------------
-- RESET_FLOPS:
-- This FORGEN implements the register chain used to create 
-- the parameterizable reset pulse width.
-------------------------------------------------------------------------------
RESET_FLOPS : for index in 0 to C_RESET_WIDTH-1 generate

    flop_q_chain(0) <= '0';

    RST_FLOPS : FDRSE
        port map(
            Q   =>  flop_q_chain(index+1), -- :    out std_logic;
            C   =>  Bus2IP_Clk,            -- :    in  std_logic;
            CE  =>  '1',                   -- :    in  std_logic;
            D   =>  flop_q_chain(index),   -- :    in  std_logic;    
            R   =>  Bus2IP_Reset,          -- :    in  std_logic;
            S   =>  reset_trig             -- :    in  std_logic
        );

end generate RESET_FLOPS;

    
-- Use the last flop output for the commanded reset pulse 
sm_reset        <= flop_q_chain(C_RESET_WIDTH);

wrack_ff_chain  <= flop_q_chain(C_RESET_WIDTH) and 
                    not(flop_q_chain(C_RESET_WIDTH-1));


-- Register the Write Acknowledge for the Reset write
-- This is generated at the end of the reset pulse. This
-- keeps the Slave busy until the commanded reset completes.
FF_WRACK : FDRSE
    port map(
        Q   =>  wrack,            -- :  out std_logic;
        C   =>  Bus2IP_Clk,       -- :  in  std_logic;
        CE  =>  '1',              -- :  in  std_logic;
        D   =>  wrack_ff_chain,   -- :  in  std_logic;    
        R   =>  Bus2IP_Reset,     -- :  in  std_logic;
        S   =>  '0'               -- :  in  std_logic
    );


end implementation;


 








-- SRL_FIFO entity and architecture
-------------------------------------------------------------------------------
--
-- *************************************************************************
-- **                                                                     **
-- ** DISCLAIMER OF LIABILITY                                             **
-- **                                                                     **
-- ** This text/file contains proprietary, confidential                   **
-- ** information of Xilinx, Inc., is distributed under                   **
-- ** license from Xilinx, Inc., and may be used, copied                  **
-- ** and/or disclosed only pursuant to the terms of a valid              **
-- ** license agreement with Xilinx, Inc. Xilinx hereby                   **
-- ** grants you a license to use this text/file solely for               **
-- ** design, simulation, implementation and creation of                  **
-- ** design files limited to Xilinx devices or technologies.             **
-- ** Use with non-Xilinx devices or technologies is expressly            **
-- ** prohibited and immediately terminates your license unless           **
-- ** covered by a separate agreement.                                    **
-- **                                                                     **
-- ** Xilinx is providing this design, code, or information               **
-- ** "as-is" solely for use in developing programs and                   **
-- ** solutions for Xilinx devices, with no obligation on the             **
-- ** part of Xilinx to provide support. By providing this design,        **
-- ** code, or information as one possible implementation of              **
-- ** this feature, application or standard, Xilinx is making no          **
-- ** representation that this implementation is free from any            **
-- ** claims of infringement. You are responsible for obtaining           **
-- ** any rights you may require for your implementation.                 **
-- ** Xilinx expressly disclaims any warranty whatsoever with             **
-- ** respect to the adequacy of the implementation, including            **
-- ** but not limited to any warranties or representations that this      **
-- ** implementation is free from claims of infringement, implied         **
-- ** warranties of merchantability or fitness for a particular           **
-- ** purpose.                                                            **
-- **                                                                     **
-- ** Xilinx products are not intended for use in life support            **
-- ** appliances, devices, or systems. Use in such applications is        **
-- ** expressly prohibited.                                               **
-- **                                                                     **
-- ** Any modifications that are made to the Source Code are              **
-- ** done at the user’s sole risk and will be unsupported.               **
-- ** The Xilinx Support Hotline does not have access to source           **
-- ** code and therefore cannot answer specific questions related         **
-- ** to source HDL. The Xilinx Hotline support of original source        **
-- ** code IP shall only address issues and questions related             **
-- ** to the standard Netlist version of the core (and thus               **
-- ** indirectly, the original core source).                              **
-- **                                                                     **
-- ** Copyright (c) 2001-2010 Xilinx, Inc. All rights reserved.           **
-- **                                                                     **
-- ** This copyright and support notice must be retained as part          **
-- ** of this text at all times.                                          **
-- **                                                                     **
-- *************************************************************************
--
-------------------------------------------------------------------------------
-- Filename:        srl_fifo.vhd
--
-- Description:     
--                  
-- VHDL-Standard:   VHDL'93
-------------------------------------------------------------------------------
-- Structure:   
--              srl_fifo.vhd
--
-------------------------------------------------------------------------------
-- Author:          goran
-- Revision:        $Revision: 1.1.4.1 $
-- Date:            $Date: 2010/09/14 22:35:47 $
--
-- History:
--   goran  2001-05-11    First Version
--   KC     2001-06-20    Added Addr as an output port, for use as an occupancy
--                        value
--
--   DCW    2002-03-12    Structural implementation of synchronous reset for
--                        Data_Exists DFF (using FDR)
--   jam    2002-04-12    added C_XON generic for mixed vhdl/verilog sims
--
--   als    2002-04-18    added default for XON generic in SRL16E, FDRE, and FDR
--                        component declarations
--
--     DET     1/17/2008     v5_0
-- ~~~~~~
--     - Incorporated new disclaimer header
-- ^^^^^^
--
-------------------------------------------------------------------------------
-- Naming Conventions:
--      active low signals:                     "*_n"
--      clock signals:                          "clk", "clk_div#", "clk_#x" 
--      reset signals:                          "rst", "rst_n" 
--      generics:                               "C_*" 
--      user defined types:                     "*_TYPE" 
--      state machine next state:               "*_ns" 
--      state machine current state:            "*_cs" 
--      combinatorial signals:                  "*_com" 
--      pipelined or register delay signals:    "*_d#" 
--      counter signals:                        "*cnt*"
--      clock enable signals:                   "*_ce" 
--      internal version of output port         "*_i"
--      device pins:                            "*_pin" 
--      ports:                                  - Names begin with Uppercase 
--      processes:                              "*_PROCESS" 
--      component instantiations:               "<ENTITY_>I_<#|FUNC>
-------------------------------------------------------------------------------
library IEEE;
use IEEE.std_logic_1164.all;
library unisim;
use unisim.all;

entity SRL_FIFO is
  generic (
    C_DATA_BITS : natural := 8;
    C_DEPTH     : natural := 16;
    C_XON       : boolean := false
    );
  port (
    Clk         : in  std_logic;
    Reset       : in  std_logic;
    FIFO_Write  : in  std_logic;
    Data_In     : in  std_logic_vector(0 to C_DATA_BITS-1);
    FIFO_Read   : in  std_logic;
    Data_Out    : out std_logic_vector(0 to C_DATA_BITS-1);
    FIFO_Full   : out std_logic;
    Data_Exists : out std_logic;
    Addr        : out std_logic_vector(0 to 3) -- Added Addr as a port
    );

end entity SRL_FIFO;

architecture IMP of SRL_FIFO is

  component SRL16E is
      -- pragma translate_off
    generic (
      INIT : bit_vector := X"0000"
      );
      -- pragma translate_on    
    port (
      CE  : in  std_logic;
      D   : in  std_logic;
      Clk : in  std_logic;
      A0  : in  std_logic;
      A1  : in  std_logic;
      A2  : in  std_logic;
      A3  : in  std_logic;
      Q   : out std_logic);
  end component SRL16E;

  component LUT4
    generic(
      INIT : bit_vector := X"0000"
      );
    port (
      O  : out std_logic;
      I0 : in  std_logic;
      I1 : in  std_logic;
      I2 : in  std_logic;
      I3 : in  std_logic);
  end component;

  component MULT_AND
    port (
      I0 : in  std_logic;
      I1 : in  std_logic;
      LO : out std_logic);
  end component;

  component MUXCY_L
    port (
      DI : in  std_logic;
      CI : in  std_logic;
      S  : in  std_logic;
      LO : out std_logic);
  end component;

  component XORCY
    port (
      LI : in  std_logic;
      CI : in  std_logic;
      O  : out std_logic);
  end component;

  component FDRE is
    port (
      Q  : out std_logic;
      C  : in  std_logic;
      CE : in  std_logic;
      D  : in  std_logic;
      R  : in  std_logic);
  end component FDRE;

  component FDR is
    port (
      Q  : out std_logic;
      C  : in  std_logic;
      D  : in  std_logic;
      R  : in  std_logic);
  end component FDR;

  signal addr_i       : std_logic_vector(0 to 3);  
  signal buffer_Full  : std_logic;
  signal buffer_Empty : std_logic;

  signal next_Data_Exists : std_logic;
  signal data_Exists_I    : std_logic;

  signal valid_Write : std_logic;

  signal hsum_A  : std_logic_vector(0 to 3);
  signal sum_A   : std_logic_vector(0 to 3);
  signal addr_cy : std_logic_vector(0 to 4);
  
begin  -- architecture IMP

  buffer_Full <= '1' when (addr_i = "1111") else '0';
  FIFO_Full   <= buffer_Full;

  buffer_Empty <= '1' when (addr_i = "0000") else '0';

  next_Data_Exists <= (data_Exists_I and not buffer_Empty) or
                      (buffer_Empty and FIFO_Write) or
                      (data_Exists_I and not FIFO_Read);

  Data_Exists_DFF : FDR
    port map (
      Q  => data_Exists_I,            -- [out std_logic]
      C  => Clk,                      -- [in  std_logic]
      D  => next_Data_Exists,         -- [in  std_logic]
      R  => Reset);                   -- [in std_logic]

  Data_Exists <= data_Exists_I;
  
  valid_Write <= FIFO_Write and (FIFO_Read or not buffer_Full);

  addr_cy(0) <= valid_Write;

  Addr_Counters : for I in 0 to 3 generate

    hsum_A(I) <= (FIFO_Read xor addr_i(I)) and (FIFO_Write or not buffer_Empty);

    MUXCY_L_I : MUXCY_L
      port map (
        DI => addr_i(I),                  -- [in  std_logic]
        CI => addr_cy(I),               -- [in  std_logic]
        S  => hsum_A(I),                -- [in  std_logic]
        LO => addr_cy(I+1));            -- [out std_logic]

    XORCY_I : XORCY
      port map (
        LI => hsum_A(I),                -- [in  std_logic]
        CI => addr_cy(I),               -- [in  std_logic]
        O  => sum_A(I));                -- [out std_logic]

    FDRE_I : FDRE
      port map (
        Q  => addr_i(I),                  -- [out std_logic]
        C  => Clk,                      -- [in  std_logic]
        CE => data_Exists_I,            -- [in  std_logic]
        D  => sum_A(I),                 -- [in  std_logic]
        R  => Reset);                   -- [in std_logic]

  end generate Addr_Counters;

  FIFO_RAM : for I in 0 to C_DATA_BITS-1 generate
    SRL16E_I : SRL16E
      -- pragma translate_off
      generic map (
        INIT => x"0000")
      -- pragma translate_on
      port map (
        CE  => valid_Write,             -- [in  std_logic]
        D   => Data_In(I),              -- [in  std_logic]
        Clk => Clk,                     -- [in  std_logic]
        A0  => addr_i(0),                 -- [in  std_logic]
        A1  => addr_i(1),                 -- [in  std_logic]
        A2  => addr_i(2),                 -- [in  std_logic]
        A3  => addr_i(3),                 -- [in  std_logic]
        Q   => Data_Out(I));            -- [out std_logic]
  end generate FIFO_RAM;
  
-------------------------------------------------------------------------------
-- INT_ADDR_PROCESS
-------------------------------------------------------------------------------
-- This process assigns the internal address to the output port
-------------------------------------------------------------------------------
  INT_ADDR_PROCESS:process (addr_i)
  begin   -- process
    Addr <= addr_i;
  end process;
  

end architecture IMP;


-------------------------------------------------------------------------------
-- upcnt_n.vhd  entity/architecture pair
-------------------------------------------------------------------------------
--  ***************************************************************************
--  ** DISCLAIMER OF LIABILITY                                               **
--  **                                                                       **
--  **  This file contains proprietary and confidential information of       **
--  **  Xilinx, Inc. ("Xilinx"), that is distributed under a license         **
--  **  from Xilinx, and may be used, copied and/or disclosed only           **
--  **  pursuant to the terms of a valid license agreement with Xilinx.      **
--  **                                                                       **
--  **  XILINX is PROVIDING THIS DESIGN, CODE, OR INFORMATION                **
--  **  ("MATERIALS") "AS is" WITHOUT WARRANTY OF ANY KIND, EITHER           **
--  **  EXPRESSED, IMPLIED, OR STATUTORY, INCLUDING WITHOUT                  **
--  **  LIMITATION, ANY WARRANTY WITH RESPECT to NONINFRINGEMENT,            **
--  **  MERCHANTABILITY OR FITNESS FOR ANY PARTICULAR PURPOSE. Xilinx        **
--  **  does not warrant that functions included in the Materials will       **
--  **  meet the requirements of Licensee, or that the operation of the      **
--  **  Materials will be uninterrupted or error-free, or that defects       **
--  **  in the Materials will be corrected. Furthermore, Xilinx does         **
--  **  not warrant or make any representations regarding use, or the        **
--  **  results of the use, of the Materials in terms of correctness,        **
--  **  accuracy, reliability or otherwise.                                  **
--  **                                                                       **
--  **  Xilinx products are not designed or intended to be fail-safe,        **
--  **  or for use in any application requiring fail-safe performance,       **
--  **  such as life-support or safety devices or systems, Class III         **
--  **  medical devices, nuclear facilities, applications related to         **
--  **  the deployment of airbags, or any other applications that could      **
--  **  lead to death, personal injury or severe property or                 **
--  **  environmental damage (individually and collectively, "critical       **
--  **  applications"). Customer assumes the sole risk and liability         **
--  **  of any use of Xilinx products in critical applications,              **
--  **  subject only to applicable laws and regulations governing            **
--  **  limitations on product liability.                                    **
--  **                                                                       **
--  **  Copyright 2011 Xilinx, Inc.                                          **
--  **  All rights reserved.                                                 **
--  **                                                                       **
--  **  This disclaimer and copyright notice must be retained as part        **
--  **  of this file at all times.                                           **
--  ***************************************************************************
-------------------------------------------------------------------------------
-- Filename:        upcnt_n.vhd
-- Version:         v1.01.b                        
--
-- Description:     
--                  This file contains a parameterizable N-bit up counter 
--                                    
-- VHDL-Standard:   VHDL'93
-------------------------------------------------------------------------------
-- Structure:
--
--           axi_iic.vhd
--              -- iic.vhd
--                  -- axi_ipif_ssp1.vhd
--                      -- axi_lite_ipif.vhd
--                      -- interrupt_control.vhd
--                      -- soft_reset.vhd
--                  -- reg_interface.vhd
--                  -- filter.vhd
--                      -- debounce.vhd
--                  -- iic_control.vhd
--                      -- upcnt_n.vhd
--                      -- shift8.vhd
--                  -- dynamic_master.vhd
--                  -- iic_pkg.vhd
--
-------------------------------------------------------------------------------
-- Author:          USM
--
--  USM     10/15/09
-- ^^^^^^
--  - Initial release of v1.00.a
-- ~~~~~~
--
--  USM     09/06/10
-- ^^^^^^
--  - Release of v1.01.a
-- ~~~~~~
--
-- NLR      01/07/11
-- ^^^^^^
-- -  Release of v1.01.b
-- ~~~~~~
------------------------------------------------------------------------------

library ieee;
use ieee.std_logic_1164.all;
use ieee.std_logic_arith.all;

-------------------------------------------------------------------------------
-- Port Declaration
-------------------------------------------------------------------------------
-- Definition of Generics:
--      C_SIZE     -- Data width of counter
--
-- Definition of Ports:
--      Clk               -- System clock
--      Clr               -- Active low clear
--      Data              -- Serial data in
--      Cnt_en            -- Count enable
--      Load              -- Load line enable
--      Qout              -- Shift register shift enable
-------------------------------------------------------------------------------
-- Entity section
-------------------------------------------------------------------------------
entity upcnt_n is
   generic(
          C_SIZE : integer :=9
          );
      
    port(
         Clr      : in std_logic;                        
         Clk      : in std_logic;                        
         Data     : in std_logic_vector (0 to C_SIZE-1); 
         Cnt_en   : in std_logic;                        
         Load     : in std_logic;                        
         Qout     : inout std_logic_vector (0 to C_SIZE-1)
         );
        
end upcnt_n;

-------------------------------------------------------------------------------
-- Architecture
-------------------------------------------------------------------------------
architecture RTL  of upcnt_n is
  attribute DowngradeIPIdentifiedWarnings: string;
  attribute DowngradeIPIdentifiedWarnings of RTL : architecture is "yes";

    
    constant enable_n : std_logic := '0';
    signal q_int : unsigned (0 to C_SIZE-1);
    
begin

   ----------------------------------------------------------------------------
   -- PROCESS: UP_COUNT_GEN
   -- purpose: Up counter
   ----------------------------------------------------------------------------
   UP_COUNT_GEN : process(Clk)
   begin
      if (Clk'event) and Clk = '1' then
         if (Clr = enable_n) then     -- Clear output register
            q_int <= (others => '0');
         elsif (Load = '1') then      -- Load in start value
            q_int <= unsigned(Data);
         elsif Cnt_en = '1' then      -- If count enable is high
            q_int <= q_int + 1;
         else
            q_int <= q_int;
         end if;
      end if;
   end process UP_COUNT_GEN;

   Qout <= std_logic_vector(q_int);

end architecture RTL;


-------------------------------------------------------------------------------
-- shift8.vhd - Entity and Architecture
-------------------------------------------------------------------------------
--  ***************************************************************************
--  ** DISCLAIMER OF LIABILITY                                               **
--  **                                                                       **
--  **  This file contains proprietary and confidential information of       **
--  **  Xilinx, Inc. ("Xilinx"), that is distributed under a license         **
--  **  from Xilinx, and may be used, copied and/or disclosed only           **
--  **  pursuant to the terms of a valid license agreement with Xilinx.      **
--  **                                                                       **
--  **  XILINX is PROVIDING THIS DESIGN, CODE, OR INFORMATION                **
--  **  ("MATERIALS") "AS is" WITHOUT WARRANTY OF ANY KIND, EITHER           **
--  **  EXPRESSED, IMPLIED, OR STATUTORY, INCLUDING WITHOUT                  **
--  **  LIMITATION, ANY WARRANTY WITH RESPECT to NONINFRINGEMENT,            **
--  **  MERCHANTABILITY OR FITNESS FOR ANY PARTICULAR PURPOSE. Xilinx        **
--  **  does not warrant that functions included in the Materials will       **
--  **  meet the requirements of Licensee, or that the operation of the      **
--  **  Materials will be uninterrupted or error-free, or that defects       **
--  **  in the Materials will be corrected. Furthermore, Xilinx does         **
--  **  not warrant or make any representations regarding use, or the        **
--  **  results of the use, of the Materials in terms of correctness,        **
--  **  accuracy, reliability or otherwise.                                  **
--  **                                                                       **
--  **  Xilinx products are not designed or intended to be fail-safe,        **
--  **  or for use in any application requiring fail-safe performance,       **
--  **  such as life-support or safety devices or systems, Class III         **
--  **  medical devices, nuclear facilities, applications related to         **
--  **  the deployment of airbags, or any other applications that could      **
--  **  lead to death, personal injury or severe property or                 **
--  **  environmental damage (individually and collectively, "critical       **
--  **  applications"). Customer assumes the sole risk and liability         **
--  **  of any use of Xilinx products in critical applications,              **
--  **  subject only to applicable laws and regulations governing            **
--  **  limitations on product liability.                                    **
--  **                                                                       **
--  **  Copyright 2011 Xilinx, Inc.                                          **
--  **  All rights reserved.                                                 **
--  **                                                                       **
--  **  This disclaimer and copyright notice must be retained as part        **
--  **  of this file at all times.                                           **
--  ***************************************************************************
-------------------------------------------------------------------------------
-- Filename:        shift8.vhd
-- Version:         v1.01.b                        
-- Description:     
--                  This file contains an 8 bit shift register 
--
--  VHDL-Standard:   VHDL'93
-------------------------------------------------------------------------------
-- Structure:
--
--           axi_iic.vhd
--              -- iic.vhd
--                  -- axi_ipif_ssp1.vhd
--                      -- axi_lite_ipif.vhd
--                      -- interrupt_control.vhd
--                      -- soft_reset.vhd
--                  -- reg_interface.vhd
--                  -- filter.vhd
--                      -- debounce.vhd
--                  -- iic_control.vhd
--                      -- upcnt_n.vhd
--                      -- shift8.vhd
--                  -- dynamic_master.vhd
--                  -- iic_pkg.vhd
--
-------------------------------------------------------------------------------
-- Author:          USM
--
--  USM     10/15/09
-- ^^^^^^
--  - Initial release of v1.00.a
-- ~~~~~~
--
--  USM     09/06/10
-- ^^^^^^
--  - Release of v1.01.a
-- ~~~~~~
--
--  NLR     01/07/11
-- ^^^^^^
--  - Release of v1.01.b
-- ~~~~~~
-------------------------------------------------------------------------------

library ieee;
use ieee.std_logic_1164.all;
use ieee.std_logic_arith.all;

-------------------------------------------------------------------------------
-- Port Declaration
-------------------------------------------------------------------------------
-- Definition of Ports:
--      Clk           -- System clock
--      Clr           -- System reset
--      Data_ld       -- Shift register data load enable
--      Data_in       -- Shift register data in
--      Shift_in      -- Shift register serial data in
--      Shift_en      -- Shift register shift enable
--      Shift_out     -- Shift register serial data out
--      Data_out      -- Shift register shift data out
-------------------------------------------------------------------------------
-- Entity section
-------------------------------------------------------------------------------

entity shift8 is
    port(
         Clk         : in std_logic;    -- Clock
         Clr         : in std_logic;    -- Clear
         Data_ld     : in std_logic;    -- Data load enable
         Data_in     : in std_logic_vector (7 downto 0);-- Data to load in
         Shift_in    : in std_logic;    -- Serial data in
         Shift_en    : in std_logic;    -- Shift enable
         Shift_out   : out std_logic;   -- Shift serial data out
         Data_out    : out std_logic_vector (7 downto 0)  -- Shifted data
         );
        
end shift8;
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
